beneckart/resonance-lighting/firmware/fixture/README.md

# fixture -- production fleet firmware

One image for all four fixture classes (downlight / perimeter / trunk /
chandelier), extracted from the proven bench sketches. The current code/NVS enum
still calls the trunk role `uplight`; treat that as a compatibility name until the
manifest/schema rename is coordinated (ADR 0032). `net_bench` remains the desk
**bridge** build (master + serial bridge); this sketch is peer-only.

## Indefinite storage and service wake

The September 12 image adds explicitly confirmed, exact-target storage:
untimed BQ ship with good USB/solar or QON wake, and untimed deep sleep with
physical RESET wake. Ship retains the fuel gauge; RESET/BOOT alone cannot wake
its unpowered ESP. OTA alone never enters storage or clears PROTECT. T-Deck
Rest -> Store also provides the existing timed sleep through a Pacific date
picker. See the [storage and wake guide](../../docs/howto/FIXTURE_STORAGE_AND_WAKE.md)
for exact firmware identities, 106-fixture deployment evidence and physical
wake/current tests still outstanding.

## Fixture class identity

The initial Wire1 probe and runtime drivers both use 100 kHz. Class identity is
ordered: ID-verified TMF8820/TMF8821-family ToF -> downlight; otherwise VL53L5CX
-> perimeter; otherwise MSA311 at `0x62` -> uplight. For the installed 2026 fleet,
no class sensors also defaults to uplight. A remembered downlight or perimeter is
retained with a mismatch if its ToF disappears.

Future chandelier PowerFeathers must be selected by exact MAC, recorded as
chandelier in the registry, and persist `O4` / `class_ovr=4` before installation.
Use `O0` to return a repurposed board to automatic identity. A sensorless explicit
chandelier is valid; an old automatically learned sensorless chandelier migrates
to uplight. See ADR 0067.

## Cambium direct control

`NB_DIRECT_FRAME` (type 25) carries up to 18 addressed RGBW entries per ESP-NOW
packet. A fixture renders only the entry matching its three-byte short MAC. Frames
grant an expiring micro-lease; after one second of silence the last color fades to
half, and after three seconds the fixture returns to its autonomous program with the
existing crossfade. `NB_FORCE_LIFECYCLE` (type 26) provides RAM-only day/night/auto
bench control and never survives reboot. The local power tier and night gate still
outrank requested colors.

The nominal 130-light fleet requires eight broadcast packets per complete color
wave. At Cambium's intended 8 Hz rate that is 64 packets/s, below the previously
exercised ESP-NOW rate range. The Nevada City acceptance bench uses perimeter
fixtures `F3FD88`, `F2BE80`, and `F2BFEC`.

## UTC schedule and build-week override

`NB_TIME_QUALITY` now carries the ADR 0031/0049 sparse UTC anchor. The T-Deck
GPS publishes active, checksum-valid RMC time; DS3231 fixtures add read-only
holdover when OSF is clear. Fixtures select bounded monotonic time and calculate
Black Rock City civil twilight (`-6 deg`) locally. If accepted time is absent
for 30 minutes, the existing panel-current dusk/dawn heuristic regains control.

RTC commissioning remains an explicit maintenance operation, never an automatic
show-time write. `ops/bench/rtc_commission.py` requires one exact fixture ID,
its identity-matched maintenance IP, the exact expected firmware revision, safe
power, DS3231 presence, and a fresh valid T-Deck GPS observation. The guarded
`POST /rtc` route repeats the fixture ID check, requires `SET_RTC_UTC`, writes
UTC once, clears OSF, and verifies readback. Maintenance telemetry exposes
`rtc_valid` and `rtc_utc_s` for the same proof.

In field profile, scheduled day is electrically dark and scheduled night runs
the autonomous program. Direct/program leases can override the baseline during
day; a dark lease can suppress night. `NB_FORCE_LIFECYCLE` provides RAM-only
Wake Fleet (the dark day baseline) / Night Show / Auto and clears on reboot.
Commission profile remains always awake with the ADR 0039 listener beacon. Only
accepted operator commands hold field fixtures awake for ten minutes; peer
heartbeats and time packets do not defeat the configured cadence. ADR 0064
additionally holds every timer wake through a trustworthy post-charge-enable
IBAT sample (normally about 12 s, bounded to 15 s on gauge failure), even if an
older recipe requested less.

## Transport sleep and rig RSSI capture

`NB_TRANSPORT_SLEEP` provides a 32-bit multi-day timer sleep. The bridge's
`Q<hours>` command (1-168) cuts fixture loads/rails and wakes automatically. The
timer wake restores radio/telemetry but retains an RTC-backed electrically-dark
output latch until a valid program command; bare bridge `b` is the intended
post-unload release. This is not physical ship mode and requires no lid access.

`NB_LOCATE_CONTROL` makes RSSI capture explicitly temporary. During bridge
`L[seconds]` only, a fixture retains up to 160 heard peers and sends its fresh
heard roster in 16-entry report fragments about every 20 seconds. Outside the
bounded window it emits no report traffic. See `ops/locate/rssi_capture.py` and
ADR 0045.

## Architecture stance

**Cooperative main loop + ISR-enqueue rx queue + esp_timer one-shots. No
application FreeRTOS tasks.** This deviates from ADR 0005 deliberately: it is
the only architecture with field hours behind it (net_bench soaks), and the
conservative reading of ADR 0028 rule 3 (no power-management-bus I2C from
core-0-pinned tasks under WiFi) plus the 2026-07-29 blocking-driver lesson
(cooperative TMF8820 one-shot machine; presence_bench's core-0 task quarantine
is forbidden on this bus). All Wire1 traffic runs at 100 kHz from loop context.
Revisit tasks only if render jitter is measured, and never for power-bus I2C.

> 2026-07-30 amendment (ADR 0028 addendum): rule 3 is downgraded -- the sealed
> A/B + 46 h soak both ran power-bus I2C from a core-0 task at 100 kHz, so the
> clock, not core placement, is the load-bearing rule. A single-owner sensor
> task (presence_bench shape, ALL Wire1 in one task) is now permitted pending
> a pre-playa field soak. Motivation is measured art quality: sensor-to-LED
> latency drives how alive the demo feels, and loop bursts visibly stutter
> max-speed orbit/spiral. Peer-to-peer CA impact TBD. The cooperative loop
> stays the shipping architecture until a task build earns its field hours.

## Layout

```
fixture.ino          setup()/loop() ordering only
src/core/            platform-independent, natively unit-tested (tests/)
  packet.h           wire protocol v1 + type registry (THE fleet contract)
  power_policy       ADR 0023/0046 tier ladder + compound PROTECT release
  boot_guard         POR/reboot-loop stage ladder (Phase-4 matrix)
  class_probe        sensors -> class decision table
  lifecycle          day/night machine, bounded night, energy-gated wake
  choreo/            program runtime: IDLE, GH_CA, BRIDGE_SHOW + lease
  neighbor_table     RSSI + pinned adjacency modes
  hex_geometry, filters, power_integrator, tmf_recovery
src/esp32/           glue/drivers (board_power owns the solar guard include)
  sensors/           cooperative machines + the single vendored VL53L5CX ULD
tests/run_tests.sh   wrapper contract + native g++ suite -- before every flash
```

## Build / flash

```
./build.sh                          # compile only
./build.sh --port /dev/ttyACM0      # USB flash
./build.sh --ota <ip>               # OTA via POST /update
./build.sh --artifact-variant b --wifi-profile-label party-in-the-woods-v1 \
  --channel 11 --profile field --basic-listener  # immutable canary artifact
./build.sh --channel 11 --profile commission
./build.sh --channel 11 --profile commission --basic-listener
./build.sh --precharge-ma 300            # low-VBAT recovery current
./build.sh --wifi-source <gitignored-header>  # solenoid capability is universal
./build.sh --wifi-source <gitignored-header> --solenoid-test  # targeted bench image
./build.sh --profile field --day-sleep-s 120 --wake-listen-ms 12000 # ADR 0064 canary
./build.sh --msa-trace-target ABCDEF --fw-rev fx-YYMMDD-xxxxxxx-t
./build.sh --sentinel-trace-target ABCDEF --fw-rev fx-YYMMDD-xxxxxxx-t
```

For ordinary edit/compile iteration, use the persistent development cache:

```bash
./build.sh --dev-cache --profile commission --channel 11
```

This path is serialized by an atomic lock and invalidated when the FQBN, flags,
toolchain, SDK, or firmware libraries change. Its mutable binary always reports
`dev-local`; it is suitable only for local iteration and, after host checks, one
explicit USB target. It is rejected with `--ota` or `--artifact-variant`.
Manual `--artifact-dir`/`--fw-rev` is disabled; the
artifact path and revision are derived from the exact canonical recipe before
compilation. Do not pass a development-cache binary to fleet tools.

If a cached build is killed, times out, or loses its wrapper, first confirm that
no `arduino-cli`, Xtensa compiler/linker, or `esptool` process remains, then run:

```bash
./build.sh --recover-dev-cache  # quarantine; next build is cold
```

Use `./build.sh --clean-dev-cache` only for a healthy, unlocked cache. Fresh
compile behavior remains the default when `--dev-cache` is omitted. Evidence and
raw gates are in
`../../docs/tests/FIRMWARE_BUILD_ACCELERATION_SMOKE_2026-08-22.md`.
Run `./build.sh --help` for the short local-versus-fleet command contract.
`tests/run_tests.sh` includes a fast, compile-free regression check for that
boundary before it starts the native C++ suite.

Maintenance WiFi credentials live only in gitignored `wifi_secrets.h`; copy
`wifi_secrets.h.example` and replace its placeholders locally. The historical
`RES_WIFI_SSID` / `RES_WIFI_PASSWORD` pair remains required. An optional
`RES_WIFI_SSID_2` / `RES_WIFI_PASSWORD_2` pair adds a second maintenance/OTA
network. On entry to maintenance, the fixture scans once, ranks visible known
SSIDs by RSSI, and tries both within a shared 30-second join budget. A failed
scan preserves primary-then-secondary order. Ordinary COMMS mode never joins
either network and remains pinned to the ESP-NOW channel.

Source defaults remain a 300-second DAY_CHARGE timer sleep and a 15,000 ms
post-wake listen grace. The installed 120 s / 3 s fleet artifact is superseded
by ADR 0064 because it could sleep before the 6-second charge guard and a fresh
MAX17260 conversion. New named 120-second canaries use at least 12,000 ms.
Firmware independently withholds ordinary day sleep until valid IBAT or a
15-second gauge-fault fail-open, so a shorter compiled grace cannot recreate
the charge-path defect. Record both build values with the artifact and do not
infer equal energy from listen duty alone because every wake also pays fixed
boot, sensor, and radio startup cost. USB telemetry exposes the compiled
`day_sleep_s` and `wake_listen_ms` values.

For any shared/fleet artifact, the manual `fixture-YYYY-MM-DD.N` counter is
retired. Follow `../../docs/howto/FIRMWARE_ARTIFACT_HANDOFF.md`: clean committed
source, generated `fx-YYMMDD-<recipe7>-<variant>`, immutable manifest, exact
binary SHA-256, and explicit target MACs. `build.sh --artifact-variant ...`
owns the canonical recipe bytes, revision/path, embedded identity, manifest,
and post-build cross-checks. Its golden test pins the final-LF byte contract.

Always `-DPOWERFEATHER_BOARD_V2=1` (build.sh injects it). Chemistry is
build-time (`--chem lfp` default); everything else is runtime NVS.
Solenoid capability is enabled by default on every PowerFeather image. The
one-time NVS policy migration enables devices that retained the historical
disarmed value; a later explicit runtime disarm remains persistent. D7/GPIO37
stays INPUT/high-Z while armed and idle, so rev-1 receiver/manual sources remain
usable and a Feather without a capboard has no connected load. A strike still
requires an addressed command, a deduplicated fleet strike event, autonomous
program output, or local input. Deliberate operator radio commands and events
are best-effort mechanism attempts under ADR 0065: they bypass lifecycle,
solar, and power-tier qualification but retain arm, pulse-width, rest-time,
maintenance, durable load-marker, and failsafe gates. Autonomous program
knocks retain the lifecycle/renewable/power-tier policy.

`NB_EVENT_SOLENOID_STRIKE` adds immediate and short-future fleet strikes without
changing the packet layout. One logical event is repeated for RF reliability;
fixtures deduplicate its 32-bit event ID, arm at most one pending event, clamp
the pulse to 5-300 ms, and refuse a scheduled strike more than 250 ms late.
`fire_in_ms` is capped at five seconds. The bridge decrements it on later RF
copies so every received copy refers to the same deadline, while the fixture
uses callback receipt time rather than later queue-drain time. At fire time an
operator event reaches the hard solenoid arm/rest/load-marker/timer/failsafe
boundary without lifecycle or power qualification. Older fixture firmware
ignores this new event kind.

`--canopy-solenoid` remains accepted as a deprecated no-op so older build recipes
do not fail; it is no longer required and must not be used to infer artifact
capability.

`--solenoid-test` is deliberately not a fleet option: it forces the arm bit and
relaxes the autonomous-program solar-surplus gate while retaining that path's
night and FULL-tier battery vetoes. Deliberate operator radio knocks no longer
need this override. Use a named artifact and a specific peer.

Rev-2 solarnoid SW1 shares D7 with the MCU through a hardware one-shot. An armed
fixture releases D7 to INPUT/high-Z between strikes. After observing a released
LOW, firmware accepts one external rising edge and extends it to the same bounded
40 ms pulse as the PowerFeather USER button; another strike requires release and
a new edge. Boot-high/stuck-high inputs do not fire or retrigger, normal MCU
requests refuse an already-high external line, and the timer plus loop failsafe
remain authoritative. External edges are ignored during OTA maintenance.

The default battery-side charge-current ceiling is 2,000 mA (ADR 0033). The
BQ25628E may deliver less because of input-current/voltage regulation, source
capability, system load, CV taper, or thermal regulation. `G<ma>` remains an
explicit lower override for a smaller or otherwise limited cell.

The BQ25628E precharge limit defaults to 300 mA (`--precharge-ma 300`). This
replaces the charger's 30 mA POR value, which left deeply discharged production
LFPs near 2.8 V treading water despite valid solar input. Firmware performs a
two-byte, little-endian, reserved-bit-preserving REG0x10 read/modify/write and
verifies the readback;
pending OTA images roll back if it does not match. Trickle charge below 2.25 V,
input DPM, thermal protection, and the hardware transition to fast charge near
3.0 V remain unchanged. Maintenance telemetry exposes `precharge_target_ma`,
`precharge_configured`, `bq_precharge_ma`, and raw `bq_reg10`.

Bringup: `fleet_usb_bringup.py commission --sketch-dir fixture --build-path
firmware/fixture/build/<r> --expect-fw <version> ...` -- the serial/HTTP
contract (`t` JSON keys, `u` + "maintenance WiFi up, ip=" banner, /telemetry,
/resume, /update) is preserved byte-for-byte from net_bench; the guarded `/rtc`
route is fixture-only.

## Sensor-domain recovery

Every non-parked boot gives the separate VSQT/STEMMA rail a verified 100 ms
off -> on cycle before class probing. This matters on OTA and warm resets because
PowerFeather otherwise preserves the RTC-held rail state, allowing a stale TMF
firmware/ranging state to survive the MCU reset. `Board.enableVSQT()` is retried
and GPIO14 is read back for both transitions; Wire1 remains fixed at 100 kHz.

The normal TMF timeout path still performs the cheap cooperative stop/start.
Three consecutive failed measurement cycles escalate once per boot to a full
VSQT cycle and reconstruction of the SparkFun driver, which forces TMF init,
open, firmware upload, application-mode switch, configuration, and ranging
start. MSA311 and BMP581 are reinitialized because they share the rail. Further
failures stay degraded rather than flapping the domain. Telemetry exposes
`tmf_domain_resets` in addition to reads/errors/recoveries.

Commissioning likewise treats `tmf8820_present=true` plus zero reads as a
recoverable state: it performs one explicitly targeted
`!S<short-mac>:1` timed-sleep/VSQT reset and retests before
failing. `tmf8820_present=false` does not get that retry and remains the signal
to inspect the module, first cable, and power contacts.

## Serial commands (peer)

`t` telemetry JSON | `u` local ENTER_MAINT | `c` resume | `C<mah>` capacity
(reboots) | `G<ma>` charge cap | `K<id>:<ms>` solenoid (gated) |
`!S<id>:<s>` newline-framed targeted deep sleep | `O<0-4>` class override |
`F<0|1>` profile dev/prod | `N<0|1|2>`
force day/night/auto | `L0` force LED rail off until `L1` or reset | `L1` clear
the override and run the bench smoke render | `X` guarded bare-board
PROTECT clear | `r` status line

`X` works only with verified good USB/VDC, no plausible battery, charging off,
and no charger fault. It does not clear PROTECT automatically or over ESP-NOW;
`fleet_usb_bringup.py` uses it only in the default battery-absent workflow.

### Installed-battery PROTECT rescue

Do not start with `RESET-BOOT-RESET`, erase NVS, or use `X`. Leave the fixture's
LFP installed, connect the enclosure rescue USB port to a proven supply, and
observe telemetry over normal USB CDC. A valid battery, good external supply,
valid/enabled charger with no fault, at least +20 mA charge current, and at
least 3.25 V must all hold continuously for 60 seconds before the durable
PROTECT latch releases. ADR 0068 adds a second proof for a full/tapered battery
that cannot accept +20 mA: a corroborated real cell, at least 3.45 V, and BQ
`CHG_STAT` of CV, top-off, or not-charging/done must hold with the same good
input and charger gates for 60 seconds. CC with low current, a proof change, or
one missing sample restarts the timer. Both paths release to LEDS_OFF and make
the same clean reboot; neither authorizes release from rebound voltage alone.

On `fx-260816-otafix1-b`, do not rely on the physical RESET button. A RESET
asserts a power-on-class reset; if the durable stage is still LEDS_OFF or DIM,
the cause-independent boot guard can correctly return to PROTECT. The observed
`F2BF5C` recovery held good USB and +340 mA charge long enough to climb
PROTECT -> LEDS_OFF -> DIM -> FULL, but the parked boot still left its LED rail
and sensors off. A deliberate software reboot at FULL then booted unparked,
initialized all three sensors, rejoined ESP-NOW, and returned to steady red.

The preferred rescue is to USB-install `fx-260816-prtrel1-b`; it replaces that
operator-timed software reboot with an automatic clean reboot immediately after
persisting the qualified release. The reboot is required because a parked boot
deliberately skipped rail cycling, class probe, sensor initialization, and LED
profiling. Use BOOT/download mode only if normal CDC never enumerates or the
ordinary USB flash tool cannot connect. Never erase NVS as a routine recovery;
it also destroys per-fixture configuration and bypasses the intended safety
qualification.

## NVS (namespace `resfx`)

`cap_mah` `chg_ma` `chg_policy` `class_ovr` `class_last` `fc_stage` `boots` `profile`
`batt_tier` `dim_mv/off_mv/slp_mv` `sol_en` `maint_v10` `channel`
`channel_policy` `night_max` `slp_cmd` `slp_prot`.
The USB command `H<1..13>` persists a new ESP-NOW channel and reboots so the
radio is cleanly re-pinned; bare `H` reports the current channel.
First boot migrates `netbench:{cap_mah,chg_ma}` and carries a parked
`fc_led_stage` (production must not un-park a protected unit). Charge-policy v1
then replaces legacy 500/1,000/1,500 mA NVS values with the 2,000 mA default
once. A nonstandard pre-existing value is preserved as a possible deliberate
cell limit; later `G<ma>` overrides remain persistent.

`slp_cmd` is the last validated operator sleep receipt; it records cause,
duration, source short ID/sequence/uptime, local uptime, VBAT, profile,
lifecycle, and power tier before the rails go down. `slp_prot` records the same
local context once on entry into PROTECT. ADR 0068 reuses its otherwise-empty
source fields to retain origin, predecessor stage, reset reason, prior
`load_arm`, and unexpected-reset streak without changing the 32-byte record.
Older records are annotated once as `legacy-unknown` without losing their entry
voltage/profile/uptime. Recurring day-charge and PROTECT timer sleeps do not
write NVS: their immediate cause uses RTC slow memory instead. An
operator-caused sleep is refused if `slp_cmd` cannot be persisted.

Channel 11 is the production default. Channel-policy v1 migrates an absent key
or the historical channel-6 fallback to the compiled channel (11 for production)
once, while preserving any other explicit lab channel. Later `H<1..13>` choices
are marked current and remain persistent.

## Commission vs field profile

`PROFILE_DEV=0` retains its wire/NVS value for compatibility but is now the
operator-facing **commission** profile. It is the pre-build/build-week posture:
the ESP-NOW control plane stays awake, heartbeats run at 1 Hz, solar current does
not trigger a lifecycle transition, and bridge command leases override the
selected no-command fallback. `commission_default` is `listener` (the normal
class-aware ready beacon), `ca` (autonomous light-only GH wildfire), or `dark`
(strict LED-rail-off diagnostics). Missing/invalid NVS stays `listener`. The
Bridge OS Default app changes one exact target or walks every fresh short ID;
its setting can be RAM-only until reboot or explicitly persisted with
`NB_COMMISSION_DEFAULT` type 30. A genuinely critical battery still parks all
loads; its commission-mode retry is 60 s, and a verified external source keeps
the parked control plane awake for service.

`PROFILE_PROD=1` is the operator-facing **field** profile: 300 s/15 s daytime
duty cycle (energy-gated), 0.2 Hz hb-short, scheduled/autonomous behavior, and the
normal 900 s PROTECT sleep. Local power and solenoid safety vetoes are identical
in both profiles; commission changes reachability and fallback behavior, not load
safety. Flip via `NB_PROFILE` (type 21) or per-unit serial `F` (`F0` commission,
`F1` field). New build flags accept `--profile commission|field`; `dev|prod` remain
compatibility aliases. The commission-default setting is ignored in field
profile, so it cannot replace the scheduled night CA or daytime sleep policy.

A timer wake with FULL power tier and measured good input at or above 150 mA
holds a RAM-only solar probe awake beyond the ordinary 15-second window. Sixty
continuous seconds earns `DAY_ACTIVE`; a transient clears immediately and
returns to the normal cadence. Once active, 100 mA is the energy-state
hysteresis threshold with a 300-second dropout confirmation; ADR 0071 no longer
treats that state as an all-day radio lease. DAY_ACTIVE returns to the normal
sleep/listen cadence after its grace and may carry readiness across one timer
sleep only when the fresh strike gate re-arms it. Autonomous strikes still
require at least 150 mA and the normal energy gate; deliberate operator knocks
are best-effort attempts under ADR 0065. Battery voltage alone is not surplus
evidence. See ADR 0060/0071.

Energy-ready downlights with trustworthy UTC shorten only their final daytime
sleep to wake 20 seconds before each hour. ADR 0071's fixed ritual attempts one
high-time-quality unison, one deterministic organic roll, and a sparse after-
ring, then returns to sleep by T+47 seconds. Invalid/weak time, scheduled night,
weak energy, a bridge lease, or any hard solenoid gate causes abstention. The
installed mallets strike finger cymbals, not bare bamboo.

The supervised `--basic-listener` posture is deliberately minimal and class
aware. With no active bridge lease, canopy/downlights hold their dedicated warm
white channel at linear 128, 37-pixel perimeter HEX modules hold red at linear
16, and single-pixel trunk/uplights hold red at linear 128. A bridge command or
dashboard tag overrides it, and stale-command fallback returns directly to the
selected commission default within three seconds. LED channel values are
linear: 0 is off and 255 is the 8-bit bright endpoint. The old
`--quiet-autonomy` option remains only as a build-script alias.

An `NB_PROGRAM_SET` GH-CA lease uses params byte 6 as an opt-in local ToF seed.
The sensor path is sampled once through the same ADR 0044 gate used by the
listener color wipe: 90-report per-zone learning, a confident 300 mm closer
delta for three reports, and four clear reports to re-arm. A rising edge is
held until the next CA step and excites only that downlight; ordinary CA state
gossip carries the result onward. Non-sensor fixtures remain graph participants.
Byte 6 defaults off, and params byte 1 now honors zero as zero spontaneous
sparks, so an operator can run a presence/neighbor-only CA lease. The separate
presence color-wipe gossip remains suppressed during every program lease.

The 1 Hz commission heartbeat remains the compact 29-byte `hb-short`. A length-
gated full heartbeat follows every 5 s in commission and every 60 s in field. Its
append-only output tails report fixture class, raw sensor-signature bits, class
mismatch, LED-rail state, the post-cap RGBW average actually written to lit
pixels, lit-pixel count, and low-VBAT recovery state/BQ presence-test voltage.
Tail 16 adds immediate sleep cause plus compact durable operator-sleep and
PROTECT-entry evidence. Tail 17 certifies power-sample validity; tail 18 adds
the durable PROTECT origin/predecessor/reset/marker/streak context. The full
heartbeat is now 199 bytes; automatic day/protection repetitions remain
flash-wear-free.
The fleet dashboard uses measured render state rather than inferring color from
the requested program. Older bridges remain compatible because every tail is
length-gated against the one canonical `src/core/packet.h` layout.

An installed LFP in the 2.2-2.5 V window is no longer confused with a missing
battery solely by voltage. On a qualified external source the fixture runs the
BQ25628E's documented 30 mA BAT-discharge presence test with charging disabled.
Only a surviving battery ADC reading at or above 2.2 V permits a 100 mA recovery
ceiling; LED and sensor rails remain parked. A fault stops recovery, and one
continuous minute at or above 2.55 V restores the persisted normal charge cap.
See ADR 0042. Cells below 2.2 V remain a bench-recovery case.

Maintenance exit clears the ESP-NOW receive queue before reinitialization, so a
queued maintenance command cannot replay after `/resume`. If radio initialization
fails during the WiFi-to-ESP-NOW transition, the fixture remains in COMMS posture
and retries once per second until `espnow_up=true`. Telemetry exposes
`espnow_up`, `comms_init_attempts`, `comms_init_failures`, `led_rail_on`, and
`smoke_render` so an operator can distinguish radio recovery, command receipt,
power veto, and physical LED output.

## OTA rollback

`verifyRollbackLater()`/`verifyOta()` are `extern "C"` -- the weak hooks live
in a C file; a mangled C++ override silently never runs. Deferred self-test at
t+20 s (power chip, gauge sanity, mode-appropriate network path, NVS, watchdog)
marks the image valid or reboots into rollback. COMMS requires ESP-NOW plus a
completed send; MAINT requires associated WiFi plus the active OTA HTTP server
because ESP-NOW is deliberately down there. Drill: flash a
`--ota-fail-selftest` build over OTA
and watch it revert unattended. Rollback support requires one full USB flash
to install the current bootloader config (the M1 fleet reflash provides it).
Telemetry exposes `ota_partition`, `ota_address`, `ota_state`, and the legacy
`ota_pending_verify` boolean so same-family A/B transitions remain observable.

## Hardware-gate checklist (owed before fleet flash; see plan)

- [ ] `fleet_usb_bringup.py --sketch-dir fixture` full commission incl. --wifi-check
- [ ] appears on an UNMODIFIED net_bench serial-bridge master + dashboard
- [ ] per-class render smoke from one binary (probe log + `O` override + RGBW order)
- [ ] bench-supply power matrix (ADR 0046): 3.15 dim / 3.10 off+OTA window / 3.05 sleep;
      PROTECT survives POR/WDT/SW reset; compound release only; retry once
- [ ] OTA good-image valid + fail-selftest auto-revert on battery
- [ ] GH wave on the 2x10 rig via pinned adjacency (RSSI-mode A/B for the record)
- [ ] commission bridge lease grant plus command-loss hard dark/rail-off <= 5 s
- [ ] commission time-to-maintenance <= 10 s; field worst case one sleep period
- [ ] 24 h outdoor prod soak: dusk, bounded night (set night_max low to prove
      it fires), dawn, maintenance reachable in every state, autonomous night
      strike refused, deliberate operator night strike bounded by mechanism gates
