beneckart/resonance-lighting/firmware/led_studio/README.md

# LED Studio (merged)

Interactive aesthetic bench tool that drives one of three LED options on the **same
data pin** (default GPIO10 / A0), with a UI **mode toggle** to hot-swap between them
-- no reflash:

- **HEX grid** -- SK6812 37px RGB hex.
- **RGBW point** -- single 4 W SK6812 RGBW (has a dedicated white die).
- **RGB point** -- single high-power RGB pixel (same as the RGBW minus the white die).

Supersedes the separate `hex_studio/` + `rgbw_studio/` sketches (kept for reference;
this one is the merged front-end).

## How the hot-swap works

Both modules are SK6812 (same WS2812 protocol + voltage), so a single
`Adafruit_NeoPixel` object is reconfigured at runtime via `updateType()` /
`updateLength()` -- **37px NEO_GRB** for HEX, **1px NEO_RGBW** for the RGBW. The strip
is blanked on every mode switch.

**Mismatched mode is harmless** (both SK6812): worst case is wrong colors or one LED
lighting until refreshed; current stays well under the 3V3 rail's ~1 A. Recommended
swap sequence: **All off -> physically swap the module on the JST -> flip the mode
toggle** to match.

## Wiring / flash

- LED data -> `DATA_PIN` (default **GPIO10 / A0**); power 3V3 (the RGBW runs fine undervolted
  at 3.3 V -- 5 V gives more Vf headroom / peak brightness but is *not* required); GND. The
  sketch enables the V2 switchable 3V3 rail (GPIO4).

> Note: the earlier "abnormally low" RGBW current at 3.3 V was a **measurement bug**, not a
> wiring problem -- `ina_monitor` divided by a 0.1 ohm shunt when the SEN0291 is 0.01 ohm, so it
> under-read 10x (fixed 2026-06-09; corrected full-RGBW draw ~ 290 mA). There is modest *real*
> rail sag under load (LED bus -> ~2.84 V at full RGBW), but **no evidence that lead / in-line
> resistance was ever the culprit** -- flaky DuPont jumpers can misbehave, but these tests don't
> demonstrate it.

```
./build.sh --port /dev/ttyACM1            # USB flash
./build.sh --pin 16 --port /dev/ttyACM1   # if data is on D6/GPIO16
./build.sh --sensor-triad --cap 6000 --charge-ma 2000 --maintain 4.6
./build.sh --l5cx --cap 6000 --charge-ma 2000 --maintain 4.6   # perimeter HEX demo
```

On shared WiFi the board registers a **per-device** mDNS name
`http://ledstudio-<last-3-MAC-bytes>.local/` (e.g. `ledstudio-9e5ae8.local`;
two boards both claiming plain `ledstudio.local` sent browser control to the
wrong unit, 2026-07-30). Serial monitor (115200) also prints the IP; SoftAP
fallback `ResonanceLED` (pw `resonance`) at `http://192.168.4.1`.

Since `led-studio-2026-08-01.3`: `wifi_secrets.h` may define `RES_WIFI_SSID2`
(bench AP) -- setupWifi scans at boot and prefers it over the primary SSID when
visible (phone hotspots can isolate clients; a laptop-hosted bench AP cannot).
Boards pick their network at boot only -- bring the bench AP up, then
power-cycle. `/set` + `/state` send `Access-Control-Allow-Origin: *` and
`/state` carries `"host"` (the mdns name), so laptop-side dashboards can drive
several boards at once: see `ops/bench/perimeter_trio.html` (3-light perimeter
bench UI with discovery scan, zone grids, and mood presets).

## Controls

- **Module toggle**: HEX grid * RGBW point * RGB point. Mode-specific controls
  show/hide accordingly (the W slider + white/warmth presets appear only for RGBW).
- **Shared**: color picker + R/G/B sliders, brightness, speed, gamma toggle, All off.
- **HEX mode**: W slider hidden; shape rings (center/+inner/+two/all); animations
  Spiral / Orbit / Breathe / Twinkle; Trail; Orbit ring; Freeze + Step.
  - **Split RGB** is a separate 3-state modifier (Off / Triad / Rotate) that applies
    on top of Static / Spiral / Orbit / Breathe -- it splits the moving "head" into
    pure R/G/B across three pixels:
    - **Triad** -- a local color-fringe cluster offset from the point (tune with
      Fringe **spread** + **rotate**).
    - **Rotate** -- R at the point, G/B the same point rotated 120 deg /240 deg about the
      grid center (3-fold rotational symmetry; collapses to white at the exact center).
- **RGBW mode**: W (white-die) slider; white/warmth presets + crossfade; animations
  Hue / Breathe / Candle / Fade (with Color B).
- **RGB mode**: same single-pixel color animations as RGBW (Hue / Breathe / Candle /
  Fade + Color B), but no W channel or white/warmth controls.
- **L5CX presence HEX mode** (`--l5cx`, perimeter demo enclosure): vendored
  VL53L5CX 4x4 @ 10 Hz on Wire1/100 kHz (fixture's trimmed ULD, loop-idiom like
  sway_demo -- begin() only in setup(), quick re-apply self-heal in loop).
  Boots into HEX anim 5 "Presence" at bri=255/gamma-off. Idle = all 37 px
  pure RED; a visitor's depth drives the hue continuously --
  t = (max - depth)/(max - min), red at 2.5 m walking R->O->Y->G->B->I->V as
  they close on the gobo threshold -- and inside the threshold (default
  500 mm, slider 40-600: visitors step up without knowing where the sensor
  is, so arm's-length pops the surprise) the gobo takes over: a single
  full-white center pixel until release. Visitor depth = closest target
  anomalous vs a learned per-zone scene baseline (unset zones count as FAR,
  so someone entering an empty sightline registers from max range; static
  clutter stays scene and cannot pin the gobo on). The wheel HOLDS during
  the gobo confirm (sudden appearance snaps to white instead of zipping the
  rainbow). Gobo triggers: **near** (visitor <= thresh) OR **occlusion** (>=60% of
  baseline-valid zones lose their target -- a palm covering the whole FoV
  returns non-valid statuses, so "closest target" alone would read it as
  clear). Baselines adapt asymmetrically (revealed-farther fast, closer on a
  ~1 min tau so a lingering visitor fades back to scene; frozen during gobo;
  "Re-zero scene" button reseeds). 2-frame enter / 3-frame release; gobo
  transitions and visible color motion re-render at sensor rate instead of
  the speed-paced frame timer. The UI shows a live 4x4 zone grid (mm +
  anomaly coloring), visitor depth, and wheel position.
- **Sensor-triad RGBW mode** (`--sensor-triad`): adds live MSA311, TMF8820, and
  BMP581 readback plus three reactive modes. ToF depth brightens the selected
  RGBW color as a target approaches (the known enclosed 20 mm window/fixture
  return is ignored); Tilt brightens with angle from a re-zeroed rest pose; and
  Elevation maps -1.5 to +1.5 m around a re-zeroed BMP581 pressure baseline from
  dim to bright. TMF8820 one-shots use a cooperative start/process/stop state
  machine instead of the driver's blocking convenience wrapper; all sensor and
  PowerFeather accesses remain single-threaded at Wire1's mandatory 100 kHz. The
  UI reports WiFi RSSI, request latency, TMF result age, and automatic recoveries.
- **Settings readback** for recording good-looking combos.

See `../POWERFEATHER_NOTES.md` for the 3V3-rail / native-USB-reset gotchas.
