beneckart/resonance-lighting/LOG.md

# LOG

Append-only session journal for the Resonance Lighting workstream. Most recent first.

Format per entry:

```
## YYYY-MM-DD -- author -- short subject

Body. What changed, what was decided, what's next.
```

## 2026-10-06 -- Ben + Codex -- Consolidate storage firmware and post-event work

Ben requested committing all pending work and pushing to origin. Integrated
both storage branches with the pending Atom/Magic Wand conductors, preserving
the exact deployed fixture/T-Deck artifacts and their original identities.
Added `docs/howto/FIXTURE_STORAGE_AND_WAKE.md` with wake contracts, operation,
rollout evidence and the still-open electrical/UI qualification. Fixed stale
canary counts and worktree-only artifact references. Added
`docs/postmortem/README.md`, linked from README, ROADMAP and TODO, to connect the
container/Oakland/PROTECT records with both 2027 brainstorming drafts. Those
ideas remain exploratory; controlled PROTECT recovery is still deferred.

Preserved the small supplementary storage snapshots/process logs/dry run with
a separate exact-byte manifest and explicit historical status. The three large
raw captures stay local with hashes retained; private NVS backups and Wi-Fi
secrets remain excluded. Original evidence and artifact bytes are unchanged.

Review caught a Magic Wand high-hold shock that could leave a gesture armed.
The source now cancels it immediately and has a regression at the rejection
threshold; previous embedded builds predate the fix and need a new artifact
before deployment. T-Deck registry generation also depended on CSV checkout
line endings; canonical LF hashing and LF/CRLF/content-change tests fix that
portability issue without altering the fleet entries or historical artifacts.

Retained the exact September 3 25 ms Atom application and supporting flash
files with a historical manifest. Its original build used uncommitted source;
the new record explicitly leaves the build source commit unknown rather than
assigning today's integration commit to that binary.

Validation: all 33 fixture and 20 T-Deck native executables, five conductor
native executables, 26 Python host/storage tests, two registry-generator
regressions, build-wrapper contracts, local documentation links and staged
whitespace checks passed. All 57 curated and 26 supplementary evidence records
retain their exact hashes in Git, as do the retained firmware binaries/options.
No fresh embedded image was built; the preserved binaries are the historical
ones, and the updated Wand source still requires a new artifact and canary.

No device commands, reflashes or changes to live fleet state were made during
this repository consolidation.

## 2026-09-14 -- Ben + Codex -- Instant maintenance wake as an OTA speed objective

Ben identified a second benefit for an independent wake interface: shorter OTA
turnaround. Added the requirement to the RFID feasibility note. It removes
sleep-cadence gathering and repeat straggler capture, especially the roughly
15-minute PROTECT rendezvous; it does not shorten compile/upload or verified
reboot. The runbook's ordinary-fleet phase timings are planning targets, not
an observed storage-run speed claim.

Specify retained bounded maintenance intent, loads parked, duplicate wake that
does not reset an active upload, group/roster coverage and the existing power
and pending-verify gates. A bare hardware reset may promptly sleep again and
never clears PROTECT. No implementation or device command.

## 2026-09-14 -- Ben + Codex -- RFID identification plus independent reset/wake explored

Ben connected the earlier battery-free fixture-ID idea to a ground-accessible
hardware reset/wake and asked whether an RTC coin cell could support it.
Recovered the earlier request from the Postmortem Findings task; no prior
selected RFID component was found. Added a feasibility note at
`docs/projects/2027-power-platform/RFID_SERVICE_ACCESS.md`.

Primary documentation establishes RF-controlled GPIO without ESP firmware on
EM4325-class UHF RFID, with an official coin-cell reference design. Proposed
independent bounded reset/ship-wake circuitry, a retained service request,
and harmless inventory separate from deliberate targeted action. Shared coin
power is plausible for control only; quantify complete standby/RF-event draw,
isolation and clock-retention effects. Passive ID, assisted ID and actuation
range need separate installed tests; passive fallback can be much shorter.

Reset does not clear durable PROTECT or supply energy to an empty main cell.
QON wakes BQ ship but not shutdown, and external-input reset behavior needs
explicit design. No chip/reader selected, device action, or firmware change.

## 2026-09-14 -- Ben + Codex -- Chime sensing demoted; command reception prioritized

Ben corrected the exploratory priority: both capboard revisions already have
optional voltage-divider sensing, and the populated bench proof produced
excellent data. Weak/null underfilled-cap strikes are acceptable; he reports
fast refill in weak sun and consistent several-Hz independent 433 MHz rings.
Chimes were more reliable than light control or presence sensing; sleeping
ESPs and suspect PROTECT recovery were the main remote-control impediment.

Revised the design exploration to preserve the working solar-fed bounded
strike path, keep cap telemetry optional for diagnostics, and compare radio
reachability/latency per unit energy. At an illustrative 3.3 V and 130 mA,
12 seconds of LEDs-off awake operation costs 5.15 J versus 4.75 J total stored
in a nominal 66 mF/12 V bank. This is not isolated RF power or per-strike energy.
Historical fast capacitor refill was measured on a bench supply; Ben's latest
weak-sun report is retained as field observation, not substituted for that trace.

ESP-NOW reception windows and an independent trigger/wake path are research
comparisons only. No deployment, new strike veto, or hardware change. The exact
count of erroneous PROTECT latches remains unresolved; no new guard command.

## 2026-09-14 -- Ben + Codex -- 2027 power-platform exploration; recovery UI deferred

Ben explicitly tabled implementation of a T-Deck un-PROTECT/recovery command
and asked for broader firmware/tooling assessment with a year until the next
event. Recorded an exploratory brief in
`docs/projects/2027-power-platform/EXPLORATION.md`, not an accepted ADR/BOM.

Reviewed local bus/SOC/current/solar/chime evidence and primary datasheets.
Proposed priorities: autonomous LFP-correct charging/recovery, private power
bus, whole-cycle energy accounting, source identity, chime-cap voltage,
independent load/cell cutoff and explicit calendar/service wake contracts.
Keep the gauge for characterization rather than blaming its silicon for an
unqualified SOC model. INA228 accumulation costs 640 uA typical while running;
its production measurement power source and gaps need design. Hardware fault
capture and retained evidence are more useful than additional opaque flags.

Queued a feature inventory and small comparative qualification program before
any board selection or retirement. No firmware, device commands, purchases,
or current fleet architecture changed.

## 2026-09-14 -- Ben + Codex -- Explicit PROTECT clear capability checked

Confirmed there is no T-Deck/ESP-NOW un-PROTECT command. Durable NVS PROTECT
survives RESET, power cycling and ordinary OTA. The fixture serial X command
is restricted to verified externally powered, battery-absent, charging-off,
no-fault bare boards; it is not an installed-battery override. Added the exact
capability boundary to the recovery investigation. A remote controlled retry
would require new fixture and handheld support. No device or firmware changes.

## 2026-09-14 -- Ben + Codex -- Wake does not override PROTECT radio sleep

Traced Wake/Performance Hold from NB_FORCE_LIFECYCLE through ordinary receive
hold and inspection control. PROTECT's separate power_glue deadline is set only
at boot and remains authoritative; Wake does not extend it, clear the latch or
guarantee full-time radio. Verified the independent 8-second grace/sleep gate
in Kiki's 91663fd source, Groot's 2805988, final-burn 316470a and inspection
7c1f71d. Expected PROTECT listening is about 8-9 s / 900 s asleep unless a
separate recovery/OTA/service condition holds it awake.

The six-minute Wake campaign also cannot guarantee capturing a 15-minute
PROTECT cadence. Corrected overly broad 'full-fleet' / 'each captured radio'
operator documentation; Performance Hold spans more wake cycles but still does
not override PROTECT. Added the distinction to the recovery investigation and
queued explicit Wake eligibility diagnostics. No firmware or device changes.

## 2026-09-14 -- Ben + Codex -- High-VBAT PROTECT cohort and recovery limitation

Ben linked unexpected quiet during the last Burning Man days to possible stuck
PROTECT. Reconciled the retained September 12 census: 74 PROTECT, 40 at >=3.25 V,
seven at >=3.30 V. The 40 entry histories are 35 low-VBAT, four load-armed reset,
one legacy; all report supply-good false in the dark-storage snapshot. This is
a substantial triage cohort, not proof of 40 healthy batteries or sunny failures.

Manifest/source ancestry confirms all three September 12 fleet images already
contained the full-battery and PROTECT sleep-ownership fixes. Kiki's older
658b7d2 contains neither; Groot's b0ff5db contains both. Offline injected-sample
checks against unchanged current power_policy reproduce a remaining limitation:
net-positive charge across sleep/wake can coexist with negative awake current,
so no recovery proof starts below the full-battery floor. Stable current and
full/CV positive controls release correctly. This is not hardware validation.

Also separated a known chime contributor: September 1 inspection firmware on
70 fixtures deliberately disabled autonomous chimes; the earlier final-burn and
visibility images allow them in FULL/DIM. Bench plan, exact cohort and synthetic
reproduction are in `docs/tests/PROTECT_RECOVERY_INVESTIGATION_2026-09-14.md`.
No production code or device state changed; preserve Oakland specimens for
controlled diagnosis before deciding a repair.

## 2026-09-14 -- Ben + Codex -- Timed sleep does not set PROTECT

Traced T-Deck Rest 12-hour radio sleep through NB_SLEEP_FOR into the fixture's
timed deep sleep. It records the operator request without setting PROTECT;
an expected timer wake preserves the previous power stage. Wooper retains a
12-hour command yet currently reports NORMAL. Kairi instead records a low-VBAT
entry at 2.993 V (no load armed), now 3.303 V/PROTECT; Kiki has a 2.978 V older
entry, now 3.277 V/PROTECT. These are historical trigger records, not independent
cell measurements. A voltage rebound alone never qualifies the charge-based
release. Groot's low-VBAT entry is 2.976 V with load armed, now 2.880 V.

Ben clarified the early morning timing and doubts significant solar recovery;
no measured charge history supports that explanation, so it is not adopted.
The available listen samples show negative battery current/good-input false
for the high-voltage production fixtures. Updated the Oakland post-mortem
record with exact command/protection distinctions; no device changes.

## 2026-09-14 -- Ben + Codex -- Oakland units stay out; preserve post-mortem baseline

Ben plans to leave the Oakland lanterns out, with no deliberate sleep/ship
commands, and may bring some inside for post-mortem analysis. Existing
automatic power policy remains in place; no forced-awake hold was requested.
The high-voltage PROTECT units plausibly survived dark storage through sparse
radio duty: roughly 216 mAh/week at 130 mA for 9 seconds awake / 900 asleep,
excluding leakage/other loads. This is a model, not measured storage draw or
remaining capacity; LFP voltage plateau and unknown recent solar history limit
the 3.3 V inference. Wooper's current shorter cadence models about 1.99 Ah/week.

Prioritize Groot versus a higher-voltage PROTECT fixture (Kairi/Kiki), retain
state before firmware/guard changes, then compare actual cell/load/current and
charge behavior. Keep old prototype 9F26F8 separate from production conclusions.
Updated `docs/tests/OAKLAND_LANTERN_INVENTORY_2026-09-14.md` and TODO; no device
changes were issued and the earlier passive capture remains immutable.

## 2026-09-14 -- Ben + Codex -- Oakland bin accounts for Kairi and Wooper

Ben brought a separate bin from Nevada City to Oakland: five canopy lanterns
and one batteryless uplight with its panel connected. Two old backyard
prototypes are also present; the perimeter may be disconnected/batteryless.
TSwift's five reported identities are Groot 9F2724, Kairi 9F26B4, Kiki F2BF5C,
Wooper 9F0E30 and prototype 9F26F8. None was in the September 12 stored 106.
Kairi/Wooper account for two of that census's eight missing IDs; six remain
unlocated. Groot/Kiki/prototype were outside the 114-ID baseline. Other bin
units are not yet mapped and may still overlap the stored group.

A 22-second read-only serial snapshot verified connected TSwift 979604 on
COM157, channel 11, tdeck-dev-local; storage4 was flashed on other T-Deck
8EB508. Last-listen battery reports were Groot 2.880 V, prototype 2.992 V,
and the other three 3.277-3.321 V, with ages 18 seconds to 13.6 minutes.
These are retained reports, not simultaneous cell measurements or a complete
900-second census. No commands, firmware/power changes or background process
were issued/left running. Exact evidence and service items are in
`docs/tests/OAKLAND_LANTERN_INVENTORY_2026-09-14.md`.

## 2026-09-12 -- Ben + Codex -- 106 fixtures stored; pack-up complete

All 106 observed fixtures acknowledged untimed USB-wake storage on the exact
retained f951ae9 image. The final five replied by 18:39:20 PDT; the final
17-target job stopped at 18:39:37 with no failed or unresolved target. All
106 source/sequence receipts match durable cause-8, zero-duration audits.
The final 19:17:57 read-only reconciliation passed after 38m37s of radio quiet
since the last receipt, with continuous logger/master evidence and no bridge
restart. A fresh storage-status confirmed the controller inactive. No further
sleep command was needed when Ben requested pack-up at 19:17.

Stopped only this run's logger/dashboard and released the temporary Windows
awake hold at 19:18. Laptop, T-Deck and Starlink can be packed. The eight
never-heard installed fixtures were not commanded and remain physical-service
exceptions. USB/solar or QON wakes the selected mode; RESET/BOOT alone does
not. Assembled current and physical wake still require service-time testing.

Final proof, exact ledgers/rosters, controller flash identity and capture
hashes are retained with the report at
`docs/tests/CONTAINER_STORAGE_CENSUS_2026-09-12.md`. Compact evidence and source
are on `codex/container-storage-host-20260912`; large raw logs/private NVS
backups stay local. T-Deck Rest -> Store includes indefinite storage and a
fresh-GPS Pacific wake picker from 30 minutes to seven days. Native and
embedded checks passed; physical LCD/wake/current qualification remains open.

## 2026-09-12 -- Ben + Codex -- All 106 OTA verified; direct USB storage underway

Ben's later instruction authorizes direct laptop operation, without a physical
T-Deck confirmation tap. His dinner return window is approximately
18:30-19:00 PDT. ADR 0081 records the narrow host-command exception.

All 106 observed fixtures passed fresh exact-revision and pending-window OTA
verification on the retained `fx-260912-f951ae9-b` image by 17:56:15 PDT;
no target failed or remained in commission. The eight census exceptions were
not heard and were not commanded. Exact per-job evidence is in the container
run directory, including `all-106-ota-verified.txt`.

Flashed exact T-Deck 8EB508 / 44:1b:f6:8e:b5:08 on COM152 with retained
`tdeck-0.3.0-storage4`, 1,578,224 bytes, SHA-256
`11b98b33ca46babf21ad27cb1f2edd7cccdf6319a5e130df3e5442fd6260c1b1`.
Every written flash-region hash verified, then fresh boot identity, channel 11,
radio census and an idle host storage controller were confirmed. Firmware
source is 556c2f6 in `../resonance-tree-storage-host-20260912`; artifact commit
a53181a retains binaries and manifest. Full native and embedded checks passed.
The native registry comparison now tolerates Windows CRLF; firmware did not
change after the retained build. A private NVS/apps recovery backup remains
local and must not be committed.

Hellboy's first storage command was accepted at 17:57:18 PDT. At 17:59:12 it
reported PREPARED for source 8EB508 / sequence 21, then stayed quiet past its
former 120-second cadence. Its durable command audit reports USB storage,
zero duration, the same source and sequence. Two subsequent groups brought
the total to 31 PREPARED by 18:04, all with matching durable audits and no
rejoin or failure. Storage requests are now actually being sent under Ben's
explicit permission; earlier no-command notes describe earlier checkpoints.

The 75 PROTECT-cycle fixtures are being handled in complete timing cohorts,
with Ponyta's group armed first. Remaining exact-roster plan and per-command
ledgers are retained. The final full-cadence quiet observation is still due;
PREPARED plus radio silence is not measured electrical current or a physical
USB-wake test. Expected pack-up readiness is about 18:40-18:50 PDT if these
cohorts behave as observed. Temporary laptop awake hold remains active.

## 2026-09-12 -- Ben + Codex -- Fleet USB storage authorized

Ben returned at approximately 17:08 PDT and explicitly authorized putting the
fleet into USB-wake storage. Earlier sleep/ship confirmation is now satisfied.
Continuing exact-target OTA batches from the tested immutable f951ae9 image,
then storage through the T-Deck with explicit request/receipt evidence. First
additional wave: 12 targets, job 6FA40ADD. The T-Deck storage3 build continues;
physical storage wake/current remains unmeasured. Full rollout results will
be appended when known.

## 2026-09-12 -- Ben + Codex -- Container census and one storage-capability OTA canary

Onboarded in Nevada City after roughly a week of dark container storage.
Ben wants fixtures off until physical service; USB wake preferred, RESET
acceptable, and QON effort only if the battery benefit warrants it. Ben
authorized OTA at discretion while AFK, retaining his earlier requirement
for separate confirmation before deliberate deep-sleep/ship commands.

Completed an uninterrupted 1,020-second census after a recorded host-process
capture gap: 106 of the September 1 installed roster of 114 heard, all FIELD,
all latest retained LED reports off and supply-good false. No 0-0.6 V report
appeared in either capture segment. Ponyta `F2B7DC` was lowest at 2.582 V;
Chunli `9F2714` was 2.618 V. These are readings, not a ruined-cell diagnosis.
Eight missing fixtures remain unknown. Seventy-four latest tiers were PROTECT.
Details, field ages, limitations and battery calculations are recorded in
`docs/tests/CONTAINER_STORAGE_CENSUS_2026-09-12.md`; raw data and exact rosters
are in `ops/bench/data/ca/20260912-155847-container/`.

Prepared storage firmware in the isolated adjacent worktree
`resonance-tree-storage-20260912`, branch `codex/container-storage-20260912`,
preserving unfinished conductor changes here. The canonical protocol adds
exact-target USB-wake ship mode and RESET-wake indefinite deep sleep; OTA
does not select either. The T-Deck adds reviewed storage and a GPS-backed
Pacific date/time picker with a seven-day limit and 16-minute catch-up window.
ADR 0080 in that worktree records the contract and physical qualification still
needed. The first T-Deck build was abandoned to fix confirmation-dialog fit;
its replacement uses a fresh path, never the interrupted directory.

Fixture and T-Deck native suites passed. Fixture embedded artifact
`fx-260912-f951ae9-b` (1,218,752 bytes), SHA-256
`ec03b074c6feae7ffc3f6bb2e178ec213ea5d241b56b3e24c95bfbb24d315001`,
was built from clean `fcc5ef0` with the same runtime flags as the installed
inspection image. Sole operator Ben + Codex OTA-updated only Hellboy `9F26C4`.
Job `84DEEB42` verified a fresh exact-revision heartbeat at 25,953 ms uptime,
FIELD profile and recovery state zero at 16:40:08 PDT. No deliberate sleep,
ship, lifecycle or LED command was sent.

Added a read-only census summarizer and storage request/receipt logging;
all 16 relevant Python tests pass. Periodic radio wakes dominate storage
draw. The vendor-board 24-to-1 uA deep-sleep/ship comparison saves just
0.440 Ah/week across 114 fixtures; USB wake is ship's stronger practical
advantage. Our ship implementation retains the gauge and needs external
current measurement; do not claim the vendor's gauge-disabled 1 uA result.

## 2026-09-12 -- Ben + Codex -- Explicit unattended USB-storage operation

Ben authorized putting the fleet in USB-wake storage and asked for direct
laptop operation while a campmate later packs the equipment. ADR 0081 adds a
bounded, exact-roster USB CLI with explicit confirmation text, fresh capability
checks, job-owned stop/status, and no automatic campaign resume. The existing
physical UI flow remains intact. Work is isolated from the still-running
storage3 compile; storage4 uses a separate source checkout/build directory.

## 2026-09-12 -- Ben + Codex -- Storage confirmation proposal frozen

Final UI review found keyboard focus could reach background controls while a
confirmation was open. Storage now refuses background Review/Back/mode/Stop
actions until that modal closes, preserving its exact target, wake method and
date. Confirmation also refuses entry after the Storage screen has gone away.
The completed storage2 image passed its embedded build but was not flashed;
storage3 uses a fresh retained build directory. Ordinary Hellboy RTC audit
retention is now confirmed after clearing the receiver cache; physical storage
entry and wake remain untested and require Ben's separate confirmation.

## 2026-09-12 -- Ben + Codex -- Storage census and one OTA canary verified

Completed a 17-minute uninterrupted census after recovering an earlier host
capture gap: 106 of 114 installed fixtures heard, all FIELD, no reported
0-0.6 V batteries; Ponyta 2.582 V and Chunli 2.618 V are lowest. Eight missing
fixtures remain unknown. The main saving is removing periodic radio wakes;
ship's extra gain over uninterrupted deep sleep is small, with USB wake its
main servicing advantage. Full evidence is in
`docs/tests/CONTAINER_STORAGE_CENSUS_2026-09-12.md` and the main checkout's
`ops/bench/data/ca/20260912-155847-container/`.

Built immutable canary `fx-260912-f951ae9-b` from `fcc5ef0`, exact SHA-256
`ec03b074c6feae7ffc3f6bb2e178ec213ea5d241b56b3e24c95bfbb24d315001`, and
used Ben's OTA authorization for only Hellboy `9F26C4`. Job `84DEEB42` proved
fresh exact revision beyond 25 seconds, FIELD profile, recovery state zero.
No storage command was sent; the original separate confirmation requirement
remains. Fixture/T-Deck native suites and the fixture embedded build passed.

Added storage receipt/request logging with separate PREPARED, refusal, and
entry-failure meanings. All 16 relevant Python tests pass. Screen review found
that content-sized confirmation dialogs could obscure the footer; bounded
the dialog with a scrollable content region. The first incomplete T-Deck
compile was intentionally stopped, its compiler descendants checked gone,
and its directory abandoned. The corrected storage2 image uses a new build
directory. This does not alter the already verified fixture artifact.

## 2026-09-12 -- Ben + Codex -- Explicit container-storage capability prepared

Added exact-target indefinite RESET-wake and USB-wake ship commands, durable
sleep audit causes, pre-entry receipts, and an appended capability heartbeat
tail. OTA never selects storage automatically. The T-Deck Power screen now
offers a reviewed storage action and a GPS-backed Pacific date/time picker
using existing transport sleep, with an explicit roster and a 16-minute
catch-up window for PROTECT sleepers. ADR 0080 records the wake contracts,
confirmation boundary, and remaining physical current/wake qualification.

Fixed pre-existing T-Deck registry-generation drift: new unnamed fixtures use
their exact ID, retired fixtures can retain historical callsigns, and the
generated roster is refreshed without changing the source registry/callsigns.
All fixture native tests passed. Embedded builds and the T-Deck test completion
are recorded in the follow-up validation entry. No sleep/ship command or flash
was issued while preparing this source.
## 2026-09-03 -- Ben + Codex -- Fourth and final 25 ms Atom Conductor flashed

Identified the last COM42 Atom as full MAC `14:08:08:54:B8:C8` (short ID
`54B8C8`) and found no prior role or identity record in the repo. SHA-checked
and reused exact 938,416-byte `atom-conductor-2026-09-03.1` application
`fdabd85037a7dec96353ad1e08c4b914f80f839dea26963469767ec06ef6cfc2`
without rebuilding. Every written flash-region hash verified. A controlled
reboot reported node `54B8C8`, channel 11, `pulse=25`, `color=64`, and
`radio=ready`; no fleet action was sent. Ben's completed full-conductor roster
is `1B636C`, `54AD9C`, `54B0C8`, and `54B8C8`.

## 2026-09-03 -- Ben + Codex -- Third 25 ms Atom Conductor flashed

Identified the next COM42 Atom as full MAC `14:08:08:54:B0:C8` (short ID
`54B0C8`) and found no prior role or identity record in the repo. SHA-checked
and reused exact 938,416-byte `atom-conductor-2026-09-03.1` application
`fdabd85037a7dec96353ad1e08c4b914f80f839dea26963469767ec06ef6cfc2`
without rebuilding. Every written flash-region hash verified. A controlled
reboot reported node `54B0C8`, channel 11, `pulse=25`, `color=64`, and
`radio=ready`; no fleet action was sent. The full-conductor roster is now
`1B636C`, `54AD9C`, and `54B0C8`.

## 2026-09-03 -- Ben + Codex -- Second 25 ms Atom Conductor flashed

Identified the next COM42 Atom before writing it as full MAC
`14:08:08:54:AD:9C` (short ID `54AD9C`). This was the previously recorded
reduced-access clicker for target `9E5B8C`; Ben explicitly approved replacing
that role with the full conductor.

SHA-checked and reused the exact 938,416-byte
`atom-conductor-2026-09-03.1` application
`fdabd85037a7dec96353ad1e08c4b914f80f839dea26963469767ec06ef6cfc2`
without rebuilding. Every written flash-region hash verified. A controlled
reboot reported node `54AD9C`, channel 11, `pulse=25`, `color=64`, and
`radio=ready`. No fleet action was sent. The current full-conductor roster is
`1B636C` and `54AD9C`; the latter no longer has the one-target clicker image.

## 2026-09-03 -- Ben + Codex -- Atom Conductor changed to 25 ms and reflashed

Ben corrected the conductor strike recipe after field observation that a 25 ms
solenoid pulse produced longer cymbal ringing than 40 ms. Changed the Atom
Conductor source/build defaults and documented validation recipe to 25 ms, and
gave it distinct revision `atom-conductor-2026-09-03.1` so it cannot be confused
with the superseded 40 ms image.

Built once in fresh path `field-25ms-20260903-r2` for channel 11, 25 ms pulse,
and RGBW value 64. The build uses 938,165 bytes (47 percent flash) and 54,936
bytes (16 percent RAM); its 938,416-byte application has SHA-256
`fdabd85037a7dec96353ad1e08c4b914f80f839dea26963469767ec06ef6cfc2`.
USB-reflashed exact Atom `1B636C` on COM42, verified every written-region hash,
and captured a controlled reboot reporting the new revision, node `1B636C`,
channel 11, `pulse=25`, `color=64`, and `radio=ready`. No fleet action was sent.
This exact binary supersedes both earlier 40 ms `r3` and the unversioned interim
25 ms `r1` for all planned spare full-conductor Atoms.

## 2026-09-03 -- Ben + Codex -- Atom Conductor canary flashed to 1B636C

Windows enumerated the connected original Atom Matrix as FTDI data port COM42;
a read-only chip probe identified ESP32-PICO-D4 MAC `F8:B3:B7:1B:63:6C`
(short ID `1B636C`). This is a third recorded Atom identity, distinct from the
older smoke-test `1B5108` and reduced-access clicker `54AD9C`.

USB-flashed the already validated `verify-20260902-r3` Atom Conductor binary,
without rebuilding it. The 938,416-byte application SHA-256 remains
`715a64c90056dc511b95015389520574b3123c0eb71ba232d102c03b560322f9`;
the upload verified every written flash-region hash. A controlled serial reboot
then reported `atom-conductor-2026-09-02.2`, node `1B636C`, channel 11, 40 ms
strike, RGBW value 64, and `radio=ready`. No fleet action was requested; the
cold-boot image is waiting for its first face press.

Ben intends to flash a few identical full-conductor spares so a depleted unit
does not end the interaction. Reuse this exact inspected binary for the spares,
record each full MAC/short ID and boot proof, and keep all of them in Ben's
custody: redundancy does not change the unauthenticated fleet-command risk.

## 2026-09-03 -- Ben + Codex -- Magic Wand gesture conductor built

Located Steve's `codex/NeoHex-Magic-Wand` work and confirmed that its merge tip
`codex/integrate-magic-wand` is already an ancestor of current `main`. Added
`firmware/magic_wand_conductor/` as a separate exact-device image while
preserving the working installed `net-bench-2026-08-19.1` fallback and its `.2`
source. The new binary checks the full `68:EE:8F:F4:03:44` MAC and refuses power
configuration, external LED frames, and fleet transmission on any other board.

Resolved the no-button control around a deliberate two-sensor gesture: hold
still 1.6 seconds, lift at least 0.45 m with MSA311 motion corroboration, then
hold at least 0.35 m high for 0.8 seconds. Shocks, motion without barometric
rise, pressure drift without motion, and stale/missing sensors fail closed.
Return to the original height, or hold still five seconds at a new height, to
re-arm. Thresholds remain provisional pending traces of Steve's real carries,
handoffs, and lifts.

The existing LED switch cannot be used as a software input without a hardware
sense wire. Its Pololu 5.1 V branch leaves the PCM in parallel with the
PowerFeather, so LED load bypasses the MAX17260 sense resistor; voltage-sag
inference on the 15 Ah LFP would be unreliable. The conductor does not invent a
switch or LED-rail state in telemetry. Because the switch is not a controller
wake source, Auto cleanup returns to an always-listening idle animation rather
than deep sleep.

The first accepted gesture starts ADR 0078's bounded six-minute Wake/neighbor
gather. Each of the twenty NeoHex boards visibly loads center-out in the shared
37-pixel spiral geometry with a moving frontier head. Once ready, later gestures
remain chimes through the one-hour pre-dusk lighting overlap and switch to color
at true civil dusk using canonical trusted UTC. Night selections display across
all 740 pixels and cycle red -> green -> blue -> dim RGB; the matching tree
frames use 64 on single channels or `21,21,21` RGB with no W die. Session
renewal, 15-minute inactivity, one-hour absolute maximum, repeated Auto, graph
planning, exact canopy targets, and no power-tier target filter match the Atom.

Native gesture and visual-policy tests pass, including knock, drift,
motion-only, sensor-loss, single-fire, and re-arm cases. The complete fixture
core suite reports `ALL TESTS PASSED`. The final channel-11 PowerFeather build
uses 962,625 bytes (28 percent flash) and 129,108 bytes (39 percent RAM); its
962,768-byte binary has SHA-256
`6d7f18db8a6fc8d7b2228f198784ead206bd21fe588d6dc12c48b2279cee3d73`.
No wand or fixture was flashed. ADR 0079 records the decision and hardware
validation gates.

## 2026-09-02 -- Ben + Codex -- Ben-only Atom Conductor built

Added `firmware/atom_conductor/` as a separate fleet controller while preserving
the reduced one-target `atom_clicker/`. One face-button wake now opens a bounded
six-minute Wake/neighbor-survey gather. The Atom reconstructs a 160-peer local
graph from each reporter's eight strongest observations and centrally replays
fresh, class-confirmed canopy waves: exact-target deliberate chimes or chunked
RGBW direct frames. Disconnected graph components fall back to six-dB
Atom-relative RSSI bands; power tier is intentionally not a target filter, so an
awake PROTECT/low-voltage canopy may attempt an operator strike while its own
power policy still owns sleep.

Clarified and implemented the two-clock contract from the design discussion.
Every strike/color/color-advance button action refreshes only the Atom's local
15-minute inactivity timer. A separate scheduler issues explicit Wake renewal
every five minutes while that local activity remains fresh. Effects never invoke
the Wake sender. Fifteen minutes idle or one hour absolute starts a ten-second
repeated Auto cleanup and GPIO39 deep sleep. Fixture-side expiry remains
authoritative if the Atom crashes or loses power. The conductor has no WiFi,
OTA, maintenance, NVS mutation, fleet-sleep, or serial command surface and
remains Ben-only while
fleet commands are unauthenticated (ADR 0078).

The automatic actuator family follows true civil dusk, not the inspection
light's one-hour pre-dusk start: short press remains chime throughout that
visible-light overlap, then becomes the next R/G/B/W wave at civil dusk. The
Atom consumes the existing `NB_TIME_QUALITY` path and the canonical UTC
consensus/BRC solar calculation. Missing or stale trusted time fails closed and
emits neither strike nor light; lifecycle heartbeat state is deliberately not a
fallback because Wake changes older images and inspection night starts early.

Atom native timing/graph/action-gate tests and the full fixture-core suite pass.
A real channel-11 Atom Matrix build with a 40 ms strike and RGBW value 64 passes
at 938,165 bytes (47 percent flash) and 54,936 bytes (16 percent RAM); binary
size is 938,416 bytes with SHA-256
`715a64c90056dc511b95015389520574b3123c0eb71ba232d102c03b560322f9`.
No Atom was flashed. Button wake/current, named-canopy commands, graph geometry,
trusted/missing-time and civil-dusk switching, installed-fleet traffic, PROTECT
behavior, and power-loss recovery remain hardware validation gates.
## 2026-09-02 -- Ben + Codex -- Final-burn branch promoted to main

At Ben's request, the complete `codex/burn-final-sunrise` history was prepared
for fast-forward promotion to `main`. This carries the emergency inspection
firmware source, retained immutable fixture artifacts, T-Deck performance-hold
work and flash records, and the partial 2026-09-01 fleet-rollout evidence into
the repository's primary branch. The burn branch remains available as a named
historical pointer.

## 2026-09-01 -- Ben + Codex -- Inspection image partial fleet rollout

Exact immutable artifact `fx-260831-f121868-b` was OTA-deployed at the tree in
router-sized waves. Seventy of 114 installed fixtures now have fresh
exact-revision proof beyond the 25-second pending-verify gate. Forty-four remain
on prior images; 39 reported PROTECT in the final snapshot. Five confirmed
physical canopy/downlights remain. No fixture below 2.872 V was encountered in
the successfully uploaded waves, and no upload required physical intervention.

The shared-WiFi client population plateaued around 14-16, so the rollout used
explicit small batches. Job waves verified 16 + 13 + 14 + 14 + 13 fixtures.
`F4042C` missed one job freshness deadline but supplied supplemental fresh proof
18 seconds later at 419,516 ms uptime. Two older `-p` images (`9F0E30` and
`9F26B4`) continued mesh heartbeats but did not expose maintenance endpoints.
Ordinary exception and 14-board PROTECT gathers found no endpoints and made no
uploads. At operator departure the bridge reported no active maintenance
campaign. Exact resume roster, job table, and artifact identity are recorded in
`docs/tests/ADR_0074_PARTIAL_FLEET_ROLLOUT_2026-09-01.md`.

## 2026-09-01 -- Ben + Codex -- Perimeter charging diagnosis: P126 setpoint mismatch plus no-input outliers

Onboarded through the repository orientation, live architecture, recent power-policy
ADRs, production fixture source, retained Black Rock City censuses, and the current
read-only dashboard state. The active full-fleet inspection-artifact OTA job was not
interrupted or mutated.

All 20 registry-known perimeters in the live dashboard reported field profile,
charging enabled, no BQ fault, and `bq_vindpm_mv=4600`. The same nighttime snapshot
had a 3.190 V median, 19/20 below the 3.250 V PROTECT-release floor, and 16/20 already
reporting PROTECT. Production firmware defaults and persists 4.6 V for every class,
but the production-cabling P126 sweep qualified 5.8 V. The exact July 10 same-wake
P126 comparison measured 4.6 V at a 16.2 percent BQ-input-power penalty and about a
19 percent battery-charge-current penalty versus 5.8 V. This is a real fleet-wide
harvest loss, but it does not by itself explain zero input.

The retained daylight censuses separate the mechanisms. Around 15:18 PDT on Aug 28,
five of six now-known perimeter IDs had good charger input, but only about 0.10-0.23 W
and none had positive battery current while awake. Around 18:18-18:25 PDT, 15 of 17
had good input at up to about 0.30 W, but only four ever crossed positive awake battery
current. Negative current during a 12-second radio wake is not proof of zero daily
charge: the BQ continues charging autonomously through the following 120-second sleep.
It does prove that the installed late-day panel power did not cover the awake load.
Skitty `F3FD28` and Gengar `F2BDD4` instead showed the true no-input signature --
roughly 0.01 V and 0 mA at the charger input -- and are now the two lowest known
perimeters at about 2.98 V and 2.95 V. Their panel orientation, shade/dust, pigtail,
polarity, and VDC connection remain physical inspection priorities.

Conclusion: MPP/VINDPM is a contributing configuration defect and likely erases the
small P126 energy margin, while actual disconnected/shaded panel paths and the prior
commission-profile drain explain additional failures. The emergency bright/long
inspection posture can keep the class energy-negative even after profiles are fixed.
Do not broadcast 5.8 V fleet-wide: P105 fixtures are qualified at 4.6 V, and a 5.8 V
persisted setting rejects 5 V USB. Safest next strong-sun test is artistic loads off,
named-perimeter telemetry before/after physical inspection, then a target-isolated
4.6 -> 5.8 -> 4.6 comparison. A production correction should be class-aware in field
operation and return to a USB-safe 4.6 V before maintenance. Existing TODO items
already cover the perimeter panel inspection and MPPT decision, so no duplicate was
added.

## 2026-08-31 -- Ben + Codex -- Performance Hold flashed on second T-Deck

USB identity on COM157 confirmed exact second T-Deck `979604`
(`44:1B:F6:97:96:04`) before writing. The same ADR 0077 Performance Hold
development image already verified on `8EB508` was uploaded without rebuilding:
1,568,560 bytes, SHA-256
`5b4a896504ec81d67edda16bd59b88bbec2e98ce524c2ea93bab228e132fa639`.
Esptool verified every written region. Post-reset telemetry confirms exact ID,
channel 11, stable memory, approximately 4.51 V USB-powered battery telemetry,
and `tdeck-dev-local`. The local fleet dashboard moved from disconnected COM152
to the currently attached COM157 bridge.

## 2026-08-31 -- Ben + Codex -- One-hour T-Deck Performance Hold

ADR 0077 adds a separate confirmed Performance Hold to the T-Deck Wake app.
It republishes the existing inspection-safe lifecycle mode-0 command every two
seconds for one hour, so sleeping fixtures gather and their fixture-owned
ten-minute direct-control arms keep refreshing. The final controller copy
leaves up to roughly ten minutes of bounded tail. Direct/audio frames still
cannot extend the deadline; Auto or Night Show replaces the campaign, and all
fixture battery/recovery authority remains unchanged. No fixture protocol,
source, or immutable artifact changed.

The Wake screen now retains the original 16-minute option, adds a distinct
`hold 1h` button, and displays the active campaign plus remaining time. The
warm-cache T-Deck build passed at 49 percent flash and 59 percent static RAM;
its 1,568,560-byte binary SHA-256 is
`5b4a896504ec81d67edda16bd59b88bbec2e98ce524c2ea93bab228e132fa639`.
USB upload and flash hash verification passed on exact T-Deck `8EB508`
(`44:1B:F6:8E:B5:08`). Post-reset channel-11, GPS UTC, mesh-send, and memory
telemetry are healthy. The full native wrapper stopped at the already-recorded
missing-callsign gate for `9F268C` and `F402A8`; the wrapper contract and all
native core binaries pass when run past that inventory-only gate. No new native
core module was introduced by this controller/UI-only change.

## 2026-08-31 -- Ben + Codex -- Wake Fleet timing clarification

Final audit clarified ADR 0075's bound without changing code or artifact. Wake
Fleet republishes for six minutes, and each campaign packet refreshes that
fixture's ten-minute inspection-control deadline. The final campaign copies
therefore leave roughly ten minutes of full-fleet control, for a maximum session
of about sixteen minutes from the button press. LED Studio and CoreS3 Audio
direct frames still cannot extend the deadline. ADR 0076 records the exact
semantics; retained artifact `fx-260831-f121868-b` already implements them.

## 2026-08-31 -- Ben + Codex -- Bounded inspection control and brighter audio

ADR 0075 restores deliberately limited operator control without restoring the
autonomous show. In the static inspection field image, T-Deck Wake Fleet now
runs its existing six-minute catch campaign but preserves lifecycle Auto and
opens one non-extendable ten-minute direct-frame window per captured fixture.
LED Studio and all seven CoreS3 Audio modes can drive the armed fleet; continuing
frames do not extend the deadline, ignored program/show streams do not create
awake holds, static inspection white returns after direct-frame staleness, and
night radio duty resumes at expiry. Auto or Night Show closes the window.
Perimeter direct output remains center-pixel-only, while point sources preserve
their explicit one-pixel RGBW command. DIM/OFF/PROTECT and all recovery gates
remain authoritative.

CoreS3 Audio now applies a RAM-only post-color output gain with 1X, 1.5X, 2X,
and 3X steps, defaulting to 2X. A fourth Audio footer button and USB `V` cycle
the setting; every channel saturates at 255 and fixture power policy still
applies downstream. T-Deck standalone OTA was explicitly deferred in favor of
bringing the Starlink/shared-WiFi path and this laptop out one last time.

The full fixture and CoreS3 native suites pass. Development hardware builds
pass for fixture (36 percent flash, 20 percent static RAM), CoreS3 (36/29), and
T-Deck (49/59). Clean source commit `7c1f71d` produced replacement immutable
field artifact `fx-260831-f121868-b` (1,217,856 bytes, SHA-256
`569fa5a584019e5b4d1dedcfbea832c2b72339246f12badb6042ee5adcd29c2e`).
Manifest commit/recipe/flags and independent byte/hash checks agree. No hardware
was flashed; fleet OTA remains the next action.

## 2026-08-31 -- Ben + Codex -- Emergency static inspection firmware implemented

Art Support judged the installed piece too dim and unsafe, so ADR 0074
temporarily supersedes the autonomous show. During the scheduled field interval,
every canopy/downlight, uplight, chandelier, and unknown fixture now renders
linear `R=G=B=255,W=0`; perimeters render only that same full-RGB physical
center pixel. Program/direct color, presence effects, autonomous propagation,
Identify/Smoke blinking, wake chimes, the hourly ritual, and 1 Hz choreography
traffic cannot alter this inspection frame. Existing startup sag limiting and
FULL/DIM/OFF/PROTECT authority remain unchanged.

The schedule now starts exactly one hour before evening civil dusk while still
ending at civil dawn. With trustworthy scheduled time and a safe active light,
ESP-NOW listens for 12 seconds and then turns only the radio off for 120 seconds;
the CPU and LED rail remain live, so there is no light blink. Missing time,
transport dark, pending OTA verification, incomplete wake power evidence, or a
failed radio restart restores continuous listening/recovery. A fresh full
heartbeat is sent at each listen-window start.

Measured full RGB is about 417.6 mA total and the awake controller/radio branch
has measured 116-168 mA, radio-RX dominated. The 9.1 percent radio duty can save
at most about 105-153 mA average; even a conservative half-of-116 mA avoidable
case saves about 53 mA, roughly 13 percent of the full-RGB load. The exact
radio-off/CPU-awake floor remains unmeasured and is not overstated. The complete
native suite passes, and the ESP32-S3 field/channel-11 development build passes
at 36 percent flash and 20 percent static RAM with the deployed 120/12 cadence.
Clean commit `4efad93` then produced immutable artifact
`fx-260831-32dcb76-b` (1,216,864 bytes, SHA-256
`e82376535270057297f28198c94f9d51d65b2886fde16d63d1de386f10dac981`).
Independent manifest/hash checks pass. The exact binary and canonical handoff
files are retained in git for the camp ThinkPad; nothing was flashed and fleet
rollout remains pending.

## 2026-08-31 -- Ben + Codex -- ADR 0073 partial fleet rollout stopped at 96/112

Built immutable field/channel-11 fixture artifact `fx-260831-dc82da7-b`
(1,220,192 bytes, SHA-256
`7230f81ff1737fa51ebdd357b9249748e5712657469de82a4b5b75799ac83299`)
from clean source commit `49e06b7` and deployed it through USB T-Deck bridge
`8EB508`. Fresh exact-revision heartbeats beyond the pending-verify interval
prove 96 of 112 fixtures: all 91 fixtures that were non-PROTECT at rollout
start plus five explicitly targeted PROTECT fixtures (Ponyta `F2B7DC`, Batman
`F2BDC4`, Gengar `F2BDD4`, Yoshi `F2BE08`, and Donkey `F2BE10`).

Ben ended the field session before the remaining PROTECT phases. Sixteen
fixtures still report rollback artifact `fx-260831-b3e2738-b`; 15 received no
upload, while Abra `F2BDB4` closed its HTTP connection and never produced a
new-revision heartbeat, so it is correctly counted as not updated. The final
six-target campaign `98A408F1` found no endpoints and was manually frozen
before the host process was stopped. The final dashboard record reports phase
2 and `active=false`, so no OTA campaign was left running. Exact updated and
resume rosters, battery snapshot caveats, and job-ledger identities are in
`docs/tests/ADR_0073_PARTIAL_FLEET_ROLLOUT_2026-08-31.md`.
Because this laptop is being retired before the resume pass, the handoff commit
also force-retains the artifact's canonical binary, manifest, recipe, build
options, and SHA file at its normal immutable build path. The next bench can
therefore upload the exact existing bytes rather than rebuilding them.

## 2026-08-31 -- Ben + Codex -- Minimum-viability role lighting implemented

Implemented ADR 0073 as one final-burn fixture/handheld bundle without changing
the battery or recovery authority. During the scheduled-night field show,
uplights now render one RGB-white point at 128 when the underlying mode is dark
and 255 when it is lit. Perimeters now render only their full-scale RGB-white
center pixel; all other HEX pixels stay zero, and their VL53L5CX remains sampled
and telemetried but no longer modifies art or originates presence traffic.
OFF/PROTECT still cut the rail, DIM still scales the rendered values, and
transport/boot/OTA service safety remains intact.

Canopy presence now blinks the program or direct-stream color at 1 Hz instead
of replacing it with dedicated warm white. The T-Deck LED screen adds an
explicit `R=G=B=255,W=0` RGB-white swatch while retaining the existing dedicated
W swatch. A brightness-path audit found no gamma transform: frames and driver
scaling are linear and NeoPixel global brightness is 255. Existing dimness is a
mix of optical/3V3 limitations and deliberate low-valued program states,
battery DIM, and dense-HEX current limiting; it is not an unseen gamma penalty.

The full fixture native suite passes. Fixture and T-Deck ESP32-S3 development
builds pass at 36 percent flash/21 percent static RAM and 49 percent flash/59
percent static RAM respectively. The focused T-Deck direct-frame native test
passes; its full wrapper remains blocked by the pre-existing missing callsigns
for `9F268C` and `F402A8`. No immutable artifact was created and nothing was
flashed or OTA'd in this implementation session.

## 2026-08-31 -- Ben + Codex -- Final-burn fleet deployed and PROTECT census

Deployed immutable field/channel-11 artifact `fx-260831-b3e2738-b` (1,220,288
bytes, SHA-256
`1c31b265a1dba8544a7b02670e42382314d20fc0820cb67ed312ad43b25c349d`)
from clean source commit `316470a` to the installed fleet through the USB T-Deck
bridge. Every upload used an explicit short-MAC roster and fresh identity/power
preflight. Success required a new exact-revision mesh heartbeat after the job
start and survival beyond the 25-second OTA pending-verify window; upload ACKs
alone were not accepted. Attempts that lost a maintenance endpoint or did not
discover a target made no upload to that target.

The staged fleet jobs and two final direct-target retries leave all 112 visible
PowerFeather fixtures on the exact artifact, with zero older revisions and zero
fixtures reporting commission profile. Low-voltage PROTECT peers were included
after Ben explicitly accepted the A/B rollback tradeoff. Eight of eight in the
first low/early PROTECT cohort and seven of seven in the phase-aligned final
cohort passed; the latter safely deferred sensorless perimeter `F402A8`, which
then passed the legacy direct-target path at 3.211 V. Canopy `F3FC90`, which had
ignored several roster campaigns, also passed the direct-target path at 3.251 V.
No OTA failure required physical access. Ben reports the new ordinary-wake
two-chime behavior is "incredibly delightful" and working very well in the art.

The post-deployment dashboard census found 19 fixtures explicitly reporting
PROTECT plus two abbreviated deep-sleep reports retaining a 900-second,
`last_sleep_tier=3` state (`F2BDB4` and `F3FD28`), for 21 active/probable
PROTECT fixtures. Known roles are ten perimeters (the nine registry-labeled
perimeters plus Skitty `F3FD28`, whose prior USB/VL53 history proves its physical
role), three uplights, and four downlights; four remain role-unresolved. Lowest
reported batteries were uplight Donkey `F2BE10` at 2.98 V, perimeters Gengar
`F2BDD4` and Skitty near 3.02 V, downlight Ponyta `F2B7DC` at 3.03 V, and
unresolved Chunli `9F2714` at 3.04 V. Registry locations for all three PROTECT
uplights remain `trunk light - position TBD`, so the telemetry cannot identify
which, if any, are on the north side. All 21 report the exact new revision and
field profile; Skitty's `commission_failed` registry status is historical sensor
commissioning metadata, not a current commission firmware profile. The fleet
registry now preserves physical perimeter roles for Rotom `F2BF7C` and Skitty;
Rotom is promoted to commissioned after its fresh class-2 heartbeat reported
healthy VL53L5CX and MSA311, while Skitty remains sensor-failed.

## 2026-08-31 -- Ben + Codex -- DG1022Z HEARTBEAT visible but under-scaled

Ben and the waveform owner ran the no-human DG1022Z path into the powered PUCA.
The HEARTBEAT response works, but Ben reports it remains very dim with the Rigol
at 4 Vpp and both carrier controls fully clockwise. The generator is explicitly
not connected to a person, so the body-connected isolation prohibition was not
in scope for this bench observation.

No amplitude increase beyond the documented 4 Vpp faceplate baseline was
recommended without capture evidence. Next discriminate the source waveform
from the PUCA gain map using a High-Z, 0 V offset, 4 Vpp 1 kHz sine, then capture
PUCA `peak`, `wave`, `gain`, `ceil`, and `clipblocks` over service USB. The
current faceplate path attenuates about 4:1 and HEARTBEAT maps the raw codec peak
linearly through at most 4x sensitivity, so firmware scaling remains a credible
cause if the sine also stays dim. No firmware or hardware was changed.

## 2026-08-31 -- Ben + Codex -- PUCA HEARTBEAT field controls reconciled

Onboarded from the canonical architecture, current PUCA hardware/firmware
records, ADRs 0035/0063, and the DG1022Z runbook for a read-only operator
walkthrough. Reconciled the installed `puca-bridge-0.5.5-dev` safe-boot behavior:
hold the capacitive paw continuously for 1.2 seconds during the five-second
steady-red boot opportunity to arm DJ + line, then release and use one short
touch to select HEARTBEAT; a long hold locks immediately or the setup window
locks 20 seconds after the last activity. Boot-held arming is hardware-proven;
the post-arm short-touch/long-hold sequence remains native-tested but not yet
recorded as a hardware acceptance pass.

The paired Rigol DG1022Z bench baseline remains one front-channel analog output,
High Z load display, 0 V offset, and 1 Vpp initial amplitude into PUCA J5/J6
AUDIO IN with generator output disabled during hookup. No device was opened,
powered, commanded, built, flashed, or otherwise changed. The existing warning
still applies: do not electrically join PUCA/Pod20/USB/Tree ground to a
body-connected ceremony circuit without a separately isolated monitor boundary
approved for the complete powered system.

## 2026-08-30 -- Ben + Codex -- Final-burn autonomous art bundle implemented

Implemented the deadline-driven single field bundle in ADR 0072. Canopy
downlights now attempt one battery-safe cymbal hit after a trustworthy daytime
wake sample and a second before sleep, with a durable stochastic attenuation
knob defaulting to 100 percent. The UTC-hour ritual now uses the same FULL/DIM
safety boundary instead of requiring solar surplus; OFF/PROTECT and every hard
mechanism gate remain vetoes.

Perimeter interaction now holds the crisp center pixel through transient
too-close invalid/zero distances only after a proven valid close approach.
Program/wave origins now default to a five-minute minimum plus 30 seconds
continuously clear before re-arm, without slowing local sensor rendering. A
rootless UTC schedule rotates every 10 minutes through existing CA, Color
Virus, Epidemic, and a K=2/no-spark visitor-started CA. Canopy and perimeter
ToF fixtures may originate these program events; other classes relay/render.

Added canonical append-only packet type 31 and one versioned NVS blob for the
four field knobs, plus a confirmed/audited T-Deck Field screen. The first full
fixture native run passed. A fresh T-Deck embedded build passed at 49 percent
flash and 59 percent static RAM. The T-Deck native wrapper remains blocked by
two newly preserved commissioned fixtures (`9F268C`, `F402A8`) lacking callsign
assignments; no physical identity was invented to bypass that data contract.

The fresh immutable fixture build completed from clean commit `316470a` using
the current fleet recipe (field profile, channel 11, basic listener, 300 mA
precharge, 120-second day sleep, 12-second wake listen, and WiFi profile label
`party-in-the-woods-v1`). Artifact `fx-260831-b3e2738-b` is 1,220,288 bytes
with SHA-256
`1c31b265a1dba8544a7b02670e42382314d20fc0820cb67ed312ad43b25c349d`;
the independent host hash matches its immutable manifest. Nothing was flashed
or OTA'd as part of the build.

A read-only rollout preflight found the laptop on the site `192.168.1.0/24`
LAN, but no serial bridge was connected and no fixture served a maintenance
`/telemetry` endpoint anywhere on that subnet. No maintenance command or OTA
upload was attempted: without a bridge or an already addressed maintenance
endpoint there was no identity-checked path to the fleet.

## 2026-08-30 -- Ben + Codex -- Laptop-retirement field evidence preserved

Fetched current `origin/main` before retiring the Nevada City/BRC laptop and
reconciled every linked worktree against the remote. Preserved the uncommitted
canonical fleet registry work from the 2026-08-30 perimeter recovery session:
one newly registered fixture and 13 updated perimeter fixtures, all with unique
IDs and parseable CSV records. Several records deliberately leave firmware
identity blank where the reported image had no matching immutable manifest or
binary SHA in this checkout.

Also retained six previously untracked Black Rock City JSONL records: the
arrival censuses, the successful Dixie and Froakie canary OTA jobs, Kairi's
freeze-unconfirmed recovery attempt, and Sakura's dry-run ledger. The short
arrival trace carries incorrect default battery metadata and is explicitly
excluded by the following authoritative trace; it remains as raw append-only
evidence rather than being silently discarded. The two Sakura canary/post-TMF
records found in the older release worktree were byte-identical to files already
on `origin/main` and were not duplicated.

## 2026-08-29 -- Ben + Codex -- Completed-work integration prepared for main

Collected every unique completed change from the active fixture, daytime
ritual, canopy canary, and PUCA worktrees onto current `origin/main` without
mutating or discarding their source histories. The integration retains the raw
Spyro, Gible, Astro, Donkey, and fleet-operation ledgers; combines the canopy
motion/presence diagnostics with automatic immutable artifact identity; keeps
PROTECT sleep ownership in power policy; and includes the hourly cymbal ritual,
fail-closed sentinel persistence, Spyro post-mortem, installed-height findings,
and capacitive-paw validation. Two retained Spyro JSONL records were normalized
from CRLF to LF with no JSON content change.

The complete fixture native suite passes, including the build-wrapper artifact
contract and all combined lifecycle, ritual, motion, and sentinel regressions.
The PUCA native suite passes 129 checks, and 41 focused Python motion, sentinel,
dashboard OTA, and dashboard tests pass. Final integration is ready for the
explicit `origin/main` update requested by Ben.

## 2026-08-29 -- Ben + Codex -- Eevee recovered from low-voltage PROTECT

Exact outer-ring downlight Eevee `9F0E54` / `D8:85:AC:9F:0E:54` appeared on
COM70 after Ben tapped physical RESET. Read-only telemetry on dual-site image
`fx-260828-658b7d2-p` showed a genuine retained 3.030 V PROTECT entry, 3.304 V
battery with about +1.05 A charging, good USB input, no BQ fault, and stale
6 Ah NVS capacity despite the registry's physical 15 Ah assignment. The old
image's longer physical-reset service window stayed awake long enough to
complete its healthy-battery proof, persist OFF, and reboot. MSA311, TMF8820,
and required outer-ring BMP581 then all sampled normally.

Reused already-built immutable canary `fx-260829-b0ff5db-b`, SHA-256
`276d6558116a40da15f32eccf6bc7a940ef6d827ba965ddb81a8a8f5b0e27ae0`; no
compile ran. Exact USB commissioning restored 15,000 mAh capacity and passed
the shared-WiFi endpoint at `192.168.1.119`. After explicitly returning from
maintenance WiFi to COMMS, settled telemetry showed 3.314 V / +1.108 A,
good 4.637 V input, 2 A charge configuration, no BQ fault, tier 2 / stage 3,
field profile, channel 11, ESP-NOW up, exact revision, `pending_verify=false`,
and healthy MSA/TMF/BMP samples with zero TMF errors. Evidence is in
`ops/bench/data/usb/2026-08-29-9F0E54-protect-canary.jsonl`.

Eevee is ready to unplug, but this variant-`b` service image has only the
Party In The Woods maintenance profile. Add it to the future dual-site
production tail before fleet closure.

## 2026-08-29 -- Ben + Codex -- Logan proves the fixed timer-wake PROTECT release

Exact downlight Logan `9E5A88` / `D8:85:AC:9E:5A:88` appeared on COM158 during
a short deep-sleep wake. Read-only telemetry on dual-site production image
`fx-260828-658b7d2-p` showed 3.595 V / 100 percent, good 6.245 V input,
charging enabled, no BQ fault, and durable power tier 3 / guard stage 4
PROTECT. Its retained sleep receipt named the immediately preceding failure:
120-second `day-charge` sleep at tier 3. That is the exact lifecycle race
previously diagnosed on Toad. The port disappeared at the old 12-second wake
boundary as expected.

Caught the next exact wake and uploaded already-built immutable bench canary
`fx-260829-b0ff5db-b`, binary SHA-256
`276d6558116a40da15f32eccf6bc7a940ef6d827ba965ddb81a8a8f5b0e27ae0`;
no compile ran. Ben confirmed this physical downlight has a 15 Ah cell, so its
stale 6 Ah NVS capacity was corrected to 15,000 mAh. The retained PROTECT latch
survived both upload and the configuration reboot.

Issued one exact-target, one-second serial sleep while the canary still held
PROTECT. On the resulting genuine deep-sleep wake, Logan remained awake at
21.636 seconds with tier 3 / stage 4, good input, no fault, and the exact image
-- directly beyond the old 12-second day-sleep cutoff. It then completed the
sustained full-battery release, persisted stage 3 / LEDS_OFF, software-rebooted,
and advanced to stage 2 / DIM. Settled telemetry showed field profile, channel
11, exact image, no interruption, healthy MSA311 and TMF8820 samples with zero
TMF errors, ESP-NOW, and `pending_verify=false`. The first WiFi HTTP read had an
empty body after successful association; one explicit COMMS resume and bounded
transport-only retry passed the exact endpoint at `192.168.1.186` without a
second upload. This is the missing real-hardware acceptance of the fixed
timer-wake branch. Evidence is in
`ops/bench/data/usb/2026-08-29-9E5A88-protect-timer-release-canary.jsonl` and
`ops/bench/data/usb/2026-08-29-9E5A88-protect-timer-release-proof.jsonl`.

Like Toad and Groot, Logan currently carries the one-profile variant-`b`
service image and must receive the future dual-site production artifact before
fleet closure.

## 2026-08-29 -- Ben + Codex -- Shuckle isolated to a bad sensor-chain cable

Exact downlight Shuckle `F4031C` / `68:EE:8F:F4:03:1C` appeared on COM33 on old
commission image `fx-260817-ec7f28d-b`. It initially reported the last reset as
panic, `pf_ready=false`, no battery, no sensors, and no rail. A non-writing ROM
flash-ID check proved healthy ESP32-S3 revision 0.2, 8 MB flash, 2 MB physical
PSRAM, and exact MAC. The following captured boot reproduced four failed
`Board.init` attempts, failed VSQT off/on control, a class mismatch, and repeated
LED-rail pad verification failures. No image was built, flashed, or erased.

Ben fully depowered the fixture and disconnected the external STEMMA chain.
USB-only boot immediately restored the PowerFeather, charger/gauge telemetry,
300 mA precharge readback, no-fault BQ, and rail control. TMF8820-only then
passed presence and ranging with zero errors; MSA311-only passed presence and a
healthy sample. Reattaching both sensors reproduced the hard bus failure with
the original and replacement chain attempts. The suspect inter-sensor cable
finally failed even when connected directly from the PowerFeather to the
known-good MSA311, isolating a defective or miswired cable rather than a dead
PowerFeather or sensor.

Before a separately proven replacement cable was available, Ben accidentally
connected solar without the battery. Shuckle then stopped enumerating over USB;
the planned USB-only bootloader recovery was deferred when Ben moved to the next
fixture. Registry status is now quarantined with explicit do-not-install notes.
Next service must remain USB-only, preserve flash/NVS, replace and independently
prove the cable, restore the full chain and confirmed 15 Ah battery, then pass
exact USB/WiFi commissioning before quarantine is removed.

## 2026-08-29 -- Ben + Codex -- Groot recovered and received the PROTECT-sleep fix

The next USB-connected problem fixture did not enumerate during a no-reset
watch lasting longer than its ordinary 120-second day cycle. One deliberate
physical RESET exposed exact downlight Groot `9F2724` /
`D8:85:AC:9F:27:24` on COM76. Read-only telemetry on accepted production image
`fx-260827-1254f04-p` showed a real installed 15 Ah LFP, durable guard stage 4 /
power tier 3 PROTECT, good 4.597 V USB input, +547.5 mA battery charging, and no
BQ fault. The retained entry was at 2.974 V, so unlike Rikku this was consistent
with a genuine earlier low-voltage latch.

The physical reset provided the ten-minute cold-boot listen window. Groot
therefore completed the existing 60-second charge-current release, persisted
stage 2 / DIM, and clean-software-rebooted before any flash. Both required
downlight sensors then returned healthy. This distinguishes the initial USB
silence from a bad cable or dead board: the fixture had been in its 900-second
PROTECT sleep cadence, and USB insertion alone is not a wake source. The old
image remained vulnerable on ordinary 12-second timer wakes to the independent
day-charge sleep bug already proven on Toad.

Uploaded the already-built immutable bench canary `fx-260829-b0ff5db-b`; no
second compile occurred. Exact USB identity, ESP32-S3 revision 0.2, 8 MB flash,
2 MB physical PSRAM, binary SHA-256, field/channel-11 configuration, 15 Ah /
2 A settings, 300 mA precharge, no-fault charging, downlight class, MSA311 and
TMF8820 samples, ESP-NOW, and shared-WiFi maintenance endpoint all passed. A
settled post-check reported the exact revision, stage 2 / DIM, no interruption,
3.274 V at +543.1 mA, and `pending_verify=false`. This remains a one-profile
variant-`b` service image, not the future dual-profile fleet artifact. Evidence
is in
`ops/bench/data/usb/2026-08-29-9F2724-protect-day-sleep-canary.jsonl`.

## 2026-08-29 -- Ben + Codex -- Toad fixed; artifact identity made automatic

Fixed the lifecycle ownership bug diagnosed below. `lifeTick` now suppresses
ordinary field `DAY_CHARGE` sleep whenever the power tier is PROTECT, leaving
the PROTECT cadence and qualified 60-second release entirely under power
policy. Native regression coverage keeps ordinary FULL/DIM/OFF day sleep
unchanged and pins PROTECT `wantSleep=false`. Integrated the accepted ADR 0069
and ADR 0070 source before validation; the complete native suite passed, as did
a guarded ESP32-S3 field/basic-listener build.

Built immutable canary `fx-260829-b0ff5db-b` from clean commit
`280598802a306c7d3c2b901b480f2dac864f4ca5`. Its canonical recipe SHA-256 is
`b0ff5db9edd5f65d1e53fbcbba85de6a291ee2e83527dd802e0e451183020071`;
the 1,212,640-byte binary SHA-256 is
`276d6558116a40da15f32eccf6bc7a940ef6d827ba965ddb81a8a8f5b0e27ae0`.
It is deliberately variant `b` and labelled `party-in-the-woods-v1`, because
this checkout has one local maintenance profile rather than the accepted
dual-profile fleet credential set.

The exact USB serial identity on COM56 matched Toad `F2BEE4` before upload.
Flash-ID, upload, embedded revision, field/channel-11 configuration, 15 Ah / 2 A
settings, no-fault BQ, downlight class, class match, MSA311, TMF8820, BMP581,
ESP-NOW, and pending-verify=false checks passed. A later deep-sleep wake still
reported the exact image; by 9.712 s it was charging at +536.7 mA from 4.637 V /
504 mA good input with all three sensors healthy. The retained boot stage was
already DIM after flash, so this hardware run did not recreate a live PROTECT
release; the native lifecycle test is the direct proof of that branch. Toad is
no longer parked and its ordinary 120-second field cycle is operating. Evidence
is in `ops/bench/data/usb/2026-08-29-F2BEE4-protect-day-sleep-canary.jsonl`.

The first artifact candidate exposed the recurring manual identity hazard: its
hash was calculated without the canonical recipe's final LF. The mismatch was
caught before upload and `fx-260829-e9350b7-b` was marked rejected/never
flashed. To remove that class of wasted cold build, `build.sh` now owns the
immutable transaction via `--artifact-variant`: clean-source check, exact
compact-JSON-plus-LF recipe bytes, derived revision and path, embedded identity,
fresh build, manifest/binary hashes, and post-build cross-check. Manual
`--artifact-dir`/`--fw-rev` is refused, direct flash/OTA is refused in artifact
mode, and profile/channel/non-secret WiFi label must be explicit. A compile-free
golden test reproduces accepted recipe hash `d374034...`, so newline, encoding,
key order, or normalization drift fails before compilation. The full native
suite passes with this contract. Also quoted three pre-existing registry notes
whose commas had malformed CSV rows, then recorded Toad's exact canary identity.

## 2026-08-29 -- Ben + Codex -- Toad PROTECT recovery defeated by day sleep

Onboarded from the repository and watched Windows USB long enough to catch the
short field wake of exact outer-ring downlight Toad `F2BEE4` /
`68:EE:8F:F2:BE:E4` on COM56. No firmware, profile, NVS, reboot, rail, or other
device mutation was requested. The host added the repository-documented
`pyserial` dependency only so the existing no-reset telemetry path could run.

Read-only telemetry identifies accepted artifact `fx-260827-1254f04-p`, field
profile, channel 11, correct 15,000 mAh capacity, downlight class, valid OTA
state, and durable guard stage 4 / power tier 3 PROTECT with the LED rail off.
The retained PROTECT entry was at 3.039 V in field profile after about 1,637 s
of fixture uptime, consistent with the known low-VBAT history. A separate
durable receipt records a prior six-hour radio-all sleep from exact T-Deck
`8EB508`, sequence 10, but the current recurring sleep is local rather than a
still-active operator command.

USB power and the charge path are healthy. On the next 120-second wake, the
early stale gauge sample corrected by 5.9 s; at 11.151 s telemetry reported
3.283 V, +506 mA corrected battery current, 4.637 V / 486 mA good input,
charging enabled, no BQ fault, and verified 300 mA precharge. The port then
disappeared at the approximately 12-second wake boundary. The following boot
record named the preceding sleep `day-charge` for 120 seconds, not PROTECT for
900 seconds.

This proves a control-plane race, not a failed cell, charger, cable, or USB
port. `power_policy` correctly suppresses its own PROTECT sleep while the
60-second charge-current release proof is accumulating, but `behavior_glue`
independently takes ordinary field `DAY_CHARGE` sleep once the ADR 0064 power
sample window completes. That path does not exclude `LedTier::PROTECT` or
otherwise honor the in-progress release hold. Deep sleep clears the RAM-only
release timer, so each 12-second wake restarts a proof that requires 60
continuous seconds and Toad can never release. The current Aug-28 source and
accepted artifact change PROTECT proof quality/provenance but leave this
day-sleep gate unchanged, so updating alone is not yet an adequate repair.

Leave Toad connected: it is safely dark and gains charge during each wake and
subsequent sleep, but the durable latch will remain until the sleep ownership
bug is fixed or an explicitly controlled service posture keeps it awake long
enough for the automatic release. Next is a native regression and source fix
making the power-policy path the sole owner of PROTECT sleep, followed by a
clean immutable artifact and exact-Toad canary under ADR 0040.

## 2026-08-29 -- Ben + Codex -- Primary T-Deck updated to current Bridge OS

USB-flashed the other known T-Deck Plus, exact identity `8EB508`
(`44:1B:F6:8E:B5:08`), observed on `COM152`. The guarded development-cache
wrapper rebuilt from pushed commit `30c4124` before upload. The resulting
`tdeck-dev-local` binary is 1,565,584 bytes with SHA-256
`345f150d53ceec57de6925531953a38e49cff2de87523ab359cd6fa36992721d`.
Esptool verified every written region and reset the board successfully.
Post-reset serial reported the exact `8EB508` identity on mesh channel 11,
healthy 8 MB PSRAM, keyboard, touch, ES7210, and GPS probes, active mesh receive,
and zero send failures. The camp-labelled TSwift `979604` was not connected or
changed during this flash.
## 2026-08-29 -- Ben + Codex -- Spyro sentinel post-mortem; fail-closed recovery and VL53 watchdog fix

The first flash-persistence hardware follow-up used exact Spyro `F2BCF0` and
target-only artifact `fx-260829-96862d8-t`. OTA job `34CB76FC` verified the
test image through pending verify, but the run did not produce an accepted
retrievable trace. Exact restore job `E1428FE2` later returned Spyro to retained
fleet artifact `fx-260827-1254f04-p` and verified the restore through pending
verify. Retain both operation ledgers, but do not count this as the required
hardware persistence acceptance.

Ben reported at least 18-21 close approaches during the controlled run. After
the expected retrieval transition, Spyro rebooted with `task_watchdog`, failed
to accept the checkpoint without reporting why, and silently started another
30-minute campaign. It rebooted again one 30-second settle plus one 10-minute
baseline later, exactly at `startTof()`. The synchronous VL53 firmware upload
over the required 100 kHz bus serviced the watchdog only before and after the
whole transfer; the timing and source isolate that unserviced transfer as the
rerun watchdog. Fresh boot telemetry reported `sensor_bits=10`, proving MSA311
at corrected address `0x62` plus VL53 on that boot. Earlier bit-2-only boots are
therefore intermittent probe/rail-chain evidence, not proof of absence.

Source hardening now treats an interrupted or corrupted campaign as a recovery
condition instead of silently starting the physical experiment again. A
separate CRC-protected run marker is written before acquisition. On boot, a
matching marker without a valid artifact-bound checkpoint enters rail-off,
recovery-only maintenance. Completed checkpoints are read back and fully
validated before persistence is advertised. Validation reasons are explicit in
telemetry and the HTTP trace header, and the host capture tool refuses a
recovery-only fixture. The pure core module pins the packed marker/header
layouts, artifact tag, CRCs, sequence/count constraints, and named failure
reasons. Long VL53 transfers service the task watchdog through the shared
watchdog seam. A new `--sentinel-trace-smoke` option compresses the automatic
sequence to 40 seconds. Smoke telemetry is tagged and the power downloader
rejects it, so checkpoint/readback, same-artifact reset survival, and retrieval
can be proven without operator interaction before another full campaign.

The complete native fixture suite passes, including the expanded 23-check
sentinel regression; 25 focused Python tests pass; and an ESP32-S3 development
compile passes at 36% flash / 20% globals. The process failure is explicit: an
unproven persistence path was tested with another full campaign, and phase was
later inferred from silence, causing unnecessary repeated requests to Ben. No
further human-assisted campaign is permitted until smoke checkpoint, deliberate
same-artifact reset, exact trace recovery without rerun, and exact-prior restore
all pass.

## 2026-08-29 -- Ben + Codex -- Shaded Spyro rerun reproduced retrieval reset; trace persistence added

Re-ran the exact-target perimeter sentinel A/B/A on Spyro `F2BCF0` with the
panel physically covered and orientation fixed. Immutable artifact
`fx-260829-9f140c3-t` from source `61f2b0c`, 1,225,728 bytes, SHA-256
`03a100407b7a51e61f61cb9b81c855e39d7405dadc9ddd893c97ba51906c7512`,
uploaded only to Spyro. Fresh input stayed below `supply_good` at zero input
current, and Ben made about 14-15 close approaches during the VL53 phase.

The image reported exact revision at 2,625 ms and again from the same boot at
29,575 ms, proving the 25-second pending gate. The host verifier falsely timed
out because its five-second live-age limit was narrower than the bridge's
cached-peer report cadence. It now latches a fresh exact-revision boot and can
accept a later same-boot monotonic uptime/sequence report without allowing
cached identity to cross a reboot.

The completed controlled trace was again erased by a `task_watchdog` reset
before HTTP retrieval. This independently reproduces the retrieval fault and
shows that watchdog-safe async scan alone cannot make volatile PSRAM evidence
acceptable. Exact-target sentinel builds now checkpoint the completed trace to
the otherwise-unused SPIFFS data partition before WiFi starts. Sector-bounded
erase/write operations feed the watchdog; the header is written last; and boot
requires matching artifact tag, schema, sample size, header/sample CRCs, count,
no overwrite, and exact sequence before resuming retrieval. A later WiFi reset
therefore retries with the flash copy instead of re-running the experiment.
The full native suite, 20 OTA/capture Python tests, and an ESP32-S3 development
compile pass. Hardware persistence proof is still required. Exact-prior restore
job `612D848D` subsequently found only Spyro at `192.168.1.99`, uploaded the
retained `fx-260827-1254f04-p` bytes, and formally verified a fresh same-boot
heartbeat at 27,720 ms. Final state was exact prior revision, field profile,
perimeter class, `sensor_bits=2`, recovery zero, no BQ fault, and charging input
after the panel was uncovered. No lid access was required.

## 2026-08-29 -- Ben + Codex -- Spyro sentinel run restored safely; retrieval watchdog fixed

Ran the first exact-target ADR 0071 sentinel campaign on physically identified
perimeter fixture Spyro `F2BCF0`. Clean immutable artifact
`fx-260829-f13e090-t` from source `bb86098`, 1,225,488 bytes, SHA-256
`249c500e3a9bf12ab4902ec1db1c18680605d3a1a35bf7933e2c162dc1061cb1`,
passed single-target OTA, fresh exact-revision rejoin, and pending verify. Ben
performed about 15-16 close hand holds during the 10-minute radio-off VL53
phase. The corrected canary probe still reported `sensor_bits=2`, so Spyro's
MSA311 was not freshly proven despite the historical wrong-address bug.

The run is not an accepted power result. Rapid sunrise made the A/B/A solar
input nonlinear, and maintenance retrieval later hit an 8-second task watchdog
while no HTTP endpoint was available, erasing the completed PSRAM trace. The
unbounded gap was the synchronous all-channel WiFi scan; join loops already
serviced the watchdog. Maintenance now runs that scan asynchronously, polls
while resetting the watchdog, and falls back to configured credential order
after 15 seconds. Native tests, 17 Python OTA/capture tests, and an ESP32-S3
development compile pass.

Spyro was recovered without opening its lid. Exact restore job `DCE67738` found
it at `192.168.1.99`, uploaded retained prior artifact
`fx-260827-1254f04-p` / SHA-256
`2f9a93344e172b023ee8df473b7c747b26f38dc0ec5353f6efd00d50ec45f4af`,
and proved fresh software-reset rejoin beyond pending verify with field profile,
perimeter class, FULL tier, no BQ fault, and valid input. The full evidence and
required stable-shade/full-sun reruns are in
`docs/tests/PERIMETER_SENTINEL_CANARY_2026-08-29.md`.

## 2026-08-29 -- Ben + Codex -- Hourly cymbal ritual and sentinel power gate staged

Recorded the installed noisemaker truth: all 72 canopy/downlight mallets strike
small finger cymbals mounted on the bamboo, not bare bamboo. ADR 0071 accepts a
rootless hourly daytime ritual for energy-ready field downlights. Its fixed
T-20 through T+47-second window attempts a high-time-quality fleet unison at
T+5, one deterministic 500 ms hash-slot roll from T+12 through T+35.5, and a
one-quarter-fleet after-ring from T+42 through T+45.5. The unison abstains above
500 ms reported UTC uncertainty; the organic acts tolerate at most 3,000 ms.
Invalid time, scheduled night, weak energy, a bridge/program lease, wrong
class, or any existing solenoid hard gate remains an abstention.

DAY_ACTIVE now means energy permission rather than an all-day radio lease. A
field fixture returns to the ordinary bounded sleep/listen cadence from either
day state. A confirmed energy-ready state may cross one timer sleep, is
consumed at boot, and re-arms only if the fresh wake still satisfies the real
strike gate. With valid UTC, an eligible downlight shortens only the final
ordinary sleep needed to wake 20 seconds before the hour. The per-event ledger
is RTC-retained and marked before actuation so a mechanism refusal or reset
cannot retry the same event into a brownout loop.

Persistent perimeter sensing remains deliberately unimplemented. Instead, a
new exact-target `--sentinel-trace-target` test image runs an automatic 10-
minute radio-off/sensor-off baseline, 30-second VL53 warm-up, 10-minute radio-
off MSA311/VL53L5CX phase, and second 10-minute radio-off/sensor-off baseline.
One-second PSRAM records retain corrected/raw battery current, battery/supply
telemetry, charger state, explicit radio/rail truth, VL53 progress/range/zones,
and palm-cover edges. Maintenance WiFi starts only after the campaign. The
downloader verifies exact identity/revision/target/perimeter/completion, proves
radio and rail phase truth plus advancing VL53 frames, and exclusive-creates
the JSONL. The runbook requires physical target confirmation, one writer, an
immutable `-t` artifact, and restoration of the exact prior fleet binary.

The complete native fixture suite passes, including 18 daytime-ritual checks,
15 sentinel-ring checks, and the expanded build-wrapper contract. Six Python
capture tests and syntax compilation pass. A guarded, throwaway field/channel-
11 sentinel test compile with dummy target `A1B2C3` passes at 1,207,669 bytes
program / 68,804 bytes globals and emits a 1,207,984-byte binary. The temporary
binary was automatically discarded; no artifact was published or flashed.
Next is one named cymbal/downlight hourly-boundary canary and one physically
confirmed perimeter power campaign before any sentinel implementation.

## 2026-08-29 -- Ben + Codex -- Windy-night canopy presence passes

Ben physically located Sakura `F2BE0C` with Fleet Identify and corrected the
census inference: Sakura was in a bin, not installed high. Its all-zero TMF
scene therefore meant an open/clear view from the bin, not evidence of canopy
height. Ben pointed Sakura at himself and the ADR 0070 canary correctly changed
from its low-white baseline to full dedicated white. This closes the new
artifact's sensor -> presence latch -> visible output path. Separately, people
walking beneath the installed tree reliably caused canopy lights to turn white,
which is the intended artistic response. The precise named installed-height
artifact canary remains useful for quantitative margin, but the installation's
observable interaction is working.

The test occurred on a windy night and invalidated the mental model of a rigid
sensor observing a moving target. Each lantern swings chaotically as a pendulum
over roughly two degrees of freedom, so its TMF cone scans the space. A person
standing still can be discovered sequentially by several nearby fixtures as
their cones swing across them. This feels alive and should be treated as an
artistic affordance, not automatically motion-compensated away.

No firmware threshold changed from this observation. The next tuning step is a
correlated empty-wind/person trace of TMF depth, per-zone confidence, MSA311 sway
envelope, and visible presence state. Use it to distinguish desirable swinging-
scanner encounters from background/branch/ground false positives and to choose
minimum white hold, release hysteresis, and retrigger cooldown. Preserve the
current proven behavior until that evidence exists; do not use MSA as a blanket
veto because it would suppress the exact wind-assisted discovery Ben observed.

## 2026-08-29 -- Ben + Codex -- Exact-target canopy flight recorder staged

Implemented the evidence path requested by the windy-night observation without
changing the production interaction. An exact-target `-t` image now records a
bounded motion flight trace during ordinary mesh/show operation, so capture
does not require the hanging light to stop behaving. Each 25 Hz MSA sample
retains raw XYZ, low-pass gravity, tilt/sway, all nine current TMF zones and
confidences, the production presence edge/latch, lifecycle/program/power tier,
and the rendered LED snapshot. PSRAM holds 8,192 samples (about 5.5 minutes); a
reported 1,024-sample fallback is used if PSRAM allocation fails.

The recorder is compile-bound to one six-digit fixture ID and disables itself
on a physical-ID mismatch. After the scene, maintenance WiFi exposes a bounded
NDJSON batch endpoint. `ops/bench/capture_motion_trace.py` verifies exact
fixture identity, exact `-t` revision, compiled target match, downlight class,
MSA health, maintenance state, and buffer availability before exclusive-
creating a JSONL trace. The field runbook requires a visually confirmed hanging
target, one OTA writer, a named pre-trace artifact/SHA, exact single-target OTA,
and restoration of that prior artifact through fresh heartbeat and pending-
verify proof.

All native fixture tests pass, including the new ring overwrite/cursor test;
the downloader unit tests pass. A full ESP32-S3 commission/channel-11 test
compile also passes at 1,204,237 bytes program / 68,780 bytes globals and emits
a 1,204,528-byte binary. No target artifact was built or flashed because the
physical hanging fixture ID still needs visual confirmation.

## 2026-08-29 -- Ben + Codex -- Sakura 15 ft canopy canary staged

Built immutable production candidate `fx-260829-8790f6d-p` from clean pushed
source `ab71b8989b12e860ad1d82a5e1cf4767773a86f7` with the current field recipe:
channel 11, 300 mA precharge, 120-second day sleep, 12-second wake listen,
listener commission default, and dual-site maintenance credentials. The binary
is 1,212,640 bytes with SHA-256
`5bd65970990a34e511b44cb9a9ef1a7dc4e93a7b3cd3746df08abafb3e0ab6bf`.
Recipe hash, embedded revision, clean commit, build options, manifest, exact
binary bytes, and SHA file all agree.

Declared one OTA writer and targeted only healthy zero-return installed-height
candidate Sakura `F2BE0C`. Exact job `C804CF1F` passed dashboard and fresh
maintenance power preflights at 3.31-3.32 V, identity-matched
`192.168.1.109`, uploaded the exact retained artifact, produced a fresh exact-
revision software-reboot heartbeat, and remained on that revision past the
pending-verify gate at 31,044 ms uptime. It retained field profile, downlight
class, and recovery state 0. The complete job and uploader ledgers are retained
in the Black Rock City data folder.

A post-update exact TMF census then recorded six consecutive raw zero-depth
reports while TMF remained read-OK with 405-456 completed reads, zero errors,
zero recoveries, and zero sensor-domain resets. This proves that accepting the
full 5 m range does not turn the high empty scene into a permanent ground
target. A 10-minute exact CA lease produced the expected visible low-white
baseline (`rail=1`, one pixel, `W=25`). An eight-minute telemetry watch saw no
spontaneous `W=255` event. An exact 20-second identify blink was sent to help
locate the fixture, but no person-under-Sakura attempt was confirmed during the
watch, so human detection is unexercised rather than failed. Eight exact release
acknowledgements ended the lease and a fresh mesh heartbeat completed cleanup.

Next: have a person walk/stand directly under Sakura while an exact visible
lease is active. If no `W=255` transition or raw 2.7-3.5 m return appears, treat
15 ft height/aim/sunlight as a P0 gating concern and test one lower or better-
aimed canopy fixture before any fleet promotion.
## 2026-08-29 -- Ben + Codex -- Astro control puts useful raw range below 1.6 m

Repeated Gible's raw 1-5 m height/aim experiment on lower-hung downlight Astro
`9E5B44`, reported near 12 ft. Built exact-target-only artifact
`fx-260829-066846f-t` from the same pushed source `d9cb775`; its 1,221,136-byte
binary SHA-256 is
`b9dba40884967fd182093d1e9ab370a7d40fd89b74f5ccc3ec6588d967636877`
and immutable recipe SHA-256 is
`066846f139e79f02aaa1ef6709e8618563d544e28bebada4e7db3ecf2cfeba09`.
The only diagnostic recipe change from Gible was the target lock. Job
`861C9C57` updated only Astro and verified it through pending verify.

Dawn suppressed the field show, so Astro alone received a temporary,
nonpersistent commission profile. A pre-existing RAM-only fleet dark lease was
released; scheduled field fixtures remained dark while Astro rendered the raw
red/white sentinel. Ben observed only a split-second flicker while walking
beneath Astro, but a substantially denser response when he raised his hand.
Astro is about 12 ft high and Ben is 6 ft 3 in, leaving about 1.75 m from sensor
to head before the raised gesture.

The exact rolling drain retained 913 samples over 304.3 seconds with no sequence
gap. It captured 35 white samples in 18 short runs. Every qualifying zone return
was physically plausible at 1,003-1,561 mm, confidence 20-41, across zones 1,
2, 3, and 5. There were no sampled 1.562-5 m returns. Empty intervals spanning
49.676 seconds before and 212.752 seconds after the interaction contained no
sampled 1-5 m false positives. This directly contrasts with Gible's nearby
raised target being misreported at 3.24-5.00 m.

Lowering therefore helps, but roughly 12 ft remains marginal for passive
walk-under interaction: Ben's head gap was just outside Astro's demonstrated
reliable band and a raised hand moved into it. Test roughly 10 ft or equivalent
re-aim before choosing an installed height; do not threshold-tune around
Gible's far artifacts. Exact job `AFF7F2E7` restored Astro's original
`fx-260828-658b7d2-p` image and verified field profile, downlight class, recovery
state 0, and pending-verify survival at 32,039 ms uptime.

## 2026-08-29 -- Ben + Codex -- Raw Gible test rejects 5 m as usable physical range

Ben challenged the earlier interpretation correctly: Gible is less than 5 m
high, yet a normal person did not trigger it and a bamboo split had to be held
roughly 2 m from the sensor. The retained 4.8-5.0 m values proved that firmware
no longer discards far reports, but they did not prove accurate or useful
physical ranging at those distances.

Built exact-target-only artifact `fx-260829-4192016-t` from pushed commit
`d9cb775`, 1,221,136 bytes, SHA-256
`27b9d412d4fe51c44fc37d4adc75a7c2b0481ab2750c13b08f020482773b7fc2`.
Its immutable recipe SHA-256 is
`419201645ff0321b58030837faac989ebb8648e108e5429131e0ad696907f113`.
The diagnostic excludes Gible's known 166-363 mm self-splay, then treats any
confident zone from 1,000 mm inclusive through 5,000 mm exclusive as immediate
presence: no learned background, hit debounce, or hold hysteresis. Red means no
such zone and full RGB white means one is present. Compile-time isolation
prevents the aggressive predicate from originating or relaying a mesh presence
wave. All native checks passed, including 565 presence checks, and the fresh
ESP32-S3 build ended at 1,220,833 bytes program / 68,788 bytes globals. Job
`AB8F3FA6` updated only Gible and verified the exact image through pending
verify at 32,289 ms uptime.

The 860-sample trace retained 300.500 seconds with no overwrite or sequence
gap. It was red for 123.895 seconds before and 142.250 seconds after the sole
34.355-second interaction window. No sampled 1-5 m return and no white output
occurred in either empty interval. During Ben's raised-bamboo interval, 45
samples were white across 23 raw rising edges. The detector contract matched
exactly: every sampled 1-5 m return was white and no sample without one was
white.

The ranges inside that interval are the decisive anomaly. Despite Ben placing
the bamboo split roughly 2 m from the sensor, the TMF produced no 1-3 m zone
return. It produced eight 3-4 m returns and 65 4-<5 m returns across zones 0-4,
plus one raw exactly-5,000 mm report. Confidences were 20-79. Maximum frame
summary was 4,988 mm and maximum zone was 5,000 mm. These are not isolated
empty-scene false positives; they appear only when the nearby raised target
changes the optical scene. They are therefore evidence of aim, partial
occlusion, edge/background ranging, or multipath, not calibrated 5 m person
range.

The software parser and visible path work, but Gible's installed sensor geometry
fails the physical usability gate even with every background/debounce
discriminator removed. Do not tune production thresholds around these far
numbers. Lower or re-aim Gible, clear the TMF aperture/field of view, then repeat
a normal-person test. Exact final job `105DD74F` restored normal canary
`fx-260829-7906e6f-p` and verified it past pending verify at 26,599 ms with
field profile, downlight class, and recovery state 0.

## 2026-08-29 -- Ben + Codex -- Gible sentinel proves the path but not useful interaction

The earlier rolling captures left Ben unconvinced that the installed-height
experiment was timed and signaled clearly enough. Built exact-target-only trace
artifact `fx-260829-e98247b-t` from pushed test commit `ce785c5`, 1,222,416
bytes, SHA-256
`f19c8e2f597e0baa3145c0c2c450becf07b83a398685da4a21140a6e118d2bdc`.
Its immutable recipe SHA-256 is
`e98247b9ddff406e8e16769073792e839b14a9751200aa55853cfa166c15bbb5`.
The build is locked to Gible `9E5B34`, marked target-test-only and never
fleetable, and retains just over five minutes at one 300 ms sample per record.
It leaves the production TMF gate/debounce unchanged but replaces visible
output on that exact target with an unmistakable sentinel: solid red without a
presence latch and full RGB white while the latch is active. Exact Identify
still has higher precedence and supplied green start/end markers.

Job `C2DFDDB2` updated only Gible, received fresh 3.297 V maintenance evidence,
and verified the exact trace image through pending verify at 23,972 ms uptime.
Ben physically confirmed the red baseline. The final 1,024-sample capture
contained two approximately 10-second green markers at sequences 1031-1060 and
1501-1530. Between them, the first 111.855 seconds after the first marker were
red with no false latch. Ben then had to hold a split high to trigger Gible.
The recorder captured five separate presence rises at 2,504-4,497 mm and 49
active samples across 27.356 seconds. Every active sample rendered exact
`R=255,G=255,B=255,W=0`; no inactive sample rendered white. The sequence then
returned to red for 8.030 seconds before the second green marker. This rules out
capture timing and proves the sensor -> full-range parser -> production
debounce/latch -> render arbitration path on installed hardware. Exact capture
campaign `29CC104A` selected only Gible, froze before drain, and made no NVS or
profile mutation.

The trace also answers the range-cap question directly. Its maximum retained
post-parser zone was 4,982 mm at confidence 32; the maximum frame summary was
4,781 mm. The parser therefore demonstrably accepts the TMF through its 5,000 mm
limit. Presence intentionally has a separate 4,500 mm empty-background ceiling,
so the 4,982 and 4,781 mm frames did not initiate a latch. Rising-edge depths
were 4,497, 2,508, 2,860, 3,829, and 2,504 mm. Ben's impression that the useful
trigger was mostly near 2.5-3 m is consistent with the trace and is not evidence
that the retired 2.5 m parser cap remains.

It does not pass ADR 0070's usability gate: ordinary standing and walking had
not triggered, and the successful gesture required holding the reported split
high. Treat the remaining issue as installed aim/range/sensitivity, not a dead
sensor or broken output path. No production threshold or fleet artifact changed.
Exact restore job `F02313D7` put normal canary `fx-260829-7906e6f-p` back on
Gible and verified it past pending verify at 27,560 ms with downlight class,
field profile, and recovery state 0.

## 2026-08-29 -- Ben + Codex -- Gible installed-height canopy canary failed

Built immutable normal canary `fx-260829-7906e6f-p` (1,212,736 bytes, SHA-256
`95df1a6b18f21c0f0643949e70474a4d2af019e85efbb86f21877af350dadb7d`)
from clean test commit `fe6619f`. Exact one-target job `A04CDF37` updated only
hanging downlight Gible `9E5B34`, then proved fresh exact-revision rejoin past
pending verify with field profile, downlight class, healthy TMF/MSA, no class
mismatch, and recovery state 0.

The initial scalar censuses and timed/condensed person choreography were kept
as diagnostic evidence but rejected as acceptance runs. An exact-target trace
variant `fx-260829-1170f20-t` continuously recorded sensor, presence, motion,
and rendered LED state into a rolling buffer. Physical PSRAM was not exposed to
this image, so its explicit 1,024-sample internal-RAM fallback was used. Two
human-triggered drains retained about 70 seconds each without asking Ben to
race a timer: one while standing beneath Gible and one after a natural walk.

The standing window contained 48 valid depth frames at only 168-363 mm; the
walking window contained 23 at only 166-362 mm. Both were confined to the same
two near-field zones. Neither contained a person-range return, presence edge,
held presence, or full dedicated-white `W=255` response. Ben's observation of
repeated warm-white changes is also present in the trace: seven separate
pre-trigger `W=25` intervals match GH CA's ordinary quiescent point-source
state and provide a useful timing control. They are not the ADR 0070 response,
which requires the presence latch to force `W=255`.

The installed-height interaction gate therefore failed cleanly without a
threshold change or fleet promotion. Exact final job `32F8BF78` restored the
normal canary and verified it past pending verify at 28,353 ms; a later fresh
heartbeat showed ordinary mesh mode, field NIGHT_SHOW/FULL/GH CA, downlight
class, sensor bits `9`, no mismatch, and recovery 0. Next is mechanical
TMF-window/aim diagnosis using raw range evidence, not a wider parser limit or
weaker debounce.

## 2026-08-28 -- Ben + Codex -- Art-site TMF height census and 15 ft canopy fix

Ran a read-only exact-target TMF census while canopy installation was underway.
Campaign `207B660F` selected 61 live TMF-bearing downlights and discovered 46
shared-WiFi maintenance endpoints across one complete wake window. No firmware,
NVS, profile, or persistence write occurred. Six raw telemetry samples per node
separated 42 close returns at 145-575 mm, consistent with fixtures in bins, from
four healthy all-zero nodes: Panther `9E5A84`, Gible `9E5B34`, Sakura `F2BE0C`,
and Leia `F40384`. The latter are the strongest installed-height candidates,
though physical location is not proven. Fifteen nodes did not present an HTTP
endpoint and remain unsampled, not failed. Every sampled fixture subsequently
returned to mesh with a fresh heartbeat. Evidence is retained in the Black Rock
City data folder and summarized in the build-week TMF test note.

The census and Ben's report of roughly 15 ft sensor-to-ground mounting exposed
an artificial 2,500 mm firmware cap. TMF8820 hardware supports 5,000 mm, while a
standing head under this geometry is commonly about 2,700-3,200 mm away. ADR
0070 therefore accepts confident scene returns through 5,000 mm, extends the
empty-background presence window to 4,500 mm, clears a stale per-zone baseline
after 12 empty reports, and slowly follows a farther non-presence background.
This lets a powered fixture re-baseline after moving from a close shipping bin
to the tree without a reboot.

ADR 0069's downlight absolute distance/color/380 mm gobo rule is superseded.
Downlights now use the existing debounced per-zone presence latch and hold full
dedicated white while a person is present. Perimeter keeps its 150-1,800 mm
continuous hue and 37 -> 19 -> 7 -> 1 ring peel. Blackout, program suppression,
battery tiers, rail policy, and the physical HEX budget keep authority.

The full native fixture suite passed, including 558 presence checks. An
ESP32-S3 commission/listener development compile passed at 1,201,065 bytes
program and 68,716 bytes globals; its 1,201,360-byte `dev-local` binary SHA-256
is `c19b95df3e65aaade0a43625716defe0bf16911c6d1c307a1e9aaf32762775a2`.
No binary was flashed. Next is one immutable update on a named healthy installed
zero-return candidate and a person-under-fixture daylight/night canary.

## 2026-08-28 -- Ben + Codex -- Build-week palette, HEX power, and ToF sprint

Started the final build-week interaction sprint in an isolated clean worktree
from current `origin/main`; the active checkout's unrelated dirty T-Deck work
was not moved or modified. Upstream already recorded Ben's physical fleet truth:
20 manufactured uplights, with four former planning allocations returned to
unassigned, so no duplicate roster edit was needed.

ADR 0069 adds three bounded fixture-side improvements. First, the physical
37-pixel RGB HEX driver now budgets the rendered frame to 765 linear RGB channel
units after composing the existing battery-tier brightness cap. A sparse gobo
at or below one full RGB pixel/three full saturated channels remains unscaled;
dense washes are uniformly scaled with fail-safe downward rounding. Point RGBW
and uplight RGB output behavior is unchanged.

Second, autonomous GH CA uses the existing trusted UTC estimate for a
synchronized palette step every 20 minutes, with a six-step/two-hour loop.
Invalid time preserves the configured hue, and a bridge-owned program keeps its
requested palette. This is the first synchronized artistic cadence, not yet
program-ID rotation.

Third, a post-program local interaction layer restores continuous ToF behavior
without changing `packet.h`. From 150 through 1,800 mm, distance drives color;
the perimeter HEX peels 37 -> 19 -> 7 -> 1 pixels as someone approaches, and a
downlight switches to its full dedicated-W point source at <=380 mm for the
crisp gobo pop. It applies to any visible program, including direct bridge
frames, but an all-zero/suppressed frame remains dark and the physical current
budget plus all existing power vetoes remain downstream. MSA311 motion input is
plumbed into the same pure layer with a canary switch, but normal builds leave
it disabled until installed wind-versus-human traces set threshold/hysteresis/
hold behavior. BMP581 and multi-fixture aggregate gestures remain open.

The complete native fixture suite passed. A guarded commission/listener
PowerFeather development compile also passed at 1,201,937 bytes program and
68,708 bytes globals; its 1,202,240-byte binary has SHA-256
`9f9cd933e3c1a51929824d625e49d916be1fab298cf1aa9aea554d2d8e4a060f`.
This dirty `dev-local` binary is compile evidence only: nothing was flashed or
published. Named battery-installed perimeter and downlight canaries are next.
## 2026-08-29 -- Ben + Codex -- Sakura synchronized palette accepted

Reconnected exact T-Deck `8EB508` on `COM7` with fresh master timestamps and
advancing RX/TX counters, then took a strictly read-only Sakura sample. Exact
Sakura `F2BE0C` reported `fx-260829-8790f6d-p`, GH CA state 1, and RGB
`51,0,70`. That ratio exactly matches the firmware's expected UTC-derived
purple phase, while ordinary baseline downlights retained their static blue
hue. Ben simultaneously identified Sakura physically and described it as a
nice purple. Combined with the earlier red observation, later non-blue drift,
normal CA animation, exact canary provenance, and correct Fleet Blink/LED
Studio lease behavior, Ben accepted the synchronized palette feature without
requiring the remainder of a formal two-hour watch. The finite read-only
heartbeat monitor was deleted before any later run. No fixture command, OTA,
reboot, NVS, profile, or persistence write occurred. Palette cadence is no
longer a fleet-release gate; the electrical, installed-height, and ADR 0068
negative-safety gates remain open.

## 2026-08-29 -- Ben + Codex -- Canary inventory scopes unified fixture release

Audited the exact 110-fixture night census by artifact and source provenance.
The fleet is split across 76 general dual-site fixtures on
`fx-260828-658b7d2-p`, 16 freshly heard members of the completed 20-uplight
cohort on `fx-260828-d8f62c3-p`, 13 older baseline/holdback fixtures, and five
special canary instances: Akuma `9E668C` on mutable `dev-local`, Rikku `9F26B0`
on the ADR 0068 intermediate `fx-260828-abd893c-p`, Dixie `F40314` plus Froakie
`9E5B18` on ADR 0069 artifact `fx-260829-97aed8e-p`, and Sakura `F2BE0C` on the
ADR 0069/0070 superset `fx-260829-8790f6d-p`.

The source does have a coherent convergence path. Current `main` already
contains the dual-site maintenance, short-wake telemetry, full-battery PROTECT
recovery, MSA/uplight classification, and RGB uplight framing changes. Remote
branch `origin/codex/build-week-interaction-sprint` is exactly six commits ahead
from `main` with no divergent main commits. Fixture source through clean commit
`ab71b8989b12e860ad1d82a5e1cf4767773a86f7` adds ADR 0069's count-aware HEX
budget, synchronized palette, and local interaction plus ADR 0070's full-range
canopy presence. Its exact Sakura artifact passed identity, OTA/rejoin, pending
verify, basic sensor-to-output, and no-empty-trigger checks. The later
`fa2c9d9` motion flight recorder is exact-target diagnostic instrumentation and
is not part of the ordinary fleet-release cutoff.

Do not reuse or combine the existing canary binaries. After the remaining
hardware gates, merge the accepted source, build one new clean immutable ADR
0040 artifact, repeat a small mixed-role canary, and widen with explicit safe
target lists. Remaining gates are the ADR 0068 negative release/fault matrix,
one named installed-height canopy raw-range margin check, and a measured
perimeter HEX current/rail check. Ben subsequently accepted the synchronized
palette cadence from physical and exact telemetry evidence without requiring a
formal two-hour watch. Akuma's mutable development identity, low-voltage/PROTECT
fixtures, recovery exceptions, and target-bound diagnostics remain exclusions
until separately cleared. No build, OTA, fixture command, or persistent state
change occurred during this inventory.

## 2026-08-29 -- Ben + Codex -- Night census identifies Sakura palette canary

Onboarded through the canonical repository documents, then opened the existing
read-only host dashboard on the sole connected ESP32-S3 serial device. Exact
T-Deck `8EB508` was positively identified on `COM7`, channel 11, with zero
reported send failures. Its already-running census had seen 111 identities;
110 field-profile fixtures were heard within 15 minutes, 98 within 60 seconds,
and the five-second live count varied around 80-95 with the weak field links.
The 15-minute fixture cohort reported 108 NIGHT_SHOW, 105 CA, 96 FULL, 3 DIM,
and 11 PROTECT. Firmware was mixed across 76 `fx-260828-658b7d2-p`, 16
`fx-260828-d8f62c3-p`, 11 `fx-260827-1254f04-p`, two
`fx-260826-51d1fe1-p`, two `fx-260829-97aed8e-p`, and one each of
`dev-local`, `fx-260828-abd893c-p`, and `fx-260829-8790f6d-p`.

The same session exposed a bridge-side control failure. LED Studio and the
T-Deck Fleet/Blink action produced no visible response while fixtures continued
CA. Bridge receive frames kept climbing, but `sendok` remained exactly 9,058
through multiple attempted actions and `sendfail` remained zero. Source review
showed why the zero is misleading: transmit accounting observes only ESP-NOW
completion callbacks, while all ordinary `esp_now_send()` call sites discard a
synchronous enqueue error. LED Studio also reports the number of planned fresh
targets, not confirmed radio submissions. The failure is therefore isolated to
the T-Deck transmit path before fixture command acceptance, not CA arbitration;
the exact ESP-NOW error and initiating mechanism remain unknown.

Releasing COM7 for a read-only `show` query unexpectedly reset the USB-native
T-Deck. It returned mesh-only, channel 11, SSID unset, and ESP-NOW marked up.
After reboot, an exact-target diagnostic immediately advanced successful send
callbacks, and a new all-fleet green LED Studio stream advanced TX continuously
with zero callback failures. Ben confirmed every visible fixture green. Treat
reboot as recovery evidence, not root cause or an adequate permanent fix: add
synchronous-submit telemetry, a truthful UI fault state, and bounded recovery
for a flat TX counter while RX remains healthy.

The first telemetry interpretation did not identify the physical lantern. No
fresh class-bearing downlight heartbeat reported red output, while the fresh
red/orange renderers with authoritative LED telemetry reported perimeter class.
Ben eliminated Daxter `9D7884` because it is a known real perimeter light, then
showed that the anomalous lantern joined Fleet's filtered downlight green blink.
The lantern also followed the normal changing CA pattern and accepted arbitrary
LED Studio colors, ruling out a stuck LED channel, retired constant-red ready
behavior, and general direct-control failure.

Ben then filtered Fleet by firmware and identified the physical lantern on the
first try as Sakura `F2BE0C`, the sole observed `fx-260829-8790f6d-p` fixture.
Artifact provenance resolves the color anomaly: that exact canary was built
from clean pushed source `ab71b8989b12e860ad1d82a5e1cf4767773a86f7`, which
inherits `f5b86070931a6b32272735930fa8abf869ce02d2` and ADR 0069's synchronized
autonomous palette experiment. With trusted UTC and no bridge lease, GH CA
advances its base hue by 43 every 1,200 seconds in a six-step, two-hour loop.
A bridge lease deliberately preserves the requested hue. Sakura therefore can
appear red, later drift to a different non-blue hue, continue the same CA
animation, and still obey green Fleet Blink or any LED Studio color. This is
intentional canary behavior, not a class mismatch, missed OTA, stale hue lease,
or LED fault. Sakura was deployed as the installed-height canopy-presence
canary, but its artifact also inherited the palette-cadence experiment. That
feature remains on `origin/codex/build-week-interaction-sprint`; current main
does not contain it. Decide whether to promote the cadence or return Sakura to
the static fleet palette after the canary evaluation.

The post-blink host investigation also found that the dashboard's last master
and peer snapshot was frozen at 01:55 even though localhost continued serving
normally. COM7 no longer enumerated, but the page exposed neither serial loss nor
master age, so later apparent telemetry was cached rather than live. No firmware,
profile, NVS, OTA, or persistent fixture setting changed; the earlier diagnostic
COM reopen reset only T-Deck `8EB508`.

## 2026-08-29 -- Ben + Codex -- PUCA capacitive paw root-caused and boot arming proven

Retested exact PUCA `A4EB10` with both faceplate audio plugs removed. A confirmed
12-second stationary paw hold produced 11/11 `pawpin=0` samples, disproving the
idea that the earlier J8/J9 output-jack mistake was the continuing cause. Ohmic's
published trigger test uses `digitalRead(GPIO15)`, but its carrier schematic
routes the paw separately from the TL074 audio-output stages and the exact unit's
digital input never tracked touch.

Added an inactive-only raw ESP32 touch-channel probe in `0.5.4-dev`. The released
paw was exceptionally stable at 867-870 counts; a held paw fell cleanly to 216.
This proves the electrode, front-panel/header path, GPIO15, and ESP32 touch
peripheral. The first blocking probe exposed and then fixed two diagnostic-only
artifacts: one transient digital HIGH on peripheral restoration and receive-queue
drops while the loop was blocked.

Production paw handling now uses the actual ESP32 T3/GPIO15 capacitance channel,
not the vendor example's digital input. `0.5.5-dev` applies exact-unit hysteresis
(press <=650, release >=750) and rejects near-zero/shorted readings below 50 so
the arming gate fails safe. The 1.2-second continuous boot hold, five-second
opportunity, setup window, and SAFE-IDLE policy are unchanged. All 129 native
checks pass. Fresh artifact
`firmware/puca_bridge/build/puca-bridge-20260829-paw-cap-touch-v055-r1/puca_bridge.ino.bin`
is 1,038,176 bytes, SHA-256
`b7d4db31f339a14d079a273170544f6b4218a367075799736f1229a6c1c2f2c1`,
with `esp32:esp32:pico32:PartitionScheme=default`. Exact-target shared-WiFi OTA
uploaded once to identity-matching `A4EB10` and verified a fresh
`puca-bridge-0.5.5-dev` software-reset rejoin.

Ben then held the paw before a real Pod20 power cycle. The PUCA rejoined with
fresh `reset=poweron`; preserved USB telemetry proved `bootarmed=1`, `active=1`,
DJ + line input, released `pawcap=865-868`, 3,000+ direct frames, and zero send,
capture, queue, I2C, or clipping errors. USB `A` stopped publication and froze
the direct-frame count. A final released `P` probe remained 866-868 while
servicing mesh traffic, with `paw=0`, zero queue drops, and no synthetic edge.
The physical paw and boot arming are accepted; real RODE gain and the timed
post-arm setup gestures remain open.

## 2026-08-28 -- Ben + Codex -- PUCA mic modes proven; line and paw faults isolated

After the separate fleet OTA ended, declared this laptop the sole PUCA operator
and used T-Deck bridge `8EB508` on channel 11 plus exact PUCA `A4EB10`. A
service-started onboard-MEMS run exercised DJ, HEARTBEAT, EMBER, and HUE on the
live fleet, and Ben visibly confirmed audio-reactive fixture behavior. Serial
evidence covered about 75-92 fresh fixtures, RMS roughly
1,300-5,500, peaks through 14,685, useful rendered levels through 0.56, and zero
send, I2S-read, I2C, or receive-queue errors. Ben directly observed the audio-
reactive fixture behavior. Each run ended with `A`, a final blackout, frozen
direct-frame count, and return to inactive DJ/line state.

The laptop headphone proof did not reach the PUCA faceplate line input. Windows
recognized `Realtek HD Audio 2nd output`; a directed 96 kHz WASAPI stream played
successfully at about -8 dBFS. The endpoint was unmuted, and tests at its original
10 percent level and a temporary 25 percent level left PUCA at the same RMS 7-10
noise floor. The level was restored to 10 percent. This isolates the remaining
fault to the analog adapter/faceplate route or the WM8978 line-routing setup; it
does not implicate the shared codec/I2S/DSP/render/mesh path, which the onboard
mics proved. Verify adapter continuity and both J5/J6 inputs before changing
codec registers.

Ben later identified the exact passive chain: JSAUX `B07D8M5DML` 3.5 mm TRS
stereo male to dual RCA male, then two Bolvek `B09K3DHL82` RCA-female-to-3.5 mm
TS-mono adapters. This is electrically the correct one-channel-per-J5/J6
topology and does not inherently short or combine channels. Remaining physical
checks are continuity, full plug seating, and confirming J5/J6 AUDIO IN rather
than J8/J9 AUDIO OUT before investigating WM8978 line-register routing.

Correction and positive retest: the two TS plugs had in fact been in faceplate
J8/J9 AUDIO OUT. Ben moved them to J5/J6 AUDIO IN and the identical directed
96 kHz laptop waveform at the restored 10 percent Windows level immediately
raised line RMS from 6-12 at quiet to 37-41, with rendered level about 0.13-0.15,
zero clipping, and zero transport/capture errors across about 83-91 fresh
fixtures. `A` then stopped the publisher and returned level to zero. This proves
the exact cable chain, faceplate J5/J6 path, WM8978 line routing, I2S capture,
envelope, renderer, and fleet transport. Only real RODE gain/clipping and visual
per-mode/fallback acceptance remain on this audio axis.

A follow-up 28.5-second laptop burst run temporarily used 25 percent headphone
level and advanced DJ -> HEARTBEAT -> EMBER -> HUE at seven-second intervals.
The final status proved HUE active after the complete serial sequence, direct
frames advanced from 1,871 to 4,591, send callbacks reached 5,225 with zero
send/read/I2C/queue/clipping errors, and line level returned to zero with the
bursts stopped. Cleanup sent `A`, returned mode to DJ, and restored the Windows
endpoint to 10 percent.

A dedicated HEARTBEAT repeat used a synthesized 16-second paired-pulse waveform
through the same laptop/J5/J6 line path. With the top sensitivity control first
confirmed at its 4.00x maximum and the headphone endpoint temporarily at 60
percent, telemetry captured rendered peaks through 0.222 across about 84-93
fresh fixtures. Capture peaks reached 2,063 without a single clip, send failure,
I2S read failure, I2C error, or receive-queue drop. Cleanup stopped publication,
returned mode to inactive DJ, and restored the headphone endpoint to its 10
percent baseline; final telemetry reconfirmed gain 4.00x and zero error counters.
Ben visibly confirmed that the paired deep-red HEARTBEAT response works. He was
turning the sensitivity knob during the run, which explains the logged 0.26x-
4.00x changes; the complete top-knob sweep is therefore also proven. Physical
orientation is counterclockwise for more sensitivity and clockwise for less,
opposite Ben's initial expectation.

Ben requested the conventional carrier-control direction after that proof.
`puca-bridge-0.5.3-dev` now explicitly normalizes both carrier pots: fully
clockwise raises the top audio-sensitivity control to 4.00x and the bottom
brightness ceiling to 1.00; in HUE, clockwise also advances the color wheel.
The pure mapping and all existing safety/render checks pass 121/121. Fresh
combined artifact
`firmware/puca_bridge/build/puca-bridge-20260828-knob-direction-v053-r2/puca_bridge.ino.bin`
is 1,024,656 bytes, SHA-256
`97e43bf5e2686057474e95d4404a839967b9681e05832919ea81e77079b4bcb5`,
with the explicit `esp32:esp32:pico32:PartitionScheme=default` recipe. The prior
top-only `r1` build was never deployed. Exact-target `UA4EB10` maintenance found
identity-matching `192.168.1.159`, uploaded `r2` once, and verified a fresh
`puca-bridge-0.5.3-dev` software-reset rejoin. Post-update USB telemetry remained
SAFE-IDLE with zero direct frames and zero capture/transport errors.
After a later full power cycle, fully clockwise hardware telemetry read exactly
`gain=4.00`, `ceil=1.00`, and HUE endpoint 360, accepting both corrected control
directions. The original PUCA USB cable then enumerated only as a failed USB
device descriptor; moving the known-good T-Deck cable to PUCA immediately
restored its exact CP2102 identity on COM6. Treat the original cable as suspect;
the PUCA USB interface itself passed the swap test.

The first polarity guess produced and exact-target OTA-installed
`0.5.1-dev`, but official Ohmic Original Edition trigger source and later raw
telemetry disproved active-low operation. It was superseded in the same session.
Source and exact-target OTA now run `puca-bridge-0.5.2-dev`: active-high paw
handling, raw `pawpin`/`paw` telemetry, a five-second steady-red boot opportunity,
and elapsed-time audio calibration. Native tests pass 105/105. The immutable
candidate is
`firmware/puca_bridge/build/puca-bridge-20260828-paw-telemetry-v052-r1/puca_bridge.ino.bin`,
1,024,608 bytes, SHA-256
`3e3e8d9fa0ce3c8d60950abc027840eb345c95cf1f9438d1f0ff44cbac5a20e8`.
Exact-target shared-WiFi OTA found `A4EB10` at `192.168.1.159`, uploaded once,
and verified fresh `0.5.2-dev` software-reset rejoin. A subsequent full power
cycle also rejoined cleanly.

Hardware validated the calibration correction: `calibrated` was false at
1,500 ms and true at 2,505 ms before direct frames began. Paw release is
definitively GPIO15 low. Runtime sampling caught two intermittent high readings
about 4.2 seconds apart during one attempt, but a later confirmed ten-second
stationary hold produced no transition, and the five-second held-paw power-cycle
still returned `bootarmed=0`. Do not weaken the physical arming interlock around
an intermittent signal. Until the carrier touch path is electrically inspected
or traced at higher rate, USB service `A` is the repeatable bench start path;
SAFE-IDLE remains the no-touch boot result.

## 2026-08-28 -- Ben + Codex -- Daytime interaction and bounded fleet wake brainstorm

Onboarded from the current `main` architecture and reviewed the measured daytime
radio floor, field sleep cadence, UTC/civil-twilight scheduler, conditional solar
probe, perimeter palm gate, distributed CA/Contagion seams, and solarnoid policy.
No fixture, bridge, serial port, artifact, or shared bench was changed or
commanded. This is exploratory context, not a new ADR or implementation decision.

Continuous radio receive remains the wrong default: the measured dark-awake
floor is 126-144 mA before perimeter ToF load, or 1.51-1.73 Ah across 12 hours.
The promising architecture separates local renewable/strike eligibility from
radio availability. Strong solar may permit a strike or a richer rendezvous, but
should not by itself require all-day receive.

The leading artistic candidate combines scheduled and interactive behavior. A
bounded hourly daytime rendezvous wakes the fleet for a short roll call or
ring-wise composition and opens a fixed invitation window. Fresh perimeter palm
edges contribute engagement credits; distinct source IDs or sectors are more
valuable than a held/repeated gesture. Successive thresholds grow the response
from a few nearby downlights, to one ring, to a three-ring ripple, to a full
chorus. The session has an absolute hard end and cooldown that activity cannot
extend, while every downlight retains its autonomous solar/power/mechanism gates.

Between scheduled windows, a future low-duty perimeter-sentinel posture could
turn the radio on only after local ToF detection and let a small expiring event
spread as ordinary sleepers wake. Do not select that posture until the existing
named-perimeter A/B measures MCU plus VL53L5CX ranging with the radio off; the
small 2 W / 6 Ah perimeter class is the tightest daytime budget. The existing
generic choreography, event-fabric, sensor-power, wake-window, localization, and
solarnoid validation TODOs already cover the needed work, so no duplicate TODO
was added.

## 2026-08-28 -- Ben + Codex -- TMF8820 twenty-foot installation range reviewed

Onboarded through the canonical repository documents and compared the exact
ordered TMF8820-mini, current fixture implementation, open height-validation
TODO, and ams OSRAM datasheet performance. No firmware, fixture, bridge, serial
port, or shared bench was changed or commanded.

The TMF8820's specified maximum target distance is 5,000 mm (16.4 ft), while a
20 ft sensor-to-ground distance is 6,096 mm and cannot produce a ground return.
A roughly 6 ft person's head would be about 4,267 mm (14 ft) from the sensor,
inside only the best-case low-ambient raw range. The datasheet's 3x3 / 550 k
iteration table reaches 5 m on a full-FoV 18 percent grey center target under
350 lux LED lighting, but falls to 3.0 m center / 2.8 m edge / 2.0 m corner at
the equivalent of 1 klux sunlight; a person fills less than the test target.

The deployed source is more restrictive than the silicon: sensor parsing drops
returns beyond 2,500 mm and the no-background presence path admits only targets
within 2,200 mm. Therefore the current artifact will not detect a person from a
20 ft mounting height. A night-only foreground interaction may be recoverable
with a deliberately tested long-range configuration and gate change, but this
is not yet evidence: the exact-part downlight-height test remains open. If ToF
interaction matters, pause further high placement until one exact enclosed
fixture passes a 20 ft walk-under test; otherwise treat the high TMFs as class-ID
devices, not reliable presence sensors.

## 2026-08-28 -- Ben + Codex -- RODE-only PUCA mode proof scoped

Fast-forward pull confirmed local `main` already matched `origin/main`. Onboarded
through the canonical repository documents and reviewed the current PUCA hardware
record, ADRs 0035/0063, firmware, native tests, and audio operating guides while a
separate laptop retained ownership of the active fleet OTA. The in-progress
untracked fleet-OTA ledger was preserved and no serial port, bridge, fixture, or
PUCA was opened, commanded, reset, built, or flashed.

The RODE VideoMic NTG is sufficient to validate the PUCA line-input path and
visibly distinguish DJ, HEARTBEAT, EMBER, and HUE with speech, claps, or a played
click track. It cannot prove fidelity to the performer's exact arbitrary
waveform; that remains a later generator/photodiode gate. Current `0.5.0-dev`
has no dry-run or named-canary output: once armed it sends direct frames to the
complete fresh fixture census. SAFE-IDLE also returns from audio processing
before updating RMS, peak, clipping, envelope, or color evidence. Therefore do
not arm it in parallel with the fleet OTA. After the OTA operator releases the
radio, run the RODE test in a declared one-publisher window, capture serial
level/peak/clip evidence for all four modes, observe a controlled mixed RGB/RGBW
cohort, and finish by proving the roughly three-second autonomous fallback.

## 2026-08-28 -- Ben + Codex -- All 20 manufactured uplights updated

Declared one OTA writer and reused immutable artifact
`fx-260828-d8f62c3-p`, SHA-256
`57f40023e1e599d60cf2a309e6a7af2f94bf45716421309b2b3a15048b239097`.
The first two four-target campaigns (`70E694A4` and `385B7EF8`) completed their
full gather and freeze contracts but discovered no maintenance endpoints, so no
upload occurred. Windows exposed only the 5 GHz `Party In The Woods` BSSID,
which initially suggested a missing 2.4 GHz service. An exact no-upload Togepi
maintenance control then found `9E5AB0` at `192.168.1.207`, disproving that
hypothesis: Starlink's 2.4 GHz path was healthy and the Windows scan had omitted
it. The earlier selected fixtures simply had not woken into the campaign.

Job `45208DD7` targeted four freshly heard uplights (`F2BE1C`, `F3FC8C`,
`F2BEB4`, and `9F2694`). All four identity-matched, accepted the exact binary,
rejoined with the exact revision, survived pending verify, and retained field
profile. A direct post-update maintenance check on Psyduck `F3FC8C` reported
`fixture_class=uplight`, `class_ovr=0`, `sensor_bits=8`, and no mismatch; an
explicit second `/resume` returned it to mesh after the diagnostic HTTP client
timed out while the endpoint was dropping WiFi.

Job `444537E1` then targeted the other 15 uplights present in the dashboard.
All 15 maintenance endpoints were found, including previously unreachable
Donkey `F2BE10`; all 15 uploads acknowledged, all 15 produced fresh exact
revision heartbeats, all 15 survived pending verify, and none remained in
commission profile. Together with Togepi and the staged four, all 20 physically
manufactured uplights now report the exact artifact. Ben confirmed that only 20
uplights were made; the 24-row roster had incorrectly promoted four earlier
planning allocations into the physical cohort. Ken `F2B8DC`, Pikachu `F2BCE0`,
Kirby `F2BE64`, and Haunter `F40438` are not manufactured uplights, were never
rollout targets, and have been returned to role-unassigned registry state. The
uplight rollout is therefore complete at 20 of 20.

## 2026-08-28 -- Ben + Codex -- Combined safety/class artifact and Rikku canary

Built one immutable fleet artifact from clean pushed commit `5865282`, folding
the ADR 0068 full-battery PROTECT recovery together with the ADR 0067 MSA311
classification correction. The production recipe is field profile, channel 11,
300 mA precharge, 120-second day sleep, 12-second wake listen, and listener
commission default. Artifact `fx-260828-abd893c-p` is 1,211,504 bytes with
SHA-256
`6a0126f205be2cb6be034a71de5c5caa75f0af0acd00e1684ddc27377fb175f5`;
its clean commit, canonical recipe, embedded revision, toolchain, build options,
binary digest, and manifest all passed the ADR 0040 identity checks. The earlier
classification-only sibling artifact was never uploaded and is obsolete.

Exact Donkey `F2BE10` job `1004BAFA` acknowledged the single-target maintenance
campaign, but no endpoint appeared on either maintenance subnet across the full
360-second discovery window. Cleanup freeze was acknowledged. The host therefore
made no HTTP upload and Donkey remains unchanged on `fx-260828-658b7d2-p`.

Exact Rikku `9F26B0` job `A357B979` found a fresh endpoint at 3.597 V with good
6.138 V input and no power fault, uploaded the combined artifact, received a
fresh exact-revision heartbeat, and survived the 20-second pending-verify gate.
The retained false PROTECT state then satisfied the new sustained full-battery
proof, persisted LEDS_OFF, and made the intentional clean software reboot. It
subsequently advanced OFF -> DIM -> FULL while keeping the daytime LED rail off.
Fresh post-recovery telemetry through more than eight minutes shows field
profile, exact revision, FULL tier, downlight class, sensor bits 9 (TMF8820 plus
MSA311), no class mismatch, healthy BQ state, and no pending verify. This passes
the positive ADR 0068 hardware canary without erasing NVS or bypassing the guard.
The negative-gate fault matrix and fleet audit for other high-VBAT PROTECT
entries remain open.

Ben then brought in an installed uplight whose solar panel had been found
disconnected and connected it to USB. Read-only identity established exact
Togepi `9E5AB0`, a registry-rostered 6 Ah trunk/uplight. On the prior
`fx-260828-658b7d2-p` image it reproduced ADR 0067 exactly: automatic class was
chandelier, sensor bits were zero, and MSA311 was absent. Battery/input preflight
was safe at 3.430 V and about +418 mA charge with good USB, no BQ fault, FULL
tier, field profile, and rail off. An exact COM12 upload of the same combined
artifact verified every written region against hardware MAC
`D8:85:AC:9E:5A:B0`. Post-reset telemetry changed the same hardware to uplight,
sensor bits 8, MSA311 present with a good live read, no mismatch, exact revision,
and no pending verify. The first identity-gated `L1` smoke attempt asserted
`smoke_render=true` and the 3V3-enable pad high, but Ben saw no light. That was a
real second defect, not a bad rail: uplights are the lensed 3 W RGB module, while
`ledProfileForClass()` had incorrectly grouped them with downlight RGBW modules
and emitted four-byte `NEO_RGBW` frames. The W-only point-source smoke frame was
therefore invisible, and ordinary RGB frames also had the wrong byte stride.

Source commit `0f08904` fixes the physical class contract: perimeter and uplight
use three-byte `NEO_GRB`, downlight retains slot-proven `NEO_RGBW`, and the smoke
renderer uses equal RGB on an RGB point source versus dedicated W on RGBW. A new
platform-independent profile helper and 10 native checks pin those mappings;
the complete fixture native suite passed. The guarded ESP32 development compile
passed at 1,210,377 bytes program / 68,740 bytes globals. Clean immutable
artifact `fx-260828-d8f62c3-p` was then built from pushed commit `0f08904` with
the same production recipe: 1,210,720 bytes, SHA-256
`57f40023e1e599d60cf2a309e6a7af2f94bf45716421309b2b3a15048b239097`.
Recipe hash/prefix, clean source, manifest, build flags, binary digest, and
embedded revision all match. The prior `fx-260828-abd893c-p` remains valid for
Rikku's ADR 0068 canary but is superseded for every uplight.

An exact second COM12 upload verified every region on Togepi's hardware MAC.
Fresh telemetry retained uplight class, sensor bits 8, a good MSA sample, field
profile, channel 11, FULL tier, no fault/mismatch/pending verify, and ESP-NOW.
Corrected `L1` visibly produced the requested white breathing pattern; the
battery charge current fell from about +398 mA to +279 mA under the real LED
load. Ben confirmed the physical output was "beautifully breathing." `L0`
returned the rail off and charge current to about +420 mA; a 150 ms RTS reset
then restored ordinary field behavior with the rail off. ADR 0067 classification,
physical RGB framing, and optical smoke acceptance now pass on exact Togepi.

## 2026-08-28 -- Ben + Codex -- ADR 0068 full-battery PROTECT recovery developed

Implemented the fail-closed fix for Rikku's high-VBAT PROTECT deadlock without
weakening the loaded-collapse boot guard. OTA already parks all loads and clears
`load_arm` before writing, but correctly preserves an existing PROTECT stage;
high open-circuit VBAT also cannot disprove a real under-load collapse. The
entry ladder therefore remains fail-safe. The release plane now has two separate
60-second proofs, and changing proof or losing one battery sample restarts the
clock. The existing >=+20 mA / >=3.25 V proof now explicitly requires a valid,
enabled, no-fault BQ. The new full-battery proof requires a corroborated real
cell, >=3.45 V, good external input, valid enabled/no-fault BQ, and `CHG_STAT`
CV, top-off, or not-charging/done. CC with low current is rejected. Either proof
persists LEDS_OFF and makes the existing clean reboot; neither releases on
rebound voltage alone. A high plausible but uncorroborated cell requests the
rate-limited BQ presence test so a tapered cell can establish independent proof.
The same audit closed a pre-existing NVS failure hole: a failed PROTECT-stage
write now stays parked awake and retries instead of timer-sleeping back into the
older brighter stage; a failed release-stage write still returns to PROTECT and
cannot clean-reboot.

Added durable entry provenance without changing the 32-byte version-1 sleep
audit layout: local PROTECT reuses otherwise-empty remote-source fields for
origin, predecessor stage, reset reason, prior `load_arm`, and unexpected-reset
streak. Old records are annotated once as `legacy-unknown` without losing their
original voltage/profile/uptime. Append-only heartbeat tail 18 exposes the
context through T-Deck census/`nb-peer`, the logger, and fleet dashboard.
ADR 0068 records the decision and exact Rikku/fault-injection canary gates.

The complete fixture native suite passed, including 195 power-policy, 26
sleep-audit, and 70 packet-layout checks. The Donkey registry change was carried
into the generated T-Deck health roster; its freshness check and all directly
compiled T-Deck native test binaries passed. All 18 fleet-dashboard parser tests
passed. A guarded
field-profile PowerFeather development build passed at 1,210,353 bytes program /
68,740 bytes globals and produced a 1,210,656-byte `dev-local` binary with
SHA-256
`ca910470953cd3ebff9c952d04becf15b6e220931d74ddc19ebb9043c01648ee`.
That dirty-worktree binary is compile evidence only. Nothing was flashed or
mutated on Rikku; next is a clean commit, immutable ADR 0040 artifact, exact
Rikku automatic-recovery canary, and supervised negative-gate matrix.

## 2026-08-28 -- Ben + Codex -- Rikku false high-VBAT PROTECT deadlock

Ben connected a second canopy/downlight that was dark the prior night despite
a roughly 3.6 V battery. A timestamped read-only USB catch identified exact
Rikku `9F26B0` / `D8:85:AC:9F:26:B0` on COM11, running accepted artifact
`fx-260827-1254f04-p` with the correct field profile and 15,000 mAh capacity.
No flash, erase, maintenance, profile, rail, or NVS command was sent.

Telemetry proved durable guard stage 4 / power tier 3 PROTECT with the LED rail
off. The retained entry audit records PROTECT at 3.596 V in field profile only
2.809 seconds into that boot. This is far above the 3.15/3.10/3.05 V power
ladder and cannot be a voltage-floor transition. The leading mechanism is an
unexpected reset while the durable load marker was armed, possibly after the
one bounded FULL-to-DIM retry; the current audit does not retain the predecessor
stage or reset reason, so the initiating reset class is not proven.

Fleet history shows the latch predates the latest artifact: Rikku was already
handled on the 900-second PROTECT cadence, then accepted the exact
`fx-260827-1254f04-p` OTA at 3.582 V and survived pending verify. OTA correctly
preserved NVS, including the bad latch. A later gather still found it at
3.536 V on the same protected cadence.

The current USB observation exposed a release deadlock. Input was good, the BQ
had no fault, VBAT stabilized near 3.56-3.58 V / 99 percent, and the configured
15 Ah capacity was correct, but the nearly full cell accepted only about
0-2 mA. The compound release requires battery current >=20 mA continuously for
60 seconds, so a healthy full battery can never clear false PROTECT merely by
remaining on USB. Fix both axes before fleet use: make high-VBAT false
escalation diagnosable/less trigger-happy without weakening real collapse
safety, and add a sustained charger-termination/full-battery release proof that
cannot release a rebounded depleted cell. Rikku remains protected pending an
explicit recovery decision.

## 2026-08-28 -- Ben + Codex -- All canopy batteries confirmed 15 Ah

Ben confirmed that every canopy/downlight without exception has a 15 Ah
battery. Ponyta `F2B7DC` therefore has a live persisted-capacity configuration
error: telemetry reports 6,000 mAh while its physical class and existing
registry record correctly require 15,000 mAh. No device command or NVS write
was sent in this clarification; correct Ponyta through the declared exact-target
configuration path before relying on gauge SOC or capacity telemetry.

## 2026-08-28 -- Ben + Codex -- Sensorless uplight fallback and MSA311 probe fix

Ben reported that roughly eight installed trunk/uplights appear to share Donkey
`F2BE10`'s MSA311 detection failure. Opening that cohort to replace PowerFeathers
is not practical before deployment, while no chandelier fixtures are installed.
Ben therefore chose an installation-stage compatibility policy: automatic
sensorless fixtures are uplights, and future chandelier PowerFeathers will be
selected by exact MAC and persist an explicit class override before installation.

Source inspection found the fleet-wide cause behind the apparent hardware pattern.
The fixture's initial class probe polled `0x26`, the older MSA301 address, although
the installed Adafruit library and production MSA311 hardware use `0x62`; the later
runtime MSA311 driver already used the correct default. That split explains why a
ToF-bearing fixture could classify first and initialize its MSA311 later, while an
MSA-only uplight always appeared sensorless during class selection. The prior LOG
inference that the boot class probe used `0x62` was therefore incorrect.

ADR 0067 now supersedes ADR 0041's no-sensor-to-chandelier clause. Source probes
MSA311 at `0x62` and pins PART_ID `0x13`; automatic order is TMF -> downlight,
VL53L5CX -> perimeter, MSA311 -> uplight, then sensorless -> uplight. Existing
downlight/perimeter ToF-loss guards remain. Old sensorless `class_last=chandelier`
records migrate to uplight. A future sensorless chandelier is valid only with its
exact-MAC-rostered persistent `O4` / `class_ovr=4`; `O0` clears that assignment.
BMP581 remains non-classifying.

The complete native fixture suite passed, including 50 class-probe checks. A
guarded field-profile ESP32-S3 PowerFeather build passed with Arduino-ESP32 3.3.7,
using 1,207,517 bytes of program storage and producing a 1,207,808-byte `dev-local`
binary with SHA-256
`7e30b9e8a2688e38f3f680cc3acc91d0c949c78735b8900e3840bb479595d74f`.
That binary is compile evidence only. No revised firmware was flashed: the dirty
worktree must first become a clean commit and immutable ADR 0040 artifact. Next is
an exact Donkey canary, then exact-MAC promotion to the affected uplight cohort;
future chandelier installation is blocked on its MAC/override roster audit.

## 2026-08-28 -- Ben + Codex -- Ponyta dark-night cause and PROTECT release

Onboarded from the repository and diagnosed the PowerFeather that Ben found
dark overnight after a 3.22 V voltmeter reading. A timestamped Windows USB
watcher caught its short wake as exact outer-ring downlight Ponyta `F2B7DC` /
`68:EE:8F:F2:B7:DC` on COM10. The first 11.6-second enumeration was the
fixture's protected field wake, not a failed cable or ROM-downloader problem.
No image was built, selected, flashed, or erased.

Read-only telemetry on `fx-260827-1254f04-p` proved the immediate cause of
darkness: durable guard stage 4 / power tier 3 PROTECT with the LED rail off.
The retained entry audit records PROTECT at 3.236 V while `profile=0`
(commission); Ponyta has since been corrected to field, but a profile change
does not clear the safety latch. This supports the known commission-energy /
low-voltage chain, although the trace does not preserve the minimum loaded
voltage or distinguish a direct voltage transition from a load-armed reset.
The current live configuration also reports 6,000 mAh even though the registry
records this large-enclosure downlight as 15,000 mAh. Ben subsequently confirmed
that every canopy/downlight without exception has a 15 Ah cell, making this a
proven persisted-capacity configuration error.

With USB held continuously, charging enabled after the normal guard and stayed
near +192 to +260 mA at 3.25-3.27 V from a good 4.65-4.78 V input. The BQ
reported no fault and the configured 300 mA precharge read back correctly.
After 60 seconds of qualified charging, firmware released PROTECT to
LEDS_OFF, persisted guard stage 3, and performed its intentional clean software
reboot. MSA311, TMF8820, and BMP581 then initialized and sampled cleanly. The
fixture remains intentionally dark in the intermediate LEDS_OFF tier and needs
continued charging before a nighttime readiness test. Only read-only `t`
queries were sent; the recovery state transition and clean reboot were the
firmware's automatic guarded behavior.

## 2026-08-28 -- Ben + Codex -- Donkey exact current USB flash; MSA still absent

Ben requested the newest accepted production fixture firmware on the red
trunk/uplight. Codex declared this laptop/session the sole firmware and
configuration writer, and exact target Donkey `F2BE10` /
`68:EE:8F:F2:BE:10` on COM8. The dirty worktree was not built. Preflight selected
retained immutable artifact `fx-260828-658b7d2-p` from its manifest and accepted
promotion record, not by mtime: 1,208,640 bytes, source commit `91663fd`, SHA-256
`95de59286831bcbb9d8f610f84b09e3ac761be558f106b10b9aee8dfb01bd8cc`.
Manifest, recipe, embedded revision, local binary digest, FQBN, and Arduino CLI
1.5.1 matched.

Fresh target preflight proved the old `fx-260816-prtrel1-b` application, exact
MAC, 3.341 V battery, +221 mA charging from good USB, no BQ fault, FULL power
tier, and guard stage 1. Direct `arduino-cli upload` reused the retained build
directory and wrote only COM8; esptool identified exact `F2BE10`, verified every
bootloader/partition/application region hash, and reset normally. No build,
OTA, profile/class command, manual NVS mutation, or second target was involved.

Continuous read-only post-flash telemetry at 24.9 through 54.8 seconds proved
exact `fx-260828-658b7d2-p`, field profile, channel 11, app0, no pending verify,
3.343-3.346 V battery, about +254 to +284 mA charging, no BQ fault, configured
300 mA precharge, FULL tier, guard stage 1, and live ESP-NOW. The current image
still reports `sensor_bits=0`, `msa311_present=false`, and chandelier class.
This rules out the old firmware as the MSA detection cause. The flash passed,
but the uplight commissioning gate did not; no completion salute was sent and
the fixture is not installation-ready until the external STEMMA data path or
module is repaired.

## 2026-08-27 -- Ben + Codex -- Donkey replacement MSA and cable still do not ACK

Ben replaced Donkey `F2BE10`'s already-new MSA311 STEMMA cable and reconnected
the fixture. Fresh normal application telemetry on COM8 showed a fully healthy
power posture (guard stage 1, tier FULL, shared 3V3 rail on, good USB, no BQ
fault), but the boot's verified VSQT off/on cycle again reported
`tmf8820=0 vl53l5cx=0 bmp581=0 msa311=0` and classified chandelier. The charger
and gauge continue to communicate on internal Wire1, so the MCU/bus is not
generally dead. With a replacement sensor and cable still receiving power but
no ACK at `0x62`, next isolate the external PowerFeather STEMMA connector/data
contacts against one complete known-good MSA-plus-cable assembly; a new part is
not yet a proven-good A/B reference. No device mutation was sent.

## 2026-08-27 -- Ben + Codex -- Donkey MSA powered but absent on Wire1

Ben observed the MSA311 breakout's power LED lit on recovered Donkey `F2BE10`.
A fresh read at 181.9 seconds uptime simultaneously proved the fixture fully
recovered to power tier 0 / guard stage 1 with the shared 3V3 LED rail on, while
`msa311_present=false` remained. The firmware's probe addresses the MSA311 at
its default `0x62` on Wire1 at the required 100 kHz; the earlier verified VSQT
off/on cycle also received no acknowledgement. Powered-but-absent therefore
narrows the fault to the STEMMA cable/connectors' SDA/SCL path, an unusual
module/address mismatch, or the MSA board itself. No I2C scan command exists in
this older image, and no device mutation was sent.

## 2026-08-27 -- Ben + Codex -- Donkey new-battery PROTECT release; MSA still absent

Ben installed a new battery in Donkey `F2BE10`, left USB connected, and pressed
normal RESET. The application enumerated on COM8 immediately, so ROM bootloader
mode was unnecessary. One continuous DTR/RTS-low, read-only telemetry session
observed the old `fx-260816-prtrel1-b` recovery path without using bare-board
`X`, forcing the LED rail, entering maintenance, or changing configuration.

The new cell was recognized at 3.30-3.32 V / reported 51 percent. After the
normal six-second guard, charging enabled and held about +254 to +265 mA from
roughly 286-296 mA good USB input with no BQ fault. The qualified recovery then
released PROTECT automatically, persisted guard stage 3 / LEDS_OFF, and made a
clean software reboot. Post-reboot charging remained healthy; the LED rail
correctly stayed off in the intermediate power tier. LED smoke acceptance and
current-artifact promotion remain open.

The same reboot performed a verified VSQT off/on recovery cycle and then probed
`tmf8820=0 vl53l5cx=0 bmp581=0 msa311=0`. Repository history contains only the
original sensorless August 16 bare-board commissioning for this MAC, also
classified as chandelier; no retained evidence ever shows an MSA311. The
`uplight` label is a later registry allocation, not a previously proven runtime
class. Inspect/install the MSA311 and its STEMMA cable before treating this as an
accepted trunk light.

## 2026-08-27 -- Ben + Codex -- Archived one-off USB perimeter gobo controller

Retained a dependency-free Windows Forms stopgap for field-testing one perimeter
gobo without Starlink or the T-Deck under
`ops/bench/archive/perimeter_gobo_usb/`. The local launcher automatically
selects the sole COM port, opens native USB CDC with DTR/RTS low, and requires
fresh read-only `t` telemetry proving an exact healthy perimeter fixture before
enabling Start.

Start sends the existing RAM-only `L1` command, whose production renderer walks
one white pixel through the HEX spiral. Stop sends `L0` and explicitly explains
that the boot remains forced dark. Return to Normal sends `L0`, waits for the
rail-off path, and applies the documented 150 ms USB RTS reset pulse so normal
field behavior resumes. The app refuses non-perimeter, deep-recovery,
uninitialized, PROTECT, and LED-OFF targets; fixture-side power/boot/ramp gates
remain authoritative. No firmware, WiFi, OTA, profile, lifecycle, or NVS change
is performed. The code and its self-test are preserved for posterity, but the
installed USB-extension/reset path was never hardware-validated, so this is not
advertised as a supported production workflow.

## 2026-08-27 -- Ben + Codex -- Donkey uplight dark in pre-ADR-0051 PROTECT

Onboarded from the repository and diagnosed the USB-connected trunk/uplight as
Donkey `F2BE10` / `68:EE:8F:F2:BE:10` on COM8. The port was opened with DTR/RTS
low and only the read-only `t` telemetry query was sent; native USB CDC produced
one boot, but no firmware, profile, class, lifecycle, maintenance, rail, NVS, or
other device mutation was requested.

The immediate reason for darkness is authoritative: old artifact
`fx-260816-prtrel1-b` booted with persisted guard stage 4 (`stored=4`, `park=1`),
power tier 3, and the physical LED rail off. USB itself was healthy at 4.760 V /
70 mA with `supply_good=true` and no BQ fault. The BAT node read 2.345 V at about
+2.2 mA, but firmware judged the battery absent/implausible and kept charging
off. Because this artifact predates ADR 0051, its history matches the known
floating-BAT failure mode that could durably latch PROTECT on an empty board;
an actually installed but disconnected or severely depleted cell cannot be
excluded without physical inspection.

Registry history confirms `F2BE10` was OTA-bootstrapped bare and later allocated
to the 6 Ah trunk-light pool. Live auto-probe saw no MSA311 or other STEMMA
sensor, so it classified as `chandelier`, not `uplight`. Check the battery and
MSA311 connections before choosing the battery-absent guarded-clear path versus
the installed-battery recovery lane. The LED module/data wiring remains untested
because firmware never energized the rail.

## 2026-08-27 -- Ben + Codex -- Dual-site WiFi artifact and split-fleet rollout

Ben confirmed that camp and art-site Starlinks must retain distinct network
credentials. ADR 0066 replaces the queued one-virtual-SSID requirement for
fixture maintenance: the image may carry two gitignored credential profiles,
scan once, prefer visible known APs by RSSI, fall back in declaration order,
and share one bounded 30-second join budget. Ordinary COMMS remains ESP-NOW
only. Serial output, recipes, manifests, and git use profile labels rather than
credential values. Added the pure planner plus ten native checks, optional
second-pair compile guards, example placeholders, and firmware documentation.
The full fixture native suite and production ESP32-S3 build passed.

Clean source commit `91663fd0688f6fa903d1086fb023337a372ff179`
produced immutable artifact `fx-260828-658b7d2-p`, 1,208,640 bytes, SHA-256
`95de59286831bcbb9d8f610f84b09e3ac761be558f106b10b9aee8dfb01bd8cc`.
Its recipe label is non-secret. Swablu `F2BE70` passed the exact-target canary:
upload ACK, software-reset mesh rejoin on the exact revision, survival past the
25-second pending-verify gate, and FIELD profile. The first configured network
then carried the wider rollout. The second site profile is compiled into the
same image but still needs one explicit art-site hardware association check.

The final read-only census before releasing T-Deck `8EB508` reported 98 of the
110 intended fixtures on the exact new artifact and 12 on the prior known-good
`fx-260827-1254f04-p`. Every one of the 98 has fresh exact-revision and
pending-window proof; every verified profile was FIELD. No lingering commission
mode was found among the promoted cohort. The 12 intended holdouts are Rikku
`9F26B0`, Groot `9F2724`, Ponyta `F2B7DC`, Cammy `F2B900`, Spyro `F2BCF0`,
Gambit `F2BCF4`, Batman `F2BDC4`, Gengar `F2BDD4`, Toad `F2BEE4`, Daisy
`F40308`, Dratini `F4035C`, and Sneasel `F403DC`. No accepted or ambiguous
upload was automatically retried.

The field crew departed mid-rollout with all 24 physical perimeter fixtures.
The working historical/live perimeter reconstruction shows 13 already
contract-verified on the new image. The art-site USB queue is Cammy `F2B900`,
Spyro `F2BCF0`, Gambit `F2BCF4`, Batman `F2BDC4`, Gengar `F2BDD4`, uncalled
`F2BE80`, Clank `F2BF60`, uncalled `F2BFEC`, Thor `F40344`, Dratini `F4035C`,
and Sneasel `F403DC`. The physical slot-to-MAC map remains incomplete, so read
the identity over USB before writing rather than trusting box position alone.
Clank remains the known unsafe/commission exception and needs supervised power
recovery, not a casual OTA.

The six-way uploader again delivered the predicted transfer speed: the final
20- and 21-target ordinary camp waves each found every target and completed all
41 full upload-plus-verification contracts in 176 and 225 seconds. The overall
campaign did not approach ADR 0062's roughly ten-minute target. A 101-target
roster received only 93 bridge add acknowledgements and failed closed before
discovery; splitting fixed that control-plane loss. A later 53-target wave
found all peers but eight maintenance endpoints vanished before the fresh-power
preflight, so it also failed closed without uploads. The 48-target recovery
wave passed, and an exact nine-target recovery passed eight; Cammy's HTTP peer
closed without an ACK and its mesh revision remained old, so it was held.

Movement of the perimeter load then made three discovered endpoints disappear
before preflight and correctly produced no upload. A separate five-target
PROTECT job found only Rikku during the complete sparse cadence. Its automatic
freeze hit one transient dashboard HTTP 500; the finalizer also missed the
acknowledgement, and a manual exact-job freeze then cleared the bridge before
any upload. One final no-write Rikku attempt expired in bridge phase 3 without
discovery. Follow-up tooling should retry a transient freeze transport error,
accept a fresh stopped/expired phase as safe cleanup evidence, demote vanished
partial-discovery endpoints instead of failing the whole selected wave, and
make large roster add acknowledgement robust. All maintenance campaigns were
inactive, all OTA/dashboard processes were stopped, and COM7 was opened and
released successfully before Ben unplugged the T-Deck.
## 2026-08-27 -- Ben + Codex -- TSwift shell color and copy polish

Ben's physical review accepted the permanent shell and found three small
legibility issues: the `P` in Stop was clipped, app identity blended into the
scrolling ribbon, and the idle text alternated between ambiguous phrases such
as `join ch11 mesh` and the redundant `mesh ch11 mesh`. Widened Stop from 62 to
66 pixels and reduced its internal padding. App identity now uses a blue accent,
the ribbon retains its primary text color, and the independent clock uses cyan.
The idle ticker now spells out `WiFi`, `WiFi joining`, `mesh-only`, or `GUARD`,
followed by separated `ch11`, `live N/M`, and `bat N%` fields. Here `live N/M`
means fresh fixtures now / distinct fixtures seen since this T-Deck booted.

The complete native suite and build-wrapper contract passed. The locked build
produced a 1,565,280-byte binary with SHA-256
`3267a1b237a2a4708e5c999cf1730f497ecbc30bd80e299a8b76374764931d4c`;
the linker reports 49 percent flash and 59 percent global RAM. Esptool flashed
and verified only TSwift `979604` / `44:1B:F6:97:96:04` on COM157. Read-only
post-reset evidence reported `tdeck-dev-local`, channel 11, 19/19 mesh sends
with zero failures, valid local GPS time, and healthy PSRAM, keyboard, touch,
ES7210, GPS, heap, and PSRAM probes. No fixture command or mutation was sent.

## 2026-08-27 -- Ben + Codex -- TSwift promoted to permanent Bridge OS shell bar

Ben accepted the compact activity ribbon as a useful control signal but asked
to replace the overlay with real shell chrome. Bridge OS now permanently owns
the top 26 pixels on every LVGL screen. The left cell carries app identity, the
center carries idle app/network status or a scrolling activity ribbon, and a
fixed right-side clock and Stop button appear while this T-Deck owns a stream
or tracked program lease. Keeping the changing clock out of the text prevents
it from restarting the scroll each second. Permanent streams say
`LOCAL ... until STOP` and count up; expiring program leases count down. Fresh
non-self T-Deck, PUCA, CoreS3, or
unknown publishers remain passive warnings, and local-plus-foreign overlap is
red.

Removed duplicated per-screen title/status objects and migrated the launcher
plus all 13 implemented apps to the y>=26 content contract. LED Studio's class
picker and swatches and Wildfire CA's dense controls were explicitly reflowed;
Fleet and Health moved their former top-right controls to bottom action rows.
The bar never appears or disappears, so starting or stopping activity cannot
shift app content or cover a title, picker, or action button. Fleet detail
charger labels and Fleet View charger-phase filters remain included; Health's
existing VBAT/CHG toggle remains unchanged in behavior.

The complete native Bridge OS suite and build-wrapper contract passed. The
locked development build produced a 1,565,056-byte binary with SHA-256
`fcb0c499e749474e5c49128dcdc6245b613298a89e7b189cde7f0d80f2fc9810`;
the linker reports 49 percent flash and 59 percent global RAM. Esptool flashed
and verified only camp-labelled TSwift `979604` / `44:1B:F6:97:96:04` on
COM157. Read-only post-reset checks passed PSRAM, keyboard, touch, ES7210, and
GPS probes and reported `tdeck-dev-local`, channel 11, 15 live / 19 seen peers,
and active mesh/time publication. No fixture command, OTA, profile/lifecycle
change, reboot request, or NVS mutation was sent. Cross-app touch and conflict
behavior remains for Ben's physical visual acceptance.

## 2026-08-27 -- Ben + Codex -- TSwift banner moved off app action rows

Physical acceptance immediately rejected the first persistent-banner layout:
after LED Studio Green, its full-width bottom strip covered the app's
Solid/Stop/Back controls. Auditing every Bridge OS screen confirmed the bottom
row is universally operational and the top-right also contains controls in
several apps. The common safe region is the top-left title/status area before
the nearest interactive control at x=130.

Replaced the bottom strip with a 122x26 top-left control pill. For local
activity the entire pill is Stop, with stream mode plus explicit `n=` target
count or program countdown in a scrolling label. Foreign-only status is still
informational/non-clickable, and local-plus-foreign conflict remains red. The
pill occupies x=2..124 and y=0..26, leaving LED Studio's x=130 class selector
and y=200 Solid/Stop/Back row untouched.

The full native suite passed. The locked warm build produced a 1,586,544-byte
binary with SHA-256
`aaf2b9ae2a0d111ca69def7a04bee52af0d03cab999f12308338c4cef6335b64`;
the linker reports 50 percent flash and 59 percent global RAM. Esptool flashed
only exact TSwift `979604` / `44:1B:F6:97:96:04` on COM157 and verified every
region. Post-reset serial reported `tdeck-dev-local`, channel 11, live fleet
receive, 14/14 sends with zero failures, and healthy heap/PSRAM. No serial
command or fixture mutation was sent. COM157 was closed for the operator's
immediate LED Studio recheck.

## 2026-08-27 -- Ben + Codex -- Banner build flashed to camp-labelled TSwift

Recorded the camp label `TSwift` for the second LCD T-Deck Plus, exact MAC
`44:1B:F6:97:96:04`, short ID `979604`. USB enumeration independently exposed
that full MAC on COM157; the only remaining dashboard process owned primary
T-Deck COM152, so the exact upload target was unambiguous and free.

Rebuilt through the healthy locked development cache and USB-flashed only
TSwift with the banner and Fleet charge-filter image. The application is
1,586,688 bytes with SHA-256
`f97af709e6ea6bf234d323c53366384880c5fa734ee4a8203ac12bbe32ae45f3`;
esptool identified the same full MAC and verified every written region.

Post-reset serial reported `fw=tdeck-dev-local`, ID `979604`, channel 11, live
mesh receive, 19/19 successful sends with zero failures, roughly 7.7 MB free
PSRAM, and a valid local GPS time source. The local `probe` check passed 8 MB
PSRAM, keyboard, GT911 touch, GPS at 38400 baud, and ES7210 at 0x40. Only local
read-only `help` and `probe` commands were entered; no fixture command, OTA,
profile/lifecycle change, reboot request, or NVS mutation was sent. The monitor
was closed cleanly. Banner touch/expiry/conflict behavior and Fleet charge
filter canaries remain queued for physical acceptance.

## 2026-08-27 -- Ben + Codex -- Global control banner and charge filters built only

Added a shell-level T-Deck control activity banner that stays on LVGL's top
layer across apps. Local direct streams remain labelled `until STOP`; local
program leases show a countdown, and one touch stops the stream and releases
the tracked program without returning to its originating app. The passive side
uses the existing packet header and lease fields to identify fresh non-self
T-Deck, PUCA, CoreS3, or unknown controller activity by exact short ID. It adds
no wire format, discovery packet, or polling traffic.

Kept the already-present Health VBAT/CHG toggle unchanged. Existing Fleet detail
charger decoding now uses the operator labels `CHARGING_CC`, `CHARGING_CV`,
`TOP-OFF`, `DONE/OFF`, and `FAULT`; Fleet View adds filters for those phases plus
unknown and off air. The generated Health roster was reconciled with the
pre-existing local Bidoof registry update (6 Ah, downlight) so its source digest
contract remains exact.

The complete native Bridge OS suite passes, including new publisher freshness,
self-suppression, program lease/release/expiry, and charger-filter tests. A
locked no-upload development build completed at 1,586,688 bytes with SHA-256
`f97af709e6ea6bf234d323c53366384880c5fa734ee4a8203ac12bbe32ae45f3`;
the linker reports 50 percent flash and 59 percent global RAM. Because the build
laptop was issuing a fleet OTA, this session deliberately opened no serial port,
flashed no T-Deck, and sent no mesh, OTA, profile, lifecycle, reboot, or NVS
command. Hardware acceptance remains queued until the OTA writer is finished.

## 2026-08-27 -- Ben + Codex -- Second T-Deck Plus updated from origin

Fast-forwarded the working branch from `ec5e6c6` to current `origin/main`
`027f725a44d57c86a170d4ffba4d9817d1724aec`, preserving the existing local
LOG, TODO, registry, USB-rescue, and camera work. The two append-heavy journal
conflicts were reconciled by retaining the newer upstream record together with
the later local camera and Bidoof updates.

Positively identified the connected old handheld as LCD T-Deck Plus
`44:1B:F6:97:96:04` / short ID `979604` on COM157. It was running
`tdeck-0.1.0`; preflight showed healthy 8 MB PSRAM, keyboard, GT911 touch,
ES7210 at 0x40, GPS at 38400 baud, channel-11 mesh traffic, and retained local
credentials. No fixture or PUCA serial device was present on the selected
port.

The complete native Bridge OS suite and build-wrapper contract passed. Built
current source through the healthy locked warm cache and USB-flashed only
`979604`. The 1,583,456-byte `tdeck-dev-local` binary has SHA-256
`12d43afdf80d483e3340ddf66b554d8878d13a71586917b40c4ad3fe0405d80c`;
esptool verified every written region. Post-reset serial confirmed the same
identity, retained SSID/API/model/channel/day-mode settings, healthy onboard
peripherals, live mesh receive, 19/19 sends with zero failures, and firmware
`tdeck-dev-local`. No fixture command, OTA, profile/channel persistence, or
fixture NVS mutation was sent.

## 2026-08-27 -- Ben + Codex -- Current-source fleet OTA promotion and timing

Codex was the sole writer through exact T-Deck `8EB508` on COM7. Source commit
`d6c923427b6dc0b27ed3d054b457856c084dc0c1` was clean. The T-Deck native suite
passed and its warm-cache `tdeck-dev-local` image was flashed and boot-checked;
the 1,583,456-byte binary has SHA-256
`d22712f7f383968645cb4c381b7ad6abb17257a4c34d16bf9519a1578b8e2b06`.
This folds in the Fleet VBAT/signed-current row, human-readable detail states,
firmware/program filters, DAY/NITE UI, Health VBAT/charge swatch toggle and
clipped legend, charge-state detail, and ADR 0065 best-effort operator knocks.

Built one fresh immutable production fixture artifact from that same commit:
`fx-260827-1254f04-p`, 1,207,376 bytes, SHA-256
`2f9a93344e172b023ee8df473b7c747b26f38dc0ec5353f6efd00d50ec45f4af`.
The full native fixture suite, release build, embedded revision, canonical
recipe, manifest, build options, credential semantics, and clean-source checks
passed. Hawkeye `9F2664` then passed exact-target canary job `F774B62C`: upload
ACK, fresh software-reset mesh rejoin, exact revision beyond the 25-second
pending-verify gate, and FIELD profile, in 53.844 seconds.

The promoted rollout named 103 ordinary-cadence fixtures and a separate six-ID
PROTECT cohort. All 109 post-canary targets accepted the exact binary without an
automatic retry; together with Hawkeye, the final dashboard roster reports all
110 intended fixtures on `fx-260827-1254f04-p` and all 110 in FIELD profile.
The only observed commission fixture is Clank `F2BF60`, which was deliberately
excluded at 0.94 V. Also excluded were protected development canary Akuma
`9E668C`, targeted-maintenance exception Bidoof `9F26D8`, unsafe Tidus `F40424`,
uncommissioned `F402A8`, and off-air protected Magic Wand `F40344`.

The strict ADR 0040 completion ledger accepted 107/110 targets. Gambit
`F2BCF4`, Kabuto `F2BEE4`, and Zubat `F2B7DC` now report the exact new revision,
but their upload jobs did not observe a sufficiently fresh post-upload heartbeat
through the pending-verify contract. No accepted upload was retried. F2BEE4
entered at 3.063 V and returned to PROTECT; F2B7DC entered at 3.227 V with weak
input and later exposed exact-revision 32.096-second uptime, but the cached row
was already outside the verifier's freshness window. Treat these three as
installed-but-unproven until a later fresh exact-revision wake is recorded.

Measured from the first 103-target ordinary job at 22:16:47Z through PROTECT
cleanup at 23:01:56Z, the field rollout took 45 minutes 9 seconds rather than
the predicted roughly 10 minutes. The first ordinary job itself took 9 minutes
49.5 seconds, but sparse maintenance association found only 54/103 endpoints
and verified 53. Across the six post-canary upload waves, all 109 HTTP uploads
ACKed; their upload windows totaled 5 minutes 11 seconds, with per-fixture ACKs
10.43-29.22 seconds (median 14.41 seconds). The new six-way uploader was thus
faster than the runbook's predicted 7-9-minute upload component. Repeated
150-second discovery windows, one fail-closed cohort where a found endpoint
vanished before fresh maintenance preflight, and full verifier timeouts on
sleeping holdouts consumed the speedup.

The state machine's safety behavior held: explicit rosters, complete 1.3-second
maintenance cycles, acknowledged FREEZE before uploads, safe deferral of missing
targets, no duplicate write after upload ACK, exact-revision/pending-window
checks, automatic endpoint resume, and exclusive job ledgers. Follow up by
making partial discovery survive a later endpoint loss, aligning the 5-second
verification freshness threshold with the T-Deck's 10-second full-census serial
cadence (or forwarding proof immediately), and carrying verification across a
full PROTECT wake without weakening ADR 0040.

## 2026-08-27 -- Ben + Codex -- Operator knocks bypass energy qualification

Ben clarified the sparse Knocker result: the control plane should request a
knock from every receiver that hears it. An empty capacitor yielding weak or no
motion is acceptable; DAY_ACTIVE, >=150 mA solar input, and FULL tier must not
pre-filter a deliberate operator request. ADR 0065 supersedes the operator-
strike portions of ADR 0030/0038/0041/0060 while retaining their energy policy for
autonomous program-generated knocks.

Added a pure strike-origin policy and routed exact-target and deduplicated fleet
radio events through the operator path. Received operator traffic now reaches
`solenoidStrike()` regardless of lifecycle, solar, supply-good, or tier. The
persisted arm, rest interval, pulse clamp, D7 collision check, durable load-
armed marker, timer/failsafe, maintenance exclusion, event dedupe, one-pending
bound, and late-drop remain. Native CA/choreography still calls the autonomous
path and retains the renewable/power gate. T-Deck and agent wording now says
attempt/mechanism gate rather than promising a physical impact.

Also fixed the Health page key reported below the physical display: caption and
legend are explicit 310 x 17 pixel clipped rows inside the 320 x 240 viewport,
and both VBAT/CHG legends are shortened to one line.

The complete fixture and T-Deck native suites pass, including the new four-case
strike-origin regression. A production-conditional field fixture development
build passed at 1,207,049 bytes (36 percent) flash and 68,692 bytes (20 percent)
RAM; its 1,207,344-byte `dev-local` binary has SHA-256
`d81285ed81931f5ca3feed4ba36a5038d1e6a1b240abf4d0dcd874886f384f1a`.
The T-Deck development build passed at 1,583,307 bytes (50 percent) flash and
194,856 bytes (59 percent) RAM; its 1,583,456-byte binary has SHA-256
`d22712f7f383968645cb4c381b7ad6abb17257a4c34d16bf9519a1578b8e2b06`.
Neither development image was flashed or OTA-deployed.

## 2026-08-27 -- Ben + Codex -- Sparse Knocker roll is not the live count

Ben observed 92 live fixtures but only sparse audible results from a Knocker
targeted roll. A subsequent read-only 22-second T-Deck serial census captured
106 unique peers, 83 of them under the app's 5-second freshness threshold. Of
the fresh rows whose full lifecycle fields were available, 18 reported
DAY_CHARGE, four reported DAY_ACTIVE, and one reported COMMISSION. Only four
had affirmative FIELD + DAY_ACTIVE + FULL + good input >=150 mA evidence:
`9E5B44`, `9F2664`, `9F266C`, and `F401CC`. Sixty fresh serial rows lacked the
full lifecycle/firmware tail, so they could not be counted as strike-ready.
No fixture command was sent during this diagnosis.

Knocker currently equates `fresh` with rollout membership. It snapshots every
real ID heard within five seconds, regardless of class, full-state evidence,
DAY_ACTIVE, tier, solar input, or physical mallet presence. A 92-target roll at
80 ms per target takes about 7.36 seconds, so an ordinary short-wake peer may
already be asleep when its sorted turn arrives even though it was `live` when
the modal opened. Every receiver then independently refuses a field strike
unless it is DAY_ACTIVE with >=150 mA input and FULL tier; a fixture without
physical mallet hardware is silent regardless. The displayed live count is
therefore send fanout, not expected audible knocks. Add explicit fresh,
mallet-class, state-known, and strike-ready counts/filtering; retain the
multicast modes for the updated fleet when simultaneous awake-peer delivery is
desired.

## 2026-08-27 -- Ben + Codex -- Hawkeye passed ADR 0064 OTA canary

Declared exact T-Deck `8EB508` as the sole writer and exact fixture `9F2664`
(Hawkeye) as the only target. Fresh preflight showed the battery-backed field
fixture on `fx-260826-51d1fe1-p`, 3.571 V battery, +317 mA battery current,
6.137 V / 244 mA input, FIELD profile, DAY_ACTIVE lifecycle, FULL tier, DARK
program, and no protect latch. OTA job `192D6A8B` used retained artifact
`fx-260827-db0cb73-p`, source `8c0e577ed05b32453aeeefa239819920551e7a6d`,
and binary SHA-256
`e30c42802f34966ca5c959539d20bf9c737786c935dc81c3934a3ff638386b5c`.
No other fixture was targeted.

The shared-WiFi maintenance endpoint was found at `192.168.1.254`, fresh
maintenance power preflight passed at 3.570 V battery and 6.026 V / 264 mA
input, and the 1,207,408-byte upload returned its reboot ACK. The host then saw
the exact new revision at 8.649 s uptime and did not accept the canary until a
fresh software-reset heartbeat at 28.521 s uptime had survived the 25-second
pending-verify gate. Profile audit confirmed FIELD; no commission correction or
NVS write was needed. The job completed with one verified, zero deferred, and
zero failed targets. The generated job and upload ledgers are retained under
`ops/bench/data/Nevada City/`.

Post-verify read-only telemetry reported 3.567-3.573 V, +312 to +323 mA IBAT,
6.157-6.232 V / 240-242 mA input, charge status 2 (`CHARGING_CV`), FULL tier,
and LEDs off. At 79.741 s uptime Hawkeye completed the sustained-solar probe
and returned to DAY_ACTIVE. OTA reboot cleared the prior volatile DARK lease,
so its program returned to IDLE. This proves artifact identity, power
ride-through, corrected positive-sun telemetry, solar-active transition, and
the profile audit. It does not yet prove the no-surplus 120-second sleep/wake
path because Hawkeye's input remained above the 150 mA DAY_ACTIVE threshold.
Hold fleet promotion until a low-input wake proves the validity transition and
ordinary sleep behavior.

## 2026-08-27 -- Ben + Codex -- ADR 0064 immutable fixture candidate retained

Committed the complete short-wake power-truth change as clean source
`8c0e577ed05b32453aeeefa239819920551e7a6d`, then generated the canonical
production recipe with field profile, channel 11, LFP, 300 mA precharge,
120-second day sleep, 12,000 ms listen grace, ADR 0039 basic-listener
capability, and the local `party-in-the-woods-v1` credential set. Recipe
SHA-256 is
`db0cb732abe988e6c0e8e691d5c11ccabc92cf127d99691db95fe10542838463`.

The fresh retained build completed normally with the actual production
conditional paths. Candidate `fx-260827-db0cb73-p` uses 1,207,113 bytes (36
percent) of flash and 68,692 bytes (20 percent) of RAM. Its 1,207,408-byte
`fixture.ino.bin` has SHA-256
`e30c42802f34966ca5c959539d20bf9c737786c935dc81c3934a3ff638386b5c`.
`build.options.json`, embedded identity, binary digest, immutable manifest, and
the locally installed PowerFeather SDK source-tree digest all agree. The
manifest marks this `p` artifact `candidate_canary_pending`.

No fixture was commanded, rebooted, profile-mutated, or OTA-flashed. ADR 0064
requires one explicit battery-backed field canary before widening, and ADR 0040
still requires Ben to name the exact short-MAC target roster and sole writer.
A subsequent 18-second read-only T-Deck snapshot captured 230 peer lines / 115
unique peers: 113 field, one persisted commission (`F2BF60` Clank), and one
profile-unknown (`F40424` Tidus). No correction was sent. These are the two
already-known unsafe battery exceptions (about 0.86 V and near-zero/missing,
respectively), so they remain outside ordinary OTA/profile mutation until their
battery paths are repaired or separately proven stable.

## 2026-08-27 -- Ben + Codex -- Short-wake charge truth and Health charge view built

Investigated why most idle daytime fixtures reported battery current around
zero while fixtures held awake by a dark command showed strong charge. The
initial full heartbeat is a boot announcement before lifecycle initialization;
fixture power initialization disables charging until the 6-second battery
guard. The installed 120-second sleep / 3-second listen recipe could therefore
return to deep sleep before charging was re-enabled. Independently, the
MAX17260 Current register can remain a hibernate-era sample for 5.625 seconds,
so a successful early I2C read did not prove a fresh zero. This reopens the
3-second cadence as unsafe for solar-health visibility and charge continuity.

ADR 0064 appends `power_sample_flags` as heartbeat tail 17. Old firmware current
is now explicitly unverified. New firmware trusts IBAT only after 12 seconds,
immediately sends a corrected full heartbeat on that transition, and blocks
ordinary day sleep until the sample is valid or a bounded 15-second gauge-fault
fail-open expires. A live program lease also blocks day sleep for its duration,
so a long Blackout lease cannot be lost through a timer reboot. The full wire
packet is now 193 bytes; the fixture RX buffer was raised to the ESP-NOW
250-byte limit and canonical layout tests pin the append-only offset.

Bridge OS now latches BQ state across short heartbeats, displays signed IBAT
only with the new validity proof, derives human charge phases
`CHARGING_CC`/`CHARGING_CV`/`TOP_OFF`/`NOT_CHARGING/DONE` plus disabled/fault/
unknown/off-air, and lets Health toggle its stable swatches between VBAT and
CHG. Fleet and Health detail use readable class/lifecycle/tier/program/charge
names. The launcher and apps now separate Wake Fleet, Blackout, and Deep sleep.
Wake Fleet is the former repeated dark day-baseline campaign; Blackout is the
releasable LED-off/radio-awake lease.

The OTA host now audits verified runtime profiles. With explicit
`--fix-commission-profile`, it sends persisted FIELD only to exact verified
commission targets and requires a fresh expected-revision field confirmation;
unknown evidence fails closed. Repeated RF profile copies are deduplicated in
fixture firmware so one command cannot multiply NVS writes.

Fixture native tests, the complete T-Deck native suite, and 12 OTA host tests
pass. The field-recipe fixture development build uses 1,197,161 bytes (35
percent flash) and 68,692 bytes (20 percent RAM); its 1,197,456-byte binary has
SHA-256
`129fe62ad4c831b6e7a42ec9aa30eae9a69e769bf1cf98e6a90ec6cd485d472c`.
It is `dev-local`, lacks maintenance WiFi credentials, and was not flashed to
any fixture.

The T-Deck build uses 1,583,199 bytes (50 percent flash) and 194,856 bytes (59
percent RAM). Its 1,583,344-byte binary has SHA-256
`3bc13ca8a8bfeb60aaa31d349721b3760522dc1600f3913dd145400fe1ef905c`.
Preflight read exact COM7 identity `44:1B:F6:8E:B5:08`; only T-Deck `8EB508` was
USB-flashed, esptool verified every written region, and post-reset serial showed
live `8EB508` channel-11 time traffic. No fixture command, OTA, profile write,
or reboot request was sent. Next is one clean immutable credentialed fixture
artifact and a named battery-backed short-wake canary before any exact-roster
fleet OTA.

## 2026-08-27 -- Ben + Codex -- Combined current Bridge OS flashed on 8EB508

Ben requested the new Fleet build on the primary T-Deck and asked whether it
also contained the other recent Bridge upgrades. The previously retained Fleet
binary was older than the current source tree, so it was not reused. Recorded
source digest
`f8b93cb792aee9edd7b7271f7748243f662aca4027038e2e1b2d1a00adc4adbd`
before the build and matched it afterward. The combined source includes the
persistent high-contrast DAY/NIGHT presentation and Fleet quick toggle, the
compact Fleet VBAT/signed-IBAT row, IDLE-versus-unknown state fix, readable
detail names, program/firmware rollout filters, the exact-target Default app,
and the current semantic-white planner.

The complete native T-Deck suite passed. Built and USB-flashed only exact
T-Deck `8EB508` (`44:1B:F6:8E:B5:08`) on COM7; COM6 remained the separately
identified PUCA CP2102N and was never opened. The application uses 1,581,023
bytes (50 percent) of flash and 164,888 bytes (50 percent) of global RAM. The
1,581,168-byte `tdeck-dev-local` binary has SHA-256
`c87b2805feb8bd95c0d6c9ae3022baaa40079483bca652de6c33f738c0e69e7e`.
Upload verified every written region. Three raw `read-flash` attempts stopped
after 4-44 KB with USB serial corruption at 921600, 460800, and 115200 baud;
the independent `verify-flash` operation then compared all 1,581,168
application bytes in place and passed with a matching digest.

After the verification reset, `8EB508` reported `tdeck-dev-local`, channel 11,
`display=day`, saved night backlight 59, mesh up with live receive, 14/14 sends
and zero failures, healthy 8 MB PSRAM/keyboard/touch/ES7210/GPS probes, about
68.7 KB free heap, and about 7.72 MB free PSRAM. Only local read-only
`show`/`probe`/`mem` and emitter on/off diagnostics were used; no fixture
command, profile change, reboot request, OTA request, or NVS mutation was sent.
Physical checks of the new Fleet layout/filter scrolling and Default/semantic-
white behavior remain in TODO.

## 2026-08-27 -- Ben + Codex -- PUCA safe bootstrap and exact-target OTA accepted

Onboarded from and fast-forwarded to `origin/main` at `ec5e6c6`, preserving the
existing uncommitted Bridge and PUCA work through a named safety stash. Reviewed
the incoming T-Deck cache-schema-2 optimization: Arduino owns only
`build/dev-cache`, wrapper recipe/interruption state now lives in sibling
`dev-cache.state`, and the compile-free build-wrapper contract passed locally.
No T-Deck rebuild or flash was required for this acceptance run.

Built the credentialed PUCA Original Edition `puca-bridge-0.5.0-dev` bootstrap
with the explicit 4 MB default dual-app partition layout. The retained
application is 1,024,128 bytes, SHA-256
`1e90f6f1731a622b11274fa91abbc6eeebb17c35abe90bd86337c915cb99e8da`.
The received CP2102N automatic-reset circuit repeatedly booted normally instead
of entering the ROM downloader. The visible onboard button proved to be GPIO36,
not BOOT. With stable Pod20/USB power, holding the accessible `RST` header pin to
`GND`, asserting DTR/download, releasing `RST`, and using esptool
`--before no_reset` entered ROM download; all four flash regions completed hash
verification. A normal jumper was used -- never an ammeter-mode meter or a
short to `VIN`/`VDD`.

Fourteen consecutive post-bootstrap samples reported DJ selected but
`active=0`, `bootarmed=0`, controls locked, healthy codec, and `frames=0`; only
the intended PUCA heartbeat counter advanced. Primary Bridge OS `8EB508` saw
fresh channel-11 `A4EB10` heartbeats with exact revision
`puca-bridge-0.5.0-dev`.

The host then sent only exact command `UA4EB10`. PUCA joined shared maintenance
WiFi, exposed identity-matching telemetry, accepted the exact retained
1,024,128-byte image, rebooted with software reset, rejoined the Bridge with
reset uptime/sequence, and survived the 25 s pending-verify gate. A later
ordinary USB-induced reset again reported SAFE-IDLE, locked controls, codec
ready, and zero direct frames. The OTA result is in
`ops/bench/data/ca/2026-08-27-ota-results.jsonl`. Routine enclosed OTA is now
accepted; paw-held DJ/setup controls, `/resume`/timeout, broadcast rejection,
softAP absence, forced rollback, and visible audio/light acceptance remain open.
## 2026-08-27 -- Ben + Codex -- Local Windows Arducam viewer added

Added `ops/camera/`, a dependency-free localhost USB UVC viewer launched as a
Microsoft Edge app window. It prefers an Arducam/USB Camera source, requests
320x240 through 1920x1080 modes, reports the accepted mode, saves PNG snapshots
and WebM recordings, supports mirror/fullscreen shortcuts, and exposes the
camera controls Windows publishes to Chromium. A guarded launcher reuses one
hidden localhost server; a companion script stops only its recorded matching
process. Video stays local.

The attached device enumerated as USB camera `0C45:6366` with video and audio
interfaces. LilyGO's T-Deck schematic confirms that its ESP32-S3 USB data pins
are present but the Type-C port has sink/device CC pull-downs, VBUS input, and
no host 5 V source. The future T-Deck path is therefore a channel-11 WiFi
320x240 JPEG/MJPEG viewer fed by a laptop or Pi, not a passive OTG cable.

The likely Arducam B0205/B0506 day/night family is designed to leave its IR LED
boards connected: a photoresistor automatically switches the 850 nm LEDs and
mechanical IR-cut filter. Disconnect them, with USB power removed first, only
for visible-only dim-room tests, reflection troubleshooting, or reduced power.
HTML JavaScript, PowerShell launcher/stop parsing, ASCII, diff checks, localhost
serving, and the complete no-permission UI passed. The Edge app is open; final
live-video acceptance awaits the one-time user camera-permission click.

## 2026-08-27 -- Ben + Codex -- Bidoof USB rescue and A/B verification completed

Declared the single state-changing target as Bidoof `9F26D8` on COM156 and
used immutable production artifact `fx-260826-51d1fe1-p` from clean commit
`64264b2c60cbff9a9423642cb6cfee93e4272636`. Its 1,206,784-byte binary freshly
matched manifest SHA-256
`57306019dbf93a1d0cf950f25b9f557d9a0a68663621a7ce4579aba01dea1261`.
No competing flash or OTA process was active.

The generic Arduino uploader failed closed before any write because this
archived artifact retains the application binary but not the companion
bootloader/partition binaries expected by the full-image upload recipe. Bidoof
remained on the old image with uninterrupted uptime and guard stage FULL. The
documented ESP32 application-only path then wrote only the existing app0 address
`0x10000`; esptool positively identified full MAC `D8:85:AC:9F:26:D8`, wrote
1,206,784 bytes, and verified the on-device data hash. The partition table and
NVS were preserved.

The production boot reported the exact revision, healthy field profile, channel
11, good input/charge, downlight class, and healthy MSA311/TMF8820. An explicit
serial `F1` persisted field profile. Local maintenance then joined
`Party In The Woods`, exposed exact identity at `192.168.1.75`, and accepted the
same immutable binary into app1. Fresh serial evidence showed `pending_verify`
at 12.9 and 17.0 seconds, followed by the 20-second network self-test PASS,
`ota_state=valid` at 21.0 seconds, and continued exact-revision stability through
93.9 seconds. Final telemetry was VBAT 3.451 V / +673 mA, qualified 4.637 V input,
no BQ fault, field/DAY_ACTIVE, channel-11 ESP-NOW 114/0 sends, guard FULL, and
healthy MSA311/TMF8820.

The original no-endpoint failure is closed: Bidoof now has working maintenance
WiFi and a validated production image. A T-Deck-targeted maintenance command
could not be rechecked because its COM152 bridge was physically absent; the
dashboard correctly reported disconnected. That one test remains useful only to
exclude a secondary ESP-NOW receive fault. Evidence is in
`ops/bench/data/usb/2026-08-27-bidoof-usb-rescue.jsonl`.

## 2026-08-27 -- Ben + Codex -- Bidoof USB diagnosis found WiFi-less same-version image

The newly attached Espressif native-USB device on COM156 positively identified
as Bidoof `9F26D8` / `D8:85:AC:9F:26:D8`. Read-only serial telemetry showed old
`fx-260816-otafix1-b` on app0 with pending verify false, persisted commission
profile, channel 11, guard stage FULL, and healthy PowerFeather, battery, charger,
radio uplink, LED rail, MSA311, and TMF8820. Settled samples measured about
3.43 V / +613 to +621 mA at the battery and 4.63 V / 610 to 632 mA good input,
with no BQ fault. ESP-NOW status reported 41 successful sends and zero failures.

A transient local USB `u` maintenance test supplied the missing discriminator.
The fixture entered the maintenance transition but printed
`no wifi_secrets.h -> cannot OTA`, immediately resumed ESP-NOW, and returned to
healthy COMMS. No flash, NVS/profile/channel write, manual reset, or persistent
mutation was performed. The accepted immutable `fx-260816-otafix1-b` artifact
had demonstrably working compiled-in maintenance WiFi on its F40364 canary, so
Bidoof is running different bytes under the same historical revision string.
This fully explains why supervised targeted-maintenance campaigns never found
an identity-matching endpoint; those observations do not prove a per-unit
ESP-NOW downlink fault. A secondary receive fault remains untested until the
current exact production artifact is USB-installed and targeted maintenance is
rechecked. Preserve NVS, then verify field profile and reboot ride-through as
already planned.

## 2026-08-27 -- Ben + Codex -- T-Deck warm-build cache boundary repaired and proven

Before changing the wrapper, fetched GitHub and confirmed the clean local HEAD
matched current `origin/main` at `d60d1ca`; the second laptop still needed its
own fetch, which Ben acknowledged before work continued.

Fixed the cache failure exposed by the day-mode upload. Cache schema 2 now
treats `firmware/tdeck_bridge/build/dev-cache` as exclusively Arduino-owned.
The wrapper's recipe hash/detail and interruption marker live in sibling
`dev-cache.state`, where Arduino's source-graph cleanup cannot delete them.
Clean removes both cache and state; recovery quarantines both plus any lock;
the existing atomic single-writer and fail-closed interruption behavior remain.
Schema 2 also recognizes a legacy schema-1 `.build-in-progress` marker and
requires quarantine instead of silently reseeding an interrupted old cache.

Added a compile-free wrapper regression with a fake Arduino CLI. Its first
compile deletes every entry, including dotfiles, from the Arduino build path;
the second invocation must retain the external recipe, report `DEV_CACHE_HIT`,
reuse the simulated LVGL object, and leave no lock or in-progress marker. The
clean path must then remove both directories. The complete native Bridge suite
passes with this regression.

Real-toolchain acceptance used one uninterrupted schema-2 seed followed by two
unchanged builds. The seed took 3,051 s (50m51s); the warm runs took 143 s and
145 s (2m23s and 2m25s), about 21x faster. No `.o` or `.a` timestamp changed
during the warm runs. All produced the same 1,579,040-byte application with SHA-256
`d4eb675e4c0423310325d9c35d8613c985d75edaea29833cfc71cb9c3b67f3db`,
50% flash use, and 44% global RAM use. The build was not flashed. Independent
cold-build byte nondeterminism remains a separate explicit TODO.

## 2026-08-27 -- Ben + Codex -- Rotated-power cohort updated; cadence holdbacks closed

After Ben rotated the USB power cables onto dark lanterns, a read-only 379 s
census found eight ordinary old-firmware candidates with safe power evidence.
The exact immutable target remained `fx-260826-51d1fe1-p` (1,206,784 bytes,
SHA-256 `57306019dbf93a1d0cf950f25b9f557d9a0a68663621a7ce4579aba01dea1261`).
Protected Akuma `9E668C`, protected magic-wand Thor `F40344`, and unsafe 0 V
Shuckle `F4031C` were excluded.

The first eight-target 360 s campaign failed closed before upload because
Bidoof `9F26D8`, Cynder `F4042C`, and Meowth `9F266C` did not expose maintenance
endpoints. A follow-up exact five-target batch uploaded Loki `9E5AD4`, Chunli
`9F2714`, Pacman `F40174`, Ponyta `F2B7DC`, and Rikku `9F26B0`; all five supplied
fresh exact-revision heartbeats and survived the 25 s pending-verify gate. The
apparent Cynder/Meowth failure was then correctly identified as cadence: both
had reported `LedTier::PROTECT`, so a separate 930 s PROTECT campaign caught,
uploaded, and pending-verify-proved both. This closes all six fixtures left in
the original 120 s / 3 s cadence rollout defer list.

An authoritative maintenance telemetry audit found Loki, Chunli, Pacman, and
Rikku persisted as `field`, while Ponyta remained `commission`; exact targeted
`FF2B7DC:1:1` changed and persisted Ponyta to field, and a subsequent full mesh
heartbeat reported `profile=1`. Cynder and Meowth reported field immediately
before OTA, and OTA preserves NVS profile. No named nonzero retained peer now
reports commission. A stale `000000/profile=0` record matches Shuckle's old
revision, panic reset, 0 V telemetry, and RSSI and is treated as a transient
identity record rather than a separately addressable fixture.

Bidoof remains the known `fx-260816-otafix1-b` targeted-maintenance downlink
exception: it is continuously fresh on channel 11 with about 3.40 V battery and
strong USB input, but two supervised campaigns never found an identity-matching
WiFi endpoint. Windows exposes only T-Deck COM152; the rotated fixture cables
provide power, not USB data. Bidoof therefore requires a real data-cable USB
rescue. No AP fallback was used.

The failed all-or-none campaign also exposed a cleanup edge case: when
`discover_batch()` raises for missing required targets, its locally found
endpoint map is not returned to `main()`, so the finalizer cannot request
`/resume` for already discovered peers. The bridge roster still freezes
correctly and no upload occurs, but the host should retain incremental discovery
state across the exception so endpoint cleanup is complete.

## 2026-08-27 -- Ben + Codex -- Bridge day mode flashed; dev-cache defect isolated

Ben found the dark Bridge OS presentation too dim in early-morning sun. The
T-Deck now has a persistent Bridge-wide display mode that defaults to day for
existing and new settings. Day mode uses the full 255 backlight and explicit
high-contrast light palettes in the launcher, Fleet, Health, and RF Diagnostics;
night mode restores the saved night-backlight level (59 on primary T-Deck
`8EB508`). Fleet has a quick `DAY`/`NITE` toggle, and Settings exposes the same
mode plus a night-backlight slider. SunTest returns to the active display mode.
The serial console reports the mode and accepts `set display day|night`; `set bl`
now changes the stored night level.

The complete native Bridge suite passed. The ESP32-S3 application is 1,579,040
bytes, using 50% flash and 44% global RAM. It was flashed through the guarded
wrapper to exact T-Deck `8EB508` (`44:1B:F6:8E:B5:08`, COM152); every write
region verified, and a complete application-region readback matched SHA-256
`473510ba76ec5ee9ce47e76575556ac0a7783c78445d913548473e0b3d4b819a`.
After reset it reported `display=day night_bl=59`, rejoined mesh channel 11,
received fresh traffic, reported `sendfail=0`, and passed peripheral and memory
probes. No fixture command or mutation was sent.

This build also exposed a defect in the T-Deck development cache. The first
compile entered as a cache hit, but Arduino rebuilt its dependency graph and
cleaned the build directory, deleting `.dev-cache-recipe.*` metadata that the
wrapper incorrectly stores inside that disposable directory. The immediate
upload invocation therefore failed closed with `DEV_CACHE_RESET reason=missing`
and performed a second full build. Two same-source, same-size full builds also
had different application hashes (`2cabfda9...` then the flashed/read-back
`473510ba...`), so dev builds are not currently byte-reproducible. Repair and
regression coverage are recorded in `TODO.md`; current cache safety behavior is
preserved until that work is done.

## 2026-08-27 -- Ben + Codex -- Fleet table contrast hotfix flashed on 8EB508

Ben's first physical Fleet check found black table text on the dark cell
backgrounds for most live fixtures. The custom Fleet draw hook was styling the
cell-fill task, then returning before LVGL's separate label task; the label
therefore inherited the default black table text. Fleet now sets label contrast
explicitly for every table cell: near-white for headers and live rows, and a
muted light grey for retained off-air rows.

The complete native Bridge suite passed. The corrected `tdeck-dev-local`
application is 1,576,768 bytes with SHA-256
`43cfda9c42e2c73126d232584c4a72717d4b118331dcbe96bf3ab108153f65e2`,
using 50% flash and 44% global RAM. It was flashed through the guarded wrapper
to the exact primary T-Deck `8EB508` (`44:1B:F6:8E:B5:08`, COM152); every write
region verified, and a complete application-region readback matched that hash
exactly. After the readback reset, the Bridge rejoined mesh channel 11, received
fresh fixture traffic, reported `sendfail=0`, and passed peripheral and memory
probes. No fixture command or mutation was sent. Physical contrast confirmation
and the remaining Fleet acceptance checks stay open in `TODO.md`.
## 2026-08-27 -- Ben + Codex -- Fleet truth labels, battery current, and rollout filters

Onboarded from the repo and traced the T-Deck Fleet report in which only a few
fixtures showed `dir` while most showed `idle`. The fixture runtime does not
persist DIRECT through a protection lockout: the lease expires after direct
frames stop, and a reboot/deep-sleep reconstructs runtime state. The actual UI
bug was that each sparse short heartbeat cleared `hasFixtureState`, after which
Fleet rendered the default numeric program value 0 as `idle`. Full-heartbeat
program/profile/lifecycle/tier state is now latched across short heartbeats with
its own evidence timestamp. A sender reboot or sequence restart clears cached
program and firmware evidence until that new boot emits a full heartbeat, so
old state cannot masquerade as current.

Reworked the compact Fleet row around the field-useful values: callsign/class,
`inf`/age, raw VBAT, signed IBAT (`+` charge, `-` discharge), and program. RSSI,
PDR, and advisory gauge SOC remain in detail. An explicit `idle` now means a
reported program 0; `?` means no program evidence. Detail uses human-readable
class, profile, lifecycle, tier, program, and network-mode names such as
`perimeter`, `FIELD`, `DAY_CHARGE`, `PROTECT`, `DIRECT`, and `COMMS`, and also
shows state age, battery/input current, and input-good state.

Extended the scrollable View screen with program filters plus firmware known,
unknown, exact-reference, and not-reference/unknown filters. The firmware
reference picker is populated from up to 16 exact revisions retained by the
census; a compact 32-bit equality fingerprint rides cached census rows so the
many 192-row consumers do not duplicate 24-byte strings. The non-match cohort
deliberately includes missing revision evidence for rollout triage; host-side
fresh-revision and pending-verify gates remain the authority for OTA success.

The complete native T-Deck suite passes, including regressions for IDLE versus
unknown, full-state retention across short heartbeats, reboot invalidation, and
firmware rollout filters. The unflashed `tdeck-dev-local` build uses 1,578,783
bytes (50 percent) of flash and 164,880 bytes (50 percent) of global RAM. Its
1,578,928-byte binary has SHA-256
`d7e544c435b9bc9bbfc26488f985ea06666224cc9cc354f6fa2a4aa2af25c599`.
No hardware was flashed; primary T-Deck `8EB508` still carries the prior
verified image documented below.

## 2026-08-27 -- Ben + Codex -- PUCA safe boot and exact-target shared-WiFi OTA source

Implemented ADR 0063 for the one-off Original Edition PUCA `A4EB10`. The
`0.5.0-dev` source now boots SAFE-IDLE after every reset and emits no
`NB_DIRECT_FRAME` unless the capacitive paw is held continuously for 1.2 seconds
during boot. A successful hold arms line input + DJ (the prior CLASSIC per-slot
look) and opens the existing 20-second setup window; the live cycle is now DJ,
HEARTBEAT, EMBER, HUE. Locked touches still report status only. An OTA/software
reboot deliberately returns dark and requires a later physical paw-held boot to
publish.

Added a PUCA tail-7 heartbeat carrying `puca-bridge-0.5.0-dev`, so Bridge OS can
census and target the publisher without any audio bridge mistaking it for a
fixture. PUCA accepts only an exact `NB_TARGET_ENTER_MAINT` for its own short ID;
the all-zero fleet target is test-covered and ignored. Maintenance stops
publishing without a blackout frame, leaves channel-11 ESP-NOW, joins the shared
maintenance WiFi, and exposes the fixture-compatible `/telemetry`, `/update`,
and `/resume` endpoints. It never creates a softAP. Resume, startup failure, and
the 10-minute timeout return to dark COMMS. The default 4 MB dual-app partition
layout and deferred 20-second codec/I2S/network/NVS self-test provide A/B
rollback; a forced-failure build flag supports the rollback drill.

Extended the build wrapper with explicit default OTA partitions, `--ota`,
`--wifi-source`, and `--ota-fail-selftest`. Updated PUCA hardware/firmware docs,
the Bridge OS field manual, TODO, and added the ADR. The documented end-to-end
path reuses `field_cycle_ota.py`: Bridge OS sends `UA4EB10`, host discovery
identity-matches the PUCA endpoint, waits out the 35-second command tail,
uploads the PUCA binary, then requires fresh exact-revision rejoin evidence and
25-second pending-verify survival.

All 103 native PUCA checks pass. A clean ESP32-PICO-D4 build on explicit
`PartitionScheme=default` uses 1,013,704 bytes (77 percent) of the 1,310,720-byte
app slot and 62,504 bytes of RAM; binary is 1,013,856 bytes, SHA-256
`1ff4f5aa9baf168fe8d6866d92f841b21406a0ad29cc8281901e8f595c674e58`.
This is deliberately only a compile-check: the checkout has no local
`wifi_secrets.h`, so that image would refuse OTA. No hardware was flashed.
Windows also exposed only COM3 / PowerFeather `F2BE20` (`VID_303A`), not the
PUCA CP2102N (`VID_10C4`, previously COM154), so the wrong ESP32 was explicitly
excluded. Next is to re-enumerate the PUCA, provide the shared-WiFi header via
`--wifi-source`, build/USB-flash that credentialed bootstrap, then execute ADR
0063's safe-boot, exact-target OTA, pending-verify, and rollback hardware gates.

## 2026-08-27 -- Ben + Codex -- One plugged canopy class probe verified; second identity still unknown

Onboarded from the repo and investigated Ben's report that two USB-powered
physical canopy lights appeared as uplights while a separate PUCA bench was
active. Preserved the in-progress PUCA source and did not touch PUCA hardware.
Windows exposed only one Espressif USB data device: COM3 / Sonic `F2BE20`
(`68:EE:8F:F2:BE:20`), a registered outer-ring downlight. The other powered
canopy was not data-enumerated on this host, so its exact identity remains
unknown from host evidence.

Opening COM3 with DTR and RTS disabled nevertheless caused the ESP32-S3 native
USB path to report `USB_UART_CHIP_RESET`; no other fixture port was opened after
that. Sonic rebooted cleanly on valid production artifact
`fx-260826-51d1fe1-p`, retained commission/listener, 15 Ah, 2 A, channel 11,
and reported no class mismatch. Its cold boot ID probe found TMF8820 + BMP581
(`sensor_bits=5`) and selected `downlight`; the later MSA driver probe reported
the MSA present, although the early telemetry sample preceded its first healthy
read. This proves the visible listener light is not itself a sensor-health gate
and rules out a missing-TMF/uplight classification for Sonic on this boot.

Ben clarified that the suspected misclassification came from T-Deck LED
Studio's white swatch rendering equal RGB rather than the dedicated W die. The
current planner does use dedicated W for a census class of downlight, but it
also deliberately maps class `unknown` to RGB white. LED Studio consumes the
raw census class and does not use the embedded registry-role fallback that the
new Fleet view uses. Therefore RGB white proves only that the T-Deck did not
have `downlight` latched for that target at planning time; it does not by itself
prove the fixture probed as uplight. Sonic's exact boot evidence is the stronger
current result. Fixtures send a full class-bearing heartbeat at boot and every
5 seconds in commission, but a missed initial full frame can leave a briefly
fresh/unknown target after its short heartbeat arrives.

Ben then ruled out both PUCA and LED Studio as sources for the three illuminated
bench fixtures at about 09:00. The lifecycle trace identifies two remaining
paths. Sonic is explicitly in persisted commission/listener, which never
day-sleeps and deliberately shows a ready beacon regardless of time. A field-
profile fixture without valid scheduled UTC instead falls back to the bare-peer
heuristic: 30 continuous minutes without a good >=20 mA input becomes dusk and
starts autonomous `NIGHT_SHOW`; five minutes of useful input ends that show.
Distributed UTC is RAM-only, expires 30 minutes after the last accepted source,
and is lost immediately on reboot, so a battery-only fixture stranded from the
fleet in bench shade can enter a false night. The autonomous Greenberg-Hastings
CA can look like random light activity. USB normally supplies affirmative day
evidence (Sonic reported about 70 mA), so the USB-powered fixtures remaining lit
for more than five minutes point to commission/listener rather than false dusk;
the unpowered-by-USB fixture could be either. Fleet detail exposes the decisive
state directly: lifecycle 3 is `NIGHT_SHOW`, while 4 is `COMMISSION`.

The initial diagnosis performed no flash, OTA, profile/channel persistence, NVS
mutation, fixture command, or PUCA operation. A follow-up host recheck after more
than five minutes still exposed only COM3/Sonic; no T-Deck and neither other
fixture enumerated as a data device. Elapsed time in shade does not satisfy the
five-minute dawn gate: it specifically requires continuous good input at >=20
mA.

Ben then explicitly authorized the exact `F2BE20` profile repair and the known
USB-open reset risk. With this laptop declared the sole configuration writer,
the guarded transaction identity-checked COM3's USB serial as
`68:EE:8F:F2:BE:20`, sent local `F1`, received `profile -> field`, and verified
with a bare `F` query returning `profile=field`. The live lifecycle immediately
started its daytime solar probe on 358 mA input. No image, channel, or other
fixture was changed.

The same short serial window captured six successive 40 ms `capboard SW1`
strikes, numbered 27 through 32; the host sent no strike command. Ben then
confirmed that the 433 MHz handheld transmitter had been used intermittently
that morning. The receiver and physical SW1 intentionally share the external
D7 path and therefore the same log label, so this is expected transmitter
activity rather than a profile-write side effect or capboard fault. Field
profile deliberately does not suppress that physical/receiver authority path.
The serial port was closed after verification.

Ben next connected the other prior RGB-white canary. USB enumeration identified
Bidoof `9F26D8` on COM4 and, six seconds later, registered outer-ring downlight
Leia `F40384` on COM5. With Ben authorizing the possible USB-open reset, a
read-only COM5 telemetry query proved Leia is running `fx-260826-51d1fe1-p`,
classifies `downlight` with `class_ovr=0` and no mismatch, and has healthy
MSA311, TMF8820, and BMP581. The TMF reported 85,330 successful reads with zero
errors or recoveries. This rules out a current STEMMA/class-probe failure as the
cause of Leia's prior LED Studio RGB-white result and supports the already
traced T-Deck raw-census `unknown` -> RGB semantic-white gap.

The same telemetry exposed two independent current-state facts. Leia remained
in persisted commission/listener (`life_state=4`), so it showed its daytime
ready beacon after commands stopped. It was also actively receiving direct
frames: over the observation interval `direct_seen` rose from 110 to 1,702 and
`direct_matched` from 110 to 716 while program remained 3 (`DIRECT`). Ben then
clarified that PUCA was connected and believed to be publishing. Fixture
telemetry does not retain the direct sender ID, so this observation is attributed
to the declared PUCA bench context and is not evidence of a lingering T-Deck
LED Studio stream. The existing Bridge OS Back-versus-Stop semantics remain
documented separately.

Ben explicitly authorized Leia's exact profile repair. With this laptop the
sole fixture configuration writer, COM5 identity was rechecked as `F40384`,
local `F1` received `profile -> field`, a bare `F` query returned
`profile=field`, and complete telemetry independently confirmed field profile,
`life_state=1` (`DAY_CHARGE`), 328 mA good input, and LED rail off. The live
class remained downlight with healthy TMF. PUCA and Bidoof/COM4 were untouched;
no fixture image or other NVS field changed.

## 2026-08-27 -- Ben + Codex -- Filterable Fleet Bridge OS flashed and read back on 8EB508

Declared the primary T-Deck `8EB508` (`44:1B:F6:8E:B5:08`, COM152) the sole
writer and flashed the already verified `tdeck-dev-local` Fleet image through
the Bridge build wrapper. The 1,576,688-byte application has SHA-256
`703b71a038530029dbd12b0cd072bc589b2d06dc83b12d9c3d4e6ca7073ea622`.
Esptool verified every written region, and a subsequent 1,576,688-byte readback
of the application region matched that SHA-256 exactly. The temporary readback
was removed after verification.

After both the flash and readback reset, the Bridge rejoined mesh channel 11 as
`8EB508` on `tdeck-dev-local`, received fresh fixture traffic, and reported
`sendok=19`, `sendfail=0`. PSRAM, keyboard, touch, codec, and GPS probes passed;
the final memory sample showed 85,744 bytes minimum free heap and 7,718,884
bytes minimum free PSRAM. Only read-only `show`, `probe`, and `mem` console
queries were used for acceptance. No fixture command, OTA, reboot, profile,
lifecycle, or fixture-NVS mutation was sent. Physical screen layout, dropdown,
stable-scroll, detail/back, 192-row memory, and named filtered-identify canary
acceptance remain open in `TODO.md`.

## 2026-08-27 -- Ben + Codex -- Stable filterable T-Deck Fleet view implemented

Onboarded from the repo and traced the Fleet app's scroll jumps to its two-
second live-first re-sort by heartbeat age and RSSI. Replaced that implicit
dynamic order with a native-tested Fleet view model. The default is now the
complete 144-entry production registry plus fresh unexpected peers, sorted
stably by callsign. Registry fixtures retain grey off-air rows, the old 64-row
UI cap is gone, and fixture identity plus scroll context survive refreshes and
detail round trips. The table now exposes raw VBAT instead of advisory SOC;
detail retains both.

Added a View screen with independent roster/seen/live scope, downlight/
perimeter/uplight/chandelier/unknown class filters, good/near-low/low/off-air/
invalid-VBAT filters, and callsign, short-ID, voltage-low/high, recent, or RSSI
sorting. Stable callsign is the default; age and signal are explicitly dynamic
operator choices. Live class telemetry stays authoritative, with registry-role
fallback only for absent or not-yet-full-heartbeat rows.

Added confirmed identify of the current filtered cohort. The button snapshots
only fresh visible IDs, reports the exact count with cancel focused, then walks
those exact targets at 80 ms cadence with 30-second green blinks. It does not
broadcast to hidden/off-air rows and changes no packet, OTA, reboot, profile,
lifecycle, or fixture-NVS contract. Sleep/Dark and Release remain together
behind the Fleet Power entry point.

The complete native Bridge suite passes, including the new stable-roster,
scope, class, battery-band, voltage-sort, and role-fallback tests. A first
embedded pass caught and fixed Arduino's `LOW` GPIO macro colliding with the
battery enum. The clean `tdeck-dev-local` build then passed at 1,576,688 bytes,
SHA-256
`703b71a038530029dbd12b0cd072bc589b2d06dc83b12d9c3d4e6ca7073ea622`,
using 50% flash and 44% global RAM. Documentation is updated. Nothing was
flashed; physical layout/input, stable-scroll, memory-watermark, and named-
canary filtered-identify acceptance remain in `TODO.md`.

## 2026-08-27 -- Ben + Codex -- USB-powered recovery updated 20 fixtures; low-VBAT lane passed

Declared T-Deck `8EB508` / channel 11 the sole writer and recovered the connected
old-firmware cohort with immutable fixture artifact `fx-260826-51d1fe1-p`
(1,206,784 bytes, SHA-256
`57306019dbf93a1d0cf950f25b9f557d9a0a68663621a7ce4579aba01dea1261`).
The expected 24 USB fixtures appeared gradually as 23, 24, and finally 25 exact
USB-powered peers. Twenty were uploaded in staged canary/ordinary/low-VBAT
batches; every one produced a fresh exact-revision heartbeat and survived the
25-second pending-verify gate. Three already-current fixtures were not
reflashed, Thor `F40344` retained its protected net-bench image, and Clank
`F2BF60` was deliberately refused at 0.86 V. Final accounting was 23/25 on the
production artifact, one protected magic wand, and one unsafe low-cell defer.

The 2.2-2.5 V recovery lane passed on real hardware. Daxter `9D7884` was the
one-device canary at 2.324 V, followed by Daisy `F40308` and Dratini `F4035C`.
All three survived OTA, proved an attached battery, enabled guarded charging,
reported field profile and no BQ fault, and showed the expected USB input-current
step. Daxter and Daisy rose to about 2.61 V and graduated to recovery state 4;
Dratini rose from 2.342 V to about 2.46 V and remained actively recovering at
the final sample. The MAX17260 current channel remained asleep at these low
voltages, but BQ state, input current, presence evidence, and rapid VBAT rise
proved charge flow. Tidus `F40424` already had current firmware but still
reported about 0.01 V/recovery refused and needs a battery-path inspection.

The first canary attempts failed closed before upload and exposed two
control-plane bugs. A 100+ peer full snapshot every second permanently exceeded
115200-baud capacity, while the host requested status four times per second and
amplified the backlog. T-Deck snapshots now emit every 10 seconds, host status
requests are bounded to once per 10 seconds with a 30-second acknowledgement
window, and the newly immediate acknowledgement exposed/fixed one ledger
`phase` name collision. Added exact-target-only serial profile command
`F<ID>:<0|1>:<0|1>` (profile/persist), refused for all-zero targets; hardware-
smoked a nonpersistent field command on Gambit. Post-OTA audits found every
sampled fixture already in field profile, so no persistent mutation was needed.

Final exact T-Deck dev-local image on `8EB508` is 1,573,072 bytes, SHA-256
`f42b4a1d40b151e07de1f569fd9cf50a095bf270f3d68547b450953d54ef4d51`.
The full embedded build, all 15 native test binaries, and 29 host OTA/dashboard
tests passed. Live bridge evidence ended on channel 11 at 7,888 successful sends,
zero failures, with the last campaign frozen. Full target/result/ledger detail is
in `docs/tests/USB_POWERED_FIXTURE_RECOVERY_2026-08-27.md`.

## 2026-08-26 -- Ben + Codex -- CoreS3 Milestone A cadence passed on hardware

Flashed only exact CoreS3 `4D5DB0` / `80:45:6B:4D:5D:B0` with the fresh
Module Audio/channel-11 `r6` build. The 1,189,072-byte binary SHA-256 is
`4AB7DB1D7F09526CD82A6E6FE7B22C5455F5DAA951C3956AED8ABB10A6F2E6C2`;
all upload region hashes verified. The full Audio screen transfer initially
limited cadence to about 15 Hz, so active Audio now transfers only its 304 x 96
spectrogram at 25 Hz, updates small meters at 5 Hz, and limits the full USB peer
table to once per 5 seconds while retaining 1 Hz compact timing telemetry.

On the awake fleet, a 65-second Ambient run achieved 24.802 Hz analysis,
24.799 Hz display, and 9.999 Hz direct-frame publishing with zero audio read
failures, radio send failures, or RX queue drops. A preceding 70-second Module
TRS run achieved
24.020/24.006/10.000 Hz; its one radio send failure leaves the 30-minute
zero-failure soak open. Both source handoffs performed an explicit black frame,
and Audio was paused/black at the end. No fixture firmware, OTA, flash, NVS,
profile, or lifecycle state changed. Physical Aux photodiode and Ambient video
sound-to-photon measurements remain open.

## 2026-08-26 -- Ben + Codex -- Live CA color and perimeter-silence diagnosis

Onboarded from the repo and inspected the already-running read-only dashboard
on T-Deck `8EB508` / `COM152`; no fixture command, OTA, profile change, reboot,
or NVS write was sent. At 20:37 PDT the bridge was healthy on channel 11 but
had restarted or been power-cycled about five minutes earlier and reported zero
outgoing frames, sends, or failures. Thus no LED Studio stream was active; a
direct stream disappears from fixtures after about three seconds of silence,
while their autonomous GH-CA continues independently.

The red/orange apparent CA island is primarily the intended class tint, not
proof of a disconnected component. Autonomous GH-CA uses hue 30 for perimeter
HEX fixtures and hue 160 for the rest of the fleet; neighbor excitation crosses
classes without copying hue. Awake perimeter peers Magmar `F2BDFC` and Swablu
`F2BE70` both reported class 2, LED rail on, one warm pixel at roughly
`25,17,0`, and usable bidirectional mesh evidence. Their battery readings were
3.170 V / 8 percent advisory SOC and 3.228 V / 34 percent respectively. The
RSSI-selected strongest-eight, three-second-fresh neighbor view can still make a
local cluster look islanded, especially before a pinned spatial map exists.

The perimeter cohort nevertheless has a real power/recovery problem. Current or
recent known-perimeter evidence included `F403DC` at 2.848 V with its LED rail
off, stale `F2BF74` / `F3FD88` near 2.25 V, `F401DC` near 3.10 V with tier 3 and
rail off, and `F40314` near 3.22 V but still tier 3/rail off. Some protected
wakes report class unknown and are therefore excluded by LED Studio's perimeter
filter even while briefly reachable; local power vetoes would still refuse
light output. Ben corrected the repository's pre-QC inventory state: all 24
perimeter fixtures were QC'd, dead cells were replaced, and none should now be
batteryless. The slot-to-MAC map and registry role coverage remain incomplete;
silence now needs to be separated into low charge, solar/charge-path failure,
identity/firmware trouble, or another hardware fault using fresh voltage and
current evidence. More precisely, QC rejected every installed cell below
3.10 V and replaced it with a factory-fresh cell individually verified above
3.20 V; the replacement cohort was not merely populated with marginal old
cells.

After LED Studio was reactivated, T-Deck `8EB508` transmitted continuously at
about 27 packets/s with successful send callbacks and zero failures. This rules
against a bridge publishing failure as the explanation for only 2 of 24
perimeters lighting. Under that load, `F2BDFC` sagged toward 3.10 V and `F2BE70`
toward 3.20 V. The former is at the LEDs-off/protect boundary and the latter has
little reserve. The current LED Studio run adds load and should be stopped when
not needed, but ten minutes near 180 mA is only about 30 mAh -- far too little
to take a healthy 6 Ah cell from charged to PROTECT.

The depletion also predates the current LED Studio run and the late-day tests.
Thirteen fixtures were already undiscoverable/deferred during the production
rollout, most with prior PROTECT evidence. The new fixture sleep audit shows the
updated cohort using automatic 120-second DAY_CHARGE sleeps, while the current
T-Deck action audit contains no retained Sleep, Dark, or Force action. Today's
207-second PUCA soak and short audio/CA tests are also too small to explain the
class-wide loss. The strongest working hypothesis is therefore accumulated
negative energy balance in the 6 Ah / 2 W perimeter class, caused by inadequate
recent harvest or a shared panel/orientation/cabling/charge-path problem. There
is no historical daytime logger for this interval, so the exact harvest failure
is not yet proven. In the next strong-sun window, leave artistic LED streams
off and capture supply voltage/current plus battery current on several named
perimeters before and after inspecting their P126 panels and connections.

Follow-up review identified the perimeter VL53L5CX as a plausible contributor
but not yet a proven root cause. Every awake perimeter starts the sensor and
ranges continuously from the fixture's perspective at 4x4 / 5 Hz, regardless
of whether the current artistic program uses ToF. Deep-sleep entry explicitly
cuts the complete VSQT sensor rail, so it should add essentially nothing during
the 120-second sleep interval. The ULD documents autonomous mode as its default,
but fixture firmware does not explicitly set or read back the ranging mode or
integration time. ST specifies about 19 mW (roughly 6 mA at 3.3 V) for autonomous
4x4 / 5 Hz / 5 ms, versus 313 mW (roughly 95 mA) in continuous mode. The intended
case is too small to explain 22 of 24 by itself; an unexpected continuous-mode
case would materially worsen the small-battery nightly budget. A named-perimeter
current A/B with identical radio/LED state, plus mode/integration readback, is
required before ruling this axis in or out.

Ben then connected USB to two physically dark perimeter positions. The two USB
identities were `F40344` (Thor) and `F4035C` (Dratini). Thor reported healthy
4.68 V input and about +495 mA battery charge, although the registry currently
describes it as the portable Magic Wand rather than a perimeter; reconcile that
physical assignment. Native USB identified Dratini on COM155. An exact-target
telemetry query restarted that unit once through the USB CDC connection but
made no firmware or configuration change. It booted old
`fx-260816-prtrel1-b`, self-classified as perimeter, and reported durable
PROTECT stage 4, a real but deeply depleted 2.324 V / 6 Ah LFP, good 4.883 V
USB input at 72 mA, no BQ fault, but `battery_present=false`,
`charging_enabled=false`, and 0 mA battery current. Thus Dratini is not being
rescued merely by leaving USB attached. This is the known pre-ADR-0042 firmware
gap: below the old 2.5 V plausible-cell threshold the image refuses charging;
later fleet images add the guarded 2.20-2.50 V recovery lane and verified
300 mA precharge. Dratini needs the explicit supervised USB recovery/flash path
with post-flash positive-current and voltage-rise evidence, not an OTA retry.

The clarified QC threshold makes a firmware-mediated post-QC collapse credible.
Perimeter Sneasel `F403DC` is especially useful evidence: it was 2.296 V before
QC and therefore had to receive one of the >3.20 V replacement cells, but the
dashboard now retains a 2.755 V heartbeat from `fx-260818-05ed4b3-b` with
`profile=0` (commission), about -166 mA, no input, and PROTECT. Dratini's exact
USB telemetry likewise reports commission profile. Commission intentionally
keeps ESP-NOW RX awake; the measured LEDs-dark battery-only floor is about
126-144 mA, or 3.0-3.5 Ah/day before the listener pixel and ToF. At roughly
160-200 mA total, a fixture spends 3.8-4.8 Ah/day. A >3.20 V open-circuit LFP
check proves a real, non-dead cell but does not prove a full 6 Ah charge because
of the flat LFP plateau. A field-default OTA image also does not overwrite an
already persisted commission profile. The likely chain is therefore: a
partially charged factory cell was installed, an old persisted commission
posture spent most or all of its reserve faster than the small P126 could
replace it, and old pre-recovery firmware could then either charge at the old
30 mA precharge rate or, below 2.5 V, refuse charging altogether. This chain is
directly demonstrated on one perimeter and consistent with another, but is not
yet proven for all silent perimeter slots.

Ben then connected two physically dark canopy fixtures by USB. Windows
enumerated only Loki `9E5AD4` / `D8:85:AC:9E:5A:D4` on COM105; no second
Espressif serial, JTAG, bootloader, or failed USB device appeared. Opening
Loki's USB CDC for read-only telemetry restarted it once but made no firmware,
profile, NVS, or other configuration write. Exact telemetry identified
`fx-260818-f80f315-b`, 6 Ah LFP, downlight class, persisted commission profile,
PROTECT stage 4, rail off, and the verified 300 mA precharge setting. With USB
attached it held clean supply and no BQ fault, charged at about +293 mA, and
rose from 2.851 V to 2.868 V over 93 seconds. Loki is therefore deeply depleted
but is successfully recovering on its existing image; keep it attached. The
second canopy remains electrically unidentified and should be connected alone
through Loki's proven data cable/host port to distinguish a cable/port problem
from failure to boot/enumerate on USB.

## 2026-08-26 -- Ben + Codex -- Predictable job-scoped fleet OTA implemented

Implemented ADR 0062's conservative path from the 120/3 rollout post-mortem.
The T-Deck now owns a bounded 160-target exact-maintenance roster instead of one
overwritten target. It schedules at 10 ms per target (1.3 s for 130 fixtures),
uses explicit job-scoped begin/add/freeze/status commands, preserves legacy
`U<ID>`, and emits structured `nb-maint` evidence through the dashboard. Native
campaign tests pass 452 checks including capacity, idempotence, wraparound,
expiry, wrong-job refusal, round-robin timing, and immediate freeze.

Refactored `fleet_dashboard_ota.py` into PLAN -> PREFLIGHT -> GATHER -> DISCOVER
-> FREEZE -> UPLOAD -> VERIFY -> CLEANUP. The host derives a 150 s ordinary or
930 s PROTECT gather, refuses insufficient deadlines, requires a fresh matching
freeze ACK before upload, removes the fixed 38 s tail, separates HTTP results
from promotion, reconciles responsive endpoints before any retry, requests
`/resume` during cleanup, uses independent firmware evidence age, and exclusive-
creates one append-only per-target job ledger. Dashboard and host tests pass.

Recorded deferred multicast/mesh-distribution and pre-stage/activate designs in
`docs/design/FLEET_OTA_FUTURE_SPEED_OPTIONS.md`; shared-WiFi unicast remains the
production transport. Added the 10-minute runbook.

Later in the same session, exact T-Deck `8EB508` on COM152 was flashed with the
complete `dev-local` image (1,572,560 bytes, SHA-256
`96f5bad803c7af646d64c2a9d3e75c42ca1a2eaa50aaac99d79c7830985f3281`).
The restarted dashboard positively reported that bridge on channel 11. A
collision-checked synthetic 130-ID roster reported a 1,300 ms cycle, dispatched
348 packets with 348 successful callbacks and zero failures, retained the same
86-peer census, and stayed exactly at dispatch 348 for one second after FREEZE.
Legacy `UF00001` still parsed as one-target `U<F00001>`, not the new lowercase
freeze command; its fake campaign was explicitly frozen afterward. The source
and live bridge scheduler are validated. A clean immutable bridge promotion,
small real-fixture interruption batch, and timed full fleet pass remain open.

## 2026-08-26 -- Ben + Codex -- PUCA standalone heartbeat baseline flashed and fleet-soaked

Installed the official Silicon Labs CP2102N Windows driver and positively
identified the received PUCA on `COM154` as ESP32-PICO-D4 revision 1.0 with
4 MB embedded flash, MAC `4C:75:25:A4:EB:10`, and USB identity
`USB\\VID_10C4&PID_EA60\\0EC45B486617EC1183509E9D47486EB0`. The S3 bench
device on `COM152` was explicitly excluded. Before the first Resonance flash,
captured an exact 4,194,304-byte full-flash recovery image with SHA-256
`c4f67d01dc1c001e1e6342f7b3b604f77b5f6f701ee4962b3bb94dd5e3d0bfcf`.

Changed the no-laptop runtime to boot in HEARTBEAT + line input with controls
LOCKED. A normal capacitive-paw touch now displays status only, so a DJ or
performer cannot accidentally stop or change the show. A continuous 1.2 s paw
hold at boot opens a 20 s setup window; short touches cycle HEARTBEAT, CLASSIC,
EMBER, and HUE, while a long hold confirms and locks. OFF is deliberately absent
from the paw cycle. The bottom LED encodes input with long pulses and mode with
short pulses. Native coverage for gestures, setup timing, LED timing, waveform
following, full-census chunking, and peer identity reached 85 passing checks.

The first flashed candidate exposed a stale `fixture-*`-only filter: transmit
counters stopped once current ADR 0040 `fx-*` heartbeats had identified every
peer. Aligned PUCA with the already-tested CoreS3 eligibility rule (`fx-*`,
legacy `fixture-*`, and `dev-local`) and added an eligible-fixture count to
status. Built and flashed the corrected `0.4.1-dev` candidate from the unique
`puca-bridge-20260826-standalone-heartbeat-v041-c2` directory. Its binary is
964,752 bytes, SHA-256
`e8ec74680564f96f10c2f6e87b37eb807b9d9ba3b355ccf41c72f8301c4984b6`;
all flash write/read-back hashes verified.

The powered Pod20 booted with steady rails, codec and stereo I2S ready, line
input, HEARTBEAT, channel 11, and LOCKED controls. Ben's normal paw test printed
status only and did not change mode. During a 207 s full-census soak the bridge
grew to 70+ eligible fixtures and 8,318 successful send callbacks with zero send
failures, audio read failures, receive drops, codec I2C errors, or clipped
blocks. This proves the local publisher and more-than-18-fixture packet path;
the performer's exact DG1022Z waveform, visible receiver response/stale fallback,
full knob sweeps, boot-hold setup feel, intended-placement RF/PDR, mixed-output
fidelity, and multi-hour soak remain open.

Left the powered bridge in a deliberate non-publishing service state so silent
HEARTBEAT frames do not own the fleet while no generator is connected. USB key
`A` sent one final eight-chunk black census, status changed to `active=0`, and
the transmit counters remained fixed. This state is intentionally not persisted;
the next power cycle restores active HEARTBEAT + line input + LOCKED controls.

## 2026-08-26 -- Ben + Codex -- 120/3 production rollout reached 85/98; OTA post-mortem recorded

Rolled immutable fixture artifact `fx-260826-51d1fe1-p` (1,206,784 bytes,
SHA-256 `57306019dbf93a1d0cf950f25b9f557d9a0a68663621a7ce4579aba01dea1261`)
from source commit `64264b2c60cbff9a9423642cb6cfee93e4272636` to 85 of the
98 fixtures on the prior production revision. Every promoted fixture produced
a fresh exact-revision mesh heartbeat and survived the 25 s host pending-image
gate. Stage-1 fixtures `9F2638`, `9F26BC`, and `F4019C` also proved the new
cadence end to end: after their 10-minute software-boot grace they slept near
600 s uptime and returned from an approximately 120 s timer sleep with
`reset_reason=deepsleep` and the exact new revision.

Thirteen production fixtures remained undiscovered and were not flashed:
`9F266C, 9F26B0, 9F2714, F2B7DC, F2BCF4, F2BDD4, F2BF7C, F3FD28, F40174,
F401DC, F402A8, F40314, F4042C`. Their last VBAT range was 3.101-3.539 V;
most full heartbeats reported PROTECT. The field PROTECT cadence is 900 s sleep
with only an 8 s wake grace, so the late-day five-minute pass could not span one
cadence. They are deferred for a strong-sun recovery/gather window. Temporary
fleet-dark gathering was explicitly released; special, dev-local, recovery,
prototype, and Magic Wand revisions were not selected.

The rollout exposed a bridge/tool contract bug: T-Deck stores only one sustained
exact-target maintenance campaign, while the host batch tool sends many targets
as if each campaign persists. Rapid lists therefore overwrite earlier targets.
It also exposed the difference between recently heard and positively held
awake, dashboard full-field revision lag, HTTP timeout despite successful OTA,
and a gather/verification race that re-caught three new-image fixtures in
maintenance; exact endpoint telemetry plus `/resume` recovered them without a
second flash. The full evidence ledger, root-cause analysis, deterministic
pacing math, and proposed PLAN -> PREFLIGHT -> GATHER -> DISCOVER -> FREEZE ->
UPLOAD -> VERIFY -> CLEANUP redesign are in
`docs/tests/FLEET_OTA_120X3_ROLLOUT_POSTMORTEM_2026-08-26.md`.

## 2026-08-26 -- Ben + Codex -- 120/3 fleet artifact built; rollout waiting on T-Deck USB

Promoted the validated Akuma cadence recipe into clean source commit
`64264b2c60cbff9a9423642cb6cfee93e4272636`, containing only fixture firmware,
tests, and ADRs 0059/0060. The complete fixture native suite passed, including
172 behavior checks, 63 packet-layout checks, 37 fail-closed serial-mutation
checks, and 13 sleep-audit checks. A first embedded build was interrupted by a
concurrent field-laptop compile; its exact lingering compiler PIDs were stopped
and its partial directory was never reused. The fresh exclusive build completed
normally with the required flash/RAM summary.

The immutable production artifact is `fx-260826-51d1fe1-p`: 1,206,784 bytes,
binary SHA-256
`57306019dbf93a1d0cf950f25b9f557d9a0a68663621a7ce4579aba01dea1261`,
recipe SHA-256
`51d1fe14bcde00e05bca6174bf9c9317d14c1dcaa3568bdcd62c0a1e368e8812`.
Its manifest is clean-source variant `p`, field profile, channel 11, standard
listener capability, 120 s DAY_CHARGE sleep, and 3000 ms timer-wake listen.
The copied canonical artifact and recipe hashes were independently rechecked.

Declared stage 1 as healthy exact targets `9F2638` (Lucas), `9F26BC` (Pinsir),
and `F4019C` (Treecko). Their dry-run preflight passed at 3.335-3.515 V with
live input. The first live maintenance POST returned HTTP 500 because the
T-Deck had disappeared from COM152 and the dashboard was disconnected. Its
recorded last command remained the earlier Akuma test, proving no stage-1
maintenance command was accepted; discovery and upload never started. Resume
only after physical T-Deck USB reconnection and a fresh `8EB508` bridge
heartbeat, then require exact revision through the 25 s pending-verify gate
before widening. Full callout:
`ops/bench/data/ca/20260826-120x3-cadence-rollout-callout.txt`.

## 2026-08-26 -- Ben + Codex -- CoreS3 Milestone A latency scheduler implemented

Implemented the CoreS3-only first slice of the sound-to-photon plan without
changing the fixture wire contract or fixture source. Audio analysis, legacy
direct-frame publishing, the spectrogram display, and bridge status now have
independent phase-locked deadlines. Late work advances from the prior deadline,
skips stale periods without catch-up bursts, and records achieved rate, minimum
and maximum interval, skipped periods, maximum lateness, and maximum capture,
FFT, packetization, display, and total-loop blocking time. This removes the
spectral path's permanent 40 ms / 100 ms quantization to 120 ms (8.3 Hz) while
keeping the installed-fleet publisher target at 10 Hz.

Calibration now measures two seconds across contiguous successful microphone
captures rather than assuming a fixed number of loop iterations. A capture gap
over 200 ms restarts that clock. Decoupling the publisher exposed a stale-data
safety edge: an I2S failure could otherwise replay the last bright feature. A
stale input now blocks publishing and emits one explicit black frame before the
fixture's ordinary fallback. The Audio screen reports achieved FFT/TX rates,
and the one-second USB `audio-timing` line carries the full scheduler evidence.

Added the durable physical-measurement record at
`docs/tests/AUDIO_REACTIVITY_LATENCY_BASELINE_2026-08.md`: Aux uses a common-clock
electrical input edge and fixture photodiode, Ambient uses a 240 fps visible-clap
cross-check, and both require median/p95/max, settle/release, and cohort skew.
The native CoreS3 suite passes 167 checks, including phase regression,
overrun/skip, millis wrap, cadence math, successful-time calibration, stale
capture freshness, FFT/envelope, and app-model coverage.

No device was flashed and no mesh artistic frame or fixture command was sent
during implementation. Several CoreS3 build attempts were abandoned when
unrelated PowerFeather compiles took the shared Arduino path. The final fresh,
exclusive Module Audio/channel-11 `r4` build passed at 1,187,435 sketch bytes
(37 percent) and 100,320 bytes dynamic memory (30 percent). Its 1,187,584-byte
binary SHA-256 is
`8FE579C3B83B8481776D0028635C133031D94EDD5B3A3C9E1077F8FBA65724FF`;
the build options confirm the CoreS3 board, channel 11, and Module Audio flag.
Exact CoreS3 `4D5DB0` / `80:45:6B:4D:5D:B0` then reappeared on `COM43`; its
pre-flash boot reported `cores3-os-0.1.2-dev`, channel 11, and Module Audio
ready. Physical cadence and sound-to-photon evidence remain open.

## 2026-08-26 -- Ben + Codex -- DG1022Z PUCA heartbeat source built

Added a dedicated HEARTBEAT look to the partially proven PUCA performance bridge
without changing the fleet packet contract or any fixture source. USB key `H`
now selects the WM8978 line input and HEARTBEAT in one step. Unlike the ambient
audio path, this mode follows raw stereo block peak with no quiet-room
calibration, so a continuously repeating generator waveform is not learned away
as noise. A fast peak follower preserves narrow pulses within the existing
100 ms capture / approximately 10 Hz direct-frame ceiling, and KNOB2 caps a
shared deep-red RGB pulse. Status output adds `wave` beside raw peak/clipping
evidence. Native coverage grew to 39 passing checks for peak attack/release,
sensitivity, and heartbeat color.

A clean `esp32:esp32:pico32` build completed at 963,248 bytes with SHA-256
`365bd7d61e67897c8080c9089f5c2176e41f099664c2090b7e42a9bef66a68d9`.
This is a development compile-check, not an ADR 0040 promoted artifact; nothing
was flashed or transmitted.

The Rigol DG1000Z manual establishes that DG1022Z has only two independent
arbitrary outputs. Its two rear Sync connectors can provide TTL repetition
timing, but an arbitrary waveform produces a 50 percent duty square rather than
a copy of its internal shape; the current AC-coupled peak input may detect both
square-wave edges. Exact waveform following therefore needs an
analog monitor copy; a passive BNC T is an acceptable high-impedance no-human
bench tap but is not acceptable evidence for a body-connected ceremony. Added
`docs/howto/DG1022Z_PUCA_HEARTBEAT.md` with the initial gain staging, clipping
checks, and a hard requirement for a qualified, separately isolated monitor
boundary before PUCA, Eurorack, USB, inverter, or Tree grounds approach the
human-connected circuit. Hardware line-in, waveform/light fidelity, RF, and
isolation acceptance remain open.

## 2026-08-26 -- Ben + Codex -- 120/3 energy decision moved to theory gate

Ben confirmed there is no INA instrumentation at the Burning Man camp, so the
Akuma cadence decision cannot depend on an unavailable empirical current test.
Replaced that field blocker with an explicit break-even model. Let `b` be the
fixed boot/setup energy expressed as the equivalent number of seconds at the
ordinary awake/listening power. Comparing full cycle active fractions,
`(b+3)/(120+b+3)` for the canary and `(b+15)/(300+b+15)` for production, gives
an exact break-even at `b=5 s`. The 120/3 recipe uses less awake energy when
`b<5 s`, the same at 5 s, and more when `b>5 s`.

Akuma's passive T-Deck evidence placed a post-deep-sleep heartbeat at about
1.1 s uptime, after board/sensor/radio initialization. Even treating that boot
interval as 2-3x the steady awake power gives roughly 2.2-3.3 awake-equivalent
seconds, still below the 5-second boundary. At `b=1.1 s`, the idealized awake
fractions are about 3.3 percent for 120/3 versus 5.1 percent for 300/15, about
35 percent lower; at a conservative `b=3 s`, 120/3 is still about 16 percent
lower. Sleep current is already known to be sub-mA and does not reverse this
comparison. Therefore the field recommendation is to treat 120/3 as likely an
energy improvement, not merely a responsiveness improvement, while retaining
the honest uncertainty of a theory-based estimate. Promote by staged fleet
observation of census/reachability rather than an INA gate that cannot be run
onsite.

## 2026-08-26 -- Ben + Codex -- Akuma 120/3 maintenance catch passed 3/3

Removed only Akuma `9E668C` from USB and left the T-Deck on `COM152`. Turning
the panel face-down on reflective playa was not enough: live Akuma heartbeats
continued to report about 4.648 V / 538 mA, well above the ADR 0060 150 mA
surplus threshold. Adding opaque plastic reduced measured input first to 42 mA
and then 0 mA / supply-not-good. That immediate physical-to-telemetry transition,
together with the burned-in full MAC inventory, confirmed the handled fixture
was Akuma even though the requested visible identify did not light it.

The identify miss exposed a real operator-parity issue rather than an RF miss.
T-Deck Fleet UI identify explicitly requests a green blinking production-light
frame, but serial quick command `i9E668C:10` calls the legacy color-0 default,
which drives only the PowerFeather status LED hidden inside the enclosure. The
field manual currently describes the serial example as green; align or clearly
separate those commands before relying on laptop identify in the field.

After the low-input hysteresis and the existing software-boot grace expired,
Akuma entered the experimental 120-second day-charge sleep cadence. Sustained
exact-target `U9E668C` campaigns caught three clean timer wakes in 86.4, 100.9,
and 94.3 seconds (3/3; mean 93.9 s, maximum 100.9 s). HTTP telemetry became
available at fixture uptimes 3.746, 4.319, and 4.380 seconds. Each catch reported
`reset_reason=deepsleep`, `last_sleep_reason=day-charge`, `last_sleep_s=120`,
`day_sleep_s=120`, and `wake_listen_ms=3000`. Because WiFi association and HTTP
startup happen after the ESP-NOW command is accepted, the roughly 4-second HTTP
times are compatible with and prove command receipt inside the 3-second radio
window.

Two apparent early repeats were deliberately excluded: one caught the 10-minute
non-deep-sleep boot grace after a same-binary OTA, and one caught a still-active
35-second T-Deck maintenance tail. The clean trials waited out each RF tail,
called `/resume`, confirmed the maintenance endpoint remained closed, and then
started from a real timer sleep. After the third pass, `/resume` again succeeded
and the endpoint remained closed for 12 seconds, returning Akuma to natural
cadence. No other fixture ID was commanded or flashed; fleet cadence remains
300/15 and the fleet still runs its prior immutable image.

The 3-second window is therefore a promising command-reachability setting on
this canary, but it is not yet an energy result. A 120-second sleeper wakes 2.5x
as often as a 300-second sleeper, so fixed boot/sensor/radio cost can erase the
listen-time savings. Use the INA logger to compare complete cycle charge before
fleet promotion. The session also showed temporally contradictory T-Deck and
direct same-revision records while modes were changing; exact cause remains
unproven, so keep the verifier fail-closed and reproduce with synchronized raw
serial, USB, and HTTP evidence rather than labeling it a cache bug prematurely.

## 2026-08-26 -- Ben + Codex -- Sound-to-photon latency development plan

Made reactive latency and cross-fixture skew explicit artistic requirements and
added `docs/projects/LOW_LATENCY_AUDIO_REACTIVITY_DEV_PLAN.md`. The plan separates
an immediate CoreS3-only path from a gated future fixture path. The immediate
work measures true sound-to-photon median/p95/max, fixes the spectral source's
nominal 10 Hz publisher quantizing to 8.3 Hz, decouples capture/analysis/TX/UI,
adds an 8 ms transient lane beside the rolling 512-sample FFT, and measures how
far faster direct publishing can improve the existing 10 Hz fixture latch.

The future path is conditional on those measurements. It proposes one compact
fleet-size-independent audio-feature broadcast, local audio mapping, and an
event-driven/50 Hz fixture latch only while a fresh Audio lease is active. It
includes old/new mixed-fleet capability handling, fast missing-stream decay,
native wire/lease tests, physical HEX/RGBW USB canaries, 130/150-node RF gates,
LFP soak, and ADR 0040 staged promotion. No firmware was changed, built, flashed,
or transmitted as part of the planning session; no fixture OTA was authorized.
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
