beneckart/resonance-lighting/ROADMAP.md

# Roadmap

## Post-event entry point (2026-10-06)

The [2026 postmortem and 2027 future-work index](docs/postmortem/README.md)
collects field evidence, storage firmware, unresolved recovery behavior and
hardware/service-access brainstorming. Use it with [TODO](TODO.md) for the next
cycle; no custom power platform has been selected. The phase plan below is
retained as the 2026 delivery baseline, not a fresh claim about current status.

Phases of work for the Resonance Lighting workstream, working backwards from Burning Man
2026.

**Hard deadline:** all nominally 130 fixtures (four classes -- see the fleet table in
`docs/block-diagram/SYSTEM.md`) must be in hand and operational by about Aug 20 --
**the container loads in Nevada City on Aug 21**.

Project-wide anchor dates (gold standard: https://resonancenetwork.org/camp,
corroborated 2026-07-08): container lands Port of Oakland **Jul 12**; NC prebuild at
Bodhi Hive, Nevada City **Jul 31 - Aug 19**; all-hands container unload **Aug 1-2**;
**lights + camp systems team build Aug 8-9**; container load **Aug 21**; early crews
roll Aug 22-24; gates open Aug 30; burn night Sep 5. (Earlier repo docs said "Grass
Valley" for the staging area; the site pins it as Bodhi Hive, Nevada City.)
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
