beneckart/resonance-lighting/CORTEX.md

# Resonance Tree — Lighting Cortex (controller / show system)

**v1.0 “Emergence”** — the first complete release: the full digital twin + control
system, runnable by anyone from a fresh clone (below), sound included, offline-capable.
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
