beneckart/resonance-lighting/ops/bench/data/ca/2026-06-02-ca-liion-4400-soc_v.png

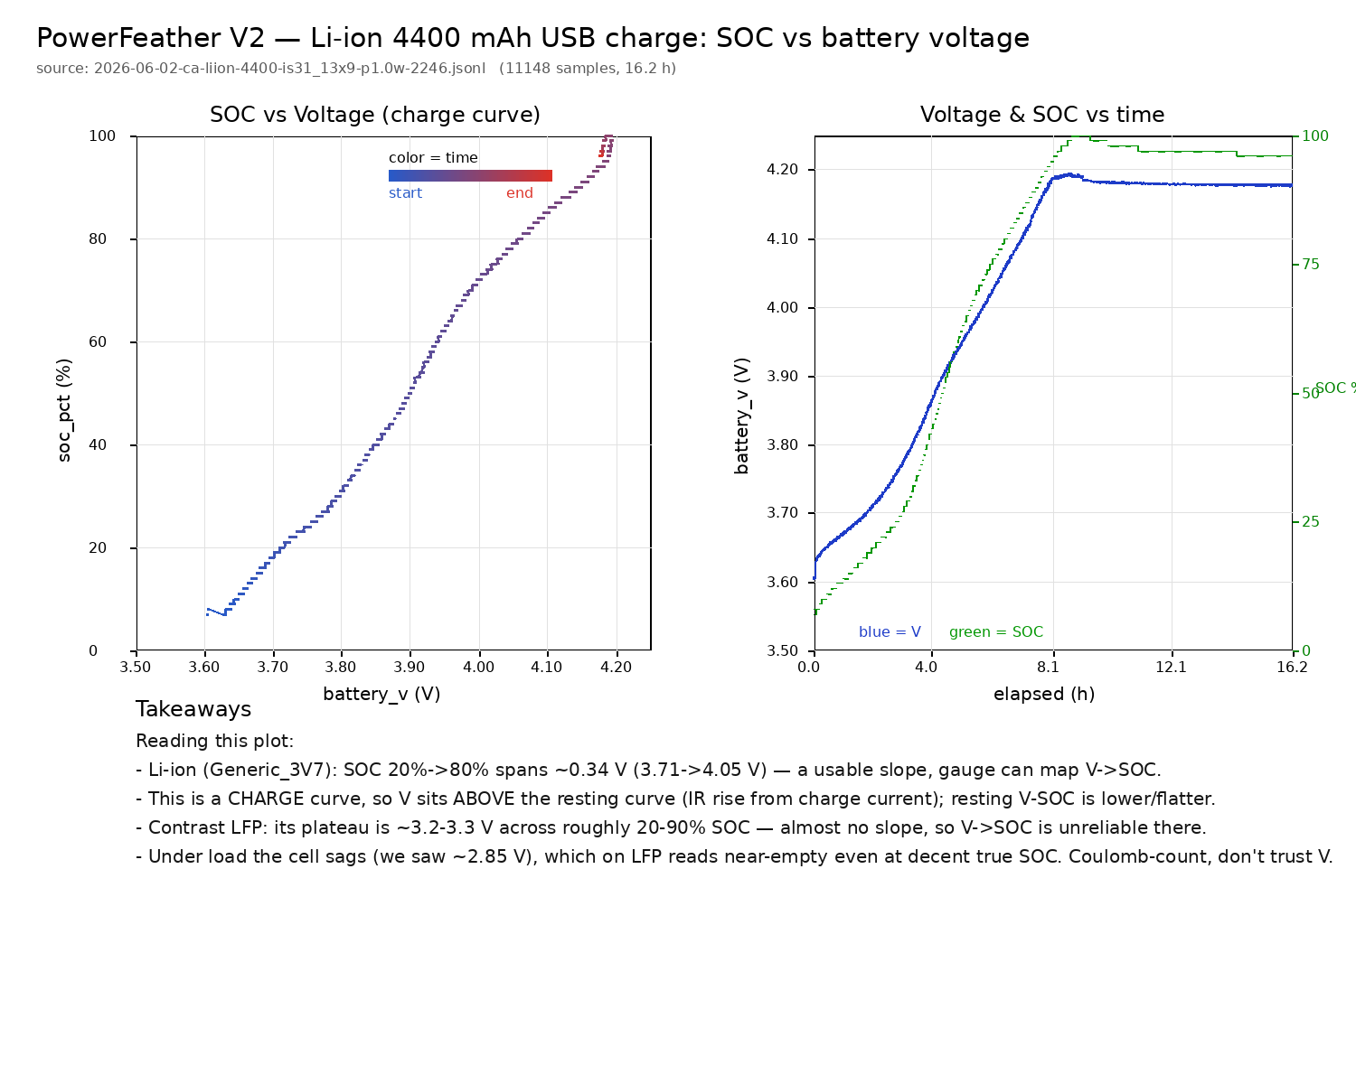
ops/bench/data/ca/2026-06-02-ca-liion-4400-soc_v.png
