beneckart/resonance-lighting/ops/bench/data/ca/2026-06-03-ca-lfp-overnight-soc_v.png

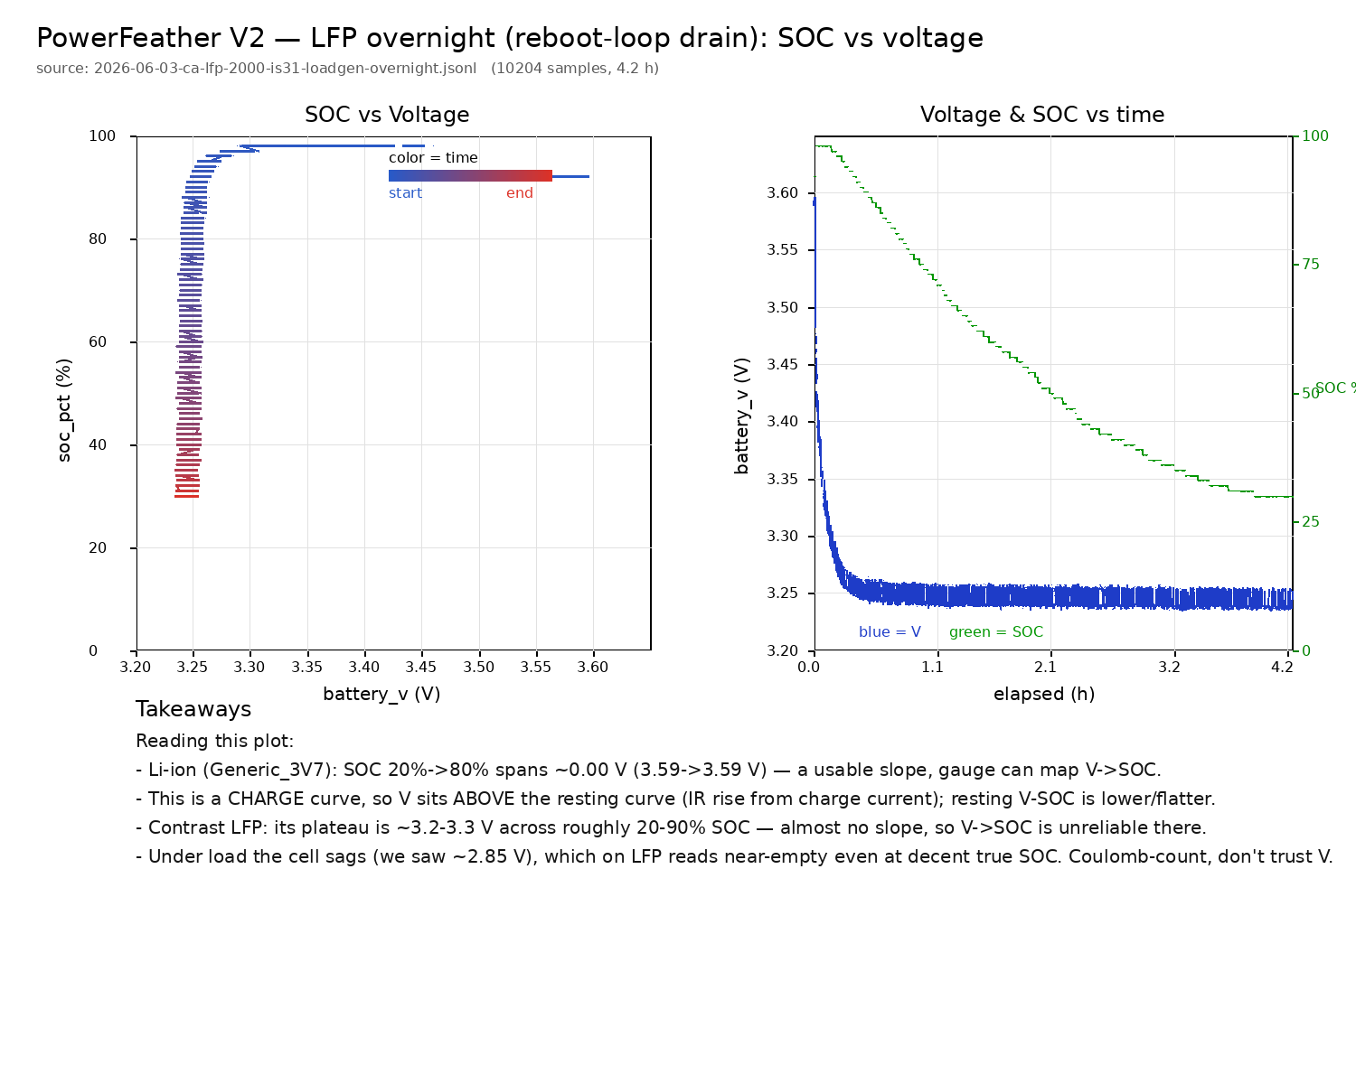
ops/bench/data/ca/2026-06-03-ca-lfp-overnight-soc_v.png
