beneckart/resonance-lighting/ops/bench/data/ca/2026-06-08-rangewalk.png

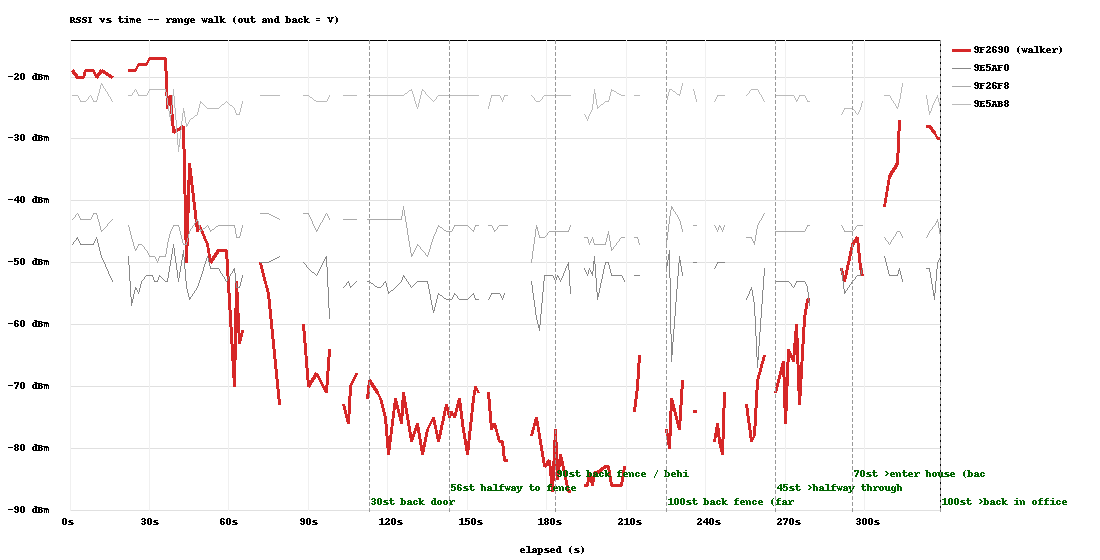
ops/bench/data/ca/2026-06-08-rangewalk.png
