beneckart/resonance-lighting/ops/bench/data/ca/2026-06-09-led-ina-sweep-2247-x10.png

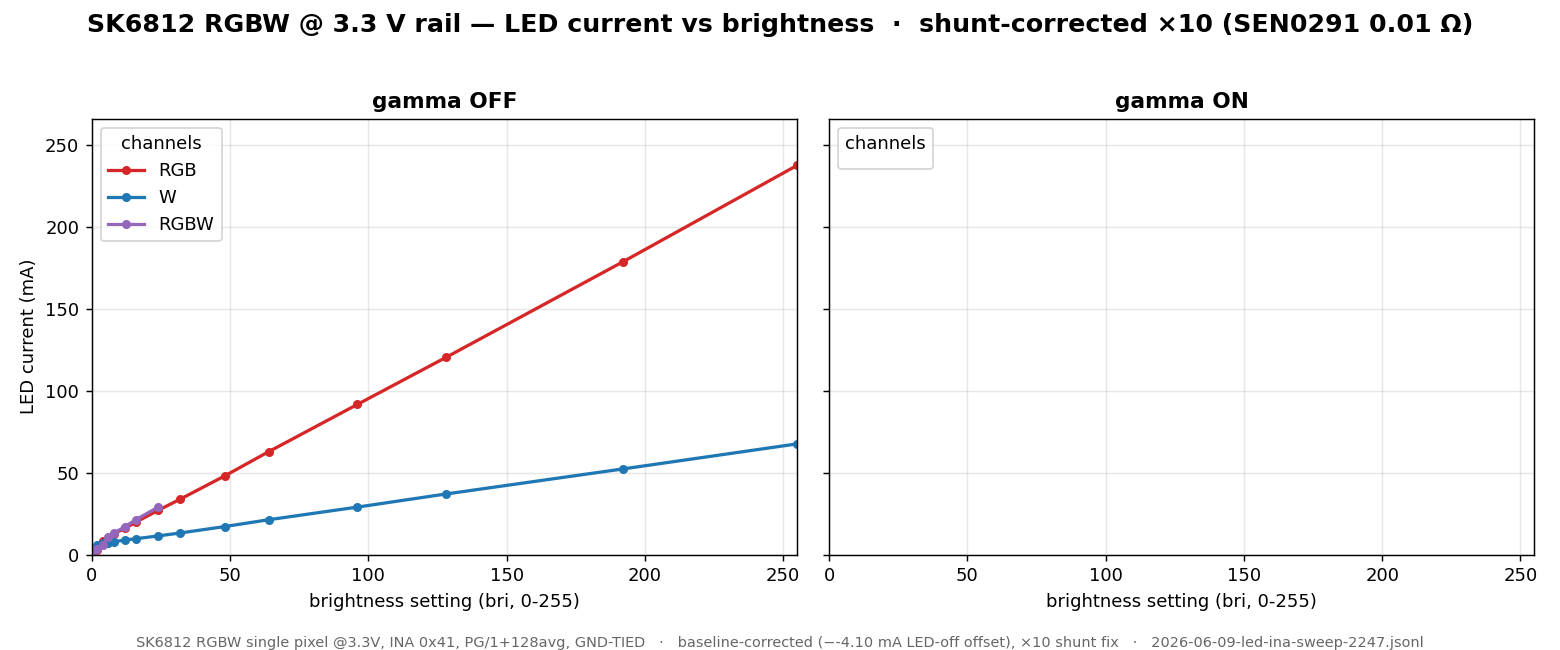
ops/bench/data/ca/2026-06-09-led-ina-sweep-2247-x10.png
