beneckart/resonance-lighting/ops/bench/data/ca/2026-06-10-afk-sweep-0031-power.png

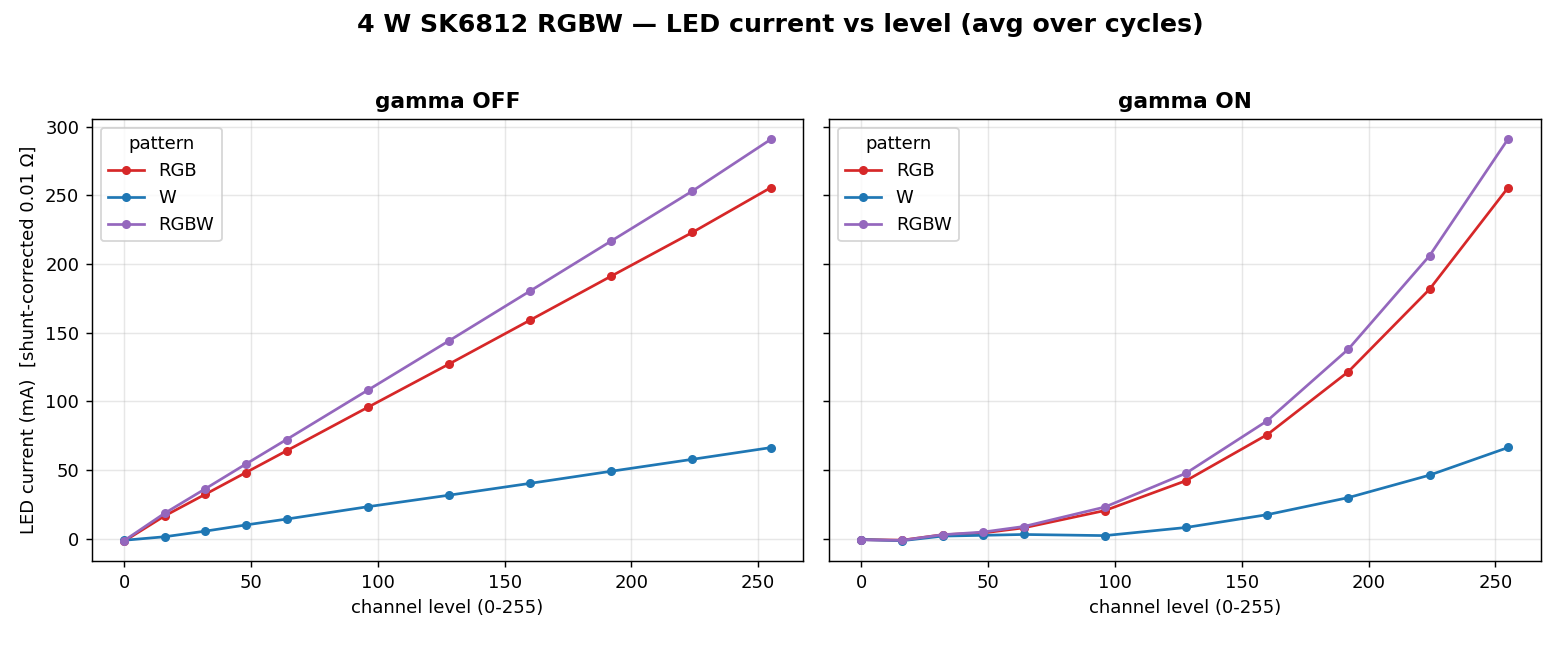
ops/bench/data/ca/2026-06-10-afk-sweep-0031-power.png
