beneckart/resonance-lighting/ops/bench/data/ca/2026-06-10-discharge-1357-bb-eff.png

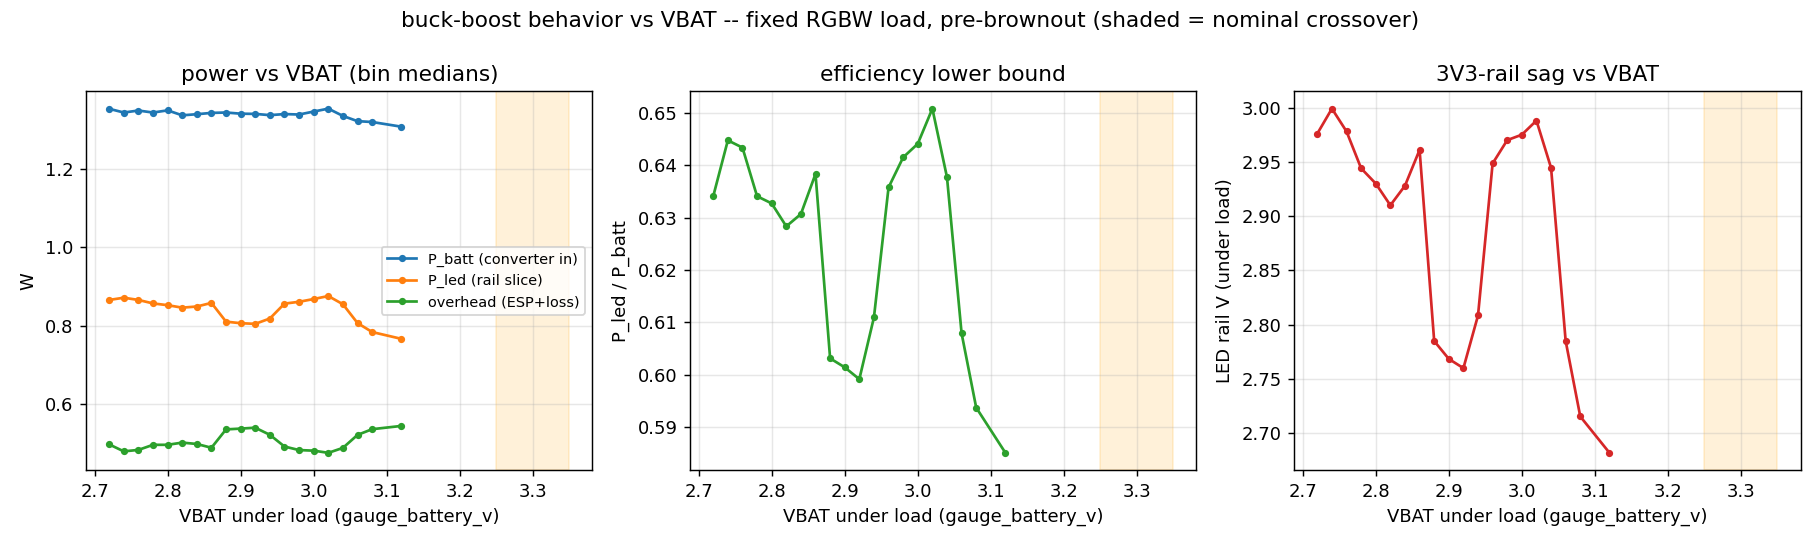
ops/bench/data/ca/2026-06-10-discharge-1357-bb-eff.png
