beneckart/resonance-lighting/ops/bench/data/ca/2026-06-11-afk-sweep-0028-gauge.png

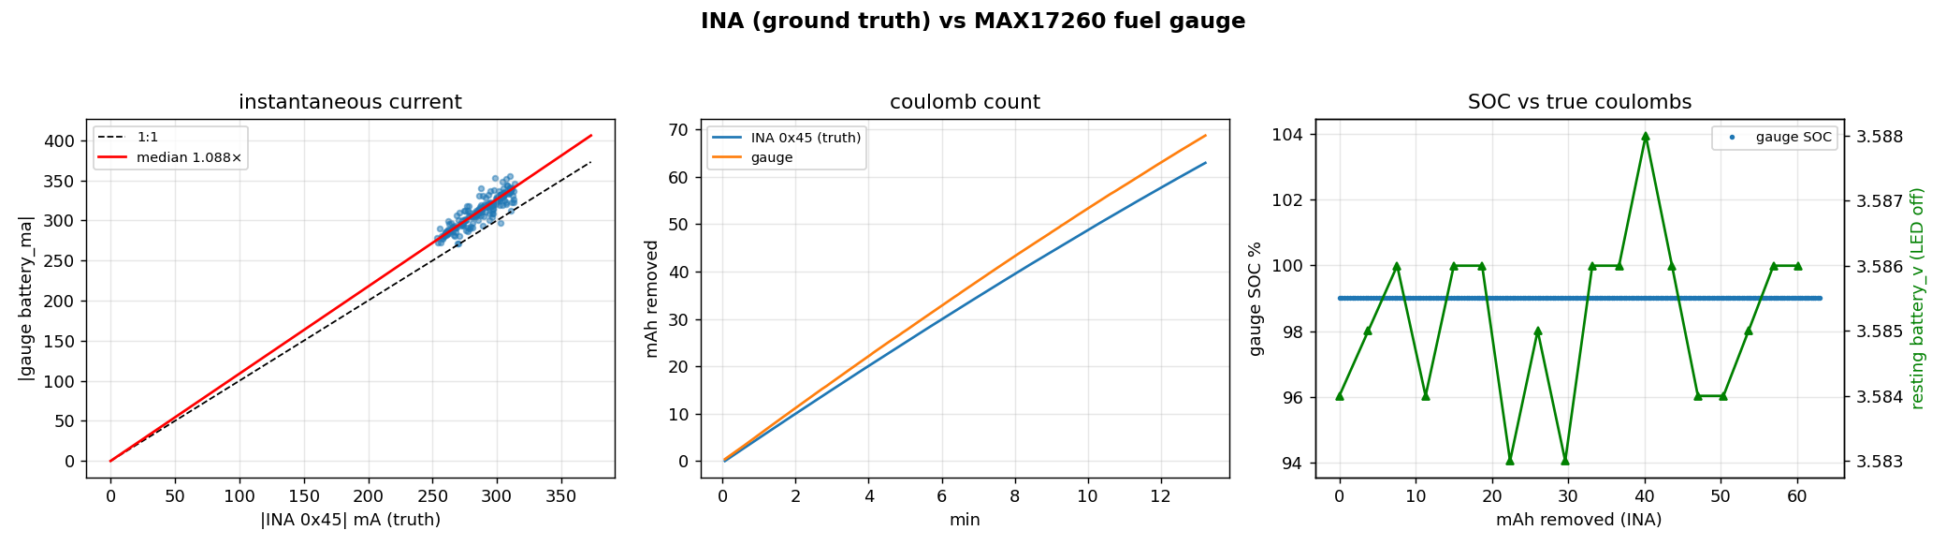
ops/bench/data/ca/2026-06-11-afk-sweep-0028-gauge.png
