beneckart/resonance-lighting/ops/bench/data/ca/2026-06-11-discharge-1717-gauge.png

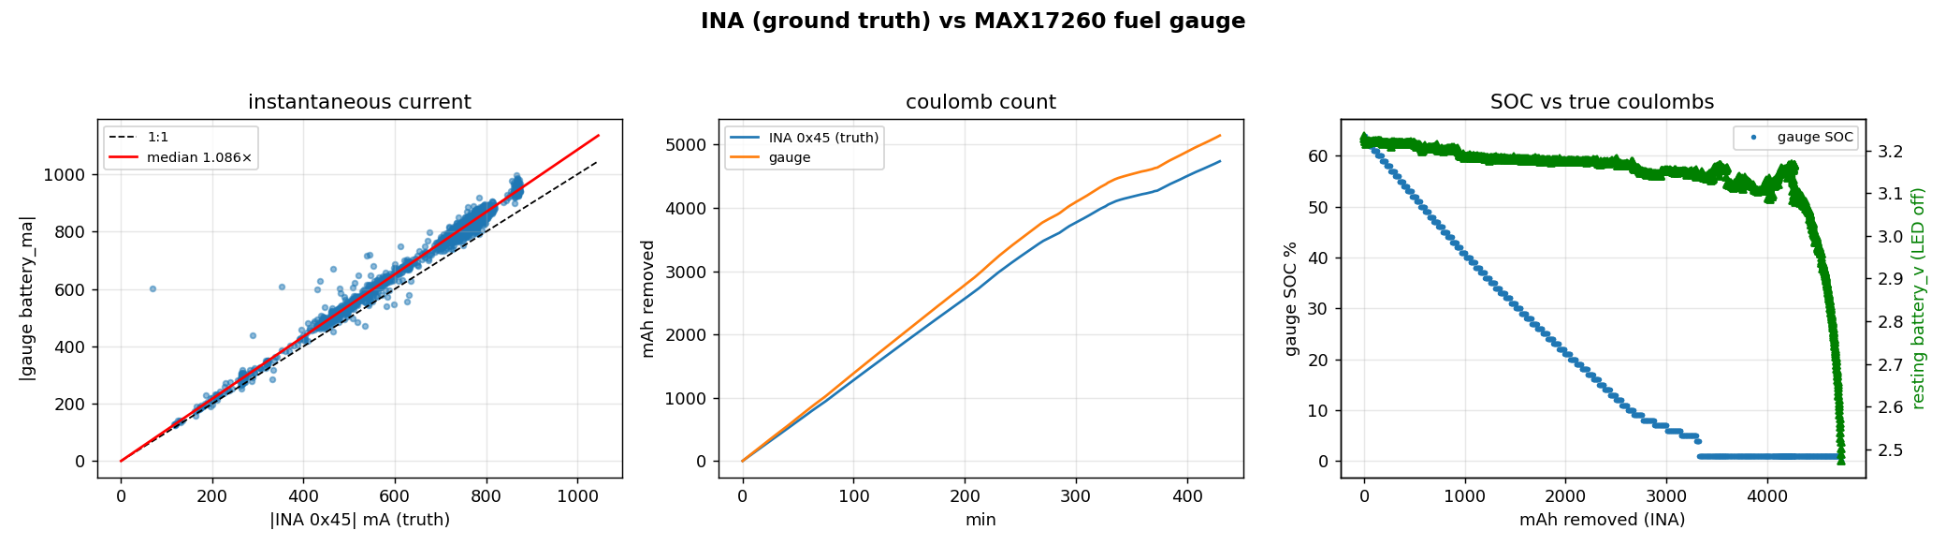
ops/bench/data/ca/2026-06-11-discharge-1717-gauge.png
