beneckart/resonance-lighting/ops/bench/data/ca/2026-06-11-mpp-sweep-hot-pm-knee-2245-curve.png

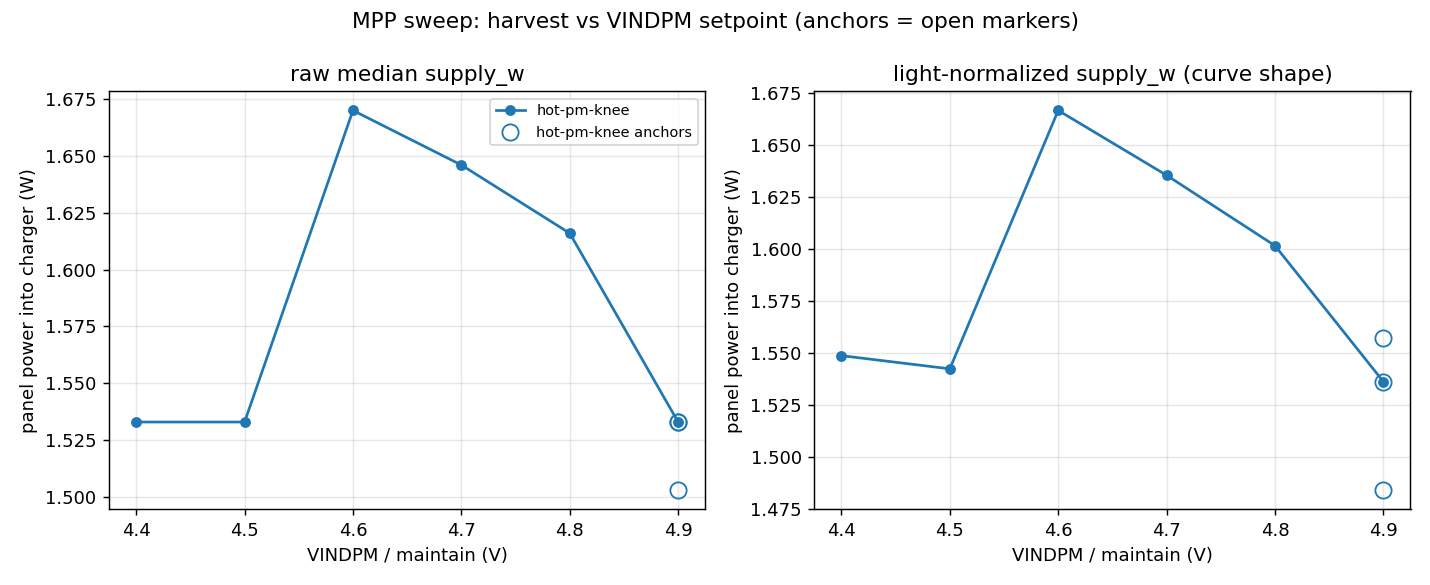
ops/bench/data/ca/2026-06-11-mpp-sweep-hot-pm-knee-2245-curve.png
