beneckart/resonance-lighting/ops/bench/data/ca/2026-07-06-discharge-F-cycle1-gauge.png

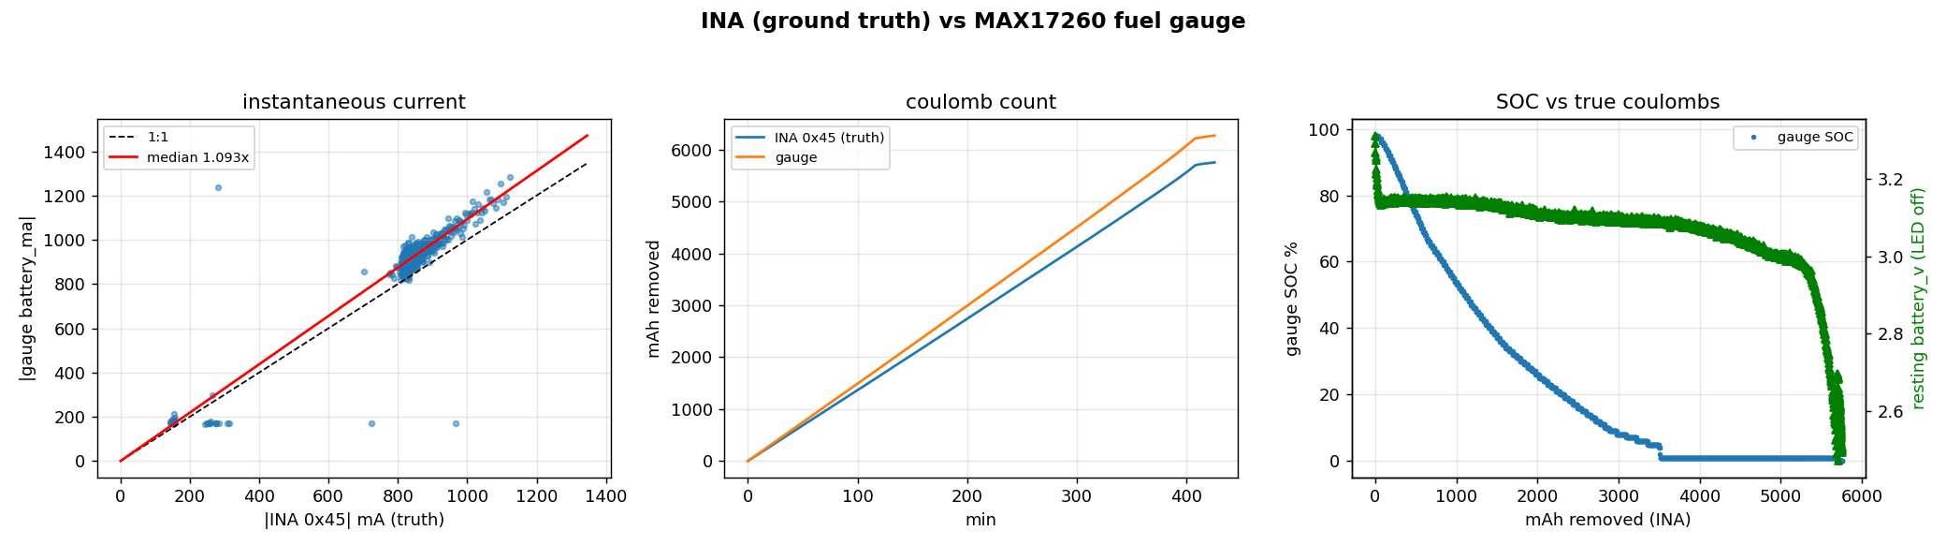
ops/bench/data/ca/2026-07-06-discharge-F-cycle1-gauge.png
