beneckart/resonance-lighting/ops/bench/data/ca/2026-07-11-discharge-20ah-cycle1-gauge.png

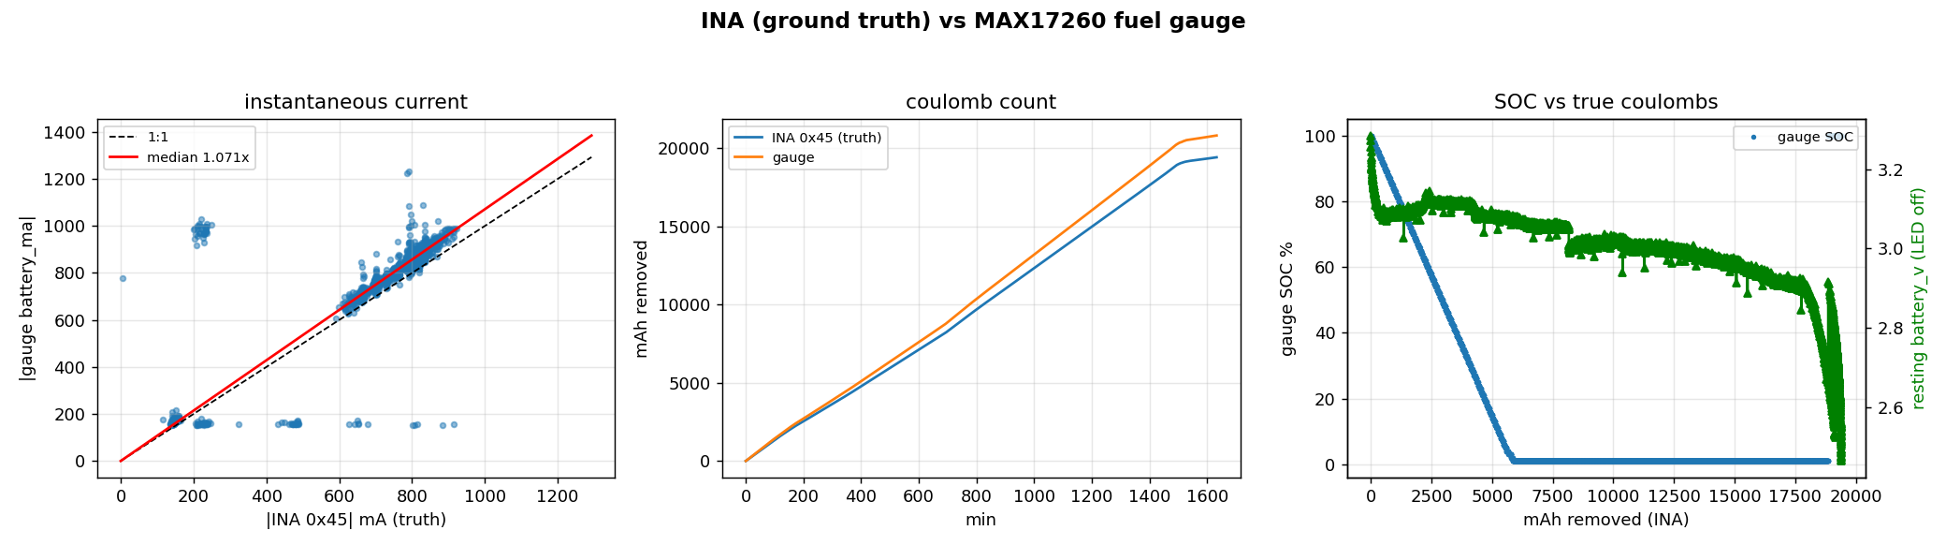
ops/bench/data/ca/2026-07-11-discharge-20ah-cycle1-gauge.png
