beneckart/resonance-lighting/ops/bench/data/ca/led-eff-3way.png

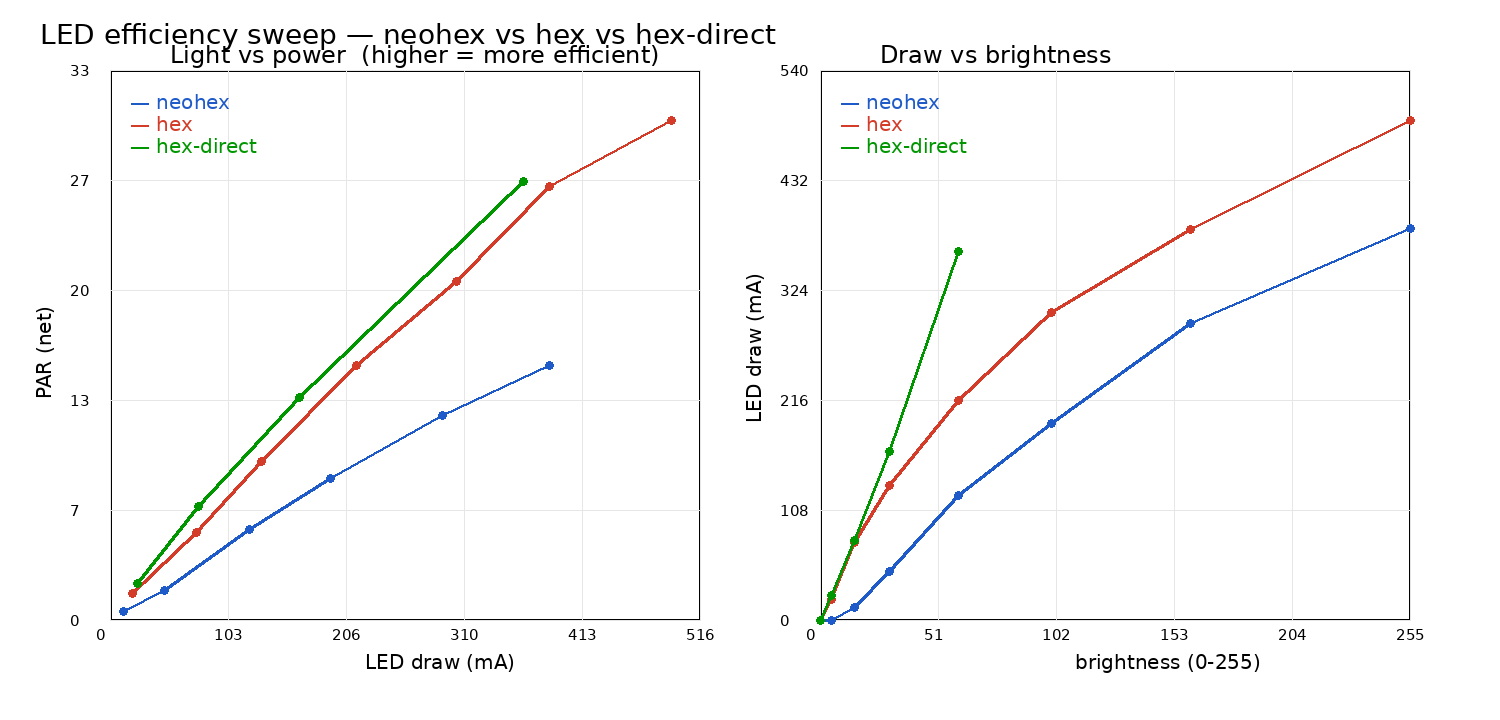
ops/bench/data/ca/led-eff-3way.png
