beneckart/resonance-lighting/ops/bench/data/ca/led-eff-compare.png

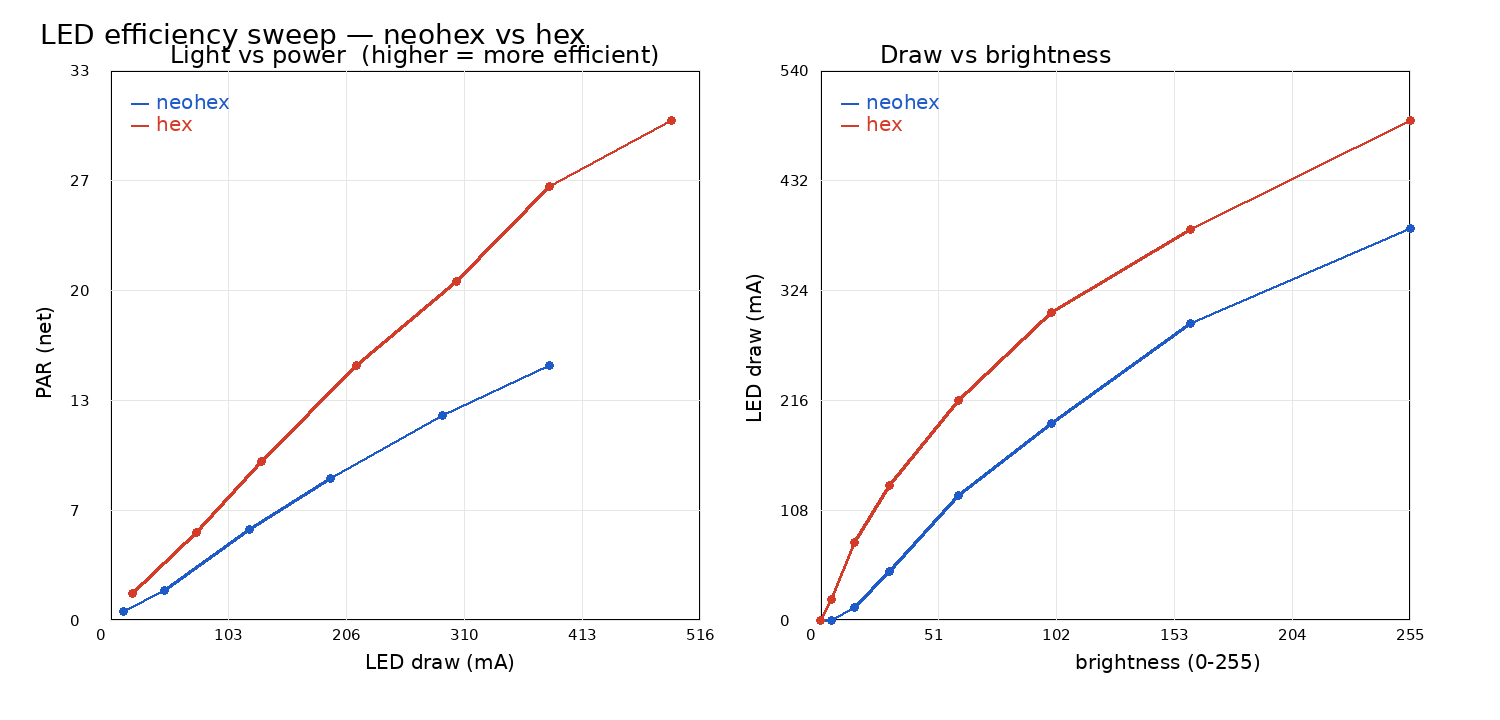
ops/bench/data/ca/led-eff-compare.png
