beneckart/resonance-lighting/ops/bench/data/ca/led-par-vs-draw.png

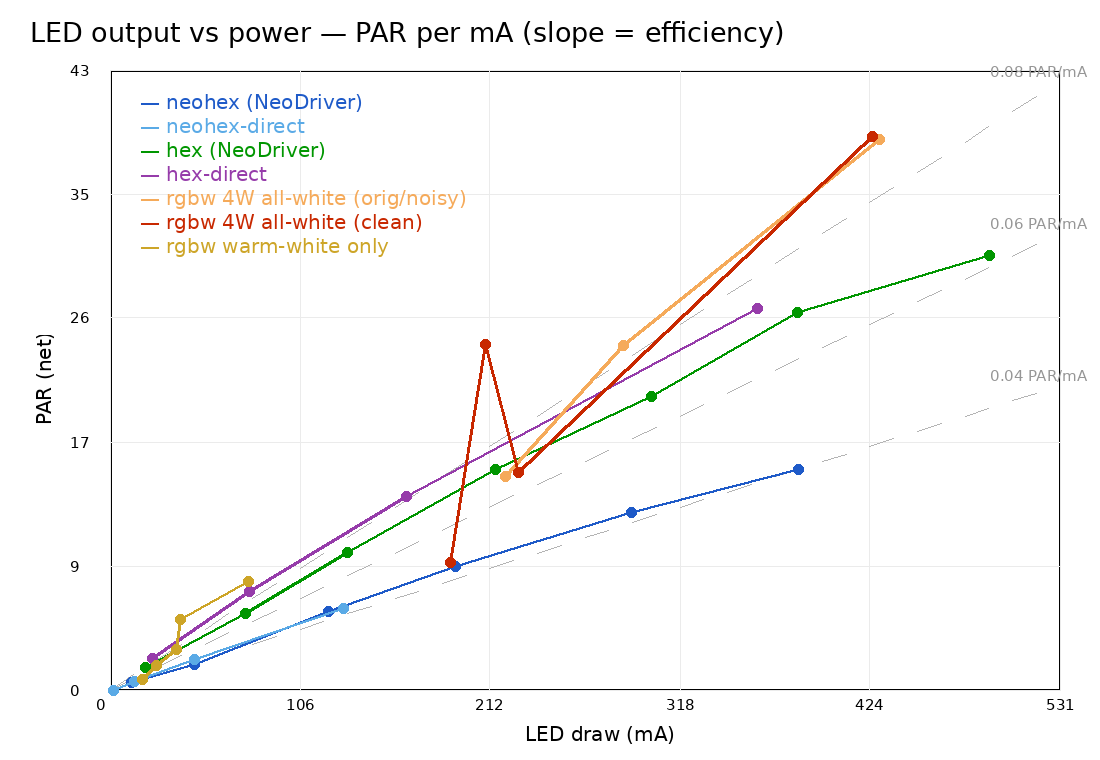
ops/bench/data/ca/led-par-vs-draw.png
