beneckart/resonance-lighting/ops/bench/data/ca/plots/2026-07-01-field-cycle-overview.png

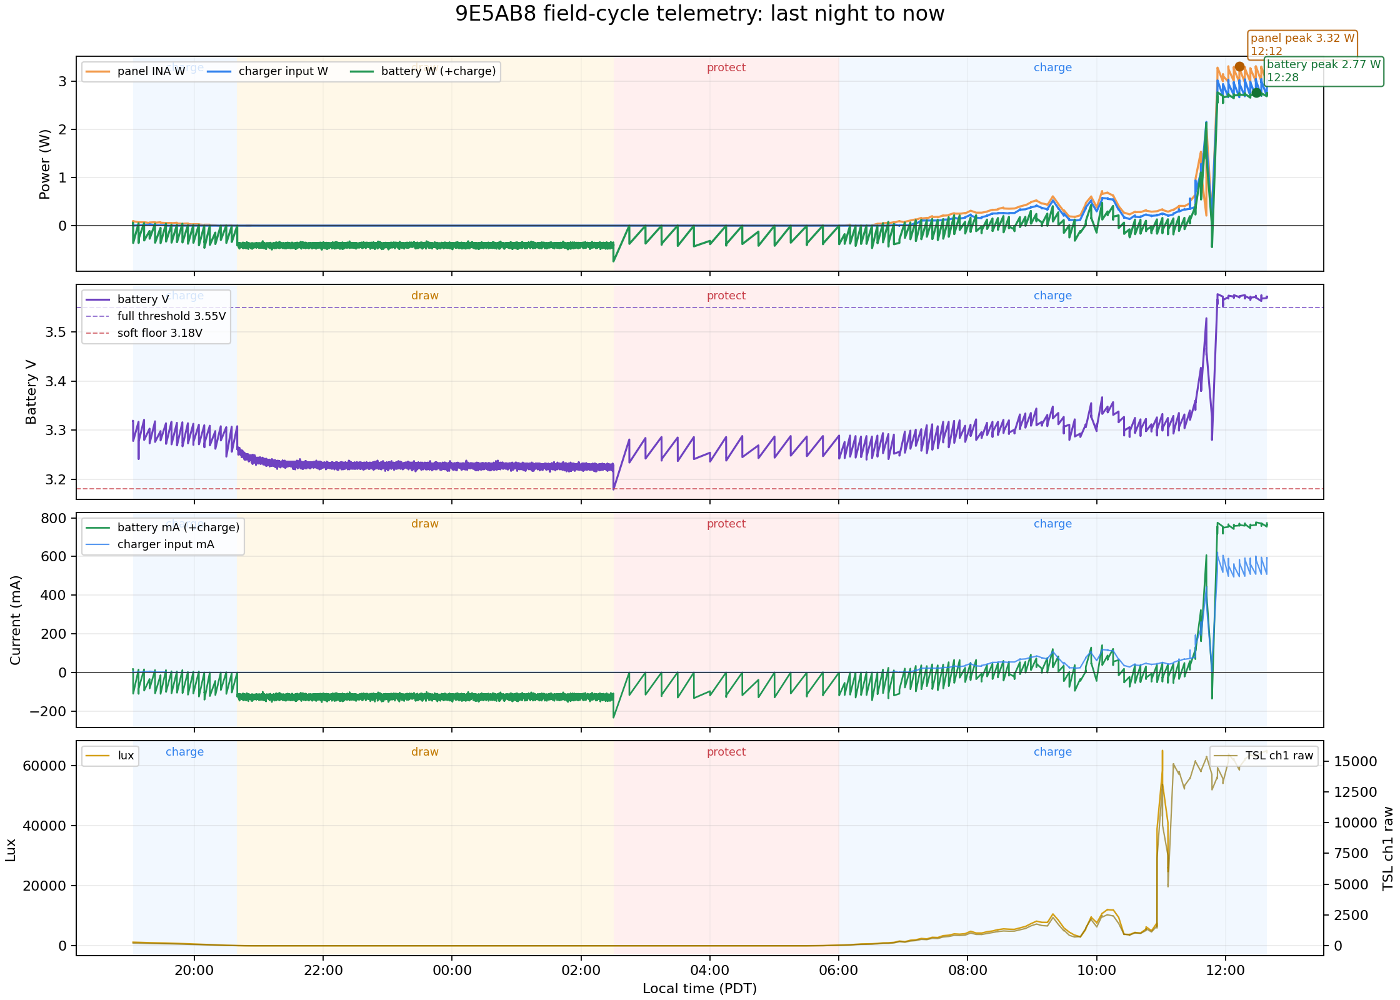
ops/bench/data/ca/plots/2026-07-01-field-cycle-overview.png
