beneckart/resonance-lighting/ops/bench/data/ca/plots/2026-07-08-09-field-cycle-daynight.png

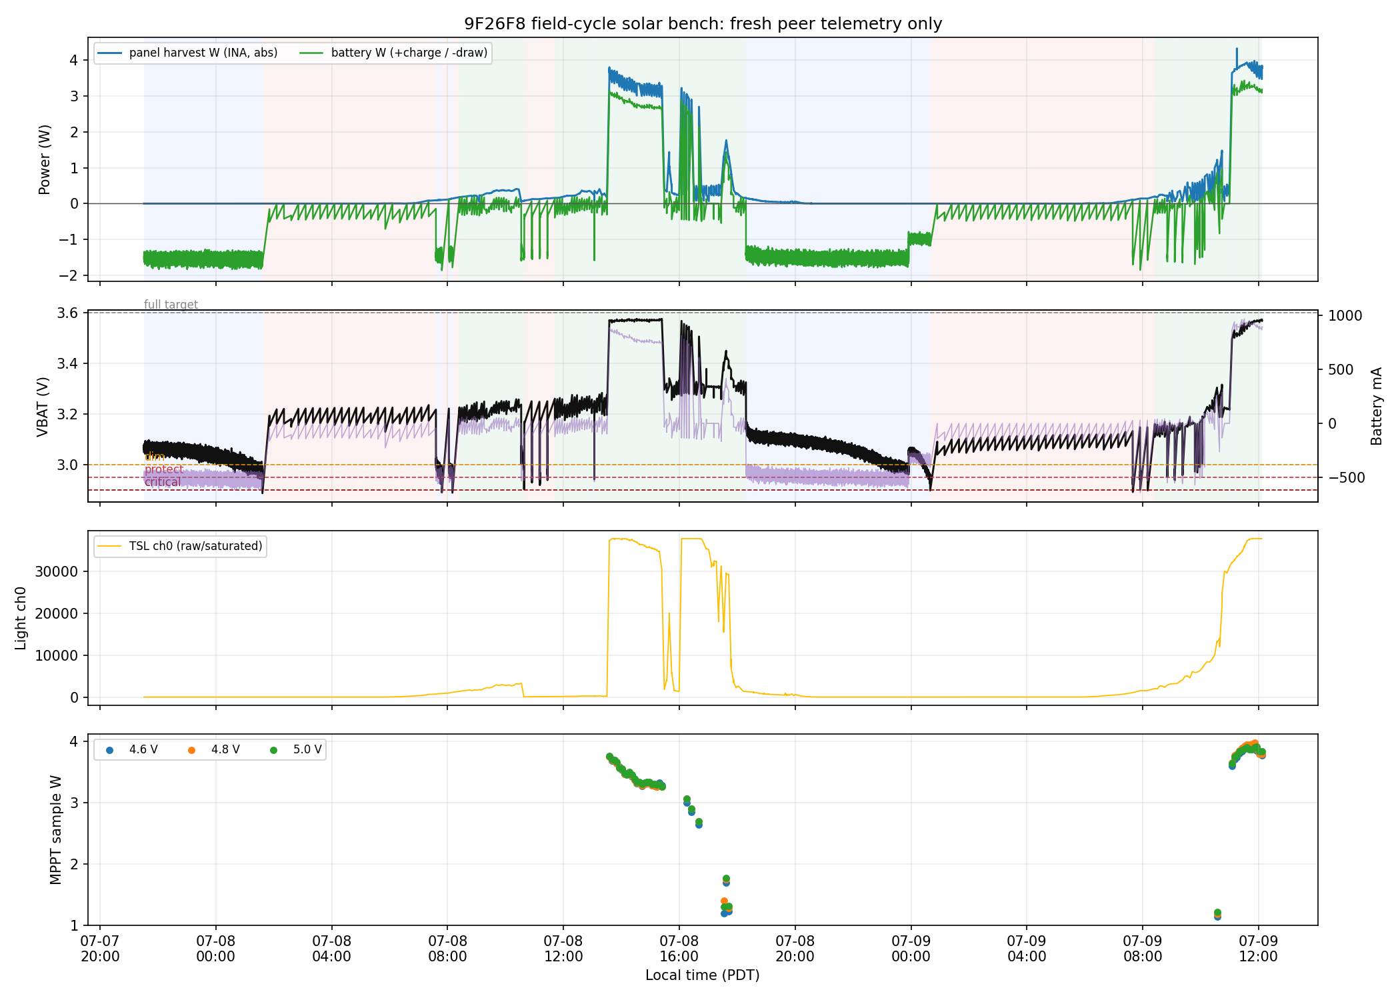
ops/bench/data/ca/plots/2026-07-08-09-field-cycle-daynight.png
