beneckart/resonance-lighting/ops/bench/data/ca/plots/2026-07-08-10-field-cycle-daynight-extended.png

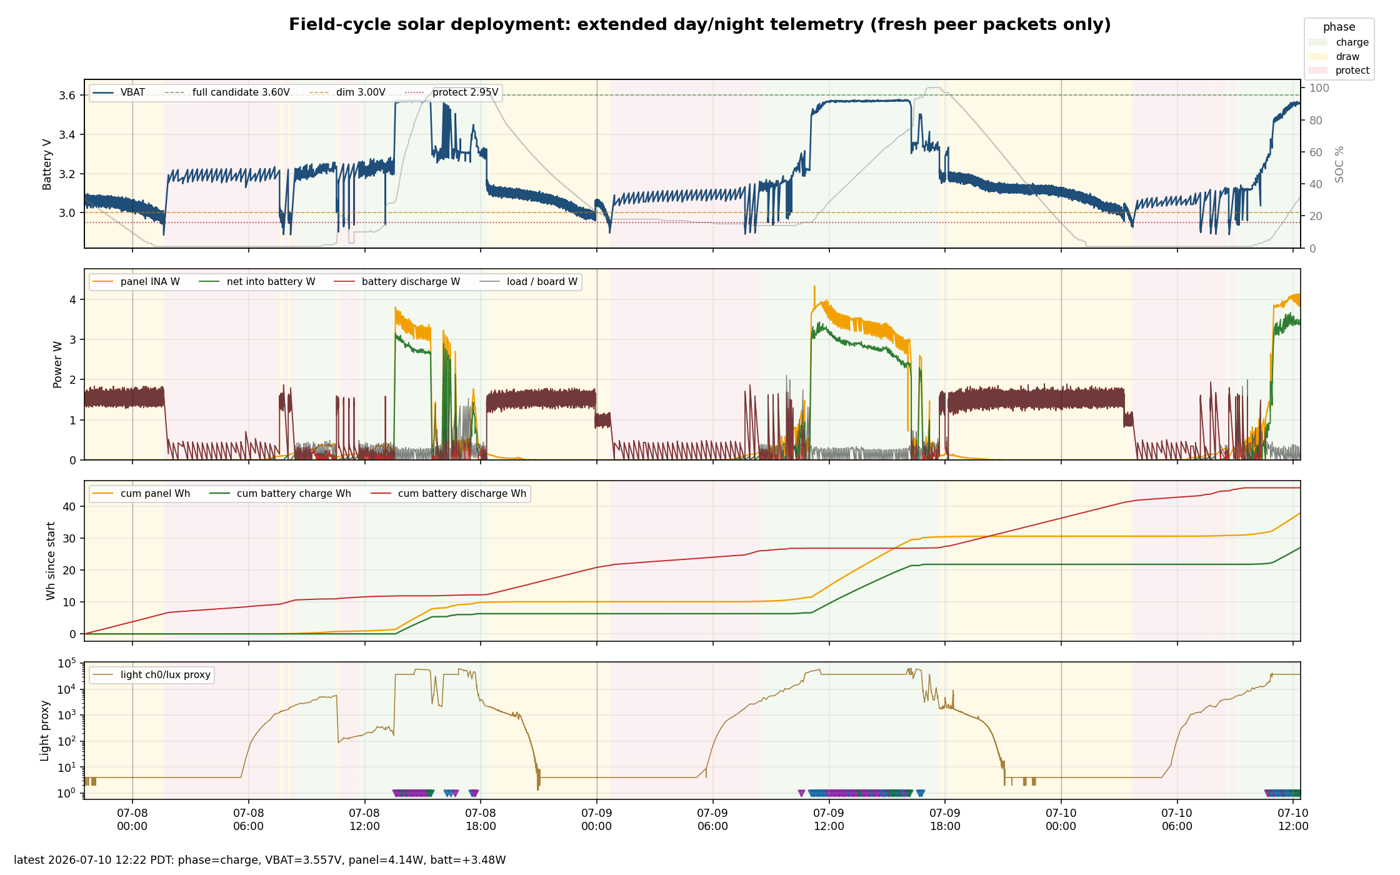
ops/bench/data/ca/plots/2026-07-08-10-field-cycle-daynight-extended.png
