beneckart/resonance-lighting/ops/bench/data/ca/rgbw-undervolt.png

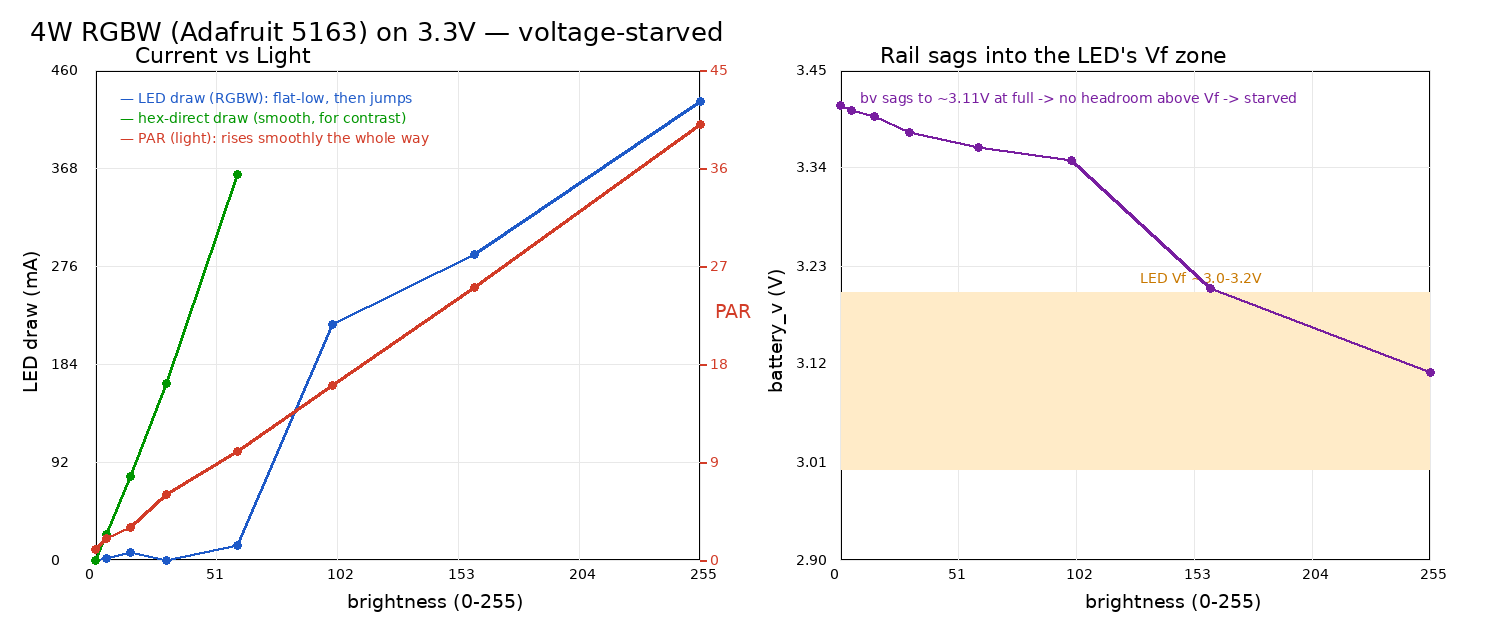
ops/bench/data/ca/rgbw-undervolt.png
