beneckart/resonance-lighting/ops/bench/data/solenoid-vdc-sweep-2026-07-11.png

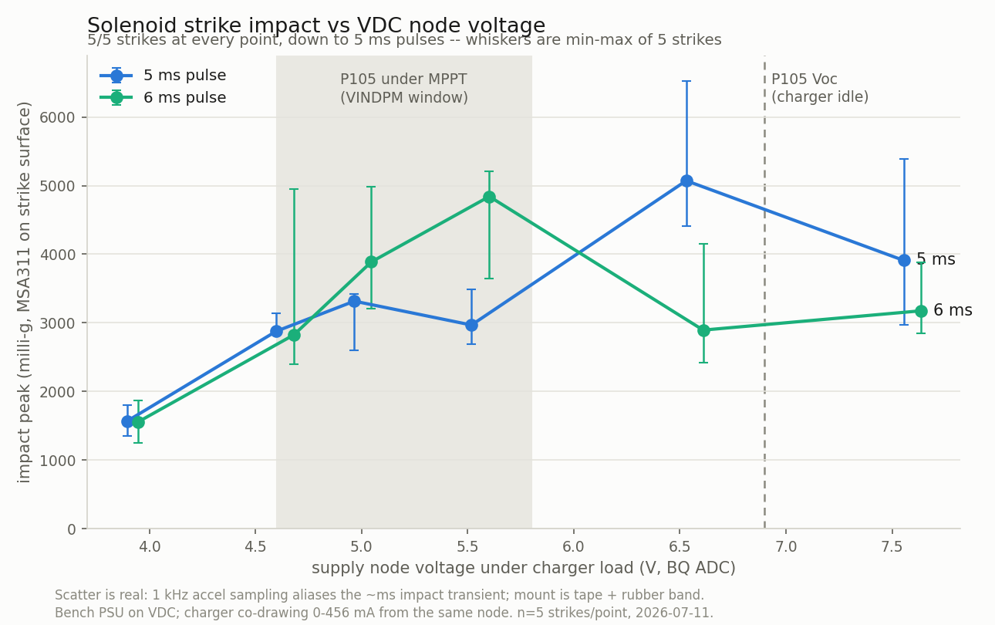
ops/bench/data/solenoid-vdc-sweep-2026-07-11.png
