beneckart/resonance-lighting/ops/bench/solenoid-comparison-2026-07-25/solenoid-comparison-preview.png

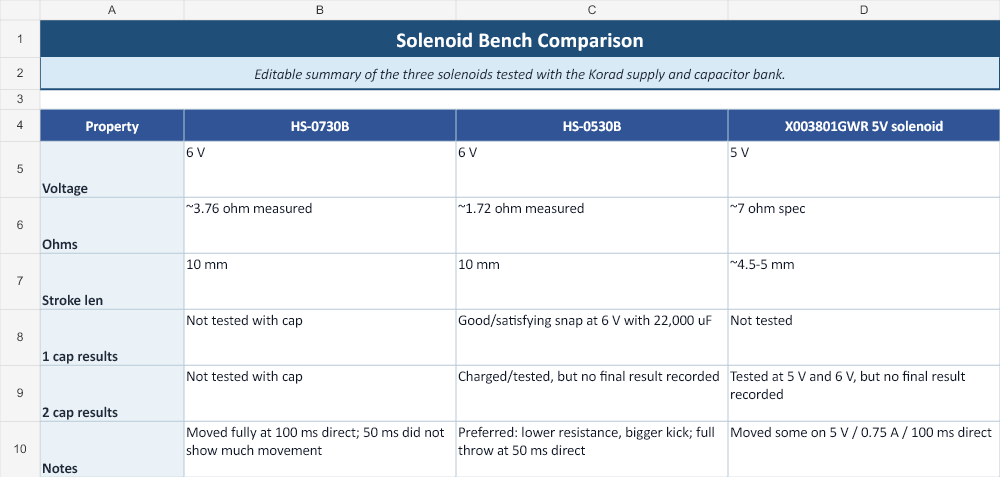
ops/bench/solenoid-comparison-2026-07-25/solenoid-comparison-preview.png
