beneckart/resonance-lighting/ops/locate/data/sim/2026-07-12-sim-sl4-s11-rssi.png

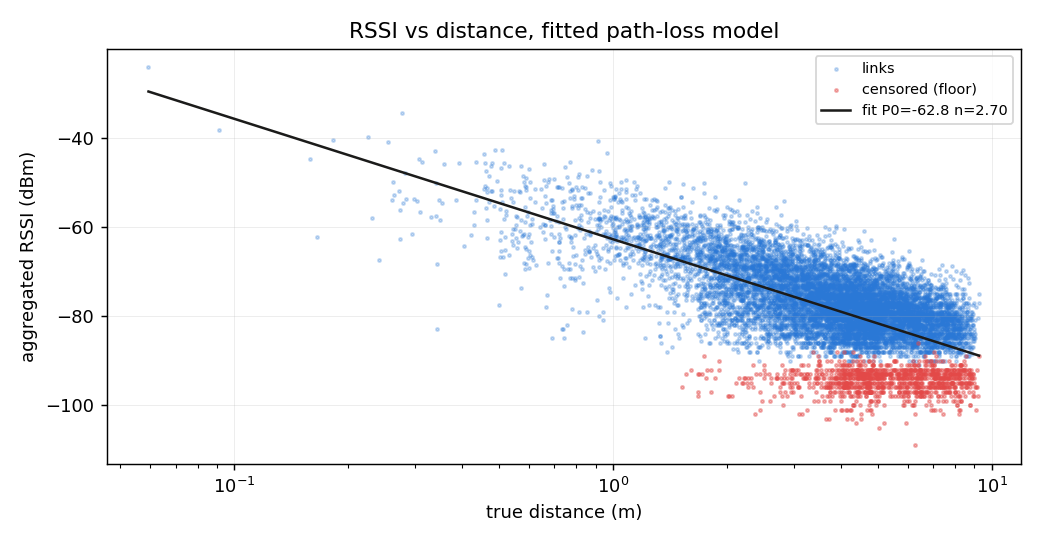
ops/locate/data/sim/2026-07-12-sim-sl4-s11-rssi.png
