beneckart/resonance-lighting/ops/locate/data/sim/2026-07-12-sweep-beacons.png

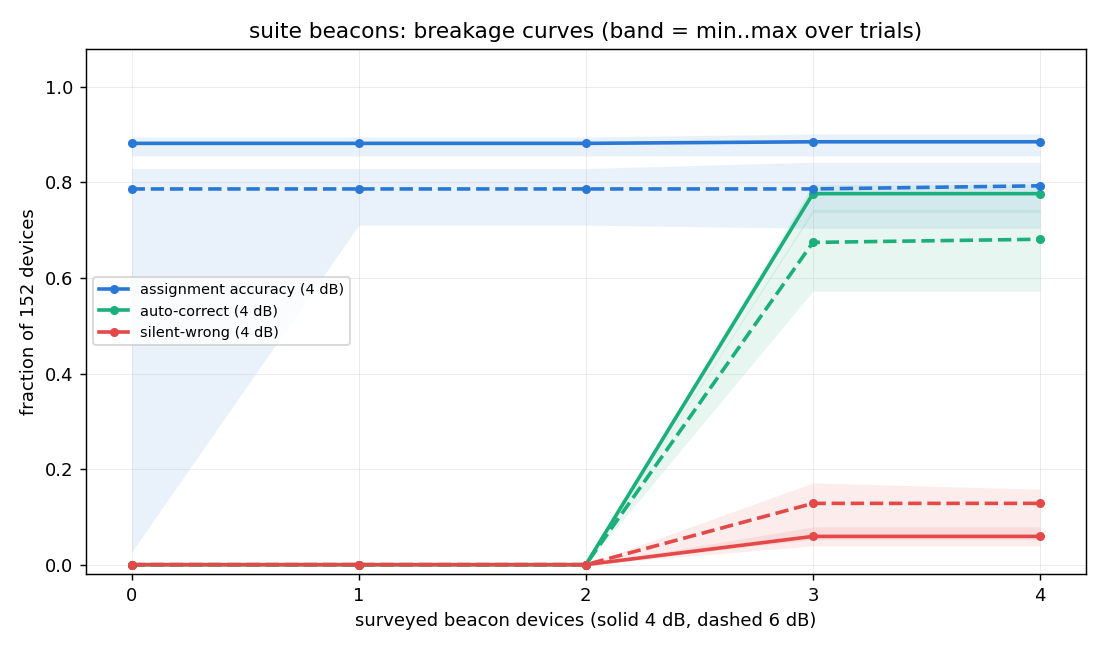
ops/locate/data/sim/2026-07-12-sweep-beacons.png
