beneckart/resonance-lighting/ops/locate/data/sim/2026-07-13-sim-sl4-s7-positions.png

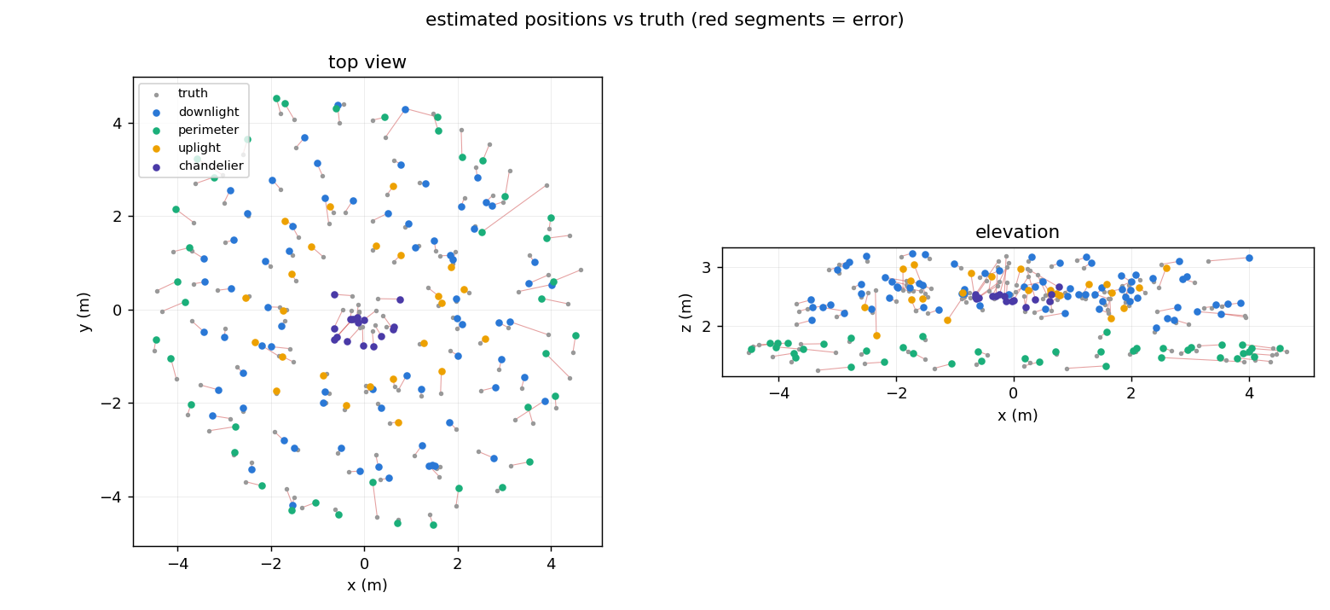
ops/locate/data/sim/2026-07-13-sim-sl4-s7-positions.png
