beneckart/resonance-lighting/ops/solarsim/data/figures/hinge_quadrants.png

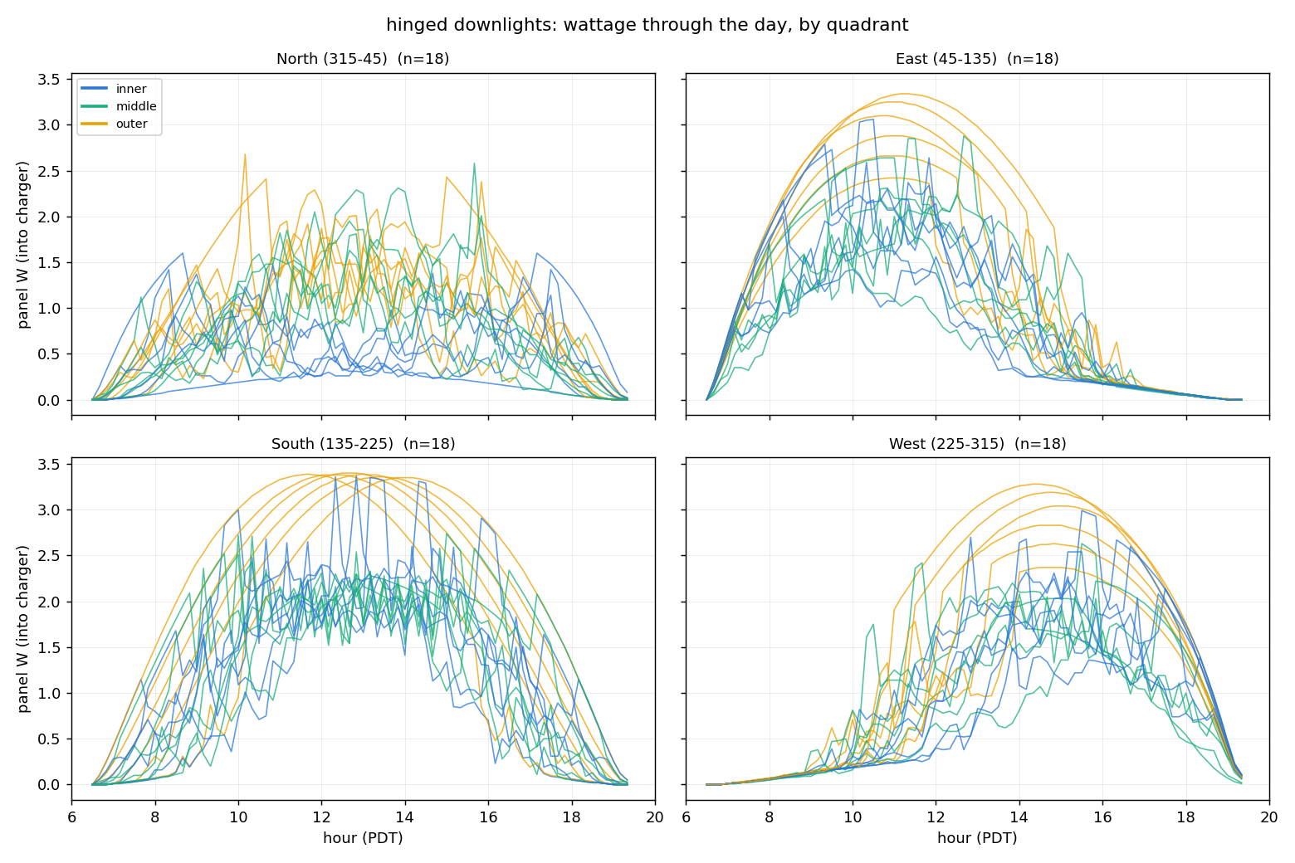
ops/solarsim/data/figures/hinge_quadrants.png
