beneckart/resonance-lighting/ops/solarsim/data/figures/hinge_sunplot.png

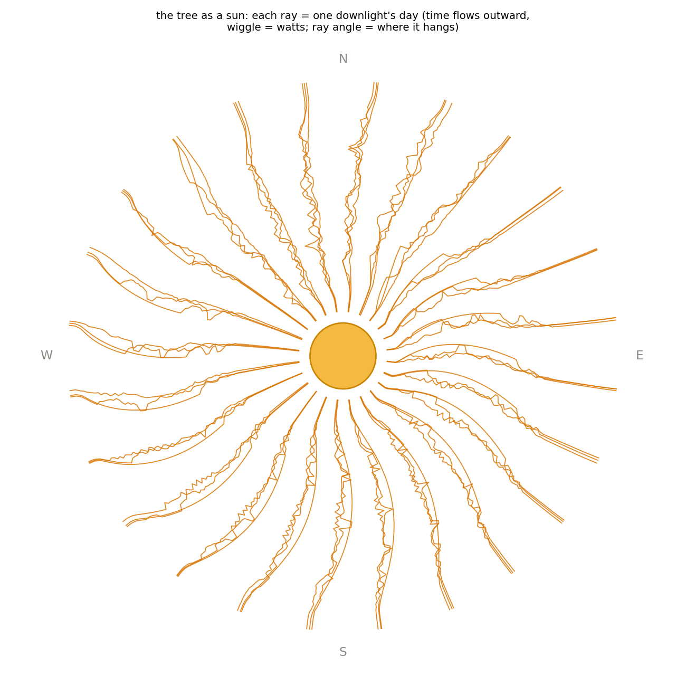
ops/solarsim/data/figures/hinge_sunplot.png
