beneckart/resonance-lighting/ops/solarsim/data/figures/hinge_sunplot_ember.png

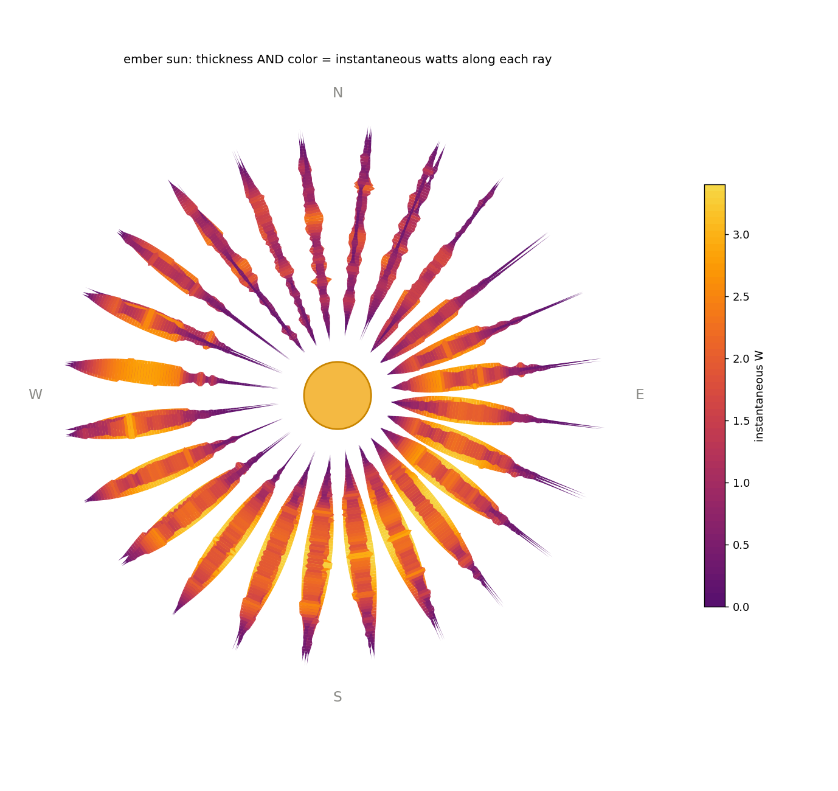
ops/solarsim/data/figures/hinge_sunplot_ember.png
