beneckart/resonance-lighting/ops/solarsim/data/figures/hinge_sunplot_ribbon.png

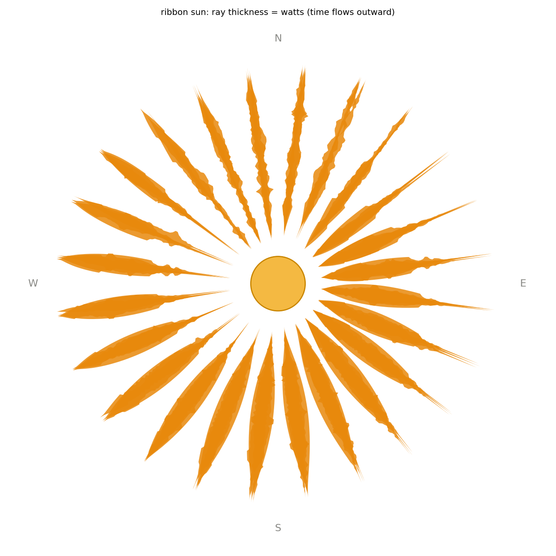
ops/solarsim/data/figures/hinge_sunplot_ribbon.png
