beneckart/resonance-lighting/ops/solarsim/data/figures/hinge_sunplot_rings.png

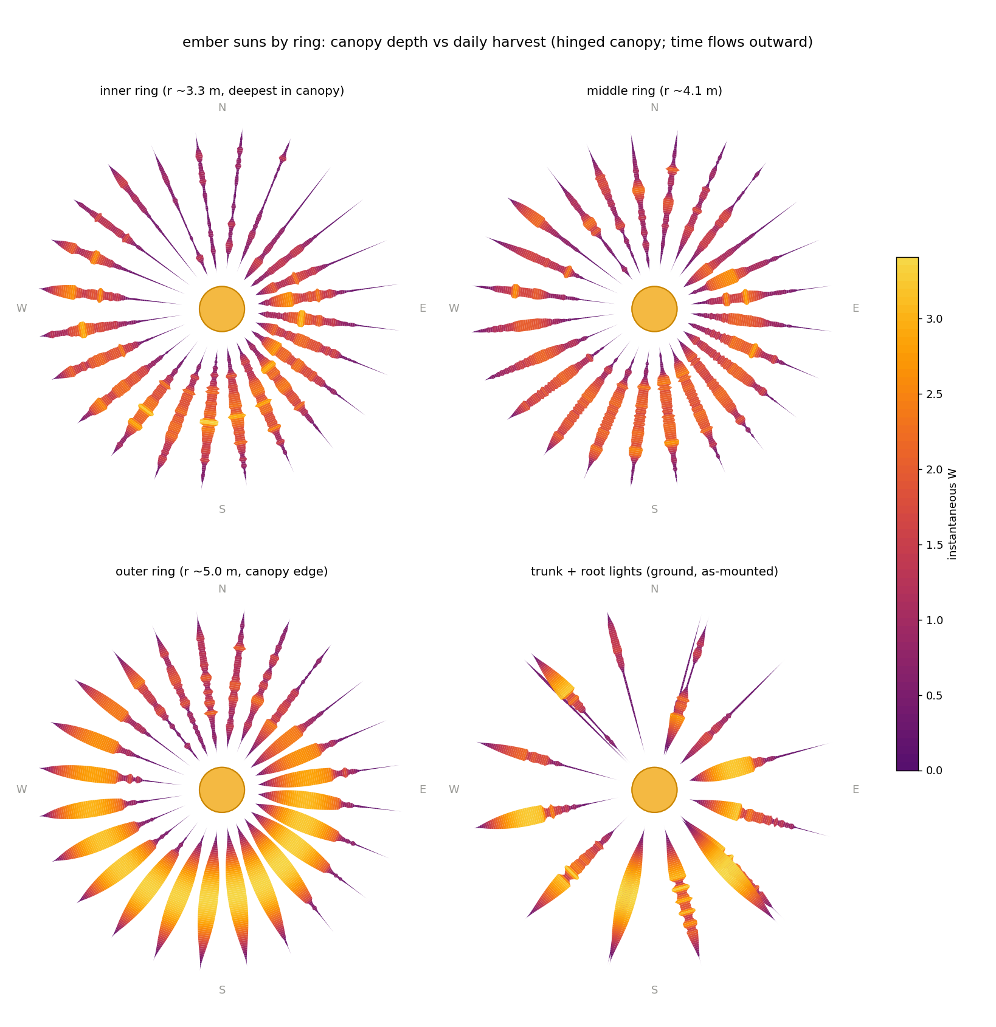
ops/solarsim/data/figures/hinge_sunplot_rings.png
