beneckart/resonance-lighting/ops/solarsim/data/figures/hinge_sunplot_rings_labeled.png

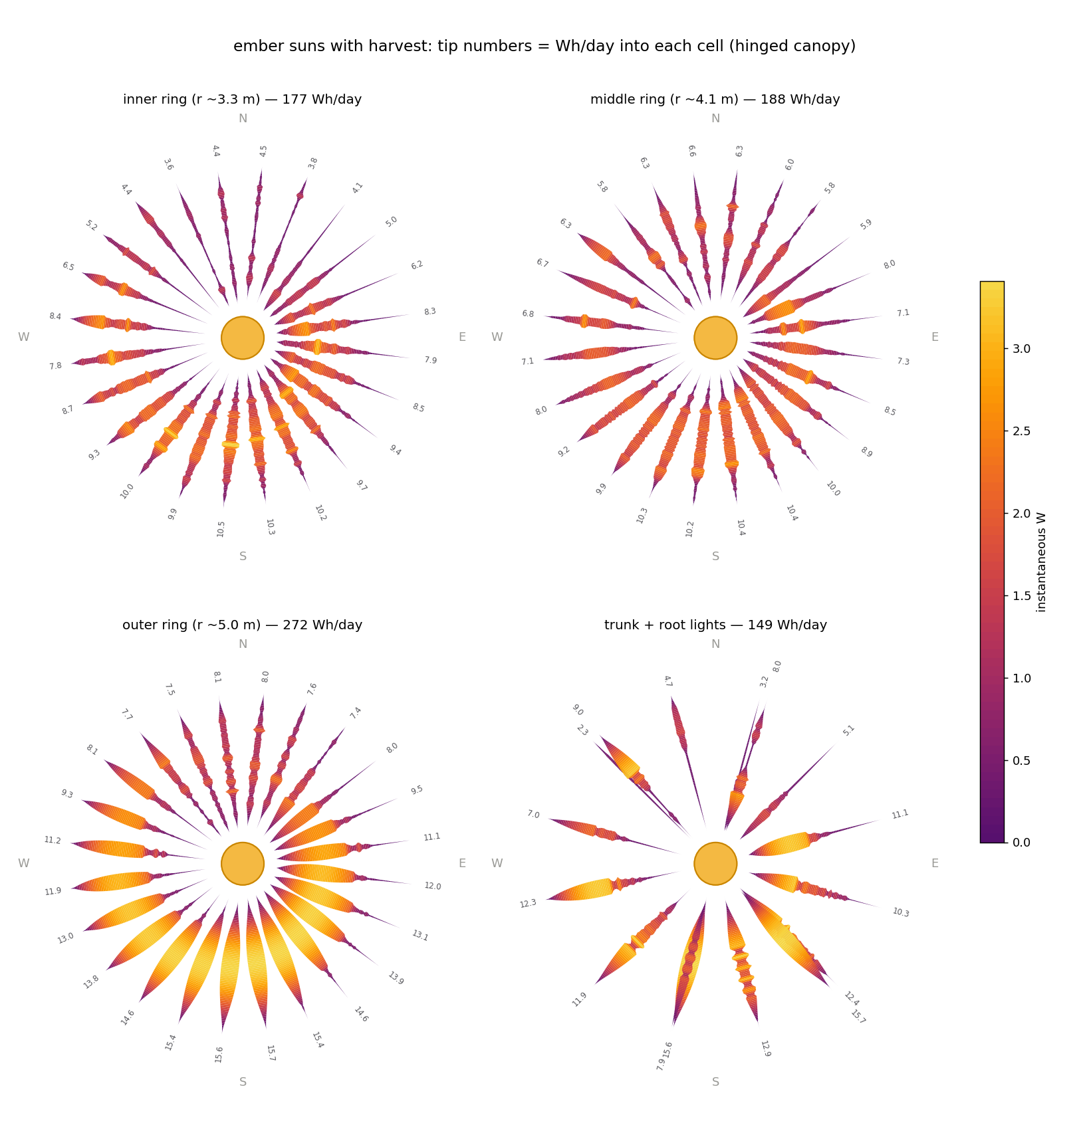
ops/solarsim/data/figures/hinge_sunplot_rings_labeled.png
