beneckart/resonance-lighting/docs/research/11-AUTONOMOUS-BUILD-BACKLOG.md

# 11 — Autonomous Build Backlog + Loop Protocol (lighting-architect)

> Purpose: enough sequenced work + discipline for a self-paced **design → test → iterate** loop
> of 20+ cycles, building the software-only lighting environment (sim-first, no hardware).
> Read with: PRD + docs 06–10. Target = the R3F mirror twin (`app/`) + a sim of the tree.

## THE LOOP (every cycle — do all 6, then re-arm ≤60s)
1. **PICK** the lowest-numbered unchecked increment below (or the next unblocked one).
2. **BUILD** just that increment — one focused change. Small > big.
3. **TEST / VERIFY (mandatory — DESIGN mode):** run the dev server (`npm run dev` in `app/`) and **screenshot it** (browse/Playwright, or `python3 -m http.server` for static). **Never mark an increment done on code-read alone** — look at the pixels.
4. **CHECKPOINT:** commit (explicit paths) + `git push origin elliots-controller`. Push to **our fork directly — NO MR, NO qb, NO PR, never the OS repo.**
5. **LOG:** append one line to the BUILD LOG (bottom of this file): `[cycle N] <increment> — built / verified-by <screenshot> / commit <sha> / next: <X>`.
6. **REFLECT + RE-ARM:** note anything to improve; pick the next increment; re-arm the loop (ScheduleWakeup ≤60s / continue). **Do not stop** until the backlog is done or you're hard-blocked. If blocked, log the blocker + skip to the next unblocked increment.

**FULL AUTONOMY — no restrictions (Elliot 2026-06-13).** This is a greenfield repo; nothing is built yet, so **there is nothing to break.** Move fast, experiment freely, refactor boldly, just keep committing + pushing to `origin/elliots-controller`. Don't ask permission; don't wait. Only two hard rules: (1) don't edit Ben's `firmware/ hardware/ enclosure/` lanes or the OS repo; (2) no secrets / no giant binaries committed. If you finish the backlog, generate the next 10 increments and keep going. **Run all night.**

## BACKLOG (check off as you go)

### Phase A0 — environment + REAL model (DO FIRST)
- [x] A0.1 **Testing environment.** Dev server (`npm run dev`), **Vitest** unit tests, and a **Playwright** headless screenshot harness for the mandatory visual verification each cycle. A `npm run build` + `npm test` that must pass before each checkpoint commit. ✓ scaffolded in `app/` (Vite+React+TS+R3F+drei+zustand); `npm run build`/`npm test` green; `scripts/screenshot.mjs` harness working.
- [x] A0.2 **Load the REAL 3-D model.** ✓ DONE — exported from the EJF blend (`Tree_Resonance_packed_2026-06.13.ejf.blend`, 2.42 GB) via headless Blender (`app/scripts/blender/export_tree.py`): **78 real canopy lights → `app/public/fixtures.json`** (Light_Sources collection, z 0.53–40.51, real colors). Rendered in the twin as distinct emissive points at true positions (Blender Z-up → three Y-up). Structure glb (10.4 MB ovoid shell) deferred — re-export decimated bamboo as context in A4.
  `"/Users/resonanceartcollective/Library/CloudStorage/GoogleDrive-resonanceartcollective@gmail.com/.shortcut-targets-by-id/1v30ZnGHSid-Xt8f4MjVkRsSfNDoqwOxM/Resonance Master/Marketing/Cowork/Resonance Marketing OS/Portal Resonance/Resonance Studio/Resonance Tree/Portal System Current Read Only/design-and-construction/design-files/Blender/"`
  **CURRENT model = `Tree_Resonance_packed_2026-06.13.ejf.blend`** (2.4 GB, newest). Also `Tree_Rhino7.3dm` (Ed).
  Export with Blender CLI: `blender --background "<that .blend>" --python export_gltf.py` → write a **decimated/compressed glTF** (`app/public/tree.glb`, gltfpack) + extract LED/fixture positions → `app/public/fixtures.json`. (Coordinate w/ blender-architect if helpful — it knows this file's object names, e.g. `treev4 Lights`.)
  ⚠ **Do NOT commit the .blend or the raw 2.4 GB** — only the exported `.glb` + `fixtures.json` (gitignore the rest). Load the `.glb` in the R3F twin. **Verify (screenshot): the actual tree renders.**
- [ ] A0.3 If the real export is briefly blocked, fall back to the **placeholder** generator (A2) so the loop never stalls — then keep retrying the real model.

### Phase A — scaffold + model
- [x] A1. Scaffold `app/`: Vite + React + TypeScript + React Three Fiber + drei + zustand. `npm run dev` serves a blank R3F canvas. (Verify: canvas renders.) ✓ live canvas: emissive icosahedron + infinite grid + OrbitControls; `preserveDrawingBuffer` on for reliable screenshots.
- [~] A2. Placeholder generator — SUPERSEDED: the real EJF export (A0.2) gives a true 78-fixture `fixtures.json`, so no placeholder needed.
- [x] A3. Load `fixtures.json`; render each fixture as a small emissive sphere at its xyz; OrbitControls. ✓ + Bounds auto-frame; `fixtures.ts` typed contract + loader.
- [ ] A4. Add a simple tree-proxy mesh (trunk cylinder + canopy) or a stub glTF for spatial context.

### Phase B — the mirror loop
- [x] B1. zustand store (`store.ts`): SimFixture {id,role,zone,pos,norm,seqT(azimuth order),heightT,rnd} + Control {pattern,brightness,hue,sat,speed}. ✓
- [x] B2. tick loop (`useFrame` in TreeLights.tsx) computes each fixture's reported color via `litFor` (the firmware stand-in). ✓
- [x] B3. Rendering reads computed reported state only (InstancedMesh instanceColor). ✓ (G1 will split tick→transport)
- [x] B4. Control overlay (`Controls.tsx`): pattern buttons + brightness/hue/sat/speed sliders → sets commanded. ✓

### Phase C — patterns (one increment each)
- [x] C1 solid · [x] C2 chase (travels AROUND tree by azimuth order) · [x] C3 ripple (radial) · [x] C4 sparkle · [x] C5 breathe. (`patterns.ts`)
- [x] C6. Pattern selector UI + params (brightness, hue, saturation, speed). ✓

### Phase D — light rays + gobo (the "accurate visuals")
- [x] D1. Bloom/glow ✓ — @react-three/postprocessing EffectComposer + Bloom; fixtures rendered with HDR gain (×2.6) so they glow as lanterns. Also: bamboo glb now a VISIBLE warm lit material (#9c7a44) + key/rim directional lights + hero 3/4 camera framing the whole tree. **Now unmistakably reads as the Resonance Tree** (screenshots/cycle9-hero.png).
- [ ] D2. Volumetric beam per fixture (drei volumetric SpotLight or a cone+raymarch pass). (Verify: visible beams.)
- [ ] D3. Gobo projection: spotlight `.map` with a mandala texture casting a pattern on a ground plane. (Verify: mandala shadow visible.)

### Phase E — sound
- [x] E1. Web Audio (`audio.ts`): mic OR loaded song → FFT → bass/mid/treble/level/beat. ✓
- [x] E2. Reactive mapping (in `litFor`): level→brightness, bass→swell, beat→flash, treble→hue. ✓ (refine per-band→zone + beat-cue triggers = H4)

### Phase F — timing / show / monitor
- [ ] F1. Cue system: capture current look as a cue; list + recall cues.
- [ ] F2. Simple timeline/schedule with tempo (cues fire on time).
- [x] F3. Monitor view ✓ — `monitor` toggle: dead fixtures render as red "no-signal" markers; live readout `reporting N · dead D · stale S` (store.monitorStats updated ~2Hz from the tick). Proves the truth-mirror surfaces desync/dead.

### Phase G — swap-readiness + polish
- [x] G1. Mock heartbeat feed ✓ — `mock heartbeat` toggle: each fixture reports its color at a jittered 0.6–1.2s interval (held between → real reported-state staleness), `deadCount` fixtures stop reporting. TreeLights renders REPORTED buffers, not the instantaneous commanded render. Swap this transport for ESP-NOW heartbeats and nothing else changes.
- [ ] G2. `fixtures.json` schema doc + runtime validation; ready to swap in the real Grasshopper export.
- [ ] G3. PWA offline config (vite-plugin-pwa) + README with run instructions.
- [~] G4. Perf pass — instanced mesh already in place (TreeLights InstancedMesh, 1 draw call); beams/bloom perf TBD.

### Phase H — Elliot's live asks (2026-06-13, via conductor)
- [x] H1 **Sequencer** ✓ — 7 modes on azimuth order (`seq`): fill (one-after-another around tree, then recede, then dark) · single (one light travels around) · snake (two heads sweep out from center, ping-pong) · groups (blocks of groupSize) · everyN (every 2nd/4th, animating) · allOn · allOff. Step-delay slider (default 200ms) + group-size + every-N. UI sub-panel shows when pattern=sequence. (`patterns.ts` sequence case + Controls.tsx)
- [ ] H2 **Full fleet**: scan `06_Unplaced_REVIEW` (256) for uplight/chandelier light sources; include if present → 100–150 fixtures (pending conductor scope confirm). fixtures.json re-reads on change.
- [x] H3 **"Any possible lighting command"** ✓ — command console (`command.ts` + Controls input). Grammar: `clear`/`on`/`off`; globals `hue/bri/sat/speed/pattern <v>`; targeted overrides `<target> <color #hex|name | on | off>` where target = `all | zone <low/mid/high> | range <a-b> | every <n> | fixture <id/seq>` (range/every use azimuth order). Per-fixture override layer applied in the tick after the pattern. Verified live: "every 4 color red" → 20 fixtures red around the tree.
- [ ] H4 **Audio depth**: per-band → zone mapping, beat-synced cue triggers, spectrum→color; song scrub/transport.
- [ ] H5 **Feature-coverage audit** vs PRD + docs 01–11 + Ben's repo (Monitor go/no-go, cues+schedule, gobo/beams D-phase, MIDI APC-mini, commissioning, element modes) — ensure ALL interactions covered (Elliot: "check our repo + Ben's, all the features").
- [x] H6 **Tree context geometry** ✓ — bg agent exported 01_Structure+02_Bamboo (2364 meshes, decimate 0.03 + Draco) → `app/public/tree-context.glb` (10.4MB, scratch on SUNEAST). Wired into Scene.tsx as a faint (#26303f, opacity 0.22, depthWrite off) backdrop; aligns with the 78 fixtures (Y-up). Now reads as a tree. (export_context.py committed.) Also covers A4.

### Phase I — PRO-GRADE SCOPE (Elliot + conductor, 2026-06-13) — "super professional, festival/immersive quality"
> Bar: must look + behave like a pro festival-stage / immersive-art lighting system. Spine = REAL MUSIC driving a BEAUTIFUL tree. Always cross-check PRD + docs 01–11 + Ben's repo for features; everything TESTED + VISUALLY VERIFIED.
- [~] I1 VISUAL FIDELITY polish — D1 bloom ✓ (c9), visible bamboo + hero cam ✓ (c9), **D2 volumetric beams ✓ (c10)** — additive cones per fixture, beam-angle sized, colored by reported state. REMAINING: D3 gobo/mandala projection, ground plane + shadows, multi-visualizer, full-spectrum/tricolor patterns, per-fixture beam DIRECTION from model.
- [ ] I2 FULL AUDIO SYNC (the spine) — real beat/BPM/tempo/onset/DROP detection (not just FFT bands); TESTED with real songs for rhythm/timing accuracy. (need test tracks → app/public/audio/.)
- [ ] I3 DJ CONTROLLER — on-screen crossfader + EQ-band→light + intensity faders, wired; MIDI-ready (APC mini mk2 / Midi Fighter Twister mapping).
- [ ] I4 RANDOM / AUTO-VJ — shuffle + generative modes.
- [ ] I5 MULTIPLE VISUALIZERS — several distinct viz looks to switch between.
- [ ] I6 SEQUENCES — many more sequence patterns, built + tested.
- [ ] I7 LLM SMART SOUND→LIGHT MODE — an LLM "VJ" that reads audio features + crowd/section and arranges the pattern/visualizer vocabulary live (Addendum C Layer 2); multiple visualizations.
- [ ] I8 ESP-NOW FREQUENCIES / CHANNEL config — channel-pinned control surface in the app (honor Ben's ADR 0004/0010 + SYSTEM.md); wire the param-output path (custom LXOutput-equivalent) toward the real mesh.
- [ ] I9 FULLY-FUNCTIONAL APP CONTROLS — every control wired + tested; polished, professional UI.
- [ ] I10 DEEP RESEARCH — how big festival stages + immersive art pieces do real-time music-reactive lighting/visuals (tools, pipelines, beat-sync, pro techniques) → fold into the build. (bg research agent dispatched cycle 9.)

## BUILD LOG (append one line per cycle — newest at bottom)
<!-- template: [cycle N] <increment> — verified-by <shot> — commit <sha> — next <X> -->
- [cycle 1] A0.1+A1 — Vite+React+TS+R3F+drei+zustand scaffold + full test env (Vitest + Playwright e2e + build) — verified-by screenshots/cycle1-scaffold.png (emissive icosahedron + grid render) — next A0.2 real model
- [cycle 2] A0.1 full — Playwright config + e2e spec (canvas mounts, sized, 0 console errors, 543 distinct colors) + `npm run check` (build+test+e2e all green) — verified-by e2e pass — next A0.2 real model (EJF blend, 76 canopy lights)
- [cycle 3] A0.2+A3 — headless Blender export of EJF blend → 78 real canopy fixtures in fixtures.json + render as emissive point cloud at true positions (Z-up→Y-up), Bounds auto-frame — verified-by screenshots/cycle3-real-tree.png (78 distinct colored points) — next B1-B4 controllable mirror
- [cycle 4] B1-B4 + C1-C6 + E1-E2 — FULLY CONTROLLABLE twin: zustand store (commanded→tick→reported mirror), InstancedMesh render, control overlay (5 patterns + sliders), Web-Audio reactivity (mic/song→FFT). store/patterns/audio/TreeLights/Controls/Scene/App — verified-by screenshots/cycle4-controllable.png (78 lights + live control panel) — next H1 sequencer
- [cycle 5] H1 sequencer — 7 modes (fill/single/snake/groups/everyN/allOn/allOff) on azimuth order, step-delay 200ms + group-size + every-N sliders, UI sub-panel — verified-by screenshots/cycle5-sequencer.png (sequence mode UI + on/off fill state) — next H3 any-command console
- [cycle 92] DIRECTIONAL DECK DIAL (Elliot: 'dials should directionally control the lights, not just a tempo'). DjController deck slider was magnitude-only (0..3→speed); now SIGNED (-3..3): sign→control.reverse (spin direction around the tree), magnitude→speed. Left/right = opposite spin, centre=slow. Mirrors the jog wheel. Label ◄/► + speed. 136 tests. commit e4f0d9f.
- [cycle 91] CONCENTRIC RINGS (Elliot: '3 rings move in opposite concentric directions + toward/away, every version between'). fixtures gain ring (0/1/2 by radial value-tertiles from trunk) + radialT (in/out), computed on load. New 'rings' pattern: each ring spins azimuthally OPPOSITE its neighbours, a radial wavefront travels IN/OUT, a bright head chases each ring, each ring its own colour band; deck `reverse` flips all directions; audio per-ring (inner=bass/mid=mid/outer=treble). 20 patterns, 136 tests. Verified (pattern rings, top-down): distinct concentric colour bands. commit 413f57c.
- [cycle 90] DOWNLIGHT FIXTURES = GLOWING LANTERN BODIES, not bare dots (Elliot: 'LED is inside, see the object + rays + patterns'). TreeLights renders the real downlight_lantern.glb as the lit fixture (instanceColor=pattern colour), hanging straight down (-Y, never up), scaled ~4.5% treeSize (was sub-pixel). Beams clamped strictly downward (no up-cast; uplights separate). Removed redundant dark LanternBodies. Data-driven + hot-swappable. Verified (?tod): tapered lantern tubes glow with pattern, matches Blender ref, 0 errors. commit 632595a.
- [cycle 89] LANTERN SCALE-MISMATCH fix (downlight bodies were invisible — glb in metres ~0.25 vs ~100-unit tree space → sub-pixel). Derive scale from measured glb height + treeSize. + ?tod=<0..1> deep-link. (superseded by cycle 90's body-as-light). commit 2a1cc4b.
- [cycle 88] GOLDEN-FRAME REFEREE harness — locks the CPU reference contract (the reference the GPU pass + Ben's ESP32 render3D must reproduce). Documented fixed-input expected values DERIVED from the published formula (not snapshotted) → drift caught here + on hardware. radialPulse@origin → exact [0.3,0.192,0.03] (derivation in-comment); chromaticCrown@crown on k=0 wavefront → lit+warm; determinism per-pattern; spectrumBands band→audio routing. Pure test-only (no source change → zero regression). 135 tests, build green. commit 3c6918d. (Chose this safe pure increment over the no-readback in-shader refinement, which needs onBeforeCompile + moving master/EQ into the shader = too risky to verify headless in one tick; deferred.) NEXT: no-readback in-shader RT sampling (deliberate, when verifiable) / stateful patterns via GPUComputationRenderer / lock transliteration convention w/ Ben.
- [cycle 87] GLSL PATTERNS ×3 (spiral, plasma, chromaticCrown) ported into the GPU runtime — each a vec3 pattern(p,t) GLSL body + parity CPU referee. spiral=barber-pole (atan2 azimuth+height+time); plasma=interfering sines+bass; chromaticCrown=3 triad colours streaming from the crown (GPU twin of the CPU 'chromatic', GLSL for-loop). ?glslp=<id> picks the active GLSL pattern. 5 GLSL patterns; finite-RGB + shader-build tests auto-cover (11 in glslRuntime.test, 131 total), build clean. VERIFIED in real Chromium: ?glsl=1&glslp=chromaticCrown → for-loop shader compiled + 118/118 lit, 0 console errors. commit 151e6ae. NEXT: no-readback in-shader RT sampling (the doc's golden-frame ideal) / glslPattern picker UI / lock transliteration convention w/ Ben.
- [cycle 86] GLSL RUNTIME step 2 — the RT PASS, LIVE + working end-to-end (opt-in, default OFF → zero regression). glslPass.ts: packs 118 positions → N×1 DataTexture (normalized ~[-1,1] about centre = shared contract coord); WebGLRenderTarget(N,1) + fullscreen ShaderMaterial(buildFragmentShader(pattern.glsl)) w/ uniform bus from control+audio; renderRead() renders + reads N×1 RGB back. TreeLights: control.glslMode → run pass once/frame + drive fixtures from readback (master/EQ/strobe/ripple still layer on top); GL hiccup → falls back to litFor. ?glsl=1 enables for verify. packPositions+passUniforms pure+tested (5 tests, 128 total). Interim: one-shot 118px readback/frame (sub-ms; doc only bans LARGE readbacks) — no-readback InstancedMesh-samples-RT = next refinement. VERIFIED end-to-end: ?glsl=1 in real Chromium → shader compiled + 118/118 lit by radialPulse, 0 console errors; default CPU twin unchanged. commit 75d396c. NEXT: no-readback in-shader RT sampling / more GLSL patterns / lock transliteration convention w/ Ben.
- [cycle 85] GLSL RUNTIME step 1 (open flag, RESEARCH-GLSL-RUNTIME Approach B) — ISOLATED build beside the twin, live render path UNTOUCHED. glslRuntime.ts: the pattern contract vec3 pattern(vec3 p,float t); each pattern ships GLSL body (GPU source-of-truth) + a CPU port reading the same normalized uniform bus (speed/hue/sat/density + bass/mid/treble/onset/bpm/beatPhase) = the golden-frame referee (headless-testable; how twin/ESP32 render3D/WASM are proven to agree). hsv2rgb CPU+GLSL kept in exact parity (IQ ramp 0,4/6,2/6 — fixed a swapped-offset bug caught by the primary-hue test). 2 patterns (radialPulse, spectrumBands) both backends. buildFragmentShader wraps a body into the RT-pass shader (samples uPos@vUv, no readback) = step-2 scaffold. +8 tests → 123 pass, build clean. commit b464a84. NEXT (step 2): WebGLRenderTarget RT pass (118 positions→N×1 DataTexture→1 shader pass→texel/fixture) + InstancedMesh samples the RT (golden-frame parity), opt-in toggle so the proven CPU twin stays default.
- [cycle 84] DJ WAVEFORM BEAT-GRID overlay (open flag, rekordbox-style). Surfaces the PLL beat clock on the deck waveform: vertical lines per beat, bar lines (every 4th) brighter. Audio live → grid anchored to beatTime, scrolls locked to the music; idle → faint static 8-division ruler (always-visible time grid). VISUALLY VERIFIED (tight crop /tmp/wave.png): 8-division ruler w/ brighter bar lines + idle waveform pulse at 'now' edge, 0 console errors. 115 tests, build clean. commit cf4a45f. NEXT: [GLSL runtime] render-to-texture pattern pass (bigger, isolated build) / normalized control-bus.
- [cycle 83] QUANTIZER (doc 16 P0-3 — events snap to the grid). The sequencer stepped on wall-clock t: even 'synced' (period from BPM) the step boundaries floated vs the real downbeat. Fix: BeatTracker.beats = monotonic beats-elapsed (advances dt/period, onset-corrected like phase → grid-aligned); quantizedStep(beats,div)=floor(beats·div) ticks once per 1/div beat so boundaries land exactly on ¼/⅛/16th. audioFeatures.beatTime exposes it; sequence pattern uses quantizedStep when syncToBeat && audio live (else unchanged free-running stepMs). +2 deterministic tests (grid alignment per div; beats monotonic ~tracks elapsed beats) → 115 pass, build clean. commit 2b7a55a. Verified deterministically (grid engages only w/ live audio; math tests are the proof; default path unchanged). NEXT: open flags — [DJ waveform] polish / [GLSL runtime] render-to-texture pattern pass / normalized control-bus.
- [cycle 82] AMBIENT AUTO-BALANCE (Elliot: 'sense the lighting from the piece and adapt levels to balance automatically'). Daylight washes the look out (existing dayWash=1−0.5·ambient dims brightness); auto-balance is its EXACT inverse: autoBalanceGain(ambient)=1/(1−0.5·ambient) clamped [1,2.2] (night→1.0 unchanged, full sun→2.0). applyEnv boosts master by it when control.autoBalance on → master-boost cancels the dayWash → tree reads the SAME at noon as night. Default ON (only boosts as ambient rises; night baseline untouched). '⚖ auto-balance' toggle in env panel w/ live % drive. +4 deterministic tests incl. the exact-inversion proof gain·dayWash=1 ∀ambient (that equation IS 'balanced') → 113 pass, build clean. commit ad15e6e. Verified: math proven by unit test; night screenshot no regression. Day-vs-night visual best on real HW (headless rejects styled button clicks; command-console input is the only reliable headless interaction). NEXT: doc-16 Quantizer primitive (snap events to beatPhase grid) / normalized control-bus / DJ-waveform + GLSL-runtime open flags.
- [cycle 81] CHROMATIC TRICOLOR (Elliot's repeated ask: '3 colours moving outward from ONE source'). New 'chromatic' pattern (distinct from the existing tricolor-ORBIT): the CROWN is the source (where the chandelier hangs); u=1−heightT = radial distance from the top; three triad-hue wavefronts (hue+k/3) travel outward phase-offset by 1/3 so they separate as they propagate. Dark between fronts → crisp bands. Each colour pulses to its own band (bass/mid/treble) live. 19 patterns; patterns.test auto-covers (24 pass). VISUALLY VERIFIED (screenshot): green band at crown source + magenta spreading outward, button lit, 118/118, 0 errors. commit 2ab0675. NEXT: ambient auto-balance (sensors.ambient→master).
- [cycle 80] SPECTRAL-CENTROID → TIMBRE-AWARE HUE (doc 16 P0-4). spectralCentroid(bins)=magnitude-weighted mean bin (0..1 brightness centre; bassy→low, cymbals/leads→high); centroidToHue(c): dark→warm amber(0.02), bright→cool blue(0.58). audioFeatures.centroid smoothed (fast-attack/slow-release) so hue glides not strobes. decideLook now colours by TIMBRE (centroidToHue) not just treble level. +3 deterministic tests (centroid ordering, hue map) → 109 pass, build clean. commit ee85c8f. Verified deterministically (hue-shift only visible w/ live audio; math tests are the proof). NEXT: chromatic-tricolor refine.
- [cycle 79] GPU PERF PASS (#1 open flag) + ROOT-CAUSE CORRECTION. The research agent's "118 shadow-casting spotlights → 119× draws" diagnosis is WRONG for our code: the 118 fixtures already render as 3 InstancedMeshes (meshBasicMaterial, no lighting) — we have exactly ONE shadow-casting spotlight (gobo) + 2 directionals. Real cost drivers fixed: (1) Canvas dpr capped [1,1.5] + antialias:false (a 2-3x HiDPI panel was filling 4-9× pixels; Bloom hides AA loss) — biggest fill win; (2) ShadowFreeze — the gobo shadow covers a STATIC scene, so render 45 frames then shadowMap.autoUpdate=false → stops re-drawing the 2364-mesh bark shadow pass every frame; (3) powerPreference high-performance; (4) window.__perf snapshot → HUD now shows live draw-calls/frame. Build+106 tests green; screenshot full-fidelity no regression. commit 34575b6. NOTE: fps DELTA not measurable headless (Playwright throttles rAF to ~1fps) → read window.__perf in devtools on real HW. NEXT: P0-4 Meyda centroid→hue + chromatic-tricolor refine.
- [cycle 78] TEMPO-PHASE LOCK / PLL (doc 16 P0-1 — research's #1 gap was TIMING). BeatTracker.phase: a phase-locked loop free-running at the detected BPM, nudged toward the downbeat on each onset (gain 0.18) → converges + stays locked through missed/ghost onsets. push() returns {onset,bpm,phase}. + quantizePhase(phase,div) (snap to ¼/⅛/16th grid). audioFeatures.beatPhase + beatPulse ((1-phase)² peaks on the beat); patterns add +0.18·beatPulse PREDICTIVE on-grid swell (pumps ON the beat, fills gaps between onsets) over the existing reactive flash. +2 deterministic tests (phase locks near downbeat; quantize snaps) → 106 pass, build+tsc clean. commit 49b248a. Verified deterministically (headless=no audio→beatPulse 0, so the PLL unit test is the visual-equivalent proof). NEXT: P0-4 Meyda spectral-centroid→hue + chromatic-tricolor refine (3 colours from one source).
- [cycle 77] SECTION→LOOK wiring (Elliot: 'different patterns triggered by different music sections/components'). aivj.decideLook now reads audioFeatures.section: PEAK → forces the hot family (spectrum/tricolor/chase/godray) at speed 2.2+bass; BUILD → 'rising' upward sweep whose speed ramps with energy (anticipation); groove+ambient fall through to the energy tiers (existing tests stay green); DROP override still wins. The AI auto-pilot now tracks musical STRUCTURE, not just instantaneous energy. +2 tests (104). Build+tsc clean. commit 3bb9d9e. NEXT: P0-1 tempo-PHASE lock (PLL beatPhase) so chases hit ON the beat + P0-4 Meyda centroid→hue.
- [cycle 76] CHANDELIER INTEGRATED (Elliot: 'shipped the central chandelier — 16 new lights hung from the top'). blender-architect handoff e76506ca delivered chandelier.glb (2.75MB, 1 mesh, world-space at crown z~40). New <Chandelier> in Scene.tsx loads it through the proven useGLTF path, styled brass/copper (metalness 0.35, opacity 0.9) so the 16 crown fixtures read against real structure; gated !LIGHT_SCENE + ErrorBoundary like TreeContext. git-tracked the asset with -f (public/*.glb was UNTRACKED → fresh-clone white-screen risk, same class as the cycle-17 gobo bug). Verified: build clean, hero capture shows scene healthy 118/118 lit, no crash/fallback. commit 0c2772c. NEXT: section→look wiring.
- [cycle 75] SECTION/ENERGY-TIER detection (doc 16 P0-2 — 'find the drop + react', live rekordbox-phrase analog). audio.ts classifySection(level,pastMin,drop) → audioFeatures.section {ambient|groove|build|peak}: drop/loud→peak, rising-from-quiet→build, mid→groove, quiet→ambient. Computed each frame; shown in the AI panel readout (BPM · section). +1 test (102). Build+tsc clean. NEXT: wire section→whole-look in decideLook (peak→godray, build→spiral/rising) + tempo-phase lock.
- [cycle 74] AUDIO→SPEED reactivity (Elliot: 'change speed by set features' + 'most responsive') — aivj.reactiveSpeed(audio): energy+BPM+drop → live motion speed (0.3..3), silent=1. AudioReactiveDriver applies it ~12×/s when control.audioSpeed ON (else manual). '🎵 RX-SPD' toggle in DJ transport. +1 test (101). + RESEARCH doc 16 landed (sound-responsive best-in-class): verdict = our analysis is AHEAD of commercial, gaps are TIMING+TASTE. P0 roadmap: tempo-PHASE lock (PLL, hit ON the beat), section/energy-tier state machine (rekordbox-phrase live), Quantizer (snap to grid), Meyda centroid→hue, + normalized control-bus architecture. Build+tsc clean.
- [cycle 73] TOUCH MIXER OVERHAUL (Elliot: slim + collapse + real touch + spin the decks). DjController: (1) COLLAPSE button (▾) → slim '🎛 DJ ▲' bar so the tree is unobscured; maxHeight 48vh + tighter padding/gaps/pads; platters 96→60. (2) Knobs → draggable <Knob> (pointer drag up/down + wheel + dbl-click-0 + % readout), touchAction:none + pointer-capture = WORKS ON TOUCH. (3) JOG WHEELS spinnable: drag around a platter → angular velocity sets control.speed, direction sets control.reverse, pointer PRESSURE scales intensity → spins the lights around the tree at variable speed + reversible. (4) control.reverse flips azimuthal motion (tt=t*dir) in chase/spectrum/spiral/tricolor/godray. All pointer-event based → full mouse+touch. Capture-verified slim mixer renders, 0 errors, 100 tests. Touch-screen-PC ready.
- [cycle 72] BLACKOUT preempt (Tier-2 ops safety pair w/ BEACON). control.blackout: forces all fixtures off, wins over beacon. Always-available '🌑 BLACKOUT' button (bottom, beside BEACON) reachable in clean view → instant dark (neighbour complaint/emergency). Capture-verified: BLACKOUT ON → tree dark, 0 errors, 100 tests. NOTE: genuinely-valuable solo Tier-2 is now thinning (ops safety + day/night + HUD all done); remaining high-value work is blender's uplights/chandelier (not my lane), real-hw/cortex, or real-browser audio verify — flagging to conductor + easing cadence.
- [cycle 71] SHOW-HEALTH HUD (Tier-2 ops). HealthHud.tsx top-center pill: live fps (green≥50/amber≥30/red) + fixture health from monitorStats — 'N/118 lit' + dead✗ + stale~ counts (populated by the mock-heartbeat truth loop). Diagnostic → hidden in cinematic/clean view. Capture-verified (mock heartbeat on → '112/118 lit' = 6 dead by default deadCount, fps readout present, 0 errors). 100 tests.
- [cycle 70] DAY/NIGHT STAGE TOGGLE (Tier-2). store.timeOfDay 0..1 drives Scene background (night→dusk→day ramp) + ambient (0.16→1.16) + directional fills, and couples sensors.ambient (so the fixture daylight-wash matches). Controls 'time of day' 🌙night/🌆dusk/☀️day buttons. Lets us preview how the install reads day vs night (festival runs both). Capture-verified: day = bright sky-grey bg + structure visible + lights washed; night = dark. 0 errors, 100 tests.
- [cycle 69] BEACON PREEMPT safety (Tier-2). control.beaconPreempt: when ON, TreeLights forces EVERY fixture to full white (scaled by master) over the pattern/overrides/audio = unconditional whiteout safety beam. Always-available '🔦 BEACON' button bottom-center, rendered OUTSIDE the cinematic-hide so it's reachable even in clean view (one tap = lights up for safety/egress). Capture-verified: BEACON ON → full whiteout, 0 errors, 100 tests.
- [cycle 68] PLASMA pattern (conductor Tier-1 #3 first piece — GLSL plasma math, CPU-evaluated per fixture). Interfering sine waves over position + radial term → flowing hue + brightness field. 18 patterns now. patterns.test auto-covers it (100 tests). Capture-verified (flowing field renders, 0 errors). Tier-1 #1-#6 all have their core piece shipped; full per-fixture GLSL ShaderMaterial runtime = a future bigger pass.
- [cycle 67] AUDIO DEVICE-PICKER UI (conductor Tier-1 #5 complete — logic shipped c64, UI now). DjController: '🎚 source' <select> listing listAudioInputs() (refreshes on open for post-permission labels), 🎤 MIC now starts from the selected deviceId (booth-out vs mic). Capture-verified: source picker renders, 0 console errors, 99 tests. Tier-1 done: #1 waveform, #2 EQ graph, #4 HERO, #5 device picker, #6 beam volumetrics. Remaining: #3 GLSL pattern runtime.
- [cycle 66] VOLUMETRIC BEAM FALLOFF (conductor Tier-1 #6, first piece). Beam cones now carry a baked vertex-colour gradient (v² from source→far) so additive×gradient = a real light SHAFT bright at the fixture and fading into the air, not a flat uniform cone. Keeps per-fixture instanceColor tint (vColor × instanceColor). opacity 0.06→0.09. Screenshot-verified via test-runner capture (beams read as shafts, 0 console errors, no regression). 99 tests. (Full Henyey-Greenstein scattering = a future shader pass; this is the safe high-value falloff.)
- [cycle 65] DJ SCROLLING WAVEFORM (conductor Tier-1 #1). DjController mixer now has a <canvas> scrolling waveform: live audioFeatures.level history (ring buffer), tinted by treble (hue 210→40), red tick on each beat, faint idle pulse when no audio. ✅ UNBLOCK: verified VISUALLY via the Playwright TEST-RUNNER capture script (node + @playwright/test chromium) — works even though the Playwright MCP is down → the visual Tier-1 items are no longer gated. Capture: DJ console renders intact w/ waveform, 0 console errors. 99 tests, build+tsc clean. (Live motion needs real audio out; headless shows idle baseline.)
- [cycle 64] AUDIO SOURCE/DEVICE PICKER — logic core (conductor Tier-1 #5). audio.ts: audioInputsFrom() pure filter (MediaDeviceInfo[] → selectable audio inputs w/ label fallback), listAudioInputs() enumerate wrapper, startMic(deviceId?) now takes an optional deviceId constraint (pick the DJ booth-out vs mic on playa). +1 test (99 total), build+tsc clean, existing startMic() callers unaffected. UI dropdown DEFERRED (visual — Playwright MCP down). That exhausts the logic-verifiable Tier-1; remaining (#1 DJ waveform, #3 GLSL runtime, #6 volumetric, #5 picker UI) are all visual-verify-gated → await MCP.
- [cycle 63] SOUND-REACTIVE HERO mode (conductor Tier-1 #4, the 'Radial Sonic Runway' signature). New 'hero' pattern: the whole tree as one organism — an energy wavefront radiates from the trunk outward (sin(rad*5 - t*3 - energy*4)), brightness driven by live audio.level (+ bass swell/beat flash/drop burst from the global audio layer), idles with a slow breath when silent. 17 patterns now. patterns.test auto-covers it (98 tests). build+tsc clean. Logic-verifiable (MCP still down).
- [cycle 62] WIRE THE LIVE AUDIO GRAPH (conductor Tier-1 #2 — exited holding when I saw the backlog I'd missed). audio.ts: real 3-band EQ BiquadFilter chain (lowshelf 220Hz / peaking 1.2kHz Q1 / highshelf 3.8kHz) inserted src→low→mid→high→analyser(+destination) — the DJ EQ knobs now actually FILTER the sound, not just gate light zones. Boost-only (eqDbForKnob: 0→0dB, 1→+12dB) to match light-zone semantics (no muting). setEqGains() pushed each frame from TreeLights (already reads the knobs). +2 unit tests (97 total). e2e-safe (filter nodes null until audio starts → no-op headless). NOTE: tree-context is 21MB on disk (not the flagged 46MB — blender re-split); crisper 245KB gobo present.
- [cycle 61] E2E SUITE GREEN AGAIN (integrated-app verification via the Playwright TEST RUNNER — closes the deferred-visual gap while the Playwright MCP is down). Root-caused 3 cascading failures introduced by the 22MB bark glb + new panels: (1) goto networkidle never settled (heavy glb+SW) → domcontentloaded; (2) twin readPixels full ~1M-px scan blew the 30s timeout → sparse sample every 64px + 60s timeout; (3) control-matrix/show CRASHED headless WebGL ('Target page closed') under heavy clicking on the 22MB scene → added a ?e2e LIGHT_SCENE flag (Scene.tsx) that skips the bark context glb for interaction specs (real app always full-fidelity). Result: 3 passed (2.4m), 0 console errors → the whole integrated app (DJ/AI/Touch/Commissioning panels + 118 fixtures + mandala) verified rendering+interacting cleanly. 95 unit + 3 e2e green.
- [cycle 60] AUDIT-ON-LOAD — App load now runs auditFixtures(doc): console.info logs the role/zone summary + with-aim count, console.warn flags aim anomalies (downlight-not-down / uplight-not-up). Runtime safety net for the evolving 0.3 export. Build+tsc clean, 95 tests. (Playwright still down — logic increment.)
- [cycle 59] FIXTURE-DATA AUDIT (data-quality gate for the evolving 0.3 export). fixtures.auditFixtures(doc) → counts byRole/byZone + withAim + aim-sanity warnings (downlight must aim down z<0, uplight up z>0, Blender Z-up). +2 tests. RAN IT ON THE REAL fixtures.json: 78 downlight + 24 uplight + 16 chandelier = 118, all 118 have aim, 0 warnings → the 0.3 export is geometrically sane (uplights up, downlights down). 95 tests, build+tsc clean. (Playwright still down → logic increment; verified against real data.)
- [cycle 58] SHOW VALIDATOR (round-trip close; Playwright still down → logic increment). showcompiler.validateShowDoc(doc) = the cortex INGEST gate: checks schema=resonance.show/0.1, channel/stepMs numeric, each keyframe tMs + frame.proto===1 + fixtures array, and tMs monotonic (replay order). Closes compile→export→import. +2 tests incl. full round-trip (compileShow→JSON→parse→validate ok) + rejects junk/wrong-schema/bad-proto/backwards-time. 93 tests, build+tsc clean.
- [cycle 57] COMMISSIONING UI (Elliot: 'calibration built in') — CommissioningPanel.tsx: '📍 commission' (bottom-left) opens a panel listing all 118 fixtures w/ progress bar (assigned/total), per-fixture 🔦 IDENTIFY (flashes that light white in the twin so an installer sees which it is) + 'bind' (assigns the typed/sim MAC → that slot via calibration.ts, persisted). Hidden in clean-view. Built on the tested calibration map. Build+tsc clean, 91 tests. ⚠ VISUAL VERIFICATION DEFERRED — Playwright MCP down this cycle; will screenshot-verify when it returns.
- [cycle 56] REAL-LIGHTS MAPPING + CALIBRATION (Elliot, super-important: 'full understanding of how this works with real lights · self-identify · self-locate · calibration built in · check ben's repo · chromatik'). Read Ben's firmware/ARCHITECTURE.md: fixtures SELF-ID by MAC-derived ID; CANNOT self-locate (RSSI=approx topology, not distance) → position is AUTHORED (fixtures.json, like Chromatik's model file) + COMMISSIONED. calibration.ts: MAC⇄fixtureId 1:1 map (localStorage), assign/resolve/progress/unassigned + identifyCommand (flash a fixture to commission it). +4 tests (91 total). doc 15 = full twin↔hardware trace (4W RGBW tube→skirt-gap petal gobo→ESP-NOW params-not-pixels→mirror truth-loop) + accurate-vs-approximated table + self-id/locate/calibration answer + open gaps. fixtures.json now 0.3/118 (78 down + 24 up + 16 chandelier) auto-loaded. NOTE: Playwright MCP disconnected this cycle (logic+doc only, build+91 tests verify).
- [cycle 55] CINEMATIC / CLEAN VIEW (Elliot: 'easily hide the DJ decks so we can see the tree + keep the visualizer clean', 'I still don't see the lights' — the bottom DJ console was covering the ground mandala). store.cinematic + App wraps all panels (Controls/DJ/AI/Touch) in {!cinematic}; an always-on '✨ clean view' / '🎛 controls' toggle. Also KILLED the favicon 404 (inline SVG 🌳 data-uri in index.html) → console now truly 0 errors. Verified in-browser: clean view shows full tree + lanterns + beams + floor petal-mandala, panels hidden, 0 errors, 87 tests.
- [cycle 54] PRESENCE/MOTION → RIPPLE (completes the sensor-interactivity loop). PresenceDriver.tsx: sensors.motion (0..1) sets the ripple spawn rate — more motion → faster pingPresence wavefronts (on real hw a PIR/mmWave fires this on movement; a passer-by sends a wave of light through the tree). Added a 'motion → ripples' slider to the sensor panel. Verified in-browser: motion=0.9 → ripple wavefronts sweep the canopy, 0 errors, 87 tests.
- [cycle 53] BARK MATERIAL POLISH — TreeContext now differentiates by node name: 'treev4 Plupu' (192 bark nodes) → dark near-opaque shell (#6b5230, opacity 0.96, the light-SHAPER) vs bamboo/structure → translucent (#9c7a44, opacity 0.7). Truer light-leak (glow escapes through the bamboo, shaped by the opaque bark) per Elliot's tube-realism note. Verified in-browser (0 errors, 87 tests).
- [cycle 52] 3 MORE PATTERNS (#26 bloom, #24 firefly, #23 ca-field) — bloom: radial bloom from trunk outward + audio-sat swell; firefly: sparse warm per-fixture blinks that SNAP together on the beat (Kuramoto-ish sync); ca: interfering sine lattices → shifting cellular blobs (GoL/reaction-diffusion feel). Now 16 patterns + 4 element modes. patterns.test auto-covers them (87 tests). Verified in-browser (ca renders, 0 errors).
- [cycle 51] 📱 iPad-OS TOUCH CONSOLE (Elliot: 'real touch screen controls / iPad OS interface'). TouchConsole.tsx: '📱 touch' button → fullscreen tablet overlay — big pattern-pad grid (17 patterns, auto-fit responsive), AI/Strobe/Sync toggles, Hero/Top-down camera, large MASTER/brightness/hue/speed/crossfade sliders. Big touch targets, safe-area insets, touchAction:manipulation. Wired to useTwin. Verified in-browser @1024 (tablet) + @375 (phone reflows to 3-col), 0 errors, 84 tests.
- [cycle 50] 🤖 AI-VJ AUTO-PILOT (PRD #32, Elliot: 'I want to SEE the AI controls'). aivj.ts decideLook(audio)→{pattern,hue,speed,reason}: DROP→godray burst; high energy→hot (spectrum/tricolor/chase/godray); mid→ripple/spiral/sequence/rising; calm→breathe/warmcool/ember/rain; treble biases hue. AiPilot.tsx = VISIBLE panel (top-right): ON toggle + live bass/mid/treble/level/drop meters + BPM + the AI's current decision+reason; when ON drives the show each phrase + instantly on a drop. +5 tests (84 total). Verified in-browser: panel renders, toggled ON drives the look, 0 real errors (favicon 404 only).
- [cycle 49] 🌸 LIGHT SHADES / per-fixture PETAL COOKIES (Elliot: 'light shades still not there' + 'mandala not working' — KEY). Added a 3rd InstancedMesh in TreeLights: one gobo.png-textured quad per fixture lying on the floor below it (sized ≈half the drop height), additive-blended, tinted per-frame by that fixture's reported colour (map×instanceColor). = real overlapping COLOURED petal shapes = the mandala. Performant (78 quads, not 78 spotlights). Verified in-browser TOP-DOWN+spectrum: full radial mandala of coloured petal flowers (red→purple around the ring), 0 errors, 79 tests. THIS is the projection milestone Elliot called key.
- [cycle 48] TOP-DOWN PROJECTION CAMERA + tighter gobo (conductor 0f274dea asks #1+#2) — store.cameraPreset hero|top + setCameraPreset; CameraRig positions straight-above looking down for 'top' (see the radial petal/mandala pattern); Controls 'camera' toggle (hero 3/4 | ⬇ top-down). Gobo cone penumbra tightened (×0.5, cap 0.4) so petals resolve crisply. Verified in-browser — TOP-DOWN + spectrum = the money shot: 78 lanterns in full rainbow wrapping the canopy radially, gobo projections visible, 0 errors. 79 tests.
- [cycle 47] 🎉 5/5 ASSETS INTEGRATED (blender f89a35c: tree-context.glb + Plu Plu bark 22MB + fixtures.json regen w/ TRUE per-fixture aim from .ejf). Bark auto-loads via TreeContext (semi-opaque 0.85 so glow leaks through), true aim auto-drives beams via schema-0.2 support. FULL real-geometry + real-photometric parity now LIVE: real petal gobo + IES cone + true aim + lantern bodies + bark shell + live colour ground-tint. Verified in-browser (bark visible, 78 lights, 0 errors, 79 tests). The Blender→twin pipeline is closed end-to-end.
- [cycle 46] LANTERN BODIES instanced (blender's downlight_lantern.glb: 17 meshes — body+ring+15 skirt strips, non-draco, real-world metres ~0.07×0.25m). LanternBodies.tsx: useGLTF → merge sub-meshes (position+normal) via mergeGeometries → InstancedMesh at 78 positions aimed by f.aim (schema 0.2), dim bamboo MeshStandardMaterial. Wrapped in ErrorBoundary. scale=1 = geometrically ACCURATE (intentionally small+dim — the LED source is HIDDEN in the tube per Elliot; the light stays beam+gobo+glow). Verified glb structure + 0 console errors + build/79 tests. NOTE: bodies are subtle at tree-zoom by design (correct realism).
- [cycle 45] IES PHOTOMETRY WIRED (blender-architect's downlight.ies) — ies.ts parseIES() reads the LM-63 profile (peak 450cd@0°, 50%@46.8°, ~0@57°) → beamDeg≈93.6, fieldDeg≈114. GoboFloor fetches /downlight.ies on mount + sets the SpotLight angle=fieldHalf + penumbra=(field-beam)/field → the floor cone now matches the REAL fixture photometrics (was a guessed 0.62rad). +3 unit tests (79 total). Verified in-browser (wider accurate cone, 0 errors). All 3 delivered assets now consumed (glb pending body-instancing; gobo+ies live).
- [cycle 44] REAL GOBO LANDED + WIRED (blender-architect pushed e7ab0b2: downlight_lantern.glb + gobo.png + downlight.ies via headless bake) — swapped floor SpotLight.map gobo-mandala.png → real gobo.png (skirt-petal projection). Combined with cycle-43 ground-tint = REAL COLOURED PETAL SHAPES on the floor, tinted by the live tree colour. Verified in-browser (spectrum → petal projection, 0 errors). NEXT: instance downlight_lantern.glb as the fixture body; fixtures.json 0.2 + bark tree-context.glb still pending (blender needs the organized scene).
- [cycle 43] LIVE GROUND TINT (conductor/Elliot milestone: 'real coloured shapes on the ground, not circles') — groundtint.ts shared mutable (zero re-render): TreeLights writes the tree's live aggregate colour (normalized hue + avg luminance) each frame; GoboFloor spotlight reads it in useFrame → floor projection is TINTED + brightened by what the tree is doing (was static warm). Works with current mandala gobo now, auto-upgrades to the real petal gobo.png when blender drops it. Verified in-browser (set magenta → floor glows magenta, 0 errors). 76 tests.
- [cycle 42] LLM OPERATOR (PRD #31) — llm.ts interpret(NL)→command-grammar lines: target words→zone/every/all, pattern names+synonyms (rainbow→spectrum, pulse→breathe, fire→ember…), CSS colours, fast/slow→speed, bright/dim→bri, vivid/pastel→sat, off/blackout→target off. Deterministic+offline (stand-in for the LLM policy; real LLM emits same surface). '🧠 say it' NL box in Controls → runScript. +8 tests (76 total). doc 13 tool-spec added. Verified in-browser: 'slow rainbow over the whole tree' → 'pattern spectrum · speed 0.5' applied, 0 errors.
- [cycle 41] SCHEMA 0.2 FORWARD-COMPAT (blender-architect co-build thread 6c772887: export bumps fixtures.json 0.1→0.2 w/ per-fixture aim + role) — Fixture.aim?[x,y,z] (Blender Z-up) → SimFixture.aim (three-space via blenderToThree, directions transform identically) → TreeLights uses REAL aim for beam orientation when present, else the down+outward heuristic. Validator soft-checks aim. Backward-compatible (gated on f.aim) → no regression now, auto-activates when their 0.2 fixtures.json lands. Also unblocked them on the Blender bridge (web-only my side; headless bake OK for assets). Build clean, 68 tests, 0 console errors.
- [cycle 40] SHOW COMPILER (PRD #29/F2) — showcompiler.ts: compileShow(cues,fixtures,base,channel,stepMs) → resonance.show/0.1 ShowDoc = deterministic per-fixture keyframe timeline of Protocol-v1 frames (params-not-pixels, channel-pinned, epoched) the CORTEX can replay browser-free. '⬇ compile show → JSON' button in Controls downloads it. +5 unit tests (68 total). Verified in-browser: clicking downloads resonance-show.json (schema ok, 78 fixtures, proto 1, 0 errors).
- [cycle 39] 5 NEW PATTERNS from research doc 14 (Elliot: 'get other patterns running', 'what other features') — spiral (rainbow barber-pole up the tree), godray (4 tight shafts sweeping azimuth), rising (band climbs trunk→canopy), planewipe (sheet of light sweeps through volume at rotating angle), warmcool (warm trunk/cool canopy w/ breathing split = depth). Added to PatternId+PATTERN_IDS+litFor; auto-appear as Controls buttons + DJ pads. NEW patterns.test.ts: every pattern+element id produces finite RGB in [0,1] across time, silent+loud audio (63 tests total). Verified in-browser (godray shafts). NOTE: new Blender geometry (bark/downlight bodies) NOT yet pushed — blender-architect still blocked on Blender reconnect; twin loads existing tree-context.glb.
- [cycle 38] BEAM-CAST GEOMETRY (Elliot: 'get the geometry right', 'more accurate', 'light shades create the real beam cast geometry', 'improve physics engine') — each beam cone now ORIENTED along its real cast direction: canopy downlights aim DOWN + fan radially OUTWARD from the trunk (they're tube-buried pointing down/out at the crowd), via quaternion setFromUnitVectors(DOWN, aim) per fixture. Replaces all-straight-down cones. Verified in-browser (spectrum beams splay outward = realistic radial cast). 45 unit green.
- [cycle 37] ENVIRONMENT SENSORS (Elliot: 'think about sensors — motion/people/temperature/wind', 'what other sensors'). sensors.ts: Sensors{crowd,motion,tempC,windKph,ambient} + pure applyEnv(control,sensors) — temp→warm/cool hue bias, wind→animation speed (capped 2.2x), crowd→energy/brightness, daylight→wash-down; windSway helper. Store sensors slice + setSensors. Controls panel 'environment sensors (sim)' with 4 sliders. Wired into TreeLights render via applyEnv. +5 unit tests (45 total). Verified in-browser (panel renders, build clean). On real hw these come from PIR/mmWave + temp probe + anemometer.
- [cycle 36] TRICOLOR ORBIT (Elliot: 'the three-colour projection design from the video — get it running') — upgraded the tricolor pattern to 3 triad hues (120° apart) in CRISP azimuthal sectors that ORBIT the trunk, each sector phase-offset-pulsing + (audio live) driven by its OWN band (sector0→bass, 1→mid, 2→treble) so the three colours dance against each other. sat floored 0.92 to keep them vivid/distinct. Verified in-browser (3 distinct gold/purple/green sectors around the tree).
- [cycle 35] SMOOTH TRANSITIONS (Elliot: 'smoother/better') — per-fixture 110ms low-pass colour slew in TreeLights so EVERY transition (pattern/cue/crossfade/colour) eases instead of hard-cutting. + RESEARCH doc 14: LED-art landscape (Tenere/Entwined/Chromatik lineage = our ancestor but NOT OSS; WLED EUPL-1.2 + WLEDtubes MIT = copy-safe) + 10 concrete new pattern algorithms (Canopy Dapple, Godray Shafts, Rising Sap, Tricolor Orbit, Warm/Cool Depth, Plane Wipe, Spectrum Spiral, Bloom, Particle Embers v2, Texture Scroll) + engine recs (shared phase clock, layered compositing, live-JS expr, temporal dither). Verified in-browser + 40 unit green.
- [cycle 34] VIRTUAL DJ CONTROLLER (Elliot ask: 'real virtual dj controller, spinning slider, buttons, the whole thing') — DjController.tsx: bottom console w/ 2 spinning platters (DECK A/B, spin rate = live BPM + beat boost), 3-band EQ knobs (LOW/MID/HIGH) + MASTER, crossfader A<->B, transport (SYNC/STROBE/AUTO-VJ/TRACK/MIC), 12-pad performance grid (all patterns + element modes). Wired to useTwin + audio engine. Pads aria-labelled to avoid e2e role collision. Verified in-browser (Playwright, 0 console errors); caught+noted PWA service-worker stale-cache gotcha (must unregister SW to see new build in preview). 40 unit green.
- [cycle 33] LIVE art-direction pass (Elliot, in-browser) — tightened beam RAYS (15° crisp shafts, 0.38×size throw, capped width) so downlights read as defined rainbow shafts not a flood; REDUCED brightness (GAIN 2.1→1.65, bloom 1.15→0.85/thresh 0.42, gobo 4.2→1.7); cut LIGHT POLLUTION between fixtures (ambient 0.35→0.16, fills down) → darker stage, each fixture distinct. Verified-by in-browser Playwright screenshots (spectrum/tricolor) + 40 unit green.
- [cycle 32] hardening — show-flow e2e (command script → save 2 cues → recall → play/stop timeline, 0 errors) + made the GL-heavy e2e suite reliable (workers:1, serial; retries:1) — verified-by npm run e2e 3 passed (2.5m) — APP-SIDE BUILD COMPLETE; remaining = hardware/cortex/env
- [cycle 31] IES-ish beam photometrics — photometry.ts beamIntensity/relativeBeam (lumens/cone-solid-angle: narrower=brighter) unit-tested; TreeLights scales each beam by its lumens_max+beam_deg; ready for the mixed HEX/RGBW fleet — verified-by build✓ npm test 40 passed + screenshots/cycle31-ies.png — next perf / polish / coverage
- [cycle 30] C3 guest-DJ scoped mode — guard.ts guestClamp (caps brightness≤0.8/master≤0.7, forces strobe off) unit-tested; 🔒 guest toggle; applied to effective control in the tick — safe handed-over controller — verified-by build✓ npm test 37 passed — next IES-ish falloff / perf / polish
- [cycle 29] control-matrix e2e + robustness — Playwright spec drives EVERY pattern/element/visualizer/seq-mode + command-console + DJ + auto-VJ + ping, asserts 0 console errors; FOUND+FIXED a remount churn (TreeLights no longer re-keys the InstancedMesh on viz change → unit-sphere scaled per-instance + wireframe/visible props; matters for long auto-VJ runs) — verified-by npm run e2e 2 passed (1.8m) — next guest-DJ / IES / perf
- [cycle 28] presence→ripple — interaction.ts rippleIntensity (expanding wavefront, fades ~2s) unit-tested; store.ripples + pingPresence; TreeLights brightens fixtures as the wave passes; ✨ ping button — the mesh-choreography interactivity — verified-by build✓ npm test 34 passed + screenshots/cycle28-ripple2.png (brightened ring) — next completeness audit / IES / guest-DJ
- [cycle 27] C2 WebMIDI — midi.ts ccToControl mapper (faders→brightness/hue/sat/speed/master/xfade) unit-tested + guarded WebMIDI engine (CC→params, note→cue recall) + 🎹 MIDI connect button/status; graceful when WebMIDI absent — verified-by build✓ npm test 30 passed + screenshots/cycle27-midi.png — next completeness audit + presence-ripple
- [cycle 26] F2 cue timeline — play toggle cycles saved cues in order, holding each stepSecs (loops); nextCueIndex unit-tested; TimelineDriver + transport in Controls — completes jam→lock→schedule — verified-by build✓ npm test pass + screenshots/cycle26-timeline.png (timeline cycling A→B) — next C2 WebMIDI / completeness audit
- [cycle 25] G3 PWA + README — vite-plugin-pwa (autoUpdate, manifest, SW precaches app shell + runtime-caches glb/png/json/wav → offline after first load); app/README.md (run/features/grammar) — verified-by build✓ (sw.js+manifest generated) npm test pass + screenshots/cycle25-pwa.png — next F2 timeline / G4 perf / A6 IES
- [cycle 24] F1/D5 cue system — save current look as a named cue + recall + delete, localStorage-persisted; cues.ts pure (makeCue/load/save) unit-tested; cue panel in Controls — verified-by build✓ tests pass + screenshots/cycle24-cues.png (saved spectrum → solid → recalled → restored) — next F2 timeline / G3 PWA
- [cycle 23] D4 element modes — wind (sway ripple+dim, teal) · ember (warm flicker) · rain (silver-blue cascade by heightT) · beacon (white lighthouse sweep, whiteout-safety) added as patterns + element-modes UI row — verified-by build✓ + screenshots/cycle23-beacon.png (white sweep) — next F2 cue/timeline / G3 PWA
- [cycle 22] G2 fixtures.json validation — pure validateFixturesDoc (checks meta+bbox + per-fixture id/position[3]/zone/beam_deg → {ok,errors[]}); wired into App load (errors → banner); unit-tested valid/invalid (23 tests pass); ready to gate a swapped real Grasshopper export — verified-by build✓ + screenshots/cycle22-validate.png (real doc valid, no banner) — next D4 element modes
- [cycle 21] E/I8 ESP-NOW control plane — protocol.ts Protocol-v1 param ENCODER (per-fixture {pattern,bri,hue,rgb?} CONTROL PARAMS not pixels; channel-pinned ShowFrame) unit-tested (4 tests); control-plane panel (channel 1-13 + 📡 drive-real stub + live packet preview); honors ADR 0004/0010 — verified-by build✓ npm test 19 passed + screenshots/cycle21-protocol.png — next G2 fixtures.json validation / D4 element modes
- [cycle 20] F1 LLM-console — multi-line command runner (textarea → store.runScript → each line via runCommand, the LLM's tool surface) + parseScript (drops blanks/# comments) unit-tested + command.test.ts (grammar) + docs/research/13 LLM grammar tool-spec — verified-by build✓ npm test 15 passed + screenshots/cycle20-llmscript.png (3-command script: solid + high-zone blue + every-4 red) — next more sequences / E cortex-bridge / G2 validation
- [cycle 19] D auto-VJ — shuffle-bag look switching (pattern+visualizer+hue) on phrase boundary (phraseSeconds from BPM × autoBars, fallback timer); autovj.ts pure (ShuffleBag/phraseSeconds/LOOKS) unit-tested; 🤖 auto-VJ toggle + bars in Controls — verified-by build✓ npm test 11 passed + screenshots/cycle19-autovj.png (auto-switched to spectrum) — next F LLM-console / more sequences
- [cycle 18] C DJ controller — crossfader A↔B look blend (2× litFor lerp) + 3-band EQ→tree-zone gain + master intensity + strobe gate; dj.ts pure helpers (eqGain/strobeGate/lerp) unit-tested; scrollable panel — verified-by build✓ npm test 8 passed + screenshots/cycle18-dj.png — next D auto-VJ / F LLM-console
- [cycle 17] P0 FIX (conductor caught) — app was BLANK on fresh clone: gobo-mandala.png was untracked → texture 404 → Suspense hang. Committed the asset + added per-asset ErrorBoundary around GoboFloor/TreeContext so a missing asset degrades gracefully (never blanks). — verified-by build✓ + screenshots/cycle17-assetfix.png — next C DJ controller
- [cycle 16] A7 multiple visualizers — render-style switch: lanterns (spheres+beams) / orbs (big blooming) / wire (wireframe data look, beams off); viz selector in Controls — verified-by screenshots/cycle16-{orbs,wire,lanterns}.png (3 distinct looks) — next C DJ crossfader
- [cycle 15] B live wiring — BPM→sequencer tempo (sync-to-beat toggle + ¼/⅛ div; stepMs=beatStepMs(bpm,div)) + onset→flash + DROP detection→burst; beatStepMs unit-tested (124→484, 140→429); 140bpm-drop test track added — verified-by build✓ npm test 4 passed + screenshots/cycle15-beatsync.png — next: real-browser audio confirm + C DJ crossfader / A7 visualizers
- [cycle 14] A5 gobo projection — ground plane (receiveShadow) + downward SpotLight map=gobo-mandala.png (shadows on, target below tree), mandala projected on the ground + lantern/structure shadows — verified-by screenshots/cycle14-gobo.png (radial mandala on ground) — next: BPM→sequencer tempo + drop→burst (with unit test), then A7 visualizers / C DJ
- [cycle 13] B BPM PROVEN — extracted beat math to pure BeatTracker (beat.ts) + Vitest: detects 124 BPM from a 124-bpm impulse train AND 90 from a 90-bpm train (deterministic, hardware-independent). Confirms the headless ~83 was the audio path, not the algorithm. audio.ts refactored to use it. — verified-by `npm test` 3 passed — next A5 gobo + real-browser audio confirm
- [cycle 12] B audio spine — audio.ts rewrite: spectral-flux onset (bass band) + interval BPM + asymmetric attack/release envelope followers (bass/mid/treble) + AGC + track player + beat→flash; "🎶 test track" button + live BPM readout — verified-by screenshots/cycle12-audio.png (reactive, 0 errors). ⚠ BPM read ~83 on the 124bpm track IN HEADLESS (headless audio timing unreliable) → needs real-browser verification + BPM-accuracy tuning (next). onset-reactivity works. — next: real-browser BPM verify + A5 gobo
- [cycle 11] spectrum + tricolor-dance patterns + ACES tonemapping — full-spectrum rainbow around the tree + 3-color dancing + filmic tonemap after bloom — verified-by screenshots/cycle11-spectrum.png (gorgeous full-rainbow tree, colored beams) — next A5 gobo (conductor supplied gobo-mandala.png) + B audio (Meyda/BPM)
- [cycle 10] A4 volumetric beams — additive downward cones per fixture, beam-angle sized (beamDeg), colored by reported state; tuned bloom/gain so it's pro not blown-out — verified-by screenshots/cycle10-beams.png (glowing lanterns + tasteful beam wash, reads beautifully as the tree) — next: full-spectrum/tricolor patterns + B audio beat/BPM
- [cycle 9] D1 bloom + VISUAL FIDELITY — bloom (HDR gain), visible warm bamboo material + key/rim lights + hero camera — verified-by screenshots/cycle9-hero.png (NOW LOOKS LIKE THE RESONANCE TREE: bamboo lattice + glowing lanterns) — next I2 real audio beat/BPM sync + I1 beams/gobo
- [cycle 8] G1+F3 truth loop — mock-heartbeat transport (held reports + jitter + dead fixtures) + Monitor (red no-signal markers + reporting/dead/stale readout); TreeLights renders reported buffers — verified-by screenshots/cycle8-monitor.png ("reporting 72 · dead 6 · stale 0", 6 red markers) — next D1 bloom
- [cycle 7] H6 tree-context backdrop — bg agent's decimated bamboo glb (2364 meshes, 10.4MB) wired as faint backdrop; tree now reads as a tree — verified-by screenshots/cycle7-tree-context.png (canopy silhouette behind 78 lights) — next G1 mock-heartbeat + F3 Monitor
- [cycle 6] H3 any-command console — command.ts parser (clear/on/off/globals + targeted overrides by all/zone/range/every/fixture) + per-fixture override layer + Controls input/chips/log — verified-by screenshots/cycle6-cmd-every4-red.png (live "every 4 color red" → 20 fixtures red, 0 errors) + build+e2e green — next: G1 mock-heartbeat + F3 Monitor (top audit pick), then D1 bloom + H6 tree geometry (bg agent running) / H6 tree context geometry
