beneckart/resonance-lighting/docs/tests/SOLAR_FIELD_CYCLE_P105_P126_2026-07.md

# P105/P126 outdoor solar field cycle and POR-loop findings -- July 2026

**Status:** Active bench record. Final P105 safety firmware was OTA-deployed July 13;
the production-RGBW ceiling profile and active-integrator fix were OTA-deployed July 14,
and the RGBW was installed before dusk. The original P126 peer was then disassembled
and retired after a header-rework hardware failure; replacement `9F2690` completed the
first VDC-capacitor solenoid trial. The paired replacements completed a clean seven-day
logger run on July 24. The trial's VDC + 10,000 uF result was subsequently promoted
to the finalized ADR 0030 solarnoid concept with 22,000 uF and a stronger-solenoid
bake-off; those later experiments are tracked separately. The P105 external INAs are
next scheduled for removal for a production-harness A/B.

## Purpose

This run combines two related questions:

1. What daily energy range can the production-cabled Voltaic P126 2 W panel deliver
   into a production 32700 LFP/PowerFeather fixture?
2. Why did the adjacent P105/HEX peer enter early nighttime power-on-reset (POR)
   loops, and what must firmware do so any POR source cannot recreate a full-load
   boot loop?

The two peers are useful A/B references but are not identical instruments. P105 has
external panel/battery INAs and a TSL2591. P126 deliberately uses production cabling,
no INAs, no Dupont leads, and no lux sensor.

## Devices and deployed images

| Peer | Panel/load | Instrumentation | Image/status |
|---|---|---|---|
| `9E5B0C` (historical) | P126 2 W, fixed 5.8 V; three full-bright single-channel R/G/B HEX pixels spiraling at 120 deg offsets | PowerFeather BQ/MAX17260 only; production cables | `net-bench-2026-07-10.1`; disassembled July 13 and board retired after header-rework failure |
| `9F2690` (replacement) | Same P126/HEX profile plus manual D7/VDC solenoid strike | Onboard telemetry; production cables; 10,000 uF cap trial on panel-input adapter | `net-bench-2026-07-13.3`; safety-verified July 13; no-cap weak / cap-assisted strike qualitatively strong July 14 |
| `9F26F8` | P105 5 W, fixed 4.6 V; one rail-fed 4 W RGBW point source, RGB full/W off | PowerFeather telemetry and TSL2591; external-INA status at swap was not recorded | `net-bench-2026-07-14.1`; OTA verified and RGBW installed before dusk July 14 |

P126 logger:
`ops/bench/data/ca/2026-07-10-ca-field-cycle-9E5B0C-p126-production-cabling.jsonl`.

Completed paired seven-day logger:
`ops/bench/data/ca/2026-07-17-ca-field-cycle-9F26F8-9F2690-weather-range-r2.jsonl`.

P105/P126 share the master/logger, so the same file also captures the P105 peer after
the July 10 P126 deployment. Earlier P105 history is in the July 3-8 field-cycle files
under `ops/bench/data/ca/`.

### P105 production-RGBW ceiling run -- armed July 14

The July 13-14 P105 HEX stress night delivered 4.505 Ah / 14.7 Wh over about 9.76 h,
then reached the 3.6 V CV/taper region by about 15:15 the next day. To remove the main
load mismatch, `net-bench-2026-07-14.1` changes only the LED profile to one 4 W RGBW
point source on the switchable 3V3 rail and A0/GPIO10: measured RGBW wire order,
`R=G=B=255`, `W=0`, brightness 255. Fixed P105 4.6 V VINDPM, charge/wait/protect
sleeps, lux thresholds, ramp, DIM/LOW/CRITICAL thresholds, durable session guard, and
recovery policy are unchanged.

The same image fixes the retained active-time integrator by carrying the sub-second
millisecond remainder instead of discarding it on every `dt / 1000` step. This changes
telemetry accounting only, not state transitions or load policy. Artifact:
`firmware/net_bench/build/field-cycle-peer-20260714-p105-rgbfull-r2/net_bench.ino.bin`,
SHA-256 `B7C75B53F278CE3A87E3301A376578569C994A51030E1F48EC3B42D233367FA6`.
Targeted shared-WiFi OTA completed at about 17:29 PDT and the peer rejoined ESP-NOW as
`.1`, software reset, still in daylight wait with no DIM or PROTECT latch. The first
75 s discovery attempt safely expired without uploading because it missed the peer's
300 s sleep / 8 s listen window; the successful retry used 360 s, now the helper
default. Ben installed the physical RGBW before dusk.

The peer entered DRAW at 20:29:37 PDT after the five-minute low-lux qualification.
The first DRAW heartbeat carried about 102 lux; by 20:54 the light sensor read about
7 lux and the rail-fed RGBW was stable at 3.295 V / -414 mA = 1.364 W battery-side,
with no DIM/PROTECT latch or fault reset. This agrees almost exactly with the earlier
417.6 mA full-RGB bench measurement. The corrected retained integrator rose 178 mAh
over the first 1,535 DRAW seconds, equivalent to 417.5 mA average. The absolute
counter included a 238 mAh pre-DRAW cycle baseline from charge/wait sleep-current
estimation: `field_elapsed_s` is phase-local, but discharge Ah/Wh are cycle-total, so
analysis must subtract the counter at the DRAW boundary.

### P126 VDC solenoid trial -- staged July 13, first capacitor result July 14

The next P126 experiment adds an Adafruit #5648 MOSFET driver on D7/GPIO37 with its
load supply tapped from VDC/GND. The first bright-sun trial deliberately omits the VDC
storage capacitor to answer whether the panel/BQ input path can deliver a useful strike
without it. Begin at one 40 ms pulse; record physical actuation, reset reason, supply
collapse, and post-strike telemetry before changing pulse width or adding capacitance.

`net-bench-2026-07-13.3` implements targeted manual-only strikes, timer plus loop
gate-off protection, a 5-300 ms hard range, 80 ms rest guard, and gate LOW across boot,
OTA, maintenance, and sleep. The driver schematic includes a 10K signal pulldown and
flyback diode. Its input therefore remains off while older firmware leaves D7
high-impedance. The P126 image retains the fixed 5.8 V and three-pixel spiral profile.
The original `9E5B0C` never received it and was retired after the failed header rework.
Replacement `9F2690` was USB-flashed July 13; direct telemetry verified `.3`,
`solenoid_enabled=true`, GPIO37, gate LOW, and zero strike/block/failsafe counters.
Solar and the driver were still disconnected at verification, so the no-capacitor
bright-sun strike remained the next hardware step at that point.

July 14 qualitative result: the panel-only/no-storage-capacitor strike was weak. Adding
a 10,000 uF, 16 V electrolytic directly across the panel adapter's V+/GND made the kick
dramatically stronger; Ben's assessment was that it was both effective and a design he
liked. This was not a quantified strike-energy result, but it moved VDC + local
storage from an alternative to the leading production candidate at the time. ADR 0030
later finalized the solarnoid around a 22,000 uF store and stronger-solenoid bake-off.

The tested cable/adapter stack was:

```text
Voltaic panel 3.5 x 1.1 mm male DC
  -> Voltaic female DC-to-male-USB-C adapter
  -> female USB-C-to-four-pin JST-XH breakout
  -> V+ and GND alone rehoused into two-pin XH
  -> PowerFeather VDC/GND
```

The capacitor leads happen to align directly with the V+ and GND through-holes on the
USB-C/XH breakout, so the addition took roughly one minute of soldering and no bare-wire
PowerFeather work. The prototype 10,000 uF/16 V parts cost roughly $1 each from Amazon;
volume price is expected to be lower but has not been sourced.

Remaining qualification: capture coil/pulse/VDC/recharge telemetry, repeated-strike and
hot-plug behavior, BQ/reset/fault response, dusk discharge/residual energy, capacitor
ESR/tolerance/temperature/lifetime, strain relief, and cold-Voc voltage margin. P126's
published nominal Voc is about 8.59 V; measure worst-case cold Voc and production
tolerance to document the derating margin of the successful 16 V part.

## Executive read

- The P126 load is representative of the intended production HEX show. Do not raise
  it merely to force a full-to-empty cycle every night.
- The P126's instantaneous input-loss dusk rule created a 14 h 46 min LED window.
  That is a bench-policy artifact, not the intended playa show. Civil dusk to civil dawn during the Aug 30-
  Sep 7 event is about 9 h 53 min to 10 h 15 min, so use 9-10 h for HEX energy sizing.
- At the measured 157.7 mA average battery draw, a 9 h show costs about 1.42 Ah and a
  10 h show about 1.58 Ah. The good July 11 solar interval put about 1.74 Ah into the
  battery, provisionally leaving +0.32 Ah at 9 h or +0.16 Ah at 10 h.
- The observed P126 daily range so far is about 1.12-1.55 Ah at the 5.8 V BQ input,
  or about 1.11-1.74 Ah of positive battery charge. These are only two weather days,
  and the battery number is acceptance- and sampling-limited.
- P126 has avoided POR primarily because its roughly 158 mA show is about one-third
  of P105's 460-480 mA draw and its production harness is lower resistance. It has
  stayed around 3.24-3.33 V instead of exercising the marginal low-voltage region.
  This does not prove its older reset policy safe.
- P105's dense loop was a firmware-amplified loaded-collapse problem: a POR erased
  dim/protect state and confirmation timers, rebound voltage looked healthy on reboot,
  and firmware reapplied the full LED load until the next POR. A power-path I2C glitch
  can create the same reset signature, so the loop breaker must be independent of the
  initiating cause.

### Seven-day P126 follow-up -- do not size from the artificial show window

The clean 604,800-second paired logger run from 2026-07-17 10:18 PDT through
2026-07-24 10:18 PDT extended the weather range. Integrating fresh telemetry into seven
consecutive 24-hour windows gives the replacement P126 fixture approximately:

| Quantity | Seven-day total |
|---|---:|
| BQ/fixture input | 52.3 Wh |
| Positive battery charge | 35.0 Wh |
| Battery discharge/load | 48.6 Wh |
| As-run battery balance | -13.6 Wh |

Some individual windows have 18.5-22.0 hours of usable telemetry, so the affected
daily values are lower-confidence. The week-level interpretation is nevertheless
clear: the no-lux bench policy still kept the LEDs on for roughly 13-15 hours on most
complete nights, close to the earlier directly measured 14.773-hour session. That is
not the production show duration.

At the measured 157.7 mA average whole-fixture draw, a scheduled 9-hour show is about
1.42 Ah / 4.6 Wh and a 10-hour show is about 1.58 Ah / 5.1 Wh. Normalizing the same
seven days to that 9-10 hour production window yields roughly 32-36 Wh of load versus
about 35 Wh charged. Therefore:

- the literal bench result ("every 24-hour window energy-negative") is true for the
  overlong as-run show;
- it is not evidence that the P126 2 W production role is undersized;
- this weather week is approximately break-even after schedule normalization, with
  little poor-weather margin and some telemetry uncertainty;
- future charts and sizing summaries must show both the as-run bench load and the
  schedule-normalized production load.

Production direction as of 2026-07-26 is deterministic scheduled dusk/dawn operation
from a sparse fleet of external GPS/GNSS and battery-backed RTC time anchors (ADR 0031),
not continued refinement of panel-current-only dusk inference. Local panel/lux
telemetry remains useful for diagnostics and optional degraded-mode policy.

## P126 MPP and daily harvest

### Fixed MPP result

The July 10 onboard re-check found a broad best region around 5.8-6.0 V. The apparent
6.0 V charger-input gain was only about 3.8 percent and produced no corresponding
battery-current gain; 6.2 V rolled over. Two 5.8 V anchors agreed within 0.4 percent.
Keep the external-INA-qualified P126 setpoint at **5.8 V**.

### What "Ah/day" means on this peer

There is no panel-lead INA, so there is no direct panel-terminal Ah measurement.
Record all three quantities and do not substitute one for another:

- **BQ input Ah:** integral of positive onboard `supply_ma`. At fixed 5.8 V this is
  the best available day-to-day panel/charger-input comparison.
- **BQ input Wh:** integral of `supply_v * supply_ma`; preferred when comparing energy.
- **Positive battery Ah:** integral of positive corrected `battery_ma`. This is what
  reached the cell after conversion and the live system load, but it is also affected
  by battery charge acceptance and sparse sleep sampling.

`battery_ma` on the P126 image already includes the measured MAX17260 `/1.08`
correction. Never divide it again. BQ supply current does not receive that correction.

### Preliminary rolling ledger

One-second cached sample-and-hold integration, with host gaps over 5 seconds excluded:

| Local date | Coverage | BQ input | BQ input energy | Positive battery charge | Interpretation |
|---|---:|---:|---:|---:|---|
| Jul 10 | 0.72 h | 0.166 Ah | 0.95 Wh | 0.190 Ah | Partial deployment afternoon; not a daily result |
| Jul 11 | 16.56 h | 1.545 Ah | 9.02 Wh | 1.738 Ah | Best observed sunny day; host resumed before useful P126 input began |
| Jul 12 through about 18:00 | 17.93 h | 1.116 Ah | 6.51 Wh | 1.114 Ah | Sunny then overcast; provisional weaker-day point |

The input-Ah and battery-Ah columns may look inverted because the buck charger trades
the roughly 5.8 V input for higher current at roughly 3.3 V. Compare Wh across voltage
domains. Input-to-battery differences also include conversion loss and the awake system
load.

The purpose of any remaining P126 deployment is to grow this weather-conditioned range,
not to validate the current 14.8 h show duration. For each additional local day record:

1. BQ input Ah and Wh;
2. positive battery Ah and Wh;
3. sky condition and any shading/handling;
4. logger coverage and whether a number is complete or a lower bound;
5. minimum loaded VBAT and any reset/protect event.

Do not use MAX17260 SOC percent for this ledger. It has previously stuck at 1 percent
with roughly 35 percent of cell capacity remaining. Coulomb integration against the
measured roughly 5,500 mAh usable capacity is the relevant battery-state estimate.

## Production HEX show duration

The clean July 11-12 P126 session ran from 18:07:33 to 08:53:54 PDT:

- wall-clock LED window: 14.773 h;
- logger-integrated battery draw: 2.33 Ah;
- mean corrected draw: 157.7 mA;
- dawn loaded/resting region: about 3.27 V; no dim, protect, or POR.

The deployed July 10 peer has no light sensor and predates the July 12 dusk qualifier.
It declares dusk immediately when charger input stops meeting the useful-input test and
ends draw when useful input returns. It can chatter through new cycles as input crosses
that boundary and can start well before visual darkness or run well after dawn. The
30-minute no-sensor confirmation exists in `net-bench-2026-07-12.1`, but that image was
deployed only to P105 and is not running on P126.

Black Rock Desert tables for event week give about 19:59-19:46 civil-dusk end and
05:52-06:01 civil-dawn start. That is a roughly 9 h 53 min to 10 h 15 min dark-show
window. Provisional sizing:

| Show duration | Draw at 157.7 mA | Net after the Jul 11 1.74 Ah charge estimate |
|---:|---:|---:|
| 9 h | 1.42 Ah | +0.32 Ah |
| 10 h | 1.58 Ah | +0.16 Ah |
| 11 h | 1.73 Ah | about break-even |
| 14.77 h bench artifact | 2.33 Ah | -0.59 Ah |

This is encouraging, not yet a production margin. Playa heat, dust, panel angle,
fixture shading, smoke/clouds, battery taper, and incomplete telemetry can consume the
small 10 h surplus. The qualified cell provides multi-day buffering, but final sizing
needs more daily harvest points and the actual show profile.

Sources:

- https://www.timeanddate.com/sun/@5701651?month=8
- https://www.timeanddate.com/sun/@5701651?month=9
- https://burningman.org/black-rock-city/ticketing-information/

## P105 POR boot-loop reconstruction

### Observed symptom

On July 11, P105 began a dense series of `reset_reason=poweron` boots around loaded
VBAT 3.00-3.05 V after only about 0.68 Ah had been removed from a recently full cell.
This was far earlier than the qualified cell's hard knee. The board repeatedly booted,
reapplied the 18-pixel brightness-128 load, collapsed, and booted again. A final sample
at or below the immediate critical floor eventually allowed protect to latch.

### Firmware regression chain

1. The July 7/8 ADR23 image moved the loaded protection region down. Earlier firmware
   generally exited near 3.10 V; `net-bench-2026-07-08.1` dimmed only after 60 seconds
   at or below 3.00 V, protected after 60 seconds at or below 2.95 V, and used 2.90 V
   as the immediate critical floor.
2. The heavier P105 load could collapse the source before the dim decision was reached
   or confirmed. Added harness resistance can shift that boundary upward, although the
   unchanged harness does not explain why the firmware behavior changed.
3. Dim/protect latches and phase state lived in RTC memory. Timer deep sleep preserves
   them; a true POR does not.
4. The 10/60 second confirmation timers lived only in RAM/RTC state. Every POR reset
   them to zero.
5. On reboot, load release raised the measured battery voltage above the low threshold.
   With no remembered active session, firmware interpreted the rebound as permission
   to enter drawdown and reapplied the full load.
6. The reset could recur faster than either confirmation timer, making the intended
   low-voltage policy unreachable indefinitely.

There was a second, independent trigger problem: daylight required both supply voltage
and useful current. A full/tapered battery could stop accepting current, which firmware
misread as darkness. It briefly turned the LEDs on in the afternoon, then saw input
current return and declared sunrise. This created false cycles and could expose the
power path earlier than visual dusk.

### Initiating cause versus loop amplifier

The July 11 evidence best fits extra loaded droop plus the lower firmware thresholds;
the INA harness can plausibly move the knee by tens of millivolts. That is not the only
way to get a POR. A corrupted I2C transaction to the BQ25628E power-path registers can
open the battery switch at healthy voltage, as established by ADR 0028. Either event
looks like `reset_reason=poweron` because VSYS disappears.

Firmware must therefore treat an unexpected reset during an armed LED session as the
primary fact. It must not depend on distinguishing cell sag, connector resistance,
I2C upset, brownout, watchdog, or panic before making the next boot safe.

## `net-bench-2026-07-12.1` recovery policy

The July 12 P105 image was built with 18 pixels at brightness 128, 6,000 mAh LFP,
1,500 mA charge limit, fixed 4.6 V VINDPM, and these field thresholds:

- dim at or below 3.10 V for 10 seconds;
- LED off/protect at or below 2.95 V for 60 seconds;
- immediate critical protect at or below 2.90 V;
- TSL2591 dusk at or below 200 lux for five minutes;
- separate dawn threshold at or above 500 lux;
- bare-peer fallback: 30 minutes without useful input.

The exact artifact is:
`firmware/net_bench/build/field-cycle-peer-20260712-p105-dusk-dim-retry-r3/net_bench.ino.bin`.
Its full compiler flags are preserved beside it in `build.options.json`.

The reset guard is a cause-independent state machine:

1. Before LED rail-on, persist `idle`, `full`, `dim`, or `protect` in NVS. NVS write
   failure parks safely.
2. At the first instructions of boot, force pixel data and EN_3V3 low. `Board.init()`
   can reconfigure the RTC-held rail, so park it low again immediately after init.
3. An unexpected reset from persisted `full` atomically consumes the sole retry by
   storing `dim` before any rail can turn on. It may then retry once at dim brightness.
4. Any reset from `dim` or `protect`, or a failed NVS read, hard-parks with the LED rail
   off until verified positive battery charge. A second collapse cannot recreate the
   full-power loop.
5. A deliberate load start waits for power/network initialization, clears the pixel
   rail, ramps brightness in four steps, and samples VBAT during the ramp. A low sample
   parks; a dim-region sample reduces the target.
6. Only verified solar/USB charge recovery clears the persisted session stage.

Telemetry added for remote diagnosis:

- `field_session_stage` and `field_session_marker`;
- `field_interrupted_boot`, `field_interrupted_retry`, and
  `field_interrupted_park`;
- `field_dusk_s`;
- existing `field_phase=5`, `field_reason=8`, and `field_protect_latched=true` identify
  a hard-park in the ESP-NOW heartbeat without another protocol-tail change.

OTA completed without a button press. Direct `/telemetry` confirmed the new revision,
idle session stage, valid PowerFeather init, and normal charge state; `/resume` returned
the peer from maintenance to ESP-NOW. Natural low-voltage POR retry/park behavior still
needs an autonomous field observation or a controlled bench injection before it is
called fully validated.

## Reusable POR and telemetry gotchas

1. **A POR erases the safety decision that was about to happen.** Any timeout, debounce,
   coulomb budget, or dim latch stored only in RAM/RTC can be defeated forever by a
   faster reset loop. Persist the armed load tier before energizing it.
2. **Rebound voltage is not recovery.** Removing a load raises LFP voltage. Do not use
   that rebound alone to authorize the same load after reset; require a persisted retry
   budget or verified positive charge.
3. **Default-off must begin before SDK initialization.** PowerFeather cold init enables
   the switchable rail, GPIO4 is RTC-held, and raw `digitalWrite` is ineffective after
   SDK init. Drive/hold it low first, use the SDK correctly, and park it again after init.
4. **Consume retry state before rail-on.** Persisting `dim` after starting the retry
   leaves a power-fail window that recreates the loop.
5. **Ramp startup loads.** A rail enable plus stale pixel data plus WiFi startup can
   stack transients before steady-state low-voltage logic runs.
6. **Dusk needs qualification and hysteresis.** Charger current alone is not daylight;
   full-battery taper, shade, and clouds create brief low-current intervals.
7. **`poweron` has multiple physical causes.** Real loaded collapse and a BQ battery-
   switch opening both remove VSYS. Keep ADR 0028's 100 kHz/shared-bus rules even after
   adding the NVS loop breaker.
8. **Harness resistance changes loaded thresholds.** Apply load compensation or qualify
   each production power path; do not copy a voltage threshold from a different current
   and harness without margin.
9. **Onboard active-time integration currently under-reports.**
   `fieldCycleIntegrateActive()` truncates every `dt / 1000` and resets the millisecond
   origin, losing the remainder. The 14.773 h session reported 13.02 h / 2.08 Ah instead
   of the logger's 14.773 h / 2.33 Ah, about 12 percent low. Carry milliseconds across
   calls before trusting retained active mAh/Wh.
10. **Deep-sleep charging is sparsely sampled.** A five-minute held current estimate is
    useful but not ground truth during fast cloud edges. Always label coverage and
    uncertainty.
11. **Cached protect current is not continuous current.** The host repeats the last
    heartbeat while the peer sleeps. State-aware integrations must not charge that
    stale value across the protect interval.
12. **BQ input is not panel-side ground truth.** It is still the best available P126
    day-to-day proxy, but external panel-lead instrumentation remains the qualification
    reference.

## Production power-policy hardening plan (2026-07-13)

### Working interpretation

Assume the P105's unexpectedly early collapse was dominated by the resistance and/or
intermittency of its external INA harness. This changes how the P105 voltage points are
interpreted; it does not justify removing the safety mechanisms the event exercised.
A production fixture can produce the same reset signature through a poor crimp, aging
or cold-cell resistance, a connector fault, an abrupt LED frame, or a BQ power-path /
BATFET disconnect after an I2C upset.

Treat the bad harness as a fault-injection test. Preserve cause-independent recovery,
then re-derive its numeric thresholds on the production electrical path.

| Firmware behavior | Production disposition | Reason |
|---|---|---|
| Force the LED rail off at the first boot instructions and after board init | Keep | A stale LED frame or SDK rail side effect must not energize the load during recovery. |
| Persist intended `full` / `dim` / `protect` tier before rail-on | Keep | A POR must not erase the safety decision that the load was active. |
| Allow one pre-consumed DIM retry, then hard-park | Keep | Recovers from a one-off transient without recreating an unlimited boot loop. |
| Preserve PROTECT across POR, watchdog, and OTA software reset | Keep | Reset type is not proof that the battery or power path recovered. |
| Stage LED startup and sample loaded VBAT during the ramp | Keep mechanism; tune duration by load class | It bounds inrush and exposes delayed sag before steady-state policy runs. |
| Latch night and require positive dawn evidence | Keep semantics; replace bench sensor constants | A missing lux or current sample is unknown, not sunrise. |
| Correct MAX17260 current by `/1.08`; ignore RepSOC for gates | Keep | This is replicated gauge behavior; RepSOC is not trustworthy on the LFP plateau. |
| P105 special 3.10 V dim threshold | Recalibrate | It was selected around an 18-pixel stress load on the instrumented harness. |
| 3.00 / 2.95 / 2.90 V standard tiers | Starting point only | ADR 0023 requires known-load evaluation, load compensation, and cold/variance margin. |
| Clear PROTECT from one `battery_ma >= +20 mA` sample | Strengthen before production | One borderline sunrise sample can be bias or a transient, not restored load capacity. |
| Field-cycle charge/wait/full telemetry cadence | Bench-only | It measures cycling; it is not the production show or low-battery state machine. |

The healthy-harness cost of the retained protections is small: one staged start at
show onset and a few durable state writes at transitions. The retry delay and park path
run only after a fault.

### Phase 1 -- production-harness A/B

1. Remove the P105 panel/battery INAs and Dupont/instrumented interconnects. Use the
   intended cable gauges, crimps, and connector path.
2. Leave `net-bench-2026-07-13.2`, the cell, panel, LED load, and thresholds unchanged
   for the first complete dusk/show/recovery cycle. Do not tune out the symptom before
   measuring the electrical change.
3. Record, from onboard telemetry and the reset/session markers:
   - pre-load or lowest-available low-load VBAT;
   - VBAT and battery current through each startup-ramp step;
   - minimum steady full- and DIM-load VBAT;
   - selected tier, reset reason, retry count, and final persisted stage;
   - charger state, battery current, and VBAT used to release PROTECT; and
   - any missing lux/I2C sample around a state transition.
4. Compare load-step sag, stable current, and resets against the July 13 instrumented
   values: roughly 493-506 mA / 2.93 V at full and 299-308 mA / 3.07-3.09 V at DIM.

Interpretation:

- A materially smaller sag and stable show supports the harness hypothesis. Retain the
  reset guard and move the P105 3.10 V value back into the calibration queue.
- A reset that persists on production wiring keeps the BQ/BATFET-disconnect hypothesis
  open. Capture charger/gauge reachability and reset reason before changing thresholds.
- Regardless of the initiating cause, the safety pass criterion is no repeated full-
  load loop: at most one DIM retry, followed by a rail-off durable park.

### Phase 2 -- strengthen recovery from PROTECT

Replace the current single-sample release with a compound recovery gate. Do not use
MAX17260 RepSOC. Production release requires all of:

1. valid external input and a BQ charging/no-relevant-fault indication;
2. corrected positive battery current sustained across a defined interval or multiple
   wake observations;
3. VBAT above a separately measured restart floor with hysteresis; and
4. preferably, a small positive-coulomb recovery budget accumulated since PROTECT.

Derive the exact current, time/sample count, VBAT, and coulomb constants from the
production-harness recovery trace. The July 13 morning release at about +24 mA, only
4 mA above the present gate, is specifically not sufficient evidence by itself. Weak
sun may delay recovery, but it must not repeatedly re-arm a load the source cannot yet
support.

### Phase 3 -- qualify thresholds by production electrical class

1. Exercise each distinct battery-to-LED power path at its worst credible show frame,
   not only the 18-pixel P105 stress pattern or the three-pixel P126 pattern.
2. Start from ADR 0023's standard loaded tiers: dim 3.00 V, LED-off 2.95 V, sparse
   sleep 2.90 V. Keep the P105 3.10 V dim point as a temporary bench override only.
3. Measure effective path resistance and either evaluate at a known load or implement
   `bv_comp = bv + R_path * I_load`. Do not copy raw loaded thresholds between fixture
   classes with different currents or cabling.
4. Repeat at the expected cold boundary and with production cell/connector variance.
   The existing room-temperature n=2 result is not a cold qualification.
5. Make corrected coulomb remaining the primary energy estimate, anchored to measured
   usable capacity. Use the 15 / 7 / 5 percent dim/off/sleep targets from ADR 0023;
   retain voltage as the immediate safety backstop. Gauge RepSOC remains advisory.
6. Fix the retained integrator's lost-millisecond remainder and quantify onboard
   coulomb error against an external reference before using it for production gates.

Only low energy enters PROTECT/sparse-wake behavior. Routine charge-phase timer sleeps
may reduce MCU telemetry energy because the BQ continues charging autonomously, but
they must not declare the cell full, end harvest, or authorize a show from weak input.

### Phase 4 -- deterministic transition tests

The production state machine is not accepted from an outdoor happy-path run alone.
Inject or simulate this matrix:

| Starting condition / event | Required result |
|---|---|
| POR while persisted FULL | Consume the only retry before rail-on; start DIM after the recovery delay. |
| POR while persisted DIM | Rail remains off; enter durable PROTECT. |
| POR or software reset while persisted PROTECT | Remain protected; no sensor or LED startup before verified recovery. |
| NVS read/write failure | Fail rail-off; remain remotely recoverable on timed wakes. |
| I2C/BQ/gauge read failure | Do not interpret missing data as healthy voltage, daylight, or charge recovery. |
| One short positive-current or supply transient | Stay in PROTECT. |
| Sustained qualified charging and recovered VBAT | Clear the stage once and begin a new charge cycle; do not immediately start the show. |
| Missing lux during an active night | Continue the latched night/show state. |
| Explicit dawn evidence | End the show once, without charge-current chatter. |
| Low threshold crossing under known load | Dim/off only after the specified confirmation; critical floor remains immediate. |

### Production exit criteria

The policy is ready to port from `net_bench` when all of the following are true:

- the post-INA P105 A/B is captured and the initiating-cause conclusion is recorded;
- every production power/load class has a room-temperature loaded-sag profile and a
  cold/variance margin;
- the compound PROTECT-release gate passes transient and sustained-charge tests;
- coulomb integration error and persistence behavior are measured and acceptable for
  the selected energy margins;
- the complete reset matrix above produces no unlimited load/reset loop; and
- at least one clean multi-day field run covers charge, dusk, show, dim/off/protect,
  sunrise recovery, intermittent sensing, and OTA maintenance.

The reusable state machine and PowerFeather rail sequencing belong in production
firmware/board abstractions. `net_bench` profile flags, TSL2591 thresholds, P105/P126
loads, and charge-cycle reporting remain test-harness configuration.

## Current operating decision

The original outdoor harvest series ended when Ben disassembled `9E5B0C` on July 13.
Keep its `.1` data as one historical fixture series; replacement `9F2690` starts a new
hardware/run boundary even though the cell, panel, and load profile are reused.

The immediate replacement-board experiment is the manual 40 ms D7/VDC strike in bright
sun without a storage capacitor. Keep fixed 5.8 V VINDPM. After that experiment, any new
field-cycle run should implement the provisional 9-10 h show cap and fix millisecond
carry in the retained integrator. Do not compare the old overlong nighttime soak with a
new capped run as though they were the same daily-energy profile.

## Related records

- `firmware/net_bench/README.md` -- field-cycle firmware behavior and build flags.
- `firmware/POWERFEATHER_NOTES.md` -- reusable PowerFeather rail, POR, I2C, gauge,
  charge-acceptance, and solar-input gotchas.
- `docs/decisions/0023-lfp-power-policy-thresholds.md` -- measured LFP dim/off/sleep
  policy and load compensation.
- `docs/decisions/0028-power-management-bus-integrity.md` -- BQ power-path I2C failure
  class and 100 kHz rule.
- `docs/decisions/0026-solar-panel-selection-and-role-mix.md` -- P105/P126 role choice.
- `docs/tests/BATTERY_32700_SHOOTOUT_PLAN_2026-07.md` -- qualified capacity and gauge
  limitations.
