beneckart/resonance-lighting/docs/tests/figures/boost_ab/fig5_stability.png

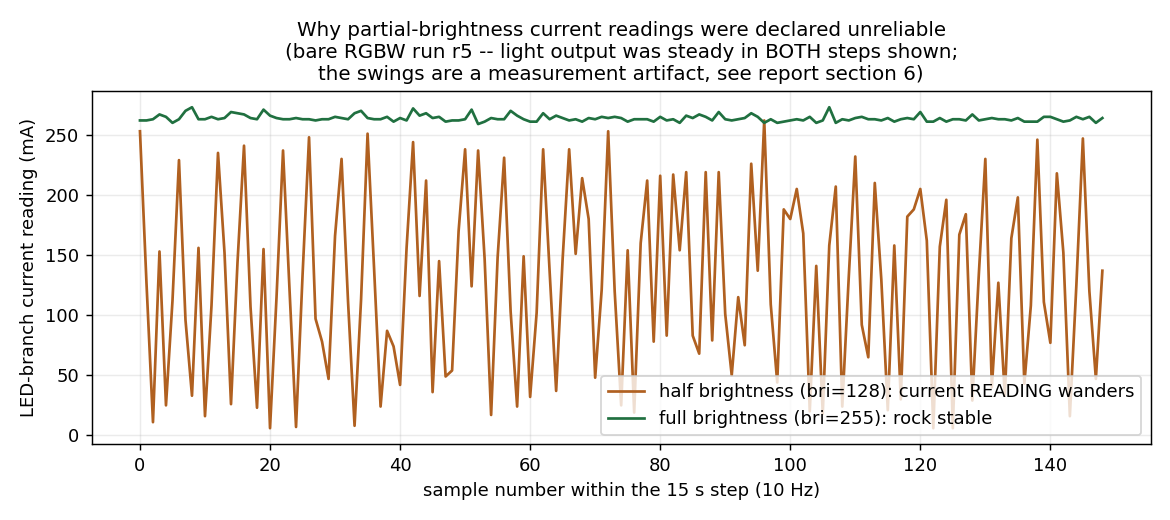
docs/tests/figures/boost_ab/fig5_stability.png
