beneckart/resonance-lighting/firmware/puca_bridge/puca_bridge.ino

// Resonance PUCA performance-audio bridge (ADR 0035) -- PROOF OF CONCEPT.
//
// *** STATUS: PARTIAL BENCH PROOF, NOT FIELD-VALIDATED. ***
// The original codec/MEMS path booted on PUCA hardware on 2026-08-20. The
// current stereo, touch, and fleet-scale deltas remain compile/native-test only.
// Every pin and register value below is sourced from the vendor repo
// (github.com/ohmic-net/puca_dsp) and marked with provenance. Treat the bring-up
// checklist in README.md as mandatory before trusting the bridge in a show.
//
// Target: PUCA DSP **Original Edition** (ESP32-PICO-D4 + WM8978 codec, 8 MB
// PSRAM) on the Ohmic 6 HP Eurorack expansion. This is a classic dual-core
// ESP32 -- NOT an S3; it does not run the CoreS3 bridge binary.
//
// Role (ADR 0035 / hardware/puca-audio-bridge/README.md):
//   audio in (onboard MEMS mics or 3.5 mm line-in from the RODE NTG)
//     -> WM8978 ADC -> I2S RX @ 16 kHz mono
//     -> shared envelope tracker (firmware/cores3_bridge/audio_reactive.h)
//     -> NB_DIRECT_FRAME broadcast at ~10 Hz on fixed ESP-NOW channel 11
//        to fixtures heard via NB_HEARTBEAT.
// Constraints honored:
//   - reuses the canonical wire contract (fixture/src/core/packet.h); no new
//     packet type (ADR 0035 6 forbids one until explicitly specced);
//   - preserves the fixture 3 s stale-frame fallback + 10 s micro-lease: any
//     silence/reboot/cable-pull just stops frames and the fleet goes back to
//     autonomous behavior;
//   - no WiFi AP (the factory image's "PUCA DSP" softAP must not exist here);
//     ordinary comms stays unassociated on channel 11. Exact-target service
//     requests may deliberately leave ESP-NOW and join shared WiFi for OTA;
//   - no raw audio on the air, ever.
//
// ---------------------------------------------------------------------------
// PIN PROVENANCE (all sources fetched 2026-08-19 from
// https://github.com/ohmic-net/puca_dsp @ main)
//
//   [IDF]  puca_dsp-esp-idf/main/main.cpp             (I2S gpio_cfg block)
//   [CVT]  puca-eurorack/hardware_test_arduino/Puca_Eurorack_CV_test/
//          Puca_Eurorack_CV_test.ino                  (knob/CV ADC channels)
//   [TRG]  puca-eurorack/hardware_test_arduino/Puca_Eurorack_trigger_test/
//          Puca_Eurorack_trigger_test.ino             (TOUCH/TRIG/LED pins)
//   [WMH]  .../Puca_Eurorack_CV_test/WM8978.h          (I2C pins + 0x1A addr)
//   [WMC]  .../Puca_Eurorack_CV_test/WM8978.cpp        (register semantics)
//   [FAU]  .../Puca_Eurorack_CV_test/sine_add.h/.cpp   (PICO_DSP=true branch:
//          bck=23 ws=25 dout=26 din=27; MCLK via CLK_OUT1 on GPIO0)
//   [DSH]  documentation/puca_dsp_datasheet_v1.1.pdf   (GPIO header table)
//   [RDM]  README.md (line-in 1 Mohm / 3.3 Vpp max; BT_LVL jumper -> GPIO14)
//
// UNCONFIRMED (could not be pinned from sources; bench-verify before trusting):
//   - which stereo slot (L/R) the mono I2S RX captures, and which physical
//     mic / line channel that is;
//   - whether the CV2/CV3 jacks share the ADC nets with the pots (eurorack
//     schematic PDF not parsed) -- a patched CV cable may fight the knobs;
//   - MICBEN requirement for the Knowles MEMS pair (upstream enables it);
//   - no amp/enable GPIO exists in any upstream source; the 1 W speaker driver
//     hangs off WM8978 LOUT2/ROUT2 which this firmware leaves powered down.
// ---------------------------------------------------------------------------

#include <ESP_I2S.h>
#include <Preferences.h>
#include <Update.h>
#include <WebServer.h>
#include <WiFi.h>
#include <Wire.h>
#include <esp_mac.h>
#include <esp_now.h>
#include <esp_ota_ops.h>
#include <esp_system.h>
#include <esp_task_wdt.h>
#include <esp_wifi.h>
#include <math.h>
#include <string.h>

// Wire contract: included via -I <firmware root> (see build.sh) so the fleet
// packet definitions come from the ONE canonical file -- never forked.
#include "fixture/src/core/packet.h"
// Shared envelope tracker + per-slot color, exactly the cores3 bridge's file
// (relative include, not a copy -- one tracker, one tuning).
#include "../cores3_bridge/audio_reactive.h"
#include "puca_core.h"

#define PUCA_BRIDGE_VERSION "0.5.5-dev"

// Shared maintenance WiFi credentials. This file is gitignored and populated
// by build.sh from an explicit --wifi-source or an existing sibling sketch.
#if __has_include("wifi_secrets.h")
#include "wifi_secrets.h"
#define PUCA_HAS_WIFI_SECRETS 1
#else
#define PUCA_HAS_WIFI_SECRETS 0
#endif

#ifndef NB_CHANNEL
#define NB_CHANNEL 11
#endif

#ifndef NB_MAX_TRACKED
#define NB_MAX_TRACKED 192
#endif

#ifndef NB_WDT_S
#define NB_WDT_S 8
#endif

// ---- pins (see provenance table above) --------------------------------------
static const int PIN_I2C_SDA = 19;   // [WMH] I2C_MASTER_SDA_IO
static const int PIN_I2C_SCL = 18;   // [WMH] I2C_MASTER_SCL_IO
static const int PIN_I2S_MCLK = 0;   // [IDF] .mclk = GPIO_NUM_0 ([FAU] CLK_OUT1)
static const int PIN_I2S_BCLK = 23;  // [IDF] .bclk = GPIO_NUM_23
static const int PIN_I2S_WS = 25;    // [IDF] .ws   = GPIO_NUM_25 (LRCLK)
static const int PIN_I2S_DOUT = 26;  // [IDF] .dout = GPIO_NUM_26 (to DAC; idle here)
static const int PIN_I2S_DIN = 27;   // [IDF] .din  = GPIO_NUM_27 (ADC -> ESP32)
static const int PIN_KNOB1 = 33;     // [CVT] CV2 top pot, ADC1_CH5 -> sensitivity
static const int PIN_KNOB2 = 34;     // [CVT] CV3 bottom pot, ADC1_CH6 -> mode param
static const int PIN_TOUCH = 15;     // [TRG] carrier capacitive paw, digital read
static const int PIN_LED_BOARD = 5;  // [TRG] LED1, PUCA_DSP onboard
static const int PIN_LED_TOP = 2;    // [TRG] LED2, carrier (LOW after boot)
static const int PIN_LED_BTM = 4;    // [TRG] LED3, carrier (LOW after boot)
static const uint32_t BOOT_ARM_WINDOW_MS = 5000;
// Not used but known: BUTTON=36 onboard, TRIG1=13, TRIG2=14 (HIGH after boot)
// [TRG]; BT_LVL jumper routes VBAT to GPIO14 [RDM] -- conflicts with TRIG2.

// ---- shared types (defined before the first function definition so the
// Arduino-injected prototypes that mention them stay valid) --------------------
struct PeerLite {
  bool used;
  uint8_t id[3];
  uint32_t lastHeardMs;
  bool hasFw;
  char fwRev[24];
};

struct RxItem {
  uint8_t len;
  uint8_t data[250];
};
static_assert(sizeof(NbHeartbeat) <= sizeof(RxItem::data),
              "heartbeat outgrew the PUCA bridge receive buffer");

// ---- WM8978 minimal register driver -----------------------------------------
// 7-bit I2C address 0x1A [WMH]. Registers are 7-bit addr + 9-bit value packed
// into two bytes: byte0 = (reg<<1)|val[8], byte1 = val[7:0] [WMC writeReg].
// The chip is write-only over I2C; there is no readback.
static const uint8_t WM8978_ADDR = 0x1A;

static uint32_t wm8978WriteErrors = 0;

static bool wm8978WriteReg(uint8_t reg, uint16_t val) {
  Wire.beginTransmission(WM8978_ADDR);
  Wire.write((uint8_t)((reg << 1) | ((val >> 8) & 0x01)));
  Wire.write((uint8_t)(val & 0xFF));
  bool ok = Wire.endTransmission() == 0;
  if (!ok) ++wm8978WriteErrors;
  return ok;
}

// Input path selection. false = onboard Knowles MEMS pair (differential into
// the input PGAs, routing per [WMC] inputCfg(1,0,0)); true = 3.5 mm stereo
// line-in (L2/R2 straight into the boost mixer at 0 dB, PGAs muted, per [WMC]
// lineinGain(5)). ALC/AGC stays at its power-on default (OFF, R32) on purpose:
// gain staging lives at the RODE dial + KNOB1, not in a codec loop
// (docs/research/AUDIO_INGEST_NTG_PUCA_2026-08-04.md item 2).
static bool wm8978SetInput(bool lineIn) {
  bool ok = true;
  if (lineIn) {
    ok &= wm8978WriteReg(44, 0x000);        // R44: nothing into the PGAs
    ok &= wm8978WriteReg(45, 0x040);        // R45: left PGA muted
    ok &= wm8978WriteReg(46, 0x140);        // R46: right PGA muted (+update)
    ok &= wm8978WriteReg(47, 0x050);        // R47: L2->boost 0 dB, PGABOOST off
    ok &= wm8978WriteReg(48, 0x050);        // R48: R2->boost 0 dB, PGABOOST off
  } else {
    ok &= wm8978WriteReg(44, 0x033);        // R44: LIP/LIN+RIP/RIN -> PGAs [WMC]
    ok &= wm8978WriteReg(45, 30);           // R45: left PGA +10.5 dB ([CVT] micGain(30))
    ok &= wm8978WriteReg(46, 0x100 | 30);   // R46: right PGA +10.5 dB, update
    ok &= wm8978WriteReg(47, 0x100);        // R47: +20 dB PGABOOSTL [WMC init]
    ok &= wm8978WriteReg(48, 0x100);        // R48: +20 dB PGABOOSTR [WMC init]
  }
  return ok;
}

// Minimal RX-only init: power/bias, ADC path, I2S slave, 16 kHz. Derived from
// the upstream init()/addaCfg()/sampleRate()/i2sCfg() sequence [WMC][CVT] with
// the DAC/headphone/speaker output enables stripped (this bridge never plays
// audio). Register fields cross-checked against documentation/WM8978_v4.5
// datasheet.pdf in the same repo.
static bool wm8978Init() {
  bool ok = true;
  ok &= wm8978WriteReg(0, 0x000);  // R0: software reset [WMC init]
  delay(10);
  ok &= wm8978WriteReg(1, 0x01B);  // R1: VMIDSEL=11, BIASEN, MICBEN (upstream
                                   //     0x9B minus OUT4MIXEN -- no outputs)
  ok &= wm8978WriteReg(2, 0x03F);  // R2: BOOSTENL/R, INPPGAENL/R, ADCENL/R
                                   //     (upstream 0x1B0|addaCfg minus LOUT1/ROUT1)
  ok &= wm8978WriteReg(3, 0x000);  // R3: DAC + output mixers all OFF (RX only)
  ok &= wm8978WriteReg(4, 0x010);  // R4: AIF = I2S format, 16-bit ([CVT] i2sCfg(2,0))
  ok &= wm8978WriteReg(6, 0x000);  // R6: codec = clock SLAVE, MCLK undivided;
                                   //     ESP32 masters BCLK/LRCLK/MCLK ([WMC]
                                   //     writeReg(6,0) + [IDF] I2S_ROLE_MASTER)
  ok &= wm8978WriteReg(7, 0x006);  // R7: SMPLR=011 -> 16 kHz filters ([WMC]
                                   //     sampleRate(3))
  ok &= wm8978WriteReg(14, 0x108); // R14: HPFEN (DC block) + ADCOSR128 (upstream
                                   //     sets OSR only; HPF is the chip default
                                   //     we keep instead of clearing)
  return ok;
}

// ---- global state ------------------------------------------------------------
static const uint8_t BCAST[6] = {0xFF, 0xFF, 0xFF, 0xFF, 0xFF, 0xFF};

uint8_t myMac[6] = {};
uint8_t myId[3] = {};
volatile uint32_t sendOk = 0;
volatile uint32_t sendFail = 0;
uint32_t txSeq = 0;
bool radioReady = false;
bool codecReady = false;
bool audioInputReady = false;
// Fail-safe boot: the publisher remains silent unless the paw was held through
// the deliberate boot gesture (or USB service explicitly enables it later).
bool audioActive = false;
bool inputLineIn = true;   // standalone profile: external line input by default
uint32_t audioFrames = 0;
uint32_t audioReadFailures = 0;
uint32_t audioClippedBlocks = 0;
uint32_t audioClippedSamples = 0;
uint16_t audioPeak = 0;

I2SClass i2sIn;
AudioEnvelope audioEnvelope;
AudioCalibrationClock audioCalibration;
PucaPeakFollower heartbeatFollower;

BridgeMode mode = MODE_CLASSIC;

enum PucaNetMode : uint8_t {
  PUCA_MODE_COMMS = 0,
  PUCA_MODE_MAINT = 1,
};
enum PucaMaintStatus : uint8_t {
  PUCA_MAINT_IDLE = 0,
  PUCA_MAINT_ACTIVE = 1,
  PUCA_MAINT_START_FAILED = 3,
  PUCA_MAINT_TIMEOUT = 4,
  PUCA_MAINT_RESUMED = 5,
};

static const uint32_t PUCA_MAINT_TIMEOUT_MS = 10UL * 60UL * 1000UL;
static const uint32_t PUCA_OTA_VERIFY_AT_MS = 20000;
WebServer otaServer(80);
PucaNetMode netMode = PUCA_MODE_COMMS;
uint8_t pucaMaintStatus = PUCA_MAINT_IDLE;
bool otaServerActive = false;
bool otaRoutesConfigured = false;
bool otaResumePending = false;
bool otaUploadActive = false;
bool otaUploadComplete = false;
uint32_t maintEnteredMs = 0;
uint32_t heartbeatSeq = 0;
uint32_t heartbeatSendOk = 0;
uint32_t heartbeatSendFail = 0;
bool otaVerifyChecked = false;
bool otaPendingCache = true;

float knob1Filt = 0.0f;   // smoothed 0..1
float knob2Filt = 0.0f;   // smoothed 0..1
bool knobsPrimed = false;
float knobGain = 1.0f;    // 0.25x..4x sensitivity multiplier from KNOB1
float lastShownLevel = 0.0f;
PucaTouchGesture touchGesture;
PucaCapTouchDetector pawCapDetector;
uint16_t pawCapRaw = 0;
PucaSetupWindow setupWindow;
PucaLedPattern statusLed;
bool bootArmRequested = false;

PeerLite peers[NB_MAX_TRACKED] = {};

QueueHandle_t rxQueue = nullptr;
volatile uint32_t rxQueueDrops = 0;

bool enterMaintenance();
void enterComms();

// uint8_t (not BridgeMode) so the Arduino-generated prototype -- which is
// injected above the enum definition -- stays a valid declaration.
const char *modeName(uint8_t m) {
  switch (m) {
  case MODE_CLASSIC: return "DJ";
  case MODE_HEARTBEAT: return "HEARTBEAT";
  case MODE_EMBER: return "EMBER";
  case MODE_HUE: return "HUE";
  case MODE_OFF: return "OFF";
  default: return "UNKNOWN";
  }
}

// ---- ESP-NOW (ported from cores3_bridge; same discipline) --------------------
void fillHeader(NbHeader *h, uint8_t type) {
  h->ver = NB_PROTO_VER;
  h->type = type;
  memcpy(h->src_id, myId, sizeof(myId));
  h->seq = txSeq++;
  h->uptime_ms = millis();
}

void onEspNowRecv(const esp_now_recv_info_t *info, const uint8_t *data, int len) {
  (void)info;
  if (!rxQueue || len < (int)sizeof(NbHeader) || len > (int)sizeof(RxItem::data))
    return;
  const NbHeader *h = (const NbHeader *)data;
  if (h->ver != NB_PROTO_VER) return;
  bool wanted = h->type == NB_HEARTBEAT ||
                h->type == NB_TARGET_ENTER_MAINT;
  if (!wanted) return;

  RxItem item = {};
  item.len = (uint8_t)len;
  memcpy(item.data, data, len);
  if (xQueueSend(rxQueue, &item, 0) != pdTRUE) ++rxQueueDrops;
}

void onEspNowSend(const esp_now_send_info_t *, esp_now_send_status_t status) {
  if (status == ESP_NOW_SEND_SUCCESS) ++sendOk;
  else ++sendFail;
}

bool setupEspNow() {
  WiFi.mode(WIFI_STA);
  WiFi.setSleep(false);
  // Leave the STA interface powered but unassociated. Passing wifioff=true here
  // stops the radio and makes esp_wifi_set_channel fail on Arduino-ESP32 3.x.
  // This also guarantees the factory "PUCA DSP" softAP behavior does not exist
  // in this firmware (ADR 0035).
  WiFi.disconnect(false, false);
  if (esp_wifi_set_channel(NB_CHANNEL, WIFI_SECOND_CHAN_NONE) != ESP_OK) {
    Serial.println("esp_wifi_set_channel FAILED");
    return false;
  }
  if (esp_now_init() != ESP_OK) {
    Serial.println("esp_now_init FAILED");
    return false;
  }
  esp_now_register_recv_cb(onEspNowRecv);
  esp_now_register_send_cb(onEspNowSend);

  esp_now_peer_info_t peer = {};
  memcpy(peer.peer_addr, BCAST, sizeof(BCAST));
  peer.channel = NB_CHANNEL;
  peer.ifidx = WIFI_IF_STA;
  peer.encrypt = false;
  esp_err_t result = esp_now_add_peer(&peer);
  if (result != ESP_OK && result != ESP_ERR_ESPNOW_EXIST) {
    Serial.printf("esp_now_add_peer FAILED: %d\n", (int)result);
    return false;
  }
  Serial.printf("esp-now up, ch=%d, broadcast peer registered\n", NB_CHANNEL);
  return true;
}

void stopEspNow() {
  if (radioReady) esp_now_deinit();
  radioReady = false;
}

// ---- heartbeat listener (minimal port of the cores3 peer tracker) ------------
PeerLite *findPeer(const uint8_t id[3], bool create) {
  for (size_t i = 0; i < NB_MAX_TRACKED; ++i) {
    if (peers[i].used && memcmp(peers[i].id, id, 3) == 0) return &peers[i];
  }
  if (!create) return nullptr;
  for (size_t i = 0; i < NB_MAX_TRACKED; ++i) {
    if (!peers[i].used) {
      memset(&peers[i], 0, sizeof(peers[i]));
      peers[i].used = true;
      memcpy(peers[i].id, id, 3);
      return &peers[i];
    }
  }
  return nullptr;
}

void processHeartbeat(const RxItem &item) {
  const NbHeartbeat *hb = (const NbHeartbeat *)item.data;
  PeerLite *peer = findPeer(hb->h.src_id, true);
  if (!peer) return;
  peer->lastHeardMs = millis();
  if (NB_HAS_HB_FIELD(item.len, fw_rev)) {
    peer->hasFw = true;
    memcpy(peer->fwRev, hb->fw_rev, sizeof(peer->fwRev));
    peer->fwRev[sizeof(peer->fwRev) - 1] = '\0';
  }
}

void processRx() {
  if (!rxQueue) return;
  RxItem item;
  while (xQueueReceive(rxQueue, &item, 0) == pdTRUE) {
    const NbHeader *h = (const NbHeader *)item.data;
    if (memcmp(h->src_id, myId, sizeof(myId)) == 0) continue;
    if (h->type == NB_HEARTBEAT &&
        item.len >= (int)offsetof(NbHeartbeat, supply_mv)) {
      processHeartbeat(item);
      continue;
    }
    if (h->type == NB_TARGET_ENTER_MAINT &&
        item.len >= (int)sizeof(NbTargetCmd)) {
      const NbTargetCmd *cmd = (const NbTargetCmd *)item.data;
      if (pucaMaintenanceTargetMatches(cmd->target_id, myId) &&
          netMode == PUCA_MODE_COMMS) {
        Serial.printf("exact-target maintenance request from %02X%02X%02X\n",
                      h->src_id[0], h->src_id[1], h->src_id[2]);
        enterMaintenance();
      }
    }
  }
}

int livePeerCount() {
  int count = 0;
  uint32_t now = millis();
  for (size_t i = 0; i < NB_MAX_TRACKED; ++i) {
    if (peers[i].used && now - peers[i].lastHeardMs <= 5000) ++count;
  }
  return count;
}

// Identical filter to cores3 collectLiveAudioIds: fixtures heard in the last
// 5 s, minus peers whose full heartbeat identifies non-fixture firmware, sorted
// by id so slot colors are stable regardless of heartbeat arrival order.
size_t collectLiveFixtureIds(uint8_t ids[NB_MAX_TRACKED][3]) {
  size_t count = 0;
  uint32_t now = millis();
  for (size_t i = 0; i < NB_MAX_TRACKED && count < NB_MAX_TRACKED; ++i) {
    if (!peers[i].used || now - peers[i].lastHeardMs > 5000) continue;
    if (!pucaAudioPeerEligible(peers[i].hasFw, peers[i].fwRev)) continue;
    memcpy(ids[count++], peers[i].id, 3);
  }
  for (size_t i = 1; i < count; ++i) {
    uint8_t key[3];
    memcpy(key, ids[i], 3);
    int j = (int)i - 1;
    while (j >= 0 && memcmp(ids[j], key, 3) > 0) {
      memcpy(ids[j + 1], ids[j], 3);
      --j;
    }
    memcpy(ids[j + 1], key, 3);
  }
  return count;
}

int liveFixtureCount() {
  uint8_t ids[NB_MAX_TRACKED][3];
  return (int)collectLiveFixtureIds(ids);
}

// ---- PUCA identity heartbeat + shared-WiFi maintenance OTA ------------------
// PUCA emits a tail-7 heartbeat so Bridge OS can census it, display the exact
// puca-bridge revision, and send NB_TARGET_ENTER_MAINT to A4EB10. It is not a
// fixture: the non-fixture firmware prefix keeps audio publishers out of the
// light-target census.
void sendPucaHeartbeat() {
  if (!radioReady || netMode != PUCA_MODE_COMMS) return;
  NbHeartbeat hb = {};
  hb.h.ver = NB_PROTO_VER;
  hb.h.type = NB_HEARTBEAT;
  memcpy(hb.h.src_id, myId, sizeof(myId));
  hb.h.seq = heartbeatSeq++;
  hb.h.uptime_ms = millis();
  hb.soc_pct = 255;             // no battery telemetry on the installed PUCA
  hb.reset_reason = (uint8_t)esp_reset_reason();
  hb.ca_state = audioActive ? 1 : 0;
  hb.mode = (uint8_t)mode;
  hb.dl_pdr_x1000 = 0xFFFF;
  hb.dl_rssi = -127;
  hb.lux_x10 = UINT32_MAX;
  hb.ptemp_cx10 = INT16_MIN;
  hb.prh_pct = 255;
  hb.btemp_cx10 = INT16_MIN;
  hb.ina_pv_mv = INT16_MIN;
  hb.ina_pa_ma = INT16_MIN;
  hb.ina_bv_mv = INT16_MIN;
  hb.ina_ba_ma = INT16_MIN;
  snprintf(hb.fw_rev, sizeof(hb.fw_rev), "puca-bridge-%s",
           PUCA_BRIDGE_VERSION);
  hb.maint_status = pucaMaintStatus;
  size_t wireLen = offsetof(NbHeartbeat, maint_status) +
                   sizeof(hb.maint_status);
  if (esp_now_send(BCAST, (const uint8_t *)&hb, wireLen) == ESP_OK)
    ++heartbeatSendOk;
  else
    ++heartbeatSendFail;
}

void heartbeatTick(uint32_t now) {
  static uint32_t nextHeartbeatMs = 0;
  if ((int32_t)(now - nextHeartbeatMs) < 0) return;
  nextHeartbeatMs = now + 1000;
  sendPucaHeartbeat();
}

const char *otaStateName(esp_ota_img_states_t state) {
  switch (state) {
  case ESP_OTA_IMG_NEW: return "new";
  case ESP_OTA_IMG_PENDING_VERIFY: return "pending_verify";
  case ESP_OTA_IMG_VALID: return "valid";
  case ESP_OTA_IMG_INVALID: return "invalid";
  case ESP_OTA_IMG_ABORTED: return "aborted";
  default: return "undefined";
  }
}

String pucaTelemetryJson() {
  const esp_partition_t *running = esp_ota_get_running_partition();
  esp_ota_img_states_t state = ESP_OTA_IMG_UNDEFINED;
  if (running) esp_ota_get_state_partition(running, &state);
  char shortId[7];
  snprintf(shortId, sizeof(shortId), "%02X%02X%02X",
           myId[0], myId[1], myId[2]);
  String json = "{\"board\":\"puca_dsp_original\",\"fw\":\"puca-bridge-";
  json += PUCA_BRIDGE_VERSION;
  json += "\",\"firmware_rev\":\"puca-bridge-";
  json += PUCA_BRIDGE_VERSION;
  json += "\",\"fixture_id\":\"";
  json += shortId; // compatibility key used by the existing discovery tools
  json += "\",\"node_id\":\"";
  json += shortId;
  json += "\",\"role\":\"puca_audio_bridge\",\"mode\":";
  json += String((unsigned)netMode);
  json += ",\"audio_mode\":\"";
  json += modeName(mode);
  json += "\",\"publisher_armed\":";
  json += audioActive ? "true" : "false";
  json += ",\"boot_armed\":";
  json += bootArmRequested ? "true" : "false";
  json += ",\"uptime_ms\":";
  json += String((unsigned long)millis());
  json += ",\"reset_reason\":";
  json += String((unsigned)esp_reset_reason());
  json += ",\"maint_status\":";
  json += String((unsigned)pucaMaintStatus);
  json += ",\"maintenance_ready\":";
  json += (netMode == PUCA_MODE_MAINT && otaServerActive &&
           WiFi.status() == WL_CONNECTED) ? "true" : "false";
  json += ",\"wifi_ip\":\"";
  json += WiFi.localIP().toString();
  json += "\",\"wifi_rssi\":";
  json += String(WiFi.status() == WL_CONNECTED ? WiFi.RSSI() : 0);
  json += ",\"codec\":";
  json += codecReady ? "true" : "false";
  json += ",\"i2s\":";
  json += audioInputReady ? "true" : "false";
  json += ",\"ota_state\":\"";
  json += otaStateName(state);
  json += "\",\"ota_pending_verify\":";
  json += state == ESP_OTA_IMG_PENDING_VERIFY ? "true" : "false";
  json += ",\"heap_free\":";
  json += String((unsigned long)ESP.getFreeHeap());
  json += "}\n";
  return json;
}

bool maintenanceReady() {
  return netMode == PUCA_MODE_MAINT &&
         pucaMaintStatus == PUCA_MAINT_ACTIVE && otaServerActive &&
         WiFi.status() == WL_CONNECTED;
}

void configureOtaRoutes() {
  if (otaRoutesConfigured) return;
  otaServer.on("/", HTTP_GET, []() {
    otaServer.send(200, "text/plain",
                   "Resonance PUCA maintenance OTA; exact target only.\n");
  });
  otaServer.on("/telemetry", HTTP_GET, []() {
    otaServer.send(200, "application/json", pucaTelemetryJson());
  });
  otaServer.on("/resume", HTTP_GET, []() {
    otaServer.send(200, "text/plain", "resuming dark comms\n");
    otaResumePending = true;
  });
  otaServer.on(
      "/update", HTTP_POST,
      []() {
        esp_task_wdt_reset();
        bool ok = otaUploadComplete && !Update.hasError();
        otaServer.send(ok ? 200 : 500, "text/plain",
                       ok ? "Update complete. Rebooting.\n"
                          : "Update failed.\n");
        if (ok) {
          delay(500);
          ESP.restart();
        }
      },
      []() {
        esp_task_wdt_reset();
        HTTPUpload &upload = otaServer.upload();
        if (upload.status == UPLOAD_FILE_START) {
          otaUploadActive = true;
          otaUploadComplete = false;
          Serial.printf("OTA start: %s\n", upload.filename.c_str());
          if (!Update.begin(UPDATE_SIZE_UNKNOWN)) Update.printError(Serial);
        } else if (upload.status == UPLOAD_FILE_WRITE) {
          if (Update.write(upload.buf, upload.currentSize) != upload.currentSize)
            Update.printError(Serial);
        } else if (upload.status == UPLOAD_FILE_END) {
          otaUploadComplete = Update.end(true);
          otaUploadActive = false;
          if (otaUploadComplete)
            Serial.printf("OTA done: %u bytes\n", upload.totalSize);
          else
            Update.printError(Serial);
        } else if (upload.status == UPLOAD_FILE_ABORTED) {
          Update.abort();
          otaUploadActive = false;
          otaUploadComplete = false;
          Serial.println("OTA aborted");
        }
      });
  otaRoutesConfigured = true;
}

bool startWifiOta() {
#if PUCA_HAS_WIFI_SECRETS
  WiFi.mode(WIFI_STA);
  WiFi.setSleep(false);
  WiFi.begin(RES_WIFI_SSID, RES_WIFI_PASSWORD);
  uint32_t startedMs = millis();
  while (WiFi.status() != WL_CONNECTED && millis() - startedMs < 20000) {
    esp_task_wdt_reset();
    delay(250);
    Serial.print('.');
  }
  Serial.println();
  if (WiFi.status() != WL_CONNECTED) {
    Serial.println("WiFi join failed");
    return false;
  }
  configureOtaRoutes();
  otaServer.begin();
  otaServerActive = true;
  Serial.print("maintenance WiFi up, ip=");
  Serial.print(WiFi.localIP());
  Serial.printf(" ch=%d id=%02X%02X%02X role=puca_audio_bridge\n",
                WiFi.channel(), myId[0], myId[1], myId[2]);
  return true;
#else
  Serial.println("no wifi_secrets.h -> cannot OTA");
  return false;
#endif
}

void stopOtaAndWifi() {
  if (otaServerActive) otaServer.stop();
  WiFi.softAPdisconnect(true); // defensive: this firmware never starts an AP
  WiFi.disconnect(true);
  WiFi.mode(WIFI_OFF);
  otaServerActive = false;
  otaUploadActive = false;
  otaUploadComplete = false;
}

bool enterMaintenance() {
  if (netMode == PUCA_MODE_MAINT) return true;
#if !PUCA_HAS_WIFI_SECRETS
  pucaMaintStatus = PUCA_MAINT_START_FAILED;
  Serial.println("maintenance refused: build has no shared-WiFi credentials");
  return false;
#endif
  // Do not transmit a black frame: simply release ownership and let the
  // receiver's stale-frame lease return every fixture to autonomous behavior.
  audioActive = false;
  digitalWrite(PIN_LED_TOP, LOW);
  Serial.println("publisher=SAFE-IDLE -> MAINTENANCE (shared-WiFi OTA)");
  stopEspNow();
  if (rxQueue) xQueueReset(rxQueue);
  netMode = PUCA_MODE_MAINT;
  maintEnteredMs = millis();
  if (!startWifiOta()) {
    pucaMaintStatus = PUCA_MAINT_START_FAILED;
    Serial.println("maintenance startup failed -> dark comms");
    enterComms();
    return false;
  }
  pucaMaintStatus = PUCA_MAINT_ACTIVE;
  return true;
}

void enterComms() {
  if (otaServerActive || WiFi.status() == WL_CONNECTED) stopOtaAndWifi();
  netMode = PUCA_MODE_COMMS;
  if (rxQueue) xQueueReset(rxQueue);
  radioReady = setupEspNow();
  digitalWrite(PIN_LED_BOARD, radioReady ? HIGH : LOW);
  digitalWrite(PIN_LED_TOP, LOW); // maintenance/resume never rearms publishing
  Serial.printf("-> COMMS dark, esp-now=%s\n", radioReady ? "ready" : "FAILED");
}

void maintenanceTick() {
  if (netMode != PUCA_MODE_MAINT) return;
  otaServer.handleClient();
  if (otaResumePending) {
    otaResumePending = false;
    pucaMaintStatus = PUCA_MAINT_RESUMED;
    Serial.println("/resume -> dark comms");
    enterComms();
    return;
  }
  if (!otaUploadActive && millis() - maintEnteredMs > PUCA_MAINT_TIMEOUT_MS) {
    pucaMaintStatus = PUCA_MAINT_TIMEOUT;
    Serial.println("maintenance timeout -> dark comms");
    enterComms();
  }
}

extern "C" bool verifyRollbackLater() { return true; }
extern "C" bool verifyOta() { return true; }

bool otaVerifyPending() {
  if (otaVerifyChecked || !otaPendingCache) return false;
  const esp_partition_t *running = esp_ota_get_running_partition();
  esp_ota_img_states_t state = ESP_OTA_IMG_UNDEFINED;
  if (!running || esp_ota_get_state_partition(running, &state) != ESP_OK) {
    otaPendingCache = false;
    return false;
  }
  otaPendingCache = state == ESP_OTA_IMG_PENDING_VERIFY;
  return otaPendingCache;
}

bool otaSelfTest() {
#ifdef PUCA_OTA_FAIL_SELFTEST
  Serial.println("ota-verify: PUCA_OTA_FAIL_SELFTEST forcing failure");
  return false;
#endif
  bool networkOk = netMode == PUCA_MODE_MAINT
                       ? maintenanceReady()
                       : radioReady && heartbeatSendOk > 0;
  if (!codecReady || !audioInputReady || !networkOk) return false;
  Preferences prefs;
  if (!prefs.begin("respuca", false)) return false;
  uint32_t probe = millis() | 1U;
  bool nvsOk = prefs.putUInt("otaprobe", probe) == sizeof(uint32_t) &&
               prefs.getUInt("otaprobe", 0) == probe;
  prefs.end();
  return nvsOk;
}

void otaVerifyTick() {
  if (otaVerifyChecked || millis() < PUCA_OTA_VERIFY_AT_MS) return;
  if (!otaVerifyPending()) {
    otaVerifyChecked = true;
    return;
  }
  otaVerifyChecked = true;
  otaPendingCache = false;
  if (otaSelfTest()) {
    esp_ota_mark_app_valid_cancel_rollback();
    Serial.println("ota-verify: VALID (codec + I2S + network + NVS)");
  } else {
    Serial.println("ota-verify: SELF-TEST FAILED -> rollback");
    Serial.flush();
    delay(100);
    esp_ota_mark_app_invalid_rollback_and_reboot();
  }
}

// ---- bridge-side color math (ported from cores3_bridge.ino) ------------------
// The wire contract (packet.h) stays untouched; this is sender-side math only.
void hsvToRgb(float hue, float sat, float val, uint8_t *r, uint8_t *g, uint8_t *b) {
  hue -= floorf(hue);
  float hf = hue * 6.0f;
  int sector = ((int)hf) % 6;
  float f = hf - (float)sector;
  float p = val * (1.0f - sat);
  float q = val * (1.0f - sat * f);
  float t = val * (1.0f - sat * (1.0f - f));
  float rf, gf, bf;
  switch (sector) {
  case 0: rf = val; gf = t; bf = p; break;
  case 1: rf = q; gf = val; bf = p; break;
  case 2: rf = p; gf = val; bf = t; break;
  case 3: rf = p; gf = q; bf = val; break;
  case 4: rf = t; gf = p; bf = val; break;
  default: rf = val; gf = p; bf = q; break;
  }
  *r = (uint8_t)(rf * 255.0f + 0.5f);
  *g = (uint8_t)(gf * 255.0f + 0.5f);
  *b = (uint8_t)(bf * 255.0f + 0.5f);
}

AudioColor colorForMode(uint8_t slot, float shown) {
  if (shown < 0.0f) shown = 0.0f;
  if (shown > 1.0f) shown = 1.0f;
  switch (mode) {
  case MODE_CLASSIC:
    // KNOB2 is the brightness ceiling; scale the level before the per-slot
    // color so the R/G/B ratios stay put.
    return audioColorForSlot(slot, shown * knob2Filt);
  case MODE_HEARTBEAT: {
    PucaRgbw heart = pucaHeartbeatColor(shown, knob2Filt);
    return {heart.r, heart.g, heart.b, heart.w};
  }
  case MODE_EMBER: {
    // Same warm-white ratios as cores3 AUDIO_MODE_EMBER; KNOB2 = ceiling.
    float v = shown * knob2Filt;
    return {(uint8_t)(v * 255.0f + 0.5f),
            (uint8_t)(v * 0.55f * 255.0f + 0.5f),
            (uint8_t)(v * 0.10f * 255.0f + 0.5f),
            (uint8_t)(v * 0.60f * 255.0f + 0.5f)};
  }
  case MODE_HUE: {
    // KNOB2 sets the hue; the envelope owns the value. No ceiling here --
    // the knob is spoken for.
    uint8_t r, g, b;
    hsvToRgb(knob2Filt, 1.0f, shown, &r, &g, &b);
    return {r, g, b, 0};
  }
  default:
    return {0, 0, 0, 0}; // MODE_OFF only sends the one blackout frame
  }
}

void sendDirectFrame(float shown) {
  if (!radioReady) return;
  uint8_t ids[NB_MAX_TRACKED][3];
  size_t total = collectLiveFixtureIds(ids);
  if (!total) return;

  // One direct frame holds 18 fixtures. Send the complete sorted census in
  // chunks, preserving global slot colors across chunk boundaries.
  for (size_t offset = 0; offset < total; offset += NB_DIRECT_MAX_ENTRIES) {
    NbDirectFrame frame = {};
    fillHeader(&frame.h, NB_DIRECT_FRAME);
    frame.flags = 0x03; // 10 s micro-lease + hard-cut; envelope owns smoothing
    size_t chunk = pucaChunkSize(total, offset, NB_DIRECT_MAX_ENTRIES);
    frame.count = (uint8_t)chunk;
    for (size_t i = 0; i < chunk; ++i) {
      size_t slot = offset + i;
      memcpy(frame.entries[i].id, ids[slot], 3);
      AudioColor color = colorForMode((uint8_t)slot, shown);
      frame.entries[i].r = color.r;
      frame.entries[i].g = color.g;
      frame.entries[i].b = color.b;
      frame.entries[i].w = color.w;
    }
    size_t wireLen = offsetof(NbDirectFrame, entries) +
                     chunk * sizeof(NbDirectEntry);
    if (esp_now_send(BCAST, (const uint8_t *)&frame, wireLen) == ESP_OK)
      ++audioFrames;
    else
      ++sendFail;
  }
}

// ---- controls -----------------------------------------------------------------
uint8_t nextLiveMode(uint8_t current) {
  return (uint8_t)pucaNextLiveMode((BridgeMode)current);
}

uint8_t modeStatusCode(uint8_t current) {
  return pucaModeStatusCode((BridgeMode)current);
}

void showStatus(uint32_t now) {
  statusLed.startStatus(now, inputLineIn, modeStatusCode(mode));
}

void setMode(uint8_t next) {
  mode = (BridgeMode)next;
  if (mode == MODE_HEARTBEAT) heartbeatFollower.reset();
  if (mode == MODE_OFF) sendDirectFrame(0.0f); // black now; staleness + lease
                                               // expiry return autonomy
  digitalWrite(PIN_LED_TOP, (mode != MODE_OFF && audioActive) ? HIGH : LOW);
  Serial.printf("mode=%s\n", modeName(mode));
}

void nextMode() {
  // The live cycle deliberately excludes OFF. Runtime silence/stop remains a
  // deliberate serial command or a power-down, never "one more paw tap".
  setMode(nextLiveMode(mode));
}

void setAudioActive(bool active) {
  if (active == audioActive) return;
  if (active && netMode != PUCA_MODE_COMMS) {
    Serial.println("audio ON refused: maintenance owns the radio");
    return;
  }
  if (active && (!codecReady || !audioInputReady)) {
    Serial.println("audio ON refused: codec/I2S not ready");
    return;
  }
  if (!active) sendDirectFrame(0.0f);
  audioActive = active;
  if (active) {
    audioEnvelope = AudioEnvelope{}; // re-run room-audio noise calibration
    audioCalibration.reset();
    heartbeatFollower.reset();
  }
  digitalWrite(PIN_LED_TOP, (mode != MODE_OFF && audioActive) ? HIGH : LOW);
  Serial.printf("audio -> %s\n", active ? "ON" : "OFF");
}

void setInputLineIn(bool lineIn) {
  inputLineIn = lineIn;
  bool ok = wm8978SetInput(lineIn);
  if (!ok) {
    codecReady = false;
    setAudioActive(false);
  }
  audioEnvelope = AudioEnvelope{}; // different noise floor -> recalibrate
  audioCalibration.reset();
  heartbeatFollower.reset();
  Serial.printf("input -> %s (%s)\n", lineIn ? "line" : "mic",
                ok ? "codec ack" : "I2C WRITE FAILED");
}

void selectHeartbeatMode() {
  if (!inputLineIn) setInputLineIn(true);
  if (!codecReady) {
    Serial.println("HEARTBEAT refused: line input unavailable");
    return;
  }
  setMode(MODE_HEARTBEAT);
  Serial.println("mode=HEARTBEAT input=line");
}

// KNOB1: sensitivity multiplier, log-mapped 0.25x (CCW) .. 4x (CW), 1x center.
// KNOB2: DJ/HEARTBEAT/EMBER brightness ceiling 0..1; HUE hue 0..1 turn.
// Both ADC1 channels, so readings survive WiFi being up. 10 Hz + light EMA.
void knobsTick() {
  float k1 = (float)analogRead(PIN_KNOB1) / 4095.0f;
  float k2 = pucaCarrierPotFromAdc(
      (float)analogRead(PIN_KNOB2) / 4095.0f);
  if (!knobsPrimed) {
    knob1Filt = k1;
    knob2Filt = k2;
    knobsPrimed = true;
  } else {
    knob1Filt += (k1 - knob1Filt) * 0.3f;
    knob2Filt += (k2 - knob2Filt) * 0.3f;
  }
  knobGain = pucaSensitivityGainFromAdc(knob1Filt);
}

bool pawTouched() {
  pawCapRaw = (uint16_t)touchRead(PIN_TOUCH);
  return pawCapDetector.update(pawCapRaw);
}

// Paw: the exact received unit exposes the electrode directly to ESP32 touch
// channel T3/GPIO15. A continuous capacitance-qualified boot hold is the
// physical arming interlock: without it PUCA joins the mesh only to report
// identity/accept maintenance and never emits a lighting frame. The same hold
// opens a 20 s setup window; short touches cycle DJ/HEARTBEAT/EMBER/HUE and a
// long hold locks immediately. OFF is never in the paw cycle.
void touchTick(uint32_t now) {
  bool raw = pawTouched();
  if (setupWindow.update(now)) {
    Serial.println("controls=LOCKED (setup timeout)");
    showStatus(now);
  }

  PucaTouchEvent event = touchGesture.update(now, raw);
  if (event == PUCA_TOUCH_NONE) return;

  if (!setupWindow.unlocked) {
    Serial.println("paw=status only (controls LOCKED)");
    showStatus(now);
    return;
  }

  if (event == PUCA_TOUCH_LONG) {
    setupWindow.lock();
    Serial.println("controls=LOCKED (confirmed)");
    showStatus(now);
    return;
  }

  nextMode();
  setupWindow.activity(now);
  Serial.println("controls=SETUP (short touch cycles; long hold locks)");
  showStatus(now);
}

void statusLedTick(uint32_t now) {
  bool on = statusLed.level(now, setupWindow.unlocked);
  digitalWrite(PIN_LED_BTM, on ? HIGH : LOW);
}

bool detectBootSetupHold() {
  PucaBootHoldDetector detector;
  uint32_t startedMs = millis();
  digitalWrite(PIN_LED_BTM, HIGH); // steady red cue while boot arming is available
  while (millis() - startedMs < BOOT_ARM_WINDOW_MS) {
    if (detector.update(millis(), pawTouched())) {
      digitalWrite(PIN_LED_BTM, LOW);
      return true;
    }
    delay(10);
  }
  digitalWrite(PIN_LED_BTM, LOW);
  return false;
}

// ---- audio: 100 ms blocking reads pace the ~10 Hz send loop -------------------
void audioTick() {
  if (!audioInputReady) return;

  // 3200 interleaved L/R samples = exactly 100 ms of 16 kHz stereo. The block
  // is analyzed for clipping, then averaged to mono for the shared envelope.
  // A single plugged jack reads about half level because the other channel is
  // silent; KNOB1's 0.25x-4x range absorbs that expected loss.
  static int16_t samples[3200];
  size_t got = i2sIn.readBytes((char *)samples, sizeof(samples));
  if (got < sizeof(samples)) {
    ++audioReadFailures;
    if (got < 2 * sizeof(int16_t)) {
      delay(5);
      return;
    }
  }

  knobsTick();
  if (!audioActive) return;

  size_t sampleCount = got / sizeof(int16_t);
  PucaPcmStats pcm = pucaPcmStats(samples, sampleCount);
  audioPeak = pcm.peak;
  audioClippedSamples += pcm.clipped;
  if (pcm.clipped) ++audioClippedBlocks;
  size_t stereoPairs = pucaStereoToMono(samples, sampleCount);

  uint32_t capturedMs = millis();
  audioCalibration.noteCapture(capturedMs);
  bool calibrating = audioCalibration.calibratingCurrentCapture();
  float level = audioEnvelope.update(
      samples, stereoPairs, calibrating, audioCalibration.observationCount16());
  float shown = mode == MODE_HEARTBEAT
                    ? heartbeatFollower.update(audioPeak, knobGain)
                    : level * knobGain;
  if (shown > 1.0f) shown = 1.0f;
  lastShownLevel = shown;

  bool inputReady = mode == MODE_HEARTBEAT || audioCalibration.calibrated();
  if (mode == MODE_OFF || !inputReady) return;

  // The blocking read is the metronome; this floor only stops a burst if the
  // DMA had a backlog and reads briefly return instantly.
  static uint32_t lastSendMs = 0;
  uint32_t now = millis();
  if (now - lastSendMs < 80) return;
  lastSendMs = now;
  sendDirectFrame(shown);
}

// ---- serial CLI + status -------------------------------------------------------
void printStatusJson() {
  bool touched = pawTouched();
  Serial.printf("{\"mode\":\"%s\",\"level\":%.3f,\"wave\":%.3f,\"rms\":%.0f,\"peak\":%u,"
                "\"clipblocks\":%lu,\"gain\":%.2f,\"hue\":%d,"
                "\"peers\":%d,\"fixtures\":%d,\"sendok\":%lu,\"active\":%d,\"input\":\"%s\","
                "\"ceil\":%.2f,\"sendfail\":%lu,\"codec\":%d,\"calibrated\":%d,"
                "\"cal_ms\":%lu,\"cal_obs\":%lu,\"paw_cap\":%u,\"paw\":%d,"
                "\"controls\":\"%s\",\"net\":\"%s\",\"maint_status\":%u,"
                "\"boot_armed\":%d}\n",
                modeName(mode), lastShownLevel, heartbeatFollower.level,
                audioEnvelope.rms, audioPeak,
                (unsigned long)audioClippedBlocks, knobGain,
                (int)(knob2Filt * 360.0f), livePeerCount(), liveFixtureCount(),
                (unsigned long)sendOk, audioActive ? 1 : 0,
                 inputLineIn ? "line" : "mic", knob2Filt,
                 (unsigned long)sendFail, codecReady ? 1 : 0,
                 audioCalibration.calibrated() ? 1 : 0,
                 (unsigned long)audioCalibration.elapsedMs(),
                 (unsigned long)audioCalibration.observations,
                 (unsigned)pawCapRaw, touched ? 1 : 0,
                 setupWindow.unlocked ? "SETUP" : "LOCKED",
                netMode == PUCA_MODE_MAINT ? "MAINT" : "COMMS",
                (unsigned)pucaMaintStatus, bootArmRequested ? 1 : 0);
}

// USB-only bench probe for the paw electrode itself. ESP32 touch-channel values
// fall when capacitance increases. Normal paw gestures are suspended for this
// bounded inactive-only measurement, while radio receive and heartbeats remain
// serviced so the diagnostic does not create queue drops or a mesh outage.
void runPawCapProbe() {
  if (audioActive || netMode != PUCA_MODE_COMMS) {
    Serial.println("pawprobe refused: requires inactive COMMS state");
    return;
  }

  static const uint32_t DURATION_MS = 4000;
  static const uint32_t REPORT_MS = 100;
  Serial.println("pawprobe start duration_ms=4000 esp32_touch=lower-is-more-capacitance");

  (void)touchRead(PIN_TOUCH); // discard first measurement
  uint32_t start = millis();
  uint32_t nextReport = start;
  uint32_t minimum = UINT32_MAX;
  uint32_t maximum = 0;
  uint64_t total = 0;
  uint32_t samples = 0;
  while (millis() - start < DURATION_MS) {
    uint32_t value = (uint32_t)touchRead(PIN_TOUCH);
    pawCapRaw = (uint16_t)value;
    if (value < minimum) minimum = value;
    if (value > maximum) maximum = value;
    total += value;
    ++samples;
    uint32_t now = millis();
    if ((int32_t)(now - nextReport) >= 0) {
      Serial.printf("pawprobe ms=%lu cap=%lu\n",
                    (unsigned long)(now - start), (unsigned long)value);
      nextReport += REPORT_MS;
    }
    processRx();
    heartbeatTick(now);
    esp_task_wdt_reset();
    delay(10);
  }

  touchGesture = PucaTouchGesture();
  pawCapDetector = PucaCapTouchDetector();
  uint32_t average = samples ? (uint32_t)(total / samples) : 0;
  Serial.printf("pawprobe done samples=%lu min=%lu avg=%lu max=%lu restored=cap-touch\n",
                (unsigned long)samples, (unsigned long)minimum,
                (unsigned long)average, (unsigned long)maximum);
}

void handleSerial() {
  while (Serial.available() > 0) {
    int c = Serial.read();
    switch (c) {
    case 't': printStatusJson(); break;
    case 'M': nextMode(); showStatus(millis()); break;
    case 'A': setAudioActive(!audioActive); break;
    case 'I': setInputLineIn(!inputLineIn); showStatus(millis()); break;
    case 'H': selectHeartbeatMode(); showStatus(millis()); break;
    case 'P': runPawCapProbe(); break;
    case '\r': case '\n': case ' ': break;
    default:
      Serial.println("keys: t=status-json M=next-live-mode A=audio-toggle I=mic/line H=heartbeat-line P=paw-cap-probe");
      break;
    }
  }
}

void statusTick(uint32_t now) {
  static uint32_t nextStatusMs = 0;
  if ((int32_t)(now - nextStatusMs) < 0) return;
  nextStatusMs = now + 1000;
  bool touched = pawTouched();
  Serial.printf("puca mode=%s active=%d bootarmed=%d net=%s maint=%u input=%s calibrated=%d calms=%lu calobs=%lu pawcap=%u paw=%d level=%.3f wave=%.3f "
                "gain=%.2f ceil=%.2f hue=%d peers=%d fixtures=%d sendok=%lu sendfail=%lu "
                "rms=%.0f peak=%u clipblk=%lu clips=%lu frames=%lu readfail=%lu "
                "rxdrop=%lu i2cerr=%lu codec=%d controls=%s up=%lu "
                "fw=puca-bridge-" PUCA_BRIDGE_VERSION "\n",
                modeName(mode), audioActive ? 1 : 0,
                bootArmRequested ? 1 : 0,
                netMode == PUCA_MODE_MAINT ? "MAINT" : "COMMS",
                (unsigned)pucaMaintStatus,
                inputLineIn ? "line" : "mic",
                 audioCalibration.calibrated() ? 1 : 0,
                 (unsigned long)audioCalibration.elapsedMs(),
                 (unsigned long)audioCalibration.observations,
                 (unsigned)pawCapRaw, touched ? 1 : 0, lastShownLevel,
                heartbeatFollower.level, knobGain,
                knob2Filt, (int)(knob2Filt * 360.0f), livePeerCount(),
                liveFixtureCount(),
                (unsigned long)sendOk, (unsigned long)sendFail,
                audioEnvelope.rms, audioPeak,
                (unsigned long)audioClippedBlocks,
                (unsigned long)audioClippedSamples,
                (unsigned long)audioFrames, (unsigned long)audioReadFailures,
                (unsigned long)rxQueueDrops, (unsigned long)wm8978WriteErrors,
                codecReady ? 1 : 0,
                setupWindow.unlocked ? "SETUP" : "LOCKED",
                (unsigned long)millis());
}

// ---- setup / loop ----------------------------------------------------------------
void setupWatchdog() {
  esp_task_wdt_config_t config = {};
  config.timeout_ms = NB_WDT_S * 1000;
  config.idle_core_mask = 0;
  config.trigger_panic = true;
  esp_err_t result = esp_task_wdt_reconfigure(&config);
  if (result == ESP_ERR_INVALID_STATE) esp_task_wdt_init(&config);
  esp_task_wdt_add(nullptr);
}

bool setupI2S() {
  // ESP32 is I2S master; ESP_I2S std mode defaults MCLK to 256 x fs, matching
  // the upstream I2S_MCLK_MULTIPLE_256 [IDF]. Capture both slots; audioTick
  // averages L+R so either faceplate input or the PCB stereo jack works.
  i2sIn.setPins(PIN_I2S_BCLK, PIN_I2S_WS, PIN_I2S_DOUT, PIN_I2S_DIN, PIN_I2S_MCLK);
  return i2sIn.begin(I2S_MODE_STD, 16000, I2S_DATA_BIT_WIDTH_16BIT,
                     I2S_SLOT_MODE_STEREO);
}

void setup() {
  Serial.begin(115200);
  uint32_t t0 = millis();
  while (!Serial && millis() - t0 < 3000) delay(10);
  Serial.println();
  Serial.println("=== Resonance puca-bridge " PUCA_BRIDGE_VERSION " ===");
  Serial.println("*** DEVELOPMENT: codec/MEMS proven; current deltas need hardware validation ***");
  Serial.printf("role=audio-bridge channel=%d target=PUCA DSP Original Edition\n",
                NB_CHANNEL);

  pinMode(PIN_LED_BOARD, OUTPUT);
  pinMode(PIN_LED_TOP, OUTPUT);
  pinMode(PIN_LED_BTM, OUTPUT);
  // GPIO15 is configured by the first touchRead(); do not claim it as a plain
  // digital GPIO first, or the electrode cannot use the RTC touch peripheral.
  digitalWrite(PIN_LED_BOARD, LOW);
  digitalWrite(PIN_LED_TOP, LOW);
  digitalWrite(PIN_LED_BTM, LOW);

  Serial.println("hold paw 1.2 s during the 5 s steady-red cue to ARM DJ; no hold = SAFE-IDLE");
  bootArmRequested = detectBootSetupHold();

  analogReadResolution(12);
  analogSetPinAttenuation(PIN_KNOB1, ADC_11db);
  analogSetPinAttenuation(PIN_KNOB2, ADC_11db);

  esp_read_mac(myMac, ESP_MAC_WIFI_STA);
  memcpy(myId, myMac + 3, sizeof(myId));
  Serial.printf("node id=%02X%02X%02X mac=%02X:%02X:%02X:%02X:%02X:%02X\n",
                myId[0], myId[1], myId[2], myMac[0], myMac[1], myMac[2],
                myMac[3], myMac[4], myMac[5]);

  Wire.begin(PIN_I2C_SDA, PIN_I2C_SCL, 100000); // [WMH] pins + 100 kHz
  codecReady = wm8978Init() && wm8978SetInput(inputLineIn);
  Serial.printf("codec: WM8978 @0x%02X %s (input=%s)\n", WM8978_ADDR,
                codecReady ? "init ok" : "INIT FAILED", inputLineIn ? "line" : "mic");

  audioInputReady = setupI2S();
  Serial.printf("i2s: 16 kHz stereo RX %s (mclk=%d bclk=%d ws=%d din=%d)\n",
                audioInputReady ? "ready" : "INIT FAILED",
                PIN_I2S_MCLK, PIN_I2S_BCLK, PIN_I2S_WS, PIN_I2S_DIN);
  audioActive = pucaPublisherShouldArmAtBoot(bootArmRequested, codecReady,
                                             audioInputReady);

  rxQueue = xQueueCreate(32, sizeof(RxItem));
  if (!rxQueue) Serial.println("rx queue allocation FAILED");
  else radioReady = setupEspNow();
  setupWatchdog();

  digitalWrite(PIN_LED_BOARD, radioReady ? HIGH : LOW);
  digitalWrite(PIN_LED_TOP, (mode != MODE_OFF && audioActive) ? HIGH : LOW);
  if (bootArmRequested && audioActive) {
    setupWindow.enter(millis());
    Serial.println("publisher=ARMED mode=DJ; controls=SETUP for 20 s");
    Serial.println("short touch cycles DJ/HEARTBEAT/EMBER/HUE; long hold locks");
  } else {
    Serial.println("publisher=SAFE-IDLE (no lighting frames); controls=LOCKED");
  }
  showStatus(millis());
  statusLedTick(millis());
  Serial.printf("mode=%s gain-knob=GPIO%d mode-knob=GPIO%d paw=GPIO%d\n",
                modeName(mode), PIN_KNOB1, PIN_KNOB2, PIN_TOUCH);
  Serial.println("status LED: LINE=1 long, MIC=2 long; DJ=1 short, HEARTBEAT=2, EMBER=3, HUE=4");
  Serial.println("keys: t=status-json M=next-live-mode A=audio-toggle I=mic/line H=heartbeat-line P=paw-cap-probe");
}

void loop() {
  esp_task_wdt_reset();
  uint32_t now = millis();
  handleSerial();
  if (netMode == PUCA_MODE_MAINT) {
    maintenanceTick();
    statusLedTick(now);
    statusTick(now);
    otaVerifyTick();
    delay(2);
    return;
  }
  processRx();
  if (netMode == PUCA_MODE_MAINT) return; // command switched radio ownership
  heartbeatTick(now);
  touchTick(now);
  statusLedTick(now);
  audioTick(); // blocks ~100 ms while audio is up; that is the loop cadence
  now = millis();
  statusLedTick(now);
  statusTick(now);
  otaVerifyTick();
  if (!audioInputReady) delay(10); // no I2S pacing -> do not spin the core
}
