beneckart/resonance-lighting/firmware/fixture/src/esp32/motion_trace.cpp

#include "motion_trace.h"

#include <Arduino.h>
#include <WebServer.h>
#include <esp_heap_caps.h>

#include "../core/motion_trace.h"
#include "../core/version.h"
#include "behavior_glue.h"
#include "identity.h"
#include "led_driver.h"
#include "sensors/sensors.h"
#include "telemetry.h"

static MotionTraceBuffer gTrace;
static uint32_t gLastMsaRead = 0;
static uint32_t gLastTraceSampleMs = 0;
static bool gPendingPresenceRising = false;
static bool gPresenceSentinelWhite = false;

#define RES_MOTION_TRACE_SAMPLE_INTERVAL_MS 300UL
#define RES_MOTION_TRACE_SAMPLE_HZ 3

bool motionTraceBuild() {
#if defined(RES_MSA_TRACE_TARGET)
  return true;
#else
  return false;
#endif
}

uint32_t motionTraceTargetId() {
#if defined(RES_MSA_TRACE_TARGET)
  return (uint32_t)RES_MSA_TRACE_TARGET;
#else
  return 0;
#endif
}

bool motionTraceTargetMatches() {
#if defined(RES_MSA_TRACE_TARGET)
  uint32_t actual = ((uint32_t)gMyId[0] << 16) |
                    ((uint32_t)gMyId[1] << 8) | gMyId[2];
  return actual == (uint32_t)RES_MSA_TRACE_TARGET;
#else
  return false;
#endif
}

uint32_t motionTraceCapacity() { return gTrace.capacity; }
uint32_t motionTraceCount() { return gTrace.count; }
uint32_t motionTraceOverwrites() { return gTrace.overwrites; }

void motionTraceNotePresenceSentinel(bool whiteActive) {
#if defined(RES_MSA_TRACE_TARGET) && defined(RES_CANOPY_PRESENCE_SENTINEL)
  gPresenceSentinelWhite = motionTraceTargetMatches() && whiteActive;
#else
  (void)whiteActive;
#endif
}

void motionTraceInit() {
#if defined(RES_MSA_TRACE_TARGET)
  if (!motionTraceTargetMatches()) {
    Serial.printf("motion-trace: target mismatch build=%06lX actual=%s; disabled\n",
                  (unsigned long)motionTraceTargetId(), gShortId.c_str());
    return;
  }

  // At the bounded diagnostic cadence, the 8192-sample PSRAM buffer is ample
  // and the internal-RAM fallback still retains just over five minutes. The
  // one-loop presence edge is held until the next recorded sample.
  uint32_t capacity = 8192;
  MotionTraceSample *storage = (MotionTraceSample *)heap_caps_malloc(
      sizeof(MotionTraceSample) * capacity, MALLOC_CAP_SPIRAM | MALLOC_CAP_8BIT);
  if (!storage) {
    capacity = 1024;
    storage = (MotionTraceSample *)heap_caps_malloc(
        sizeof(MotionTraceSample) * capacity, MALLOC_CAP_8BIT);
  }
  motionTraceBufferInit(gTrace, storage, storage ? capacity : 0);
  Serial.printf("motion-trace: armed target=%s capacity=%lu samples bytes=%lu\n",
                gShortId.c_str(), (unsigned long)gTrace.capacity,
                (unsigned long)(gTrace.capacity * sizeof(MotionTraceSample)));
#endif
}

static int16_t signedMilli(float value) {
  float scaled = value * 1000.0f;
  if (scaled > 32767.0f) return 32767;
  if (scaled < -32768.0f) return -32768;
  return (int16_t)(scaled >= 0 ? scaled + 0.5f : scaled - 0.5f);
}

static uint16_t unsignedMilli(float value) {
  if (!(value > 0.0f)) return 0;
  float scaled = value * 1000.0f;
  if (scaled >= 65535.0f) return 65535;
  return (uint16_t)(scaled + 0.5f);
}

static uint16_t centiDegrees(float value) {
  if (!(value > 0.0f)) return 0;
  float scaled = value * 100.0f;
  if (scaled >= 65535.0f) return 65535;
  return (uint16_t)(scaled + 0.5f);
}

void motionTraceTick() {
#if defined(RES_MSA_TRACE_TARGET)
  if (!motionTraceTargetMatches() || !gTrace.capacity) return;
  // The TMF edge and the bounded MSA trace sample need not land in the same
  // loop.
  // Hold the one-loop edge until it has been committed beside a motion sample.
  gPendingPresenceRising =
      gPendingPresenceRising || behaviorTofPresenceRising();
  const SensorSnapshot &sensor = sensors();
  if (!sensor.msaOk || !sensor.msaReads || sensor.msaReads == gLastMsaRead)
    return;
  if (gLastTraceSampleMs &&
      sensor.msaSampleMs - gLastTraceSampleMs <
          RES_MOTION_TRACE_SAMPLE_INTERVAL_MS)
    return;
  gLastMsaRead = sensor.msaReads;
  gLastTraceSampleMs = sensor.msaSampleMs;

  MotionTraceSample sample = {};
  sample.uptimeMs = sensor.msaSampleMs;
  sample.accelMg[0] = signedMilli(sensor.accelXG);
  sample.accelMg[1] = signedMilli(sensor.accelYG);
  sample.accelMg[2] = signedMilli(sensor.accelZG);
  sample.gravityMg[0] = signedMilli(sensor.gravityXG);
  sample.gravityMg[1] = signedMilli(sensor.gravityYG);
  sample.gravityMg[2] = signedMilli(sensor.gravityZG);
  sample.tiltCdeg = centiDegrees(sensor.tiltDeg);
  sample.swayMg = unsignedMilli(sensor.swayEnvG);
  sample.tmfReads = sensor.tmfReads;
  sample.tofDepthMm = sensor.tofDepthMm;
  sample.tofConfidence = sensor.tofConfidence;
  memcpy(sample.tofZoneMm, sensor.tofZoneMm, sizeof(sample.tofZoneMm));
  memcpy(sample.tofZoneConfidence, sensor.tofZoneConfidence,
         sizeof(sample.tofZoneConfidence));
  sample.presenceActive = behaviorTofPresenceActive() ? 1 : 0;
  sample.presenceRising = gPendingPresenceRising ? 1 : 0;
  sample.presenceSentinelWhite = gPresenceSentinelWhite ? 1 : 0;
  gPendingPresenceRising = false;
  sample.lifeState = gTelemetryLifeState;
  sample.program = gTelemetryProgram;
  sample.powerTier = gTelemetryPowerTier;
  LedOutputSnapshot led = ledOutputSnapshot();
  sample.ledRailOn = led.railOn;
  sample.ledR = led.r;
  sample.ledG = led.g;
  sample.ledB = led.b;
  sample.ledW = led.w;
  sample.ledLitPixels = led.litPixels;
  motionTraceBufferAppend(gTrace, sample);
#endif
}

static uint32_t parseUint32(const String &text, uint32_t fallback) {
  if (!text.length()) return fallback;
  char *end = nullptr;
  unsigned long value = strtoul(text.c_str(), &end, 10);
  return end && *end == '\0' ? (uint32_t)value : fallback;
}

static void appendArray(String &body, const uint16_t *values, uint8_t count) {
  body += '[';
  for (uint8_t i = 0; i < count; ++i) {
    if (i) body += ',';
    body += String(values[i]);
  }
  body += ']';
}

void motionTraceHandleHttp(WebServer &server) {
#if !defined(RES_MSA_TRACE_TARGET)
  server.send(404, "application/json", "{\"ok\":false,\"error\":\"not a trace build\"}\n");
#else
  if (!motionTraceTargetMatches()) {
    server.send(409, "application/json", "{\"ok\":false,\"error\":\"trace target mismatch\"}\n");
    return;
  }
  if (!gTrace.capacity) {
    server.send(503, "application/json", "{\"ok\":false,\"error\":\"trace buffer unavailable\"}\n");
    return;
  }

  uint32_t after = server.hasArg("after")
                       ? parseUint32(server.arg("after"), 0)
                       : 0;
  uint32_t requested = server.hasArg("max")
                           ? parseUint32(server.arg("max"), 16)
                           : 16;
  if (requested > 32) requested = 32;
  MotionTraceSample batch[32];
  uint32_t count = requested
                       ? motionTraceBufferCollectAfter(gTrace, after, batch,
                                                       requested)
                       : 0;

  String body;
  body.reserve(512 + count * 360);
  body += "{\"kind\":\"meta\",\"schema\":1,\"fixture_id\":\"";
  body += gShortId;
  body += "\",\"fw\":\"" RES_FIXTURE_VERSION "\",\"target\":\"";
  char target[7];
  snprintf(target, sizeof(target), "%06lX",
           (unsigned long)motionTraceTargetId());
  body += target;
  body += "\",\"sample_hz\":" + String(RES_MOTION_TRACE_SAMPLE_HZ);
  body += ",\"sample_interval_ms\":" +
          String((unsigned long)RES_MOTION_TRACE_SAMPLE_INTERVAL_MS);
  body += ",\"presence_sentinel_build\":";
#if defined(RES_CANOPY_PRESENCE_SENTINEL)
  body += "true";
#else
  body += "false";
#endif
  body += ",\"presence_distant_range_build\":";
#if defined(RES_CANOPY_PRESENCE_DISTANT_RANGE)
  body += "true";
#else
  body += "false";
#endif
  body += ",\"sample_bytes\":";
  body += String((unsigned)sizeof(MotionTraceSample));
  body += ",\"capacity\":" + String((unsigned long)gTrace.capacity);
  body += ",\"count\":" + String((unsigned long)gTrace.count);
  body += ",\"oldest_seq\":" +
          String((unsigned long)motionTraceBufferOldestSeq(gTrace));
  body += ",\"newest_seq\":" +
          String((unsigned long)motionTraceBufferNewestSeq(gTrace));
  body += ",\"overwrites\":" + String((unsigned long)gTrace.overwrites);
  body += "}\n";

  for (uint32_t i = 0; i < count; ++i) {
    const MotionTraceSample &sample = batch[i];
    body += "{\"kind\":\"sample\",\"seq\":" +
            String((unsigned long)sample.seq);
    body += ",\"uptime_ms\":" + String((unsigned long)sample.uptimeMs);
    body += ",\"accel_mg\":[" + String(sample.accelMg[0]) + ',' +
            String(sample.accelMg[1]) + ',' + String(sample.accelMg[2]) + ']';
    body += ",\"gravity_mg\":[" + String(sample.gravityMg[0]) + ',' +
            String(sample.gravityMg[1]) + ',' + String(sample.gravityMg[2]) + ']';
    body += ",\"tilt_cdeg\":" + String(sample.tiltCdeg);
    body += ",\"sway_mg\":" + String(sample.swayMg);
    body += ",\"tmf_reads\":" + String((unsigned long)sample.tmfReads);
    body += ",\"tof_depth_mm\":" + String(sample.tofDepthMm);
    body += ",\"tof_confidence\":" + String(sample.tofConfidence);
    body += ",\"tof_zone_mm\":";
    appendArray(body, sample.tofZoneMm, MOTION_TRACE_ZONE_COUNT);
    body += ",\"tof_zone_confidence\":";
    appendArray(body, sample.tofZoneConfidence, MOTION_TRACE_ZONE_COUNT);
    body += ",\"presence_active\":" + String(sample.presenceActive);
    body += ",\"presence_rising\":" + String(sample.presenceRising);
    body += ",\"presence_sentinel_white\":" +
            String(sample.presenceSentinelWhite);
    body += ",\"life_state\":" + String(sample.lifeState);
    body += ",\"program\":" + String(sample.program);
    body += ",\"power_tier\":" + String(sample.powerTier);
    body += ",\"led\":[" + String(sample.ledRailOn) + ',' +
            String(sample.ledR) + ',' + String(sample.ledG) + ',' +
            String(sample.ledB) + ',' + String(sample.ledW) + ',' +
            String(sample.ledLitPixels) + "]}\n";
  }
  server.send(200, "application/x-ndjson", body);
#endif
}
