beneckart/resonance-lighting/firmware/net_bench/net_bench.ino

// Resonance net-bench -- ESP-NOW networking feasibility bench for PowerFeather V2
// (ESP32-S3). Throwaway-friendly sketch to de-risk basing ~100 fixtures on this
// board: validates ESP-NOW broadcast comms (master-multicast + peer mesh), per-link
// packet-delivery-ratio / RSSI, a maintenance-mode WiFi OTA cycle, power telemetry,
// a watchdog, and battery stability. See docs/tests/NETWORKING_FEASIBILITY_5NODE_*.
//
// Forked from firmware/power_bench (reuses telemetry, OTA /update, autosleep guard).
//
// ROLES (build flag): master broadcasts SHOW_FRAME commands + WiFi-STA-joins the
// bench AP and bridges per-peer stats to the host over UDP:54321; peers run pure
// ESP-NOW on battery and broadcast HEARTBEAT (id, seq, battery, dl-PDR/RSSI).
//
// HARD ADR CONSTRAINTS: OTA is STANDARD WiFi only (ADR 0010) -- ESP-NOW carries only
// small control/state/metadata, never firmware bytes. USB/pogo stays recovery path.
//
// Build/flash (see build.sh):
//   ./build.sh --role master --channel 6 --port /dev/ttyACM0
//   ./build.sh --role peer   --channel 6 --port /dev/ttyACM1
// The bench AP MUST be on the same fixed channel as --channel (see README).

#include <Arduino.h>
#include <WiFi.h>
#include <WebServer.h>
#include <Update.h>
#include <WiFiUdp.h>
#include <esp_now.h>
#include <esp_wifi.h>
#include "esp_mac.h"
#include "esp_system.h"
#include "esp_ota_ops.h"
#include "esp_sleep.h"
#include "esp_timer.h"
#include "esp_task_wdt.h"
#include "esp_adc/adc_continuous.h"
#include "esp_adc/adc_cali.h"
#include "esp_adc/adc_cali_scheme.h"
#include "esp32-hal-periman.h"
#include "esp_heap_caps.h"
#include "driver/rtc_io.h"
#include <Preferences.h>
#include <Wire.h>
// Env sensors (MPP sweep): auto-probed on the STEMMA bus (Wire1) at boot --
// one image serves sensored and bare boards alike. See envInit()/envTick().
#include <Adafruit_TSL2591.h>
#include <Adafruit_SHT31.h>
#include <Adafruit_NeoPixel.h>
#ifndef NB_SENSOR_TRIAD
#define NB_SENSOR_TRIAD 0
#endif
#ifndef NB_MAGIC_WAND
#define NB_MAGIC_WAND 0
#endif
#if NB_SENSOR_TRIAD
#include <Adafruit_MSA301.h>
#include <Adafruit_BMP5xx.h>
#include <SparkFun_TMF882X_Library.h>
#endif
#include "magic_wand_mode.h"

#define NET_BENCH_VERSION "net-bench-2026-08-19.2" // NeoHex Magic Wand fleet role
#define RES_BOARD_NAME "powerfeather_v2"
#define NB_LED_PIN 46 // PowerFeather onboard user LED (battery-level indicator)

// ---- WiFi secrets (gitignored; copied from ../power_bench by build.sh) ------
#if __has_include("wifi_secrets.h")
#include "wifi_secrets.h"
#define RES_HAS_WIFI_SECRETS 1
#else
#define RES_HAS_WIFI_SECRETS 0
#endif

// ---- PowerFeather SDK (telemetry) ------------------------------------------
#include <PowerFeather.h>
#include "../powerfeather_solar_guard.h"
using namespace PowerFeather;
#if !defined(POWERFEATHER_BOARD_V2) && !defined(CONFIG_ESP32S3_POWERFEATHER_V2)
#error "Build with -DPOWERFEATHER_BOARD_V2=1 so the SDK uses the V2 MAX17260 fuel gauge. See firmware/net_bench/build.sh."
#endif
#ifndef RES_PF_BATTERY_CAPACITY_MAH
#define RES_PF_BATTERY_CAPACITY_MAH 2000
#endif
#ifndef RES_PF_BATTERY_TYPE
#define RES_PF_BATTERY_TYPE Mainboard::BatteryType::Generic_3V7
#endif
#ifndef RES_PF_ENABLE_CHARGING
#define RES_PF_ENABLE_CHARGING 1
#endif
#ifndef RES_PF_MAX_CHARGE_MA
#define RES_PF_MAX_CHARGE_MA 2000.0f
#endif
#ifndef RES_PF_MAINTAIN_V
#define RES_PF_MAINTAIN_V 4.6f
#endif
#ifndef NB_GAUGE_CURRENT_DIVISOR
#define NB_GAUGE_CURRENT_DIVISOR 1.08f // MAX17260 reads +8% high; ADR 0023, replicated across 8 sessions
#endif

// ---- net-bench config (override with -D at build time) ---------------------
#if !defined(NB_ROLE_MASTER) && !defined(NB_ROLE_PEER)
#define NB_ROLE_PEER 1
#endif
#ifndef NB_CHANNEL
#define NB_CHANNEL 6 // locked WiFi/ESP-NOW channel; MUST equal the bench AP channel
#endif
#ifndef NB_FRAME_HZ
#define NB_FRAME_HZ 10 // master SHOW_FRAME rate (0 = master is a pure bridge/mesh node)
#endif
#ifndef NB_HB_HZ
#define NB_HB_HZ 2 // peer HEARTBEAT rate
#endif
#ifndef NB_JITTER_PCT
#define NB_JITTER_PCT 30 // +/- jitter (% of period) on periodic sends (anti-collision)
#endif
#ifndef NB_WDT_S
#define NB_WDT_S 8 // task watchdog timeout (s)
#endif
#ifndef NB_MAINT_TIMEOUT_S
#define NB_MAINT_TIMEOUT_S 600 // peer auto-resume from maintenance if no OTA (s)
#endif
#ifndef NB_BRIDGE_HZ
#define NB_BRIDGE_HZ 1 // master -> host UDP stats rate
#endif
#ifndef NB_MAX_TRACKED
#define NB_MAX_TRACKED 16 // per-source tracking table size (5-board bench + headroom)
#endif
#ifndef NB_WIFI_LOWPOWER
#define NB_WIFI_LOWPOWER 0
#endif
// ---- WiFi scan-report (field 2.4 GHz coverage mapping over ESP-NOW) ---------
// A field PEER built with -DNB_SCAN_REPORT periodically WiFi-scans (never
// associates) and broadcasts each visible AP as an NB_SCANAP packet. A board
// built with -DNB_SERIAL_BRIDGE (a master) relays everything it hears to USB
// serial (so a desk-tethered bridge logs the fleet WITHOUT a laptop in the
// field) -- the answer to the WiFi range diagnostic / item (b) of the solar-
// telemetry plan. Scan-only: no association, so the radio stays pinned to
// NB_CHANNEL for ESP-NOW (no Eero-channel coupling). See README.
#ifndef NB_SCAN_S
#define NB_SCAN_S 20 // field-peer scan-report interval (s)
#endif
#ifndef NB_SCAN_MAX
#define NB_SCAN_MAX 12 // max APs reported per scan batch (bounds the ESP-NOW burst)
#endif
// ---- sleep-cycle (field-representative duty-cycled load measurement) --------
// -DNB_SLEEP_CYCLE makes a peer wake -> send a telemetry heartbeat -> listen
// briefly for ENTER_MAINT (preserve no-touch OTA) -> deep-sleep NB_SLEEP_S. On
// battery-only this measures the duty-cycled average draw (the overnight/idle
// budget) -- vs the always-on ~168 mA that flattens a 2 Ah cell in ~12 h. Run it
// multi-hour/overnight: avg current = SOC/coulomb drop over time (gauge is too
// coarse for a precise per-wake sleep current -> use an external meter for that).
#ifndef NB_SLEEP_S
#define NB_SLEEP_S 30 // deep-sleep interval between wakes (s)
#endif
#ifndef NB_WAKE_LISTEN_MS
#define NB_WAKE_LISTEN_MS 400 // per-wake window to catch ENTER_MAINT before re-sleeping (ms)
#endif

// Remote low-battery park command. A bare serial 'S' sleeps peers for this long.
#ifndef NB_REMOTE_SLEEP_S
#define NB_REMOTE_SLEEP_S 21600 // 6 hours; enough to wait for sun without losing recoverability
#endif
#ifndef NB_TARGET_SLEEP_DEFAULT_S
#define NB_TARGET_SLEEP_DEFAULT_S 3600 // selected-peer "solar nap" default
#endif
// Optional P126 VDC-tap solenoid. The Adafruit MOSFET driver's flyback diode and
// gate pulldown are mandatory because VDC is always live; unlike a 3V3-fed coil,
// the firmware cannot kill coil power with EN_3V3. Enable only on the wired peer.
#ifndef NB_SOLENOID_PIN
#define NB_SOLENOID_PIN D7 // PowerFeather D7 is GPIO37 (not GPIO7)
#endif
#ifndef NB_SOLENOID_DEFAULT_MS
#define NB_SOLENOID_DEFAULT_MS 40
#endif
#ifndef NB_SOLENOID_MIN_MS
#define NB_SOLENOID_MIN_MS 5
#endif
#ifndef NB_SOLENOID_MAX_MS
#define NB_SOLENOID_MAX_MS 300
#endif
#ifndef NB_SOLENOID_REST_MS
#define NB_SOLENOID_REST_MS 80
#endif
#ifndef NB_SOLENOID_BUTTON_PIN
#define NB_SOLENOID_BUTTON_PIN BTN // PowerFeather USER/BOOT button, GPIO0, active LOW
#endif
#ifndef NB_SOLENOID_BUTTON_DEBOUNCE_MS
#define NB_SOLENOID_BUTTON_DEBOUNCE_MS 30
#endif
#if defined(NB_CAPBANK_PROBE) && !defined(NB_SOLENOID_D7)
#error "NB_CAPBANK_PROBE requires NB_SOLENOID_D7"
#endif
// v1.0 capbank telemetry. Nominal cable is A4=VSNS, A5=D7S; the bench cable
// may be reversed because both signals are ADC1-safe and the PCB was designed
// to tolerate that. Override both pins at build time when reversed.
#ifndef NB_CAPBANK_VSNS_PIN
#define NB_CAPBANK_VSNS_PIN A4
#endif
#ifndef NB_CAPBANK_D7S_PIN
#define NB_CAPBANK_D7S_PIN A5
#endif
#ifndef NB_CAPBANK_VSNS_TOP_OHM
#define NB_CAPBANK_VSNS_TOP_OHM 100000.0f
#endif
#ifndef NB_CAPBANK_VSNS_BOTTOM_OHM
#define NB_CAPBANK_VSNS_BOTTOM_OHM 33000.0f
#endif
#ifndef NB_CAPBANK_PROBE_RECOVERY_MS
#define NB_CAPBANK_PROBE_RECOVERY_MS 250
#endif
#if defined(NB_CAPBANK_WAVEFORM) && !defined(NB_CAPBANK_PROBE)
#error "NB_CAPBANK_WAVEFORM requires NB_CAPBANK_PROBE"
#endif
// Bench-only waveform recorder. The ESP32-S3 ADC ceiling is 83,333 total
// conversions/s; two interleaved ADC1 channels at 80 kconv/s give about
// 40 ksps/channel. HTTP only arms/downloads the capture. WiFi is fully off
// during the strike so radio current cannot contaminate the waveform.
#ifndef NB_CAPBANK_WAVEFORM_CONV_HZ
#define NB_CAPBANK_WAVEFORM_CONV_HZ 80000
#endif
#ifndef NB_CAPBANK_WAVEFORM_PRE_MS
#define NB_CAPBANK_WAVEFORM_PRE_MS 10
#endif
#ifndef NB_CAPBANK_WAVEFORM_POST_MS
#define NB_CAPBANK_WAVEFORM_POST_MS 250
#endif
#ifndef NB_CAPBANK_WAVEFORM_MAX_PULSE_MS
#define NB_CAPBANK_WAVEFORM_MAX_PULSE_MS 50
#endif
#ifndef NB_CAPBANK_WAVEFORM_MAX_SAMPLES
#define NB_CAPBANK_WAVEFORM_MAX_SAMPLES 14000
#endif
#ifndef NB_SOLENOID_RGB_BUTTON_POLL_MS
#define NB_SOLENOID_RGB_BUTTON_POLL_MS 50
#endif
#ifndef NB_SOLENOID_RGB_BUTTON_DEBOUNCE_MS
#define NB_SOLENOID_RGB_BUTTON_DEBOUNCE_MS 50
#endif
#ifndef NB_SOLENOID_RGB_BUTTON_MAX_ERRORS
#define NB_SOLENOID_RGB_BUTTON_MAX_ERRORS 3
#endif
#ifndef NB_SOLENOID_RGB_BUTTON_PROBE_MS
#define NB_SOLENOID_RGB_BUTTON_PROBE_MS 250
#endif
#ifndef NB_SOLENOID_RGB_BUTTON_PROBE_ATTEMPTS
#define NB_SOLENOID_RGB_BUTTON_PROBE_ATTEMPTS 8
#endif
#ifndef NB_SOLENOID_NAV_POLL_MS
#define NB_SOLENOID_NAV_POLL_MS 50
#endif
#ifndef NB_SOLENOID_NAV_DEBOUNCE_MS
#define NB_SOLENOID_NAV_DEBOUNCE_MS 50
#endif
#ifndef NB_SOLENOID_NAV_PROBE_MS
#define NB_SOLENOID_NAV_PROBE_MS 250
#endif
#ifndef NB_SOLENOID_NAV_PROBE_ATTEMPTS
#define NB_SOLENOID_NAV_PROBE_ATTEMPTS 8
#endif
#ifndef NB_SOLENOID_NAV_MAX_ERRORS
#define NB_SOLENOID_NAV_MAX_ERRORS 3
#endif
#ifndef NB_DRAWDOWN_PIXEL_PIN
#define NB_DRAWDOWN_PIXEL_PIN 10 // GPIO10 / A0: direct-GPIO HEX bench harness
#endif
#ifndef NB_DRAWDOWN_PIXEL_COUNT
#define NB_DRAWDOWN_PIXEL_COUNT 37
#endif
#ifndef NB_DRAWDOWN_LIT_COUNT
#define NB_DRAWDOWN_LIT_COUNT NB_DRAWDOWN_PIXEL_COUNT
#endif
#ifndef NB_DRAWDOWN_BRIGHTNESS
#define NB_DRAWDOWN_BRIGHTNESS 128 // measured about 0.75 A battery-side on the current HEX rig
#endif
#ifndef NB_DRAWDOWN_R
#define NB_DRAWDOWN_R 255
#endif
#ifndef NB_DRAWDOWN_G
#define NB_DRAWDOWN_G 255
#endif
#ifndef NB_DRAWDOWN_B
#define NB_DRAWDOWN_B 255
#endif
#ifndef NB_DRAWDOWN_DEFAULT_MAH
#define NB_DRAWDOWN_DEFAULT_MAH 3500 // full 7.2 Ah -> roughly half-full/hungry
#endif
#ifndef NB_DRAWDOWN_SOFT_FLOOR_MV
#define NB_DRAWDOWN_SOFT_FLOOR_MV 3180 // loaded LFP, after the initial sag window
#endif
#ifndef NB_DRAWDOWN_HARD_FLOOR_MV
#define NB_DRAWDOWN_HARD_FLOOR_MV 3050 // stay well above precharge/trickle territory
#endif
#ifndef NB_DRAWDOWN_MIN_RUN_S
#define NB_DRAWDOWN_MIN_RUN_S 1800 // ignore early load sag for the soft floor
#endif
#ifndef NB_DRAWDOWN_SLEEP_S
#define NB_DRAWDOWN_SLEEP_S 43200 // 12 h: preserve the hungry cell for tomorrow morning
#endif
// ---- field-cycle (production-ish solar day / radio-night lifecycle) --------
// -DNB_FIELD_CYCLE makes a peer run an autonomous state machine:
// charge/sleep on external supply, wait-full, draw down in dark with the normal
// ESP-NOW radio load, then protect-sleep at a low LFP voltage. Timer wakes keep
// it recoverable; a sustained U can still catch an awake window for OTA.
#ifndef NB_FIELD_CHARGE_SLEEP_S
#define NB_FIELD_CHARGE_SLEEP_S 300 // charge-mode telemetry cadence while sleeping
#endif
#ifndef NB_FIELD_WAIT_SLEEP_S
#define NB_FIELD_WAIT_SLEEP_S 300 // full-but-daylight check cadence
#endif
#ifndef NB_FIELD_PROTECT_SLEEP_S
#define NB_FIELD_PROTECT_SLEEP_S 900 // low-battery protect recheck cadence
#endif
#ifndef NB_FIELD_WAKE_LISTEN_MS
#define NB_FIELD_WAKE_LISTEN_MS 8000 // timer-wake OTA/telemetry window before re-sleep
#endif
#ifndef NB_FIELD_COLD_LISTEN_MS
#define NB_FIELD_COLD_LISTEN_MS 30000 // cold boot catch window before first sleep
#endif
#ifndef NB_FIELD_FULL_MV
#define NB_FIELD_FULL_MV 3600 // PowerFeather LFP CV target / effectively full candidate
#endif
#ifndef NB_FIELD_FULL_TAPER_MA
#define NB_FIELD_FULL_TAPER_MA 120 // net battery charge current at/under this near top = full-ish
#endif
#ifndef NB_FIELD_DIM_MV
#define NB_FIELD_DIM_MV 3150 // ADR 0046 charge-knee ladder: dim load at 3.15 V loaded
#endif
#ifndef NB_FIELD_DIM_CLEAR_MV
#define NB_FIELD_DIM_CLEAR_MV (NB_FIELD_DIM_MV + 150) // hysteresis; bench dim latch normally clears on charge cycle
#endif
#ifndef NB_FIELD_DIM_CONFIRM_S
#define NB_FIELD_DIM_CONFIRM_S 10 // dim before a marginal source can reset for the full 60 s low debounce
#endif
#ifndef NB_FIELD_LOW_MV
#define NB_FIELD_LOW_MV 3100 // ADR 0046 charge-knee ladder: LED-off/protect threshold under load
#endif
#ifndef NB_FIELD_CRITICAL_MV
#define NB_FIELD_CRITICAL_MV 3050 // ADR 0046 charge-knee ladder: sparse sleep / hard backstop under load
#endif
#ifndef NB_FIELD_LOW_CONFIRM_S
#define NB_FIELD_LOW_CONFIRM_S 60 // ADR 0023: avoid one-sample load-sag false transitions
#endif
#ifndef NB_FIELD_PROTECT_RETRY_MV
#define NB_FIELD_PROTECT_RETRY_MV (NB_FIELD_LOW_MV + 150) // only used when dark retry is explicitly enabled
#endif
#ifndef NB_FIELD_PROTECT_RETRY_DARK
#define NB_FIELD_PROTECT_RETRY_DARK 0 // default: latch protect until clear solar/USB charge recovery
#endif
#ifndef NB_FIELD_DRAWDOWN_MIN_S
#define NB_FIELD_DRAWDOWN_MIN_S NB_DRAWDOWN_MIN_RUN_S
#endif
#ifndef NB_FIELD_LED_LOAD
#define NB_FIELD_LED_LOAD 0 // opt-in: use the configured addressable-LED load during field-cycle draw
#endif
#ifndef NB_FIELD_LED_RGBW
#define NB_FIELD_LED_RGBW 0 // production 4 W single pixel: RGBW wire order, RGB full and W off
#endif
#ifndef NB_FIELD_LED_SPIRAL_RGB
#define NB_FIELD_LED_SPIRAL_RGB 0 // LED Studio spiral + 120-degree symmetric pure-R/G/B triplet
#endif
#ifndef NB_FIELD_LED_FRAME_MS
#define NB_FIELD_LED_FRAME_MS 290 // LED Studio default speed=30; ~21 s center-edge-center cycle
#endif
#ifndef NB_FIELD_LED_DIM_BRIGHTNESS
#define NB_FIELD_LED_DIM_BRIGHTNESS ((NB_DRAWDOWN_BRIGHTNESS > 1) ? (NB_DRAWDOWN_BRIGHTNESS / 2) : 1)
#endif
#ifndef NB_FIELD_LED_START_DELAY_MS
#define NB_FIELD_LED_START_DELAY_MS 1000 // let power + ESP-NOW settle before applying the field load
#endif
#ifndef NB_FIELD_LED_RETRY_DELAY_MS
#define NB_FIELD_LED_RETRY_DELAY_MS 10000 // let a tripped cell/protection path recover before the one dim retry
#endif
#ifndef NB_FIELD_LED_RAMP_MS
#define NB_FIELD_LED_RAMP_MS 3200 // four 800 ms steps expose delayed harness/cell sag before full load
#endif
#ifndef NB_FIELD_LED_RAMP_STEPS
#define NB_FIELD_LED_RAMP_STEPS 4
#endif
#if NB_FIELD_LED_SPIRAL_RGB && NB_DRAWDOWN_PIXEL_COUNT != 37
#error "NB_FIELD_LED_SPIRAL_RGB requires the 37-pixel M5Stack HEX geometry"
#endif
#if NB_FIELD_LED_SPIRAL_RGB && NB_FIELD_LED_RGBW
#error "NB_FIELD_LED_SPIRAL_RGB and NB_FIELD_LED_RGBW are mutually exclusive"
#endif
#if NB_FIELD_LED_RGBW && NB_DRAWDOWN_PIXEL_COUNT != 1
#error "NB_FIELD_LED_RGBW requires NB_DRAWDOWN_PIXEL_COUNT=1"
#endif
#ifndef NB_FIELD_SUN_SUPPLY_MV
#define NB_FIELD_SUN_SUPPLY_MV 4000 // supply/panel voltage that counts as present
#endif
#ifndef NB_FIELD_SUN_CHARGE_MA
#define NB_FIELD_SUN_CHARGE_MA 20 // input current into board that counts as useful sun/supply
#endif
#ifndef NB_FIELD_RECOVER_CHARGE_MA
#define NB_FIELD_RECOVER_CHARGE_MA 20 // battery charge current needed to release protect latch
#endif
#ifndef NB_FIELD_DUSK_LUX_X10
#define NB_FIELD_DUSK_LUX_X10 2000 // 200 lux: July field trace reaches this near visual sunset
#endif
#ifndef NB_FIELD_DAWN_LUX_X10
#define NB_FIELD_DAWN_LUX_X10 5000 // 500 lux: separate dawn hysteresis avoids LED/light chatter
#endif
#ifndef NB_FIELD_DUSK_CONFIRM_S
#define NB_FIELD_DUSK_CONFIRM_S 300 // sensored peer: require 5 min below the lux threshold
#endif
#ifndef NB_FIELD_DUSK_NO_SENSOR_CONFIRM_S
#define NB_FIELD_DUSK_NO_SENSOR_CONFIRM_S 1800 // bare peer fallback: 30 min without useful input
#endif
#ifndef NB_FIELD_DRAWDOWN_HZ
#define NB_FIELD_DRAWDOWN_HZ 1 // production-ish always-awake radio draw cadence
#endif
#ifndef NB_FIELD_MPPT
#define NB_FIELD_MPPT 0 // opt-in: daylight-only 4.6/4.8/5.0 V VINDPM perturb
#endif
#ifndef NB_FIELD_MPPT_HOLD_BEST
#define NB_FIELD_MPPT_HOLD_BEST 0 // default bench mode clamps back to 4.6 V before sleep
#endif
#ifndef NB_FIELD_MPPT_DEFAULT_V10
#define NB_FIELD_MPPT_DEFAULT_V10 46 // 4.6 V: USB/power-bank rescue-safe default
#endif
#ifndef NB_FIELD_MPPT_MID_V10
#define NB_FIELD_MPPT_MID_V10 48
#endif
#ifndef NB_FIELD_MPPT_HIGH_V10
#define NB_FIELD_MPPT_HIGH_V10 50
#endif
#ifndef NB_FIELD_MPPT_MIN_BATT_MV
#define NB_FIELD_MPPT_MIN_BATT_MV NB_FIELD_DIM_CLEAR_MV
#endif
#ifndef NB_FIELD_MPPT_TAPER_MV
#define NB_FIELD_MPPT_TAPER_MV NB_FIELD_FULL_MV
#endif
#ifndef NB_FIELD_MPPT_TAPER_MA
#define NB_FIELD_MPPT_TAPER_MA 220 // skip if near top and not accepting much current
#endif
#ifndef NB_FIELD_MPPT_MIN_SUPPLY_MA
#define NB_FIELD_MPPT_MIN_SUPPLY_MA 200 // avoid noisy weak-sun comparisons
#endif
#ifndef NB_FIELD_MPPT_MIN_PANEL_W_X100
#define NB_FIELD_MPPT_MIN_PANEL_W_X100 100 // 1.00 W minimum baseline panel power
#endif
#ifndef NB_FIELD_MPPT_SETTLE_MS
#define NB_FIELD_MPPT_SETTLE_MS 900
#endif
#ifndef NB_MAINTAIN_MIN_V10
#define NB_MAINTAIN_MIN_V10 46 // PowerFeather SDK intentionally clamps at 4.6 V
#endif
#ifndef NB_MAINTAIN_MAX_V10
#define NB_MAINTAIN_MAX_V10 168 // PowerFeather SDK supports 16.8 V maximum
#endif
#ifndef NB_MAINT_MIN_LFP_MV
#define NB_MAINT_MIN_LFP_MV 3200 // below this, defer OTA until the LFP has charged
#endif
#ifndef NB_MAINT_MIN_3V7_MV
#define NB_MAINT_MIN_3V7_MV 3600 // low Li-ion cells have browned out on WiFi entry
#endif
#ifndef NB_MAINT_SUPPLY_OVERRIDE_MA
#define NB_MAINT_SUPPLY_OVERRIDE_MA 250 // strong external/solar input can override low Vbat
#endif
#ifndef NB_MAINT_POWER_ENFORCE
#define NB_MAINT_POWER_ENFORCE 0 // default: report low-power maintenance risk; do not block OTA tests
#endif
#ifndef NB_MAINT_REFUSE_REPORT_MS
#define NB_MAINT_REFUSE_REPORT_MS 5000 // throttle warning prints/HBs during sustained U
#endif
#ifndef NB_CAPACITY_MIN_MAH
#define NB_CAPACITY_MIN_MAH 100
#endif
#ifndef NB_CAPACITY_MAX_MAH
#define NB_CAPACITY_MAX_MAH 30000
#endif
#ifndef NB_CHARGE_MIN_MA
#define NB_CHARGE_MIN_MA 40
#endif
#ifndef NB_CHARGE_MAX_MA
#define NB_CHARGE_MAX_MA 2000
#endif
#ifndef NB_CHARGE_POLICY_VERSION
#define NB_CHARGE_POLICY_VERSION 1
#endif
// NB_START_MAINT, NB_WDT_HANGTEST, NB_AUTOSLEEP, NB_SCAN_REPORT, NB_SERIAL_BRIDGE,
// NB_MAINT_AP, NB_SLEEP_CYCLE, NB_FIELD_CYCLE are presence-only flags.
#ifndef NB_MAINT_AP_PASS
#define NB_MAINT_AP_PASS "resonance"
#endif
#ifndef NB_MAINT_AP_PREFIX
#define NB_MAINT_AP_PREFIX "ResonanceMaint"
#endif
#ifndef NB_BUDGET_MAH
#define NB_BUDGET_MAH 1000
#endif
#ifndef NB_WAKE_S
#define NB_WAKE_S 900
#endif
#define NB_LOOP_LIMIT 25   // NVS reboot-loop breaker threshold
#define NB_HEALTHY_MS 120000 // a boot is "healthy" after surviving this long

#if defined(NB_ROLE_MASTER)
static const bool IS_MASTER = true;
#else
static const bool IS_MASTER = false;
#endif

#if defined(NB_SERIAL_BRIDGE)
static const bool SERIAL_BRIDGE = true; // master relays bridge lines to USB serial
#else
static const bool SERIAL_BRIDGE = false;
#endif

// ---- Globals ---------------------------------------------------------------
WebServer server(80);
WiFiUDP bridgeUdp;
bool pfReady = false;
String shortId;
uint8_t myMac[6] = {0};
uint8_t myId[3] = {0};
static const uint8_t BCAST[6] = {0xFF, 0xFF, 0xFF, 0xFF, 0xFF, 0xFF};
String otaMode = "off";

enum NetMode { MODE_COMMS = 0, MODE_MAINT = 1 };
enum MaintStatus : uint8_t {
  MAINT_STATUS_IDLE = 0,
  MAINT_STATUS_ACTIVE = 1,
  MAINT_STATUS_POWER_WARN = 2,
  MAINT_STATUS_START_FAILED = 3,
  MAINT_STATUS_TIMEOUT = 4,
  MAINT_STATUS_RESUMED = 5,
};
enum FieldPhase : uint8_t {
  FC_OFF = 0,
  FC_BOOT = 1,
  FC_CHARGE = 2,
  FC_WAIT_DARK = 3,
  FC_DRAWDOWN = 4,
  FC_PROTECT = 5,
};
enum FieldReason : uint8_t {
  FC_REASON_NONE = 0,
  FC_REASON_BOOT = 1,
  FC_REASON_SUPPLY = 2,
  FC_REASON_FULL = 3,
  FC_REASON_DARK = 4,
  FC_REASON_LOW = 5,
  FC_REASON_CRITICAL = 6,
  FC_REASON_SUNRISE = 7,
  FC_REASON_INTERRUPTED = 8,
};
enum FieldSessionStage : uint8_t {
  FIELD_SESSION_IDLE = 0,
  FIELD_SESSION_FULL = 1,
  FIELD_SESSION_DIM = 2,
  FIELD_SESSION_PROTECT = 3,
};
enum FieldMpptStatus : uint8_t {
  MPPT_STATUS_DISABLED = 0,
  MPPT_STATUS_SKIPPED = 1,
  MPPT_STATUS_RAN = 2,
  MPPT_STATUS_CLAMPED = 3,
  MPPT_STATUS_HELD_BEST = 4,
};
enum FieldMpptReason : uint8_t {
  MPPT_REASON_NONE = 0,
  MPPT_REASON_DISABLED = 1,
  MPPT_REASON_PHASE = 2,
  MPPT_REASON_WAKE_WINDOW = 3,
  MPPT_REASON_LOW_BATT = 4,
  MPPT_REASON_WEAK_SUN = 5,
  MPPT_REASON_TAPER = 6,
  MPPT_REASON_BQ_FAULT = 7,
  MPPT_REASON_MEASURED = 8,
  MPPT_REASON_CLAMP = 9,
  MPPT_REASON_MAINT = 10,
};
volatile NetMode gMode = MODE_COMMS;
volatile bool gResumePending = false; // /resume sets this; loop() does the real enterComms()
bool otaActive = false;
uint32_t maintEnteredMs = 0;
uint8_t gMaintStatus = MAINT_STATUS_IDLE;
uint32_t gLastMaintRefuseMs = 0;

#define NB_FIELD_RTC_MAGIC 0xC7
RTC_DATA_ATTR uint8_t rtcFieldMagic = 0;
RTC_DATA_ATTR uint8_t rtcFieldPhase = FC_OFF;
RTC_DATA_ATTR uint8_t rtcFieldReason = FC_REASON_NONE;
RTC_DATA_ATTR uint16_t rtcFieldCycle = 0;
RTC_DATA_ATTR uint32_t rtcFieldPhaseElapsedS = 0;
RTC_DATA_ATTR uint32_t rtcFieldChargeMas = 0;
RTC_DATA_ATTR uint32_t rtcFieldDischargeMas = 0;
RTC_DATA_ATTR uint16_t rtcFieldMinMv = 0;
RTC_DATA_ATTR uint16_t rtcFieldMaxMv = 0;
RTC_DATA_ATTR uint32_t rtcFieldChargeMws = 0;
RTC_DATA_ATTR uint32_t rtcFieldDischargeMws = 0;
RTC_DATA_ATTR uint16_t rtcFieldPeakPanelWx100 = 0;
RTC_DATA_ATTR uint16_t rtcFieldPeakChargeWx100 = 0;
RTC_DATA_ATTR uint16_t rtcFieldPeakDrawWx100 = 0;
RTC_DATA_ATTR uint16_t rtcFieldLowS = 0;
RTC_DATA_ATTR uint16_t rtcFieldDimS = 0;
RTC_DATA_ATTR uint16_t rtcFieldChargeS = 0;
RTC_DATA_ATTR uint16_t rtcFieldWaitS = 0;
RTC_DATA_ATTR uint16_t rtcFieldDrawS = 0;
RTC_DATA_ATTR uint16_t rtcFieldProtectS = 0;
RTC_DATA_ATTR uint16_t rtcFieldDuskS = 0;
RTC_DATA_ATTR uint8_t rtcFieldLoadDimmed = 0;
RTC_DATA_ATTR uint8_t rtcFieldProtectLatched = 0;
RTC_DATA_ATTR uint8_t rtcFieldMpptStatus = MPPT_STATUS_DISABLED;
RTC_DATA_ATTR uint8_t rtcFieldMpptReason = MPPT_REASON_DISABLED;
RTC_DATA_ATTR uint8_t rtcFieldMpptRuns = 0;
RTC_DATA_ATTR uint8_t rtcFieldMpptActiveV10 = NB_FIELD_MPPT_DEFAULT_V10;
RTC_DATA_ATTR uint8_t rtcFieldMpptBestV10 = NB_FIELD_MPPT_DEFAULT_V10;
RTC_DATA_ATTR uint8_t rtcFieldMpptLastV10 = 0;
RTC_DATA_ATTR uint16_t rtcFieldMpptP46Wx100 = 0;
RTC_DATA_ATTR uint16_t rtcFieldMpptP48Wx100 = 0;
RTC_DATA_ATTR uint16_t rtcFieldMpptP50Wx100 = 0;
// Capability, not sample validity: once this peer has produced a real TSL2591
// sample, keep using the qualified 5-minute dusk policy across deep-sleep wakes.
// A transient sensor read failure must not expand an already-qualified night to
// the 30-minute no-sensor fallback.
RTC_DATA_ATTR uint8_t rtcFieldLuxSensorSeen = 0;
uint32_t fieldLastIntegrateMs = 0;
uint32_t fieldLowSinceMs = 0;
uint32_t fieldDimSinceMs = 0;
uint32_t fieldDuskLastMs = 0;
bool gFieldSessionMarker = false;
bool gFieldInterruptedBoot = false;
bool gFieldInterruptedRetry = false;
bool gFieldInterruptedPark = false;
bool gFieldSessionStateLoaded = false;
uint8_t gFieldSessionStage = FIELD_SESSION_IDLE;
uint32_t gFieldLedEarliestOnMs = 0;

uint32_t txSeq = 0;        // our outgoing sequence number (monotonic)
uint32_t sendOk = 0, sendFail = 0; // ESP-NOW send-callback tallies
uint8_t gRateHz = IS_MASTER ? NB_FRAME_HZ : NB_HB_HZ; // runtime-settable (master '+'/'-')

// cached battery + supply (panel) telemetry (refreshed ~1 Hz; the ESP-NOW callback
// must not touch the SDK). Supply = the solar/USB input side, the missing half for
// battery/panel sizing -- supply_v x supply_ma = panel harvest; battery_ma = net.
float cbV = 0, cbMa = 0, cbMaRaw = 0;
int cbSoc = -1;
float csV = 0, csMa = 0; // supply (panel) voltage / current
bool csGood = false;     // charger considers the supply valid (checkSupplyGood)
uint16_t gBatteryCapacityMah = (uint16_t)RES_PF_BATTERY_CAPACITY_MAH;
uint16_t gChargeMa = (uint16_t)(RES_PF_MAX_CHARGE_MA + 0.5f);
float gMaintainV = (float)RES_PF_MAINTAIN_V;
bool gBenchConfigLoaded = false;
bool gChargingEnabled = false;
uint16_t gBqVindpmMv = 0xFFFF, gBqIchgMa = 0xFFFF, gBqVregMv = 0xFFFF;
uint8_t gBqReg16 = 0xFF, gBqReg18 = 0xFF, gBqStat0 = 0xFF, gBqStat1 = 0xFF;
uint8_t gBqFault0 = 0xFF, gBqFlag0 = 0xFF, gBqFlag1 = 0xFF, gBqFaultFlag0 = 0xFF;
uint8_t gBqPart = 0xFF;

// ---- env sensors (MPP sweep: light + panel temp, no host tether) ------------
Adafruit_TSL2591 gTsl(2591);          // lux/irradiance proxy (STEMMA, 0x29)
Adafruit_SHT31 gSht(&Wire1);          // panel-back temp + RH (STEMMA, 0x44)
bool gEnvTsl = false, gEnvSht = false, gEnvBtemp = false;
uint32_t gEnvLuxX10 = 0xFFFFFFFF;     // 0xFFFFFFFE = saturated (full sun > range)
uint16_t gEnvCh0 = 0, gEnvCh1 = 0;
int16_t gEnvPtempX10 = INT16_MIN;
uint8_t gEnvRh = 255;
int16_t gEnvBtempX10 = INT16_MIN;

#if NB_SENSOR_TRIAD
// Production downlight sensor-chain diagnostic. This is opt-in until its timing
// and energy cost are folded into production firmware. All devices share Wire1
// with the PowerFeather charger/gauge, so ADR 0028's 100 kHz ceiling applies.
Adafruit_MSA311 gMsa311;
Adafruit_BMP5xx gBmp581;
SparkFun_TMF882X gTmf8820;
struct tmf882x_msg_meas_results gTmfResults = {};
bool gMsa311Present = false, gBmp581Present = false, gTmf8820Present = false;
bool gMsa311ReadOk = false, gBmp581ReadOk = false, gTmf8820ReadOk = false;
float gMsaAxG = NAN, gMsaAyG = NAN, gMsaAzG = NAN;
float gBmpTempC = NAN, gBmpPressureHpa = NAN;
uint16_t gTmfClosestMm = 0;
uint16_t gTmfClosestConfidence = 0;
uint32_t gTmfReadCount = 0, gTmfReadErrors = 0;
#endif

// ---- onboard SEN0291/INA219 meters (panel + battery leads, on Wire1) --------
// Address convention (uses the two UNAMBIGUOUS DIP settings -- no need to know
// which switch is A0): both OFF = 0x40 = panel/VDC lead; both ON = 0x45 =
// battery lead. Override with -DNB_INA_PANEL_ADDR / -DNB_INA_BATT_ADDR.
// NOTE: 0x44 is reserved by the SHT31; 0x41 needs a single-switch guess.
#ifndef NB_INA_PANEL_ADDR
#define NB_INA_PANEL_ADDR 0x40
#endif
#ifndef NB_INA_BATT_ADDR
#define NB_INA_BATT_ADDR 0x45
#endif
#define NB_INA_RSHUNT_OHMS 0.01f
#define NB_INA_CONFIG 0x27FF // BRNG 32V, PG /1 (+-4A @ 10mR), 128-avg, continuous
bool gInaPanel = false, gInaBatt = false;
int16_t gInaPvMv = INT16_MIN, gInaPaMa = INT16_MIN, gInaBvMv = INT16_MIN, gInaBaMa = INT16_MIN;
// (the ina* helper FUNCTIONS live below the struct definitions -- defining any
// function this early moves the Arduino auto-prototype insertion point above
// the structs and breaks every later type reference)

Adafruit_NeoPixel drawdownPixels(
    NB_DRAWDOWN_PIXEL_COUNT, NB_DRAWDOWN_PIXEL_PIN,
#if NB_FIELD_LED_RGBW
    NEO_RGBW + NEO_KHZ800);
#else
    NEO_GRB + NEO_KHZ800);
#endif
bool gDrawdownPixelsBegun = false;
bool gDrawdownActive = false;
bool gFieldLedLoadOn = false;
bool gFieldLedLoadDimmedApplied = false;
bool gFieldSpiralGeometryReady = false;
uint8_t gFieldSpiralOrder[NB_DRAWDOWN_PIXEL_COUNT];
float gFieldPixelX[NB_DRAWDOWN_PIXEL_COUNT], gFieldPixelY[NB_DRAWDOWN_PIXEL_COUNT];
uint16_t gFieldSpiralPosition = 0;
uint32_t gFieldSpiralLastFrameMs = 0;
uint16_t gDrawdownBudgetMah = NB_DRAWDOWN_DEFAULT_MAH;
float gDrawdownMah = 0.0f;
uint32_t gDrawdownStartMs = 0;
uint32_t gDrawdownLastMs = 0;
uint32_t gDrawdownLastLogMs = 0;

uint32_t identifyUntil = 0; // millis deadline: blink the locate pattern instead of battery

// field scan-report state (set on a -DNB_SCAN_REPORT peer). gScanRunning is read
// unconditionally by the send loop (suppress ESP-NOW TX while the radio is hopping).
bool gScanRunning = false;
uint8_t gScanId = 0;
uint32_t gNextScanMs = 0;

// D7/VDC solenoid state is deliberately outside the LED rail state machine. VDC
// remains live in every phase, so the gate gets an esp_timer one-shot, an
// independent loop deadline, and explicit LOW calls before init/OTA/sleep.
#if defined(NB_SOLENOID_D7)
volatile bool gSolenoidGateOn = false;
volatile uint32_t gSolenoidLastEndMs = 0;
uint32_t gSolenoidFailsafeMs = 0;
uint32_t gSolenoidStrikes = 0;
uint32_t gSolenoidBlocked = 0;
uint32_t gSolenoidFailsafes = 0;
uint16_t gSolenoidLastPulseMs = 0;
esp_timer_handle_t gSolenoidPulseTimer = nullptr;
bool gSolenoidButtonRawReleased = true;
bool gSolenoidButtonStableReleased = true;
bool gSolenoidButtonWakePending = false;
uint32_t gSolenoidButtonChangedMs = 0;
bool gSolenoidRgbButtonPresent = false;
uint8_t gSolenoidRgbButtonAddr = 0;
bool gSolenoidRgbButtonRawPressed = false;
bool gSolenoidRgbButtonStablePressed = false;
uint8_t gSolenoidRgbButtonConsecutiveErrors = 0;
uint32_t gSolenoidRgbButtonChangedMs = 0;
uint32_t gSolenoidRgbButtonNextPollMs = 0;
uint32_t gSolenoidRgbButtonPresses = 0;
uint32_t gSolenoidRgbButtonErrors = 0;
uint8_t gSolenoidRgbButtonProbeAttempts = 0;
uint8_t gSolenoidRgbButtonAckMask = 0;
uint8_t gSolenoidRgbButtonPidAddr = 0;
uint16_t gSolenoidRgbButtonPid = 0;
bool gSolenoidNavPresent = false;
uint8_t gSolenoidNavAddr = 0;
bool gSolenoidNavRawReleased = true;
bool gSolenoidNavStableReleased = true;
uint8_t gSolenoidNavProbeAttempts = 0;
uint8_t gSolenoidNavAckMask = 0;
uint8_t gSolenoidNavLastInput = 0xFF;
uint8_t gSolenoidNavLastConfig = 0xFF;
uint8_t gSolenoidNavLastPolarity = 0xFF;
uint8_t gSolenoidNavConsecutiveErrors = 0;
uint32_t gSolenoidNavChangedMs = 0;
uint32_t gSolenoidNavNextPollMs = 0;
uint32_t gSolenoidNavPresses = 0;
uint32_t gSolenoidNavErrors = 0;
#endif

#if defined(NB_CAPBANK_WAVEFORM)
enum CapbankWaveState : uint8_t {
  CAPW_IDLE = 0,
  CAPW_ARMED = 1,
  CAPW_CAPTURING = 2,
  CAPW_READY = 3,
  CAPW_ERROR = 4,
};
volatile uint8_t gCapWaveState = CAPW_IDLE;
uint16_t gCapWavePulseMs = 0;
uint32_t gCapWaveArmAtMs = 0;
uint32_t gCapWaveId = 0;
uint16_t *gCapWaveVsnsMv = nullptr;
uint16_t *gCapWaveD7sMv = nullptr;
uint32_t gCapWaveVsnsCount = 0;
uint32_t gCapWaveD7sCount = 0;
uint32_t gCapWaveVsnsTriggerIndex = 0;
uint32_t gCapWaveD7sTriggerIndex = 0;
uint32_t gCapWaveCaptureUs = 0;
uint32_t gCapWaveTriggerUs = 0;
uint32_t gCapWaveRequestedConvHz = NB_CAPBANK_WAVEFORM_CONV_HZ;
bool gCapWaveOverflow = false;
String gCapWaveError;
#endif

// downlink (master SHOW_FRAME) tracking on peers
uint32_t masterLastSeq = 0;
uint32_t masterRx = 0, masterGaps = 0;
int8_t masterRssi = 0;
bool masterSeen = false;

// ---- ESP-NOW packet formats (packed, versioned, little-endian) -------------
#define NB_PROTO_VER 1
enum NbType : uint8_t {
  NB_HEARTBEAT = 1,   // peer -> all: state + telemetry summary
  NB_SHOWFRAME = 2,   // master -> all: show command
  NB_ENTER_MAINT = 3, // master -> all: ADR-0010 metadata, "enter maintenance"
  NB_RESUME = 4,      // master -> all: leave maintenance
  NB_SET_RATE = 5,    // master -> all: set heartbeat/frame rate (Hz) for sweeps
  NB_IDENTIFY = 6,    // master -> target (or all): blink the locate pattern to find a board
  NB_SCANAP = 7,      // field peer -> bridge: one scanned 2.4 GHz AP (coverage mapping)
  NB_SET_MAINTAIN = 8,// master -> all: set charger VINDPM/maintain V (panel MPP sweep / MPPT)
  NB_SET_CAPACITY = 9,// master -> all: persist battery capacity (mAh), reboot to apply
  NB_SET_CHARGE_MA = 10,// master -> all: persist/apply charger current cap (mA)
  NB_SLEEP_FOR = 11,  // master -> all: cut rails and timed deep-sleep (seconds)
  NB_DRAWDOWN = 12,   // master -> target: HEX drawdown load, then guarded timed sleep
  NB_TARGET_SLEEP_FOR = 13, // master -> target: cut rails and timed deep-sleep
  NB_TARGET_CAPACITY = 14,  // master -> target: persist capacity (mAh), reboot to apply
  NB_TARGET_CHARGE_MA = 15, // master -> target: persist/apply charger current cap (mA)
  NB_TARGET_ENTER_MAINT = 16, // master -> target: enter shared-WiFi maintenance/OTA
  NB_TARGET_SOLENOID = 17, // master -> target: one bounded D7 gate pulse (milliseconds)
};

struct __attribute__((packed)) NbHeader {
  uint8_t ver;
  uint8_t type;
  uint8_t src_id[3];
  uint32_t seq;
  uint32_t uptime_ms;
};
struct __attribute__((packed)) NbShowFrame {
  NbHeader h;
  uint16_t phase;
  uint8_t hue;
  uint8_t flags;
};
struct __attribute__((packed)) NbHeartbeat {
  NbHeader h;
  int16_t batt_mv;
  int16_t batt_ma;
  uint8_t soc_pct;
  uint8_t reset_reason; // (uint8_t)esp_reset_reason()
  uint8_t ca_state;
  uint8_t mode;
  uint16_t dl_pdr_x1000; // master-multicast PDR as seen by this peer
  int8_t dl_rssi;        // RSSI of master frames at this peer
  // --- APPEND-ONLY below (supply/panel side) ---------------------------------
  // New fields go at the END. Old parsers length-check (it.len >= sizeof) and
  // ignore the tail, so NB_PROTO_VER stays 1 (no flag-day; a pre-supply master
  // still reads the battery fields of a supply-capable peer). NEVER reorder/insert.
  int16_t supply_mv; // panel/USB input voltage (mV)
  int16_t supply_ma; // panel/USB input current INTO the board (mA)
  uint8_t supply_good; // charger considers the supply valid (0/1)
  // --- APPEND-ONLY tail 2 (env sensors on the peer's STEMMA bus, for the MPP
  // sweep: no-tether outdoor light + panel-temp logging). Same rules as above.
  uint32_t lux_x10;   // TSL2591 lux*10; 0xFFFFFFFF = no sensor, 0xFFFFFFFE = SATURATED
  uint16_t light_ch0; // TSL2591 raw full-spectrum count (GAIN_LOW / 100 ms, fixed)
  uint16_t light_ch1; // TSL2591 raw IR count
  int16_t ptemp_cx10; // SHT31 temp x10 C (tape it to the panel BACK); INT16_MIN = absent
  uint8_t prh_pct;    // SHT31 RH %; 255 = absent
  int16_t btemp_cx10; // battery NTC via charger TS x10 C (needs -DNB_BATT_NTC); INT16_MIN = absent
  // --- APPEND-ONLY tail 3 (SEN0291/INA219 meters on the peer's OWN Wire1:
  // ground-truth panel + battery power for the MPP sweep, no Metro tether.
  // The peer is awake during sweeps, so self-metering works; sleep/reset tests
  // still need the separate Metro monitor). INT16_MIN = channel absent.
  int16_t ina_pv_mv; // panel-lead INA bus mV (0x40 default)
  int16_t ina_pa_ma; // panel-lead INA current mA (wired so INTO the board = +)
  int16_t ina_bv_mv; // battery-lead INA bus mV (0x41 default)
  int16_t ina_ba_ma; // battery-lead INA current mA
  // --- APPEND-ONLY tail 4 (runtime bench config). Lets the bridge/dashboard
  // verify which NVS-backed gauge/charge settings this peer booted with.
  uint16_t cfg_cap_mah;
  uint16_t cfg_charge_ma;
  // --- APPEND-ONLY tail 5 (targeted battery drawdown helper). This is bench-only
  // telemetry for preparing a hungry LFP and estimating delivered capacity.
  uint16_t drawdown_mah_x10;
  uint16_t drawdown_budget_mah;
  uint8_t drawdown_active;
  // --- APPEND-ONLY tail 6 (dashboard/debug identity). Fixed-size to keep the
  // heartbeat binary and parser simple; NUL-terminated when sent by this firmware.
  char fw_rev[24];
  // --- APPEND-ONLY tail 7 (maintenance health). Lets the bridge see power warnings
  // and maintenance-start failures instead of inferring them from silence.
  uint8_t maint_status;
  // --- APPEND-ONLY tail 8 (field-cycle lifecycle). Production-ish solar day /
  // radio-night state, persisted through timer deep sleep in RTC memory.
  uint8_t field_phase;
  uint8_t field_reason;
  uint16_t field_cycle;
  uint16_t field_elapsed_s;
  uint16_t field_charge_mah;
  uint16_t field_discharge_mah;
  uint16_t field_min_mv;
  uint16_t field_max_mv;
  // --- APPEND-ONLY tail 9 (BQ25628E charger truth). Raw status/control bytes
  // avoid over-decoding in the firmware while still exposing CHG_EN/HIZ,
  // BATFET, VBUS/charge state, and fault flags to the dashboard/log.
  uint16_t bq_vindpm_mv; // programmed/effective VINDPM via SDK, 0xFFFF = unknown
  uint16_t bq_ichg_ma;   // charge-current limit via SDK, 0xFFFF = unknown
  uint16_t bq_vreg_mv;   // charge-voltage/CV limit via SDK, 0xFFFF = unknown
  uint8_t bq_reg16;      // Charger_Control_0: CHG_EN, EN_HIZ, watchdog
  uint8_t bq_reg18;      // Charger_Control_2: BATFET_CTRL, WVBUS
  uint8_t bq_stat0;      // Charger_Status_0
  uint8_t bq_stat1;      // Charger_Status_1: VBUS_STAT, CHG_STAT
  uint8_t bq_fault0;     // FAULT_Status_0
  uint8_t bq_flag0;      // Charger_Flag_0
  uint8_t bq_flag1;      // Charger_Flag_1
  uint8_t bq_fault_flag0;// FAULT_Flag_0
  uint8_t bq_part;       // Part_Information
  // --- APPEND-ONLY tail 10 (field-cycle v2 summary). Keep the heartbeat <=128B:
  // Wh x10, W x100, soft-low debounce seconds, and time in phase minutes.
  uint16_t field_charge_wh_x10;
  uint16_t field_discharge_wh_x10;
  uint16_t field_peak_panel_w_x100;
  uint16_t field_peak_charge_w_x100;
  uint16_t field_peak_draw_w_x100;
  uint8_t field_low_s;
  uint8_t field_charge_min;
  uint8_t field_wait_min;
  uint8_t field_draw_min;
  uint8_t field_protect_min;
  // --- APPEND-ONLY tail 11 (field-cycle safe VINDPM perturb). This intentionally
  // extends the heartbeat past 128 B; deploy the matching serial bridge before
  // deploying an MPPT peer. Powers are W x100 at fixed P105 candidate setpoints.
  uint8_t mppt_status;
  uint8_t mppt_reason;
  uint8_t mppt_runs;
  uint8_t mppt_active_v10;
  uint8_t mppt_best_v10;
  uint8_t mppt_last_v10;
  uint16_t mppt_p46_w_x100;
  uint16_t mppt_p48_w_x100;
  uint16_t mppt_p50_w_x100;
  // --- APPEND-ONLY tail 12 (field-cycle low-voltage latches).
  uint8_t field_load_dimmed;
  uint8_t field_protect_latched;
};
struct __attribute__((packed)) NbCmd { // ENTER_MAINT / RESUME / SET_RATE
  NbHeader h;
  uint8_t arg; // SET_RATE: Hz
};
struct __attribute__((packed)) NbSetU16 {
  NbHeader h;
  uint16_t value;
};
struct __attribute__((packed)) NbTargetU16 {
  NbHeader h;
  uint8_t target_id[3]; // 00:00:00 = all; otherwise node short ID
  uint16_t value;
};
struct __attribute__((packed)) NbTargetCmd {
  NbHeader h;
  uint8_t target_id[3]; // 00:00:00 = all; otherwise node short ID
  uint8_t arg;
};
struct __attribute__((packed)) NbIdentify { // locate a board (target 00:00:00 = all)
  NbHeader h;
  uint8_t target_id[3];
  uint8_t secs;
};
struct __attribute__((packed)) NbScanAp { // one AP from a field scan batch (45 bytes)
  NbHeader h;
  uint8_t scan_id;  // increments per scan batch (groups a batch on the host)
  uint8_t idx;      // rank within the batch (0 = strongest), sorted by RSSI desc
  uint8_t count;    // total APs found this scan (idx<count; >NB_SCAN_MAX => truncated)
  uint8_t bssid[6]; // which radio (e.g. which Eero node)
  int8_t ap_rssi;   // RSSI of this AP as seen from the FIELD board (the coverage metric)
  uint8_t channel;
  uint8_t enc;      // wifi_auth_mode_t
  char ssid[20];    // truncated SSID (identifies home network vs neighbors)
};

// ---- per-source receive tracking (PDR) -------------------------------------
struct NbPeerStat {
  bool used;
  uint8_t id[3];
  uint8_t last_type;
  uint32_t last_seq;
  uint32_t recv;
  uint32_t gaps;
  int8_t rssi;
  uint32_t last_heard_ms;
  uint32_t up; // peer's reported uptime_ms (for host reboot detection)
  // last heartbeat snapshot (for the bridge)
  int16_t batt_mv, batt_ma;
  uint8_t soc, rr, ca, pmode;
  uint16_t dl_pdr_x1000;
  int8_t dl_rssi;
  int16_t supply_mv, supply_ma; // panel side (0 if peer pre-dates supply telemetry)
  uint8_t supply_good;
  bool has_env; // peer sent the env-sensor tail
  uint32_t lux_x10;
  uint16_t light_ch0, light_ch1;
  int16_t ptemp_cx10;
  uint8_t prh_pct;
  int16_t btemp_cx10;
  bool has_ina; // peer sent the onboard-INA tail
  int16_t ina_pv_mv, ina_pa_ma, ina_bv_mv, ina_ba_ma;
  bool has_cfg; // peer sent the runtime-config tail
  uint16_t cfg_cap_mah, cfg_charge_ma;
  bool has_drawdown; // peer sent the targeted drawdown tail
  uint16_t drawdown_mah_x10, drawdown_budget_mah;
  uint8_t drawdown_active;
  bool has_fw;
  char fw_rev[24];
  bool has_maint_status;
  uint8_t maint_status;
  bool has_field_cycle;
  uint8_t field_phase, field_reason;
  uint16_t field_cycle, field_elapsed_s, field_charge_mah, field_discharge_mah;
  uint16_t field_min_mv, field_max_mv;
  bool has_bq;
  uint16_t bq_vindpm_mv, bq_ichg_ma, bq_vreg_mv;
  uint8_t bq_reg16, bq_reg18, bq_stat0, bq_stat1, bq_fault0, bq_flag0, bq_flag1;
  uint8_t bq_fault_flag0, bq_part;
  bool has_field_summary;
  uint16_t field_charge_wh_x10, field_discharge_wh_x10;
  uint16_t field_peak_panel_w_x100, field_peak_charge_w_x100, field_peak_draw_w_x100;
  uint8_t field_low_s, field_charge_min, field_wait_min, field_draw_min, field_protect_min;
  bool has_mppt;
  uint8_t mppt_status, mppt_reason, mppt_runs, mppt_active_v10, mppt_best_v10, mppt_last_v10;
  uint16_t mppt_p46_w_x100, mppt_p48_w_x100, mppt_p50_w_x100;
  bool has_field_latches;
  uint8_t field_load_dimmed, field_protect_latched;
};
NbPeerStat peers[NB_MAX_TRACKED];

// ---- optional D7/VDC solenoid ---------------------------------------------
// Only a targeted command or a deliberate PowerFeather USER-button press can
// energize the gate. Every exit path returns it LOW. The button is also an
// active-LOW deep-sleep wake source so the local control remains useful during
// five-minute field-cycle sleeps. Physical release before re-sleep is the only
// re-arm condition; no retained debounce state can get stuck across boots.
void solenoidPreInit() {
#if defined(NB_SOLENOID_D7)
  pinMode(NB_SOLENOID_PIN, OUTPUT);
  digitalWrite(NB_SOLENOID_PIN, LOW);
#endif
}

#if defined(NB_SOLENOID_D7)
void solenoidPulseEnd(void *) { // esp_timer task context, not an ISR
  digitalWrite(NB_SOLENOID_PIN, LOW);
  gSolenoidGateOn = false;
  gSolenoidLastEndMs = millis();
}

void solenoidInit() {
  solenoidPreInit();
  gSolenoidLastEndMs = millis() - NB_SOLENOID_REST_MS;
  // EXT0 owns the RTC pad through deep sleep. Return it to normal GPIO before
  // sampling the active-LOW USER button and enabling its internal pull-up.
  rtc_gpio_deinit((gpio_num_t)NB_SOLENOID_BUTTON_PIN);
  pinMode(NB_SOLENOID_BUTTON_PIN, INPUT_PULLUP);
  delay(1);
  bool released = digitalRead(NB_SOLENOID_BUTTON_PIN) == HIGH;
  gSolenoidButtonWakePending =
      esp_sleep_get_wakeup_cause() == ESP_SLEEP_WAKEUP_EXT0;
  // EXT0 itself proves a deliberate LOW. Start latched as pressed even if the
  // user released before setup sampled GPIO0, so contact bounce cannot create a
  // second active-mode falling edge during the same press.
  gSolenoidButtonRawReleased = gSolenoidButtonWakePending ? false : released;
  gSolenoidButtonStableReleased = gSolenoidButtonWakePending ? false : released;
  gSolenoidButtonChangedMs = millis();

  const esp_timer_create_args_t timerArgs = {
      .callback = &solenoidPulseEnd,
      .arg = nullptr,
      .dispatch_method = ESP_TIMER_TASK,
      .name = "nb_solenoid",
      .skip_unhandled_events = true,
  };
  esp_err_t err = esp_timer_create(&timerArgs, &gSolenoidPulseTimer);
  if (err != ESP_OK) {
    gSolenoidPulseTimer = nullptr;
    Serial.printf("solenoid timer init failed: %s\n", esp_err_to_name(err));
  } else {
    Serial.printf("solenoid armed: PowerFeather D7/GPIO%d, VDC tap, pulse %u..%u ms\n",
                  NB_SOLENOID_PIN, NB_SOLENOID_MIN_MS, NB_SOLENOID_MAX_MS);
    Serial.printf("solenoid local trigger: USER/GPIO%d, %ums debounce, deep-sleep wake\n",
                  NB_SOLENOID_BUTTON_PIN, NB_SOLENOID_BUTTON_DEBOUNCE_MS);
  }
}

void solenoidStop(const char *why) {
  if (gSolenoidPulseTimer) esp_timer_stop(gSolenoidPulseTimer);
  digitalWrite(NB_SOLENOID_PIN, LOW);
  if (gSolenoidGateOn) {
    gSolenoidGateOn = false;
    gSolenoidLastEndMs = millis();
    Serial.printf("solenoid forced LOW (%s)\n", why);
  }
}

bool solenoidStrike(uint16_t pulseMs, const char *why) {
  pulseMs = constrain(pulseMs, (uint16_t)NB_SOLENOID_MIN_MS,
                      (uint16_t)NB_SOLENOID_MAX_MS);
  uint32_t now = millis();
  if (!gSolenoidPulseTimer || gSolenoidGateOn ||
      now - gSolenoidLastEndMs < NB_SOLENOID_REST_MS) {
    gSolenoidBlocked++;
    return false;
  }

  gSolenoidFailsafeMs = now + pulseMs + 50;
  gSolenoidGateOn = true;
  digitalWrite(NB_SOLENOID_PIN, HIGH);
  esp_err_t err = esp_timer_start_once(gSolenoidPulseTimer,
                                       (uint64_t)pulseMs * 1000ULL);
  if (err != ESP_OK) {
    digitalWrite(NB_SOLENOID_PIN, LOW);
    gSolenoidGateOn = false;
    gSolenoidLastEndMs = millis();
    gSolenoidFailsafes++;
    Serial.printf("solenoid timer start failed: %s\n", esp_err_to_name(err));
    return false;
  }

  gSolenoidStrikes++;
  gSolenoidLastPulseMs = pulseMs;
  Serial.printf("solenoid strike #%lu: %ums (%s)\n",
                (unsigned long)gSolenoidStrikes, (unsigned)pulseMs, why);
  return true;
}

#if defined(NB_CAPBANK_PROBE)
float capbankVoltsFromSenseMv(uint32_t senseMv) {
  return (senseMv / 1000.0f) *
         ((NB_CAPBANK_VSNS_TOP_OHM + NB_CAPBANK_VSNS_BOTTOM_OHM) /
          NB_CAPBANK_VSNS_BOTTOM_OHM);
}

uint32_t capbankAverageMv(uint8_t pin, uint8_t count) {
  uint32_t total = 0;
  for (uint8_t i = 0; i < count; ++i) {
    total += analogReadMilliVolts(pin);
    delayMicroseconds(150);
  }
  return count ? total / count : 0;
}

void capbankProbeInit() {
  pinMode(NB_CAPBANK_VSNS_PIN, INPUT);
  pinMode(NB_CAPBANK_D7S_PIN, INPUT);
  analogSetPinAttenuation(NB_CAPBANK_VSNS_PIN, ADC_11db);
  analogSetPinAttenuation(NB_CAPBANK_D7S_PIN, ADC_11db);
  Serial.printf("capbank probe: VSNS=GPIO%d D7S=GPIO%d divider=%.4fx\n",
                NB_CAPBANK_VSNS_PIN, NB_CAPBANK_D7S_PIN,
                (NB_CAPBANK_VSNS_TOP_OHM + NB_CAPBANK_VSNS_BOTTOM_OHM) /
                    NB_CAPBANK_VSNS_BOTTOM_OHM);
}

void capbankReportIdle() {
  uint32_t senseMv = capbankAverageMv(NB_CAPBANK_VSNS_PIN, 32);
  uint32_t gateMv = capbankAverageMv(NB_CAPBANK_D7S_PIN, 16);
  Serial.printf("{\"capbank_idle\":1,\"vsns_pin\":%d,\"d7s_pin\":%d,"
                "\"sense_mv\":%lu,\"bank_v\":%.3f,\"gate_mv\":%lu,"
                "\"gate_on\":%s}\n",
                NB_CAPBANK_VSNS_PIN, NB_CAPBANK_D7S_PIN,
                (unsigned long)senseMv, capbankVoltsFromSenseMv(senseMv),
                (unsigned long)gateMv, gSolenoidGateOn ? "true" : "false");
}

bool capbankProbeStrike(uint16_t pulseMs) {
  uint32_t preSenseMv = capbankAverageMv(NB_CAPBANK_VSNS_PIN, 32);
  uint32_t gateIdleMv = capbankAverageMv(NB_CAPBANK_D7S_PIN, 16);
  if (!solenoidStrike(pulseMs, "capbank probe")) {
    Serial.printf("{\"capbank_probe\":1,\"ok\":false,\"pulse_ms\":%u,"
                  "\"reason\":\"strike_blocked\",\"bank_v\":%.3f,"
                  "\"gate_mv\":%lu}\n",
                  (unsigned)pulseMs, capbankVoltsFromSenseMv(preSenseMv),
                  (unsigned long)gateIdleMv);
    return false;
  }

  uint32_t minSenseMv = preSenseMv;
  uint32_t gatePeakMv = gateIdleMv;
  uint32_t post20Mv = 0, post100Mv = 0, post250Mv = 0;
  bool got20 = false, got100 = false, got250 = false;
  uint32_t samples = 0;
  const uint32_t startUs = micros();
  const uint32_t endUs =
      (uint32_t)(pulseMs + NB_CAPBANK_PROBE_RECOVERY_MS) * 1000UL;
  while ((uint32_t)(micros() - startUs) < endUs) {
    uint32_t senseMv = analogReadMilliVolts(NB_CAPBANK_VSNS_PIN);
    uint32_t gateMv = analogReadMilliVolts(NB_CAPBANK_D7S_PIN);
    if (senseMv < minSenseMv) minSenseMv = senseMv;
    if (gateMv > gatePeakMv) gatePeakMv = gateMv;
    uint32_t elapsedMs = (uint32_t)(micros() - startUs) / 1000UL;
    if (!got20 && elapsedMs >= (uint32_t)pulseMs + 20U) {
      post20Mv = senseMv;
      got20 = true;
    }
    if (!got100 && elapsedMs >= (uint32_t)pulseMs + 100U) {
      post100Mv = senseMv;
      got100 = true;
    }
    if (!got250 &&
        elapsedMs >= (uint32_t)pulseMs + NB_CAPBANK_PROBE_RECOVERY_MS - 1U) {
      post250Mv = senseMv;
      got250 = true;
    }
    ++samples;
    delayMicroseconds(100);
  }
  if (!got20) post20Mv = analogReadMilliVolts(NB_CAPBANK_VSNS_PIN);
  if (!got100) post100Mv = post20Mv;
  if (!got250) post250Mv = analogReadMilliVolts(NB_CAPBANK_VSNS_PIN);

  float preV = capbankVoltsFromSenseMv(preSenseMv);
  float minV = capbankVoltsFromSenseMv(minSenseMv);
  Serial.printf("{\"capbank_probe\":1,\"ok\":true,\"pulse_ms\":%u,"
                "\"vsns_pin\":%d,\"d7s_pin\":%d,\"pre_v\":%.3f,"
                "\"min_v\":%.3f,\"drop_v\":%.3f,\"post20_v\":%.3f,"
                "\"post100_v\":%.3f,\"post250_v\":%.3f,"
                "\"gate_idle_mv\":%lu,\"gate_peak_mv\":%lu,"
                "\"samples\":%lu,\"failsafes\":%lu}\n",
                (unsigned)pulseMs, NB_CAPBANK_VSNS_PIN, NB_CAPBANK_D7S_PIN,
                preV, minV, preV - minV, capbankVoltsFromSenseMv(post20Mv),
                capbankVoltsFromSenseMv(post100Mv), capbankVoltsFromSenseMv(post250Mv),
                (unsigned long)gateIdleMv, (unsigned long)gatePeakMv,
                (unsigned long)samples, (unsigned long)gSolenoidFailsafes);
  return true;
}
#else
void capbankProbeInit() {}
void capbankReportIdle() { Serial.println("capbank probe not compiled"); }
bool capbankProbeStrike(uint16_t) {
  Serial.println("capbank probe not compiled");
  return false;
}
#endif

#if defined(NB_CAPBANK_WAVEFORM)
const char *capbankWaveStateName() {
  switch (gCapWaveState) {
    case CAPW_ARMED: return "armed";
    case CAPW_CAPTURING: return "capturing";
    case CAPW_READY: return "ready";
    case CAPW_ERROR: return "error";
    default: return "idle";
  }
}

bool capbankWaveEnsureBuffers() {
  if (gCapWaveVsnsMv && gCapWaveD7sMv) return true;
  free(gCapWaveVsnsMv);
  free(gCapWaveD7sMv);
  const size_t bytes = (size_t)NB_CAPBANK_WAVEFORM_MAX_SAMPLES * sizeof(uint16_t);
  gCapWaveVsnsMv = (uint16_t *)heap_caps_malloc(bytes, MALLOC_CAP_8BIT);
  gCapWaveD7sMv = (uint16_t *)heap_caps_malloc(bytes, MALLOC_CAP_8BIT);
  if (!gCapWaveVsnsMv || !gCapWaveD7sMv) {
    free(gCapWaveVsnsMv);
    free(gCapWaveD7sMv);
    gCapWaveVsnsMv = nullptr;
    gCapWaveD7sMv = nullptr;
    gCapWaveError = "sample buffer allocation failed";
    return false;
  }
  return true;
}

bool capbankWaveCapture(uint16_t pulseMs) {
  gCapWaveState = CAPW_CAPTURING;
  gCapWaveError = "";
  gCapWaveVsnsCount = 0;
  gCapWaveD7sCount = 0;
  gCapWaveVsnsTriggerIndex = 0;
  gCapWaveD7sTriggerIndex = 0;
  gCapWaveCaptureUs = 0;
  gCapWaveTriggerUs = 0;
  gCapWaveOverflow = false;
  if (!capbankWaveEnsureBuffers()) {
    gCapWaveState = CAPW_ERROR;
    return false;
  }

  adc_continuous_handle_t adc = nullptr;
  adc_cali_handle_t cal = nullptr;
  bool adcStarted = false;
  bool pinsDetached = false;
  bool ok = false;
  do {
    // capbankProbeInit() attached Arduino's ADC1 one-shot driver. Detaching both
    // pins releases that handle so the DMA/continuous driver can own ADC1.
    if (!perimanClearPinBus(NB_CAPBANK_VSNS_PIN) ||
        !perimanClearPinBus(NB_CAPBANK_D7S_PIN)) {
      gCapWaveError = "could not release ADC one-shot pins";
      break;
    }
    pinsDetached = true;

    adc_unit_t vsnsUnit = ADC_UNIT_1, d7sUnit = ADC_UNIT_1;
    adc_channel_t vsnsChannel = ADC_CHANNEL_0, d7sChannel = ADC_CHANNEL_0;
    esp_err_t err = adc_continuous_io_to_channel(
        NB_CAPBANK_VSNS_PIN, &vsnsUnit, &vsnsChannel);
    if (err != ESP_OK || vsnsUnit != ADC_UNIT_1) {
      gCapWaveError = "VSNS is not on ADC1";
      break;
    }
    err = adc_continuous_io_to_channel(
        NB_CAPBANK_D7S_PIN, &d7sUnit, &d7sChannel);
    if (err != ESP_OK || d7sUnit != ADC_UNIT_1) {
      gCapWaveError = "D7S is not on ADC1";
      break;
    }

    adc_continuous_handle_cfg_t handleCfg = {};
    handleCfg.max_store_buf_size = 32768;
    handleCfg.conv_frame_size = 256;
    handleCfg.flags.flush_pool = true;
    err = adc_continuous_new_handle(&handleCfg, &adc);
    if (err != ESP_OK) {
      gCapWaveError = String("ADC handle: ") + esp_err_to_name(err);
      break;
    }

    adc_digi_pattern_config_t pattern[2] = {};
    pattern[0].atten = ADC_ATTEN_DB_12;
    pattern[0].channel = vsnsChannel;
    pattern[0].unit = ADC_UNIT_1;
    pattern[0].bit_width = ADC_BITWIDTH_12;
    pattern[1].atten = ADC_ATTEN_DB_12;
    pattern[1].channel = d7sChannel;
    pattern[1].unit = ADC_UNIT_1;
    pattern[1].bit_width = ADC_BITWIDTH_12;
    adc_continuous_config_t adcCfg = {};
    adcCfg.pattern_num = 2;
    adcCfg.adc_pattern = pattern;
    adcCfg.sample_freq_hz = NB_CAPBANK_WAVEFORM_CONV_HZ;
    adcCfg.conv_mode = ADC_CONV_SINGLE_UNIT_1;
    adcCfg.format = ADC_DIGI_OUTPUT_FORMAT_TYPE2;
    err = adc_continuous_config(adc, &adcCfg);
    if (err != ESP_OK) {
      gCapWaveError = String("ADC config: ") + esp_err_to_name(err);
      break;
    }

    adc_cali_curve_fitting_config_t calCfg = {};
    calCfg.unit_id = ADC_UNIT_1;
    calCfg.atten = ADC_ATTEN_DB_12;
    calCfg.bitwidth = ADC_BITWIDTH_12;
    err = adc_cali_create_scheme_curve_fitting(&calCfg, &cal);
    if (err != ESP_OK) {
      gCapWaveError = String("ADC calibration: ") + esp_err_to_name(err);
      break;
    }

    err = adc_continuous_start(adc);
    if (err != ESP_OK) {
      gCapWaveError = String("ADC start: ") + esp_err_to_name(err);
      break;
    }
    adcStarted = true;
    const uint64_t captureStartUs = esp_timer_get_time();
    uint64_t triggerAtUs = 0;
    bool triggered = false;
    uint8_t dma[512];

    while (true) {
      esp_task_wdt_reset();
      uint32_t bytesRead = 0;
      err = adc_continuous_read(adc, dma, sizeof(dma), &bytesRead, 20);
      if (err != ESP_OK && err != ESP_ERR_TIMEOUT) {
        gCapWaveError = String("ADC read: ") + esp_err_to_name(err);
        break;
      }
      for (uint32_t offset = 0;
           offset + SOC_ADC_DIGI_RESULT_BYTES <= bytesRead;
           offset += SOC_ADC_DIGI_RESULT_BYTES) {
        const adc_digi_output_data_t *sample =
            (const adc_digi_output_data_t *)&dma[offset];
        if (sample->type2.unit != 0) continue;
        const uint16_t raw = sample->type2.data;
        if (sample->type2.channel == (uint32_t)vsnsChannel) {
          if (gCapWaveVsnsCount < NB_CAPBANK_WAVEFORM_MAX_SAMPLES)
            gCapWaveVsnsMv[gCapWaveVsnsCount++] = raw;
          else gCapWaveOverflow = true;
        } else if (sample->type2.channel == (uint32_t)d7sChannel) {
          if (gCapWaveD7sCount < NB_CAPBANK_WAVEFORM_MAX_SAMPLES)
            gCapWaveD7sMv[gCapWaveD7sCount++] = raw;
          else gCapWaveOverflow = true;
        }
      }

      const uint64_t nowUs = esp_timer_get_time();
      if (!triggered && nowUs - captureStartUs >=
                            (uint64_t)NB_CAPBANK_WAVEFORM_PRE_MS * 1000ULL) {
        gCapWaveVsnsTriggerIndex = gCapWaveVsnsCount;
        gCapWaveD7sTriggerIndex = gCapWaveD7sCount;
        triggerAtUs = esp_timer_get_time();
        gCapWaveTriggerUs = (uint32_t)(triggerAtUs - captureStartUs);
        if (!solenoidStrike(pulseMs, "capbank DMA waveform")) {
          gCapWaveError = "strike blocked";
          break;
        }
        triggered = true;
        // nowUs was sampled immediately before triggerAtUs. Do not subtract the
        // newer trigger timestamp from that older unsigned value; collect the
        // next DMA frame before evaluating the post-trigger deadline.
        continue;
      }
      if (triggered && nowUs - triggerAtUs >=
                           (uint64_t)(pulseMs + NB_CAPBANK_WAVEFORM_POST_MS) * 1000ULL) {
        gCapWaveCaptureUs = (uint32_t)(nowUs - captureStartUs);
        ok = true;
        break;
      }
      if (nowUs - captureStartUs >
          (uint64_t)(NB_CAPBANK_WAVEFORM_PRE_MS + pulseMs +
                     NB_CAPBANK_WAVEFORM_POST_MS + 1000U) * 1000ULL) {
        gCapWaveError = "capture timeout";
        break;
      }
    }

    solenoidStop("waveform complete");
    if (!ok) break;

    // DMA stores raw codes. Convert after the timing-critical capture so the
    // eFuse-calibrated millivolt conversion cannot perturb sample cadence.
    for (uint32_t i = 0; i < gCapWaveVsnsCount; ++i) {
      int mv = 0;
      if (adc_cali_raw_to_voltage(cal, gCapWaveVsnsMv[i], &mv) != ESP_OK) {
        gCapWaveError = "VSNS calibration failed";
        ok = false;
        break;
      }
      gCapWaveVsnsMv[i] = (uint16_t)constrain(mv, 0, 65535);
    }
    if (!ok) break;
    for (uint32_t i = 0; i < gCapWaveD7sCount; ++i) {
      int mv = 0;
      if (adc_cali_raw_to_voltage(cal, gCapWaveD7sMv[i], &mv) != ESP_OK) {
        gCapWaveError = "D7S calibration failed";
        ok = false;
        break;
      }
      gCapWaveD7sMv[i] = (uint16_t)constrain(mv, 0, 65535);
    }
  } while (false);

  if (adcStarted) adc_continuous_stop(adc);
  if (adc) adc_continuous_deinit(adc);
  if (cal) adc_cali_delete_scheme_curve_fitting(cal);
  if (pinsDetached) capbankProbeInit();
  if (ok) {
    ++gCapWaveId;
    gCapWaveState = CAPW_READY;
    Serial.printf("capbank waveform #%lu ready: %ums, VSNS=%lu D7S=%lu, %.1f/%.1f sps\n",
                  (unsigned long)gCapWaveId, (unsigned)pulseMs,
                  (unsigned long)gCapWaveVsnsCount,
                  (unsigned long)gCapWaveD7sCount,
                  gCapWaveCaptureUs ?
                      (double)gCapWaveVsnsCount * 1000000.0 / gCapWaveCaptureUs : 0.0,
                  gCapWaveCaptureUs ?
                      (double)gCapWaveD7sCount * 1000000.0 / gCapWaveCaptureUs : 0.0);
  } else {
    solenoidStop("waveform error");
    gCapWaveState = CAPW_ERROR;
    Serial.printf("capbank waveform error: %s\n", gCapWaveError.c_str());
  }
  return ok;
}

String capbankWaveStatusJson() {
  float vsnsHz = gCapWaveCaptureUs ?
      (float)gCapWaveVsnsCount * 1000000.0f / gCapWaveCaptureUs : 0.0f;
  float d7sHz = gCapWaveCaptureUs ?
      (float)gCapWaveD7sCount * 1000000.0f / gCapWaveCaptureUs : 0.0f;
  String j;
  j.reserve(520);
  j = "{\"feature\":\"capbank_waveform\",\"fixture_id\":\"" + shortId + "\"";
  j += ",\"fw\":\"" NET_BENCH_VERSION "\"";
  j += ",\"state\":\"" + String(capbankWaveStateName()) + "\"";
  j += ",\"capture_id\":" + String((unsigned long)gCapWaveId);
  j += ",\"pulse_ms\":" + String(gCapWavePulseMs);
  j += ",\"requested_conversion_hz\":" + String(gCapWaveRequestedConvHz);
  j += ",\"vsns_hz\":" + String(vsnsHz, 2);
  j += ",\"d7s_hz\":" + String(d7sHz, 2);
  j += ",\"vsns_count\":" + String((unsigned long)gCapWaveVsnsCount);
  j += ",\"d7s_count\":" + String((unsigned long)gCapWaveD7sCount);
  j += ",\"capture_us\":" + String((unsigned long)gCapWaveCaptureUs);
  j += ",\"trigger_us\":" + String((unsigned long)gCapWaveTriggerUs);
  j += ",\"pre_ms\":" + String(NB_CAPBANK_WAVEFORM_PRE_MS);
  j += ",\"post_ms\":" + String(NB_CAPBANK_WAVEFORM_POST_MS);
  j += ",\"overflow\":" + String(gCapWaveOverflow ? "true" : "false");
  j += ",\"radio_quiet\":true";
  j += ",\"error\":\"" + gCapWaveError + "\"}";
  return j;
}

void capbankWaveSendCsv() {
  if (gCapWaveState != CAPW_READY || !gCapWaveVsnsCount || !gCapWaveD7sCount) {
    server.send(409, "application/json", capbankWaveStatusJson());
    return;
  }
  const uint32_t n = min(gCapWaveVsnsCount, gCapWaveD7sCount);
  const float vsnsHz = (float)gCapWaveVsnsCount * 1000000.0f / gCapWaveCaptureUs;
  const float divider =
      (NB_CAPBANK_VSNS_TOP_OHM + NB_CAPBANK_VSNS_BOTTOM_OHM) /
      NB_CAPBANK_VSNS_BOTTOM_OHM;
  server.sendHeader("Content-Disposition",
                    "attachment; filename=capbank-waveform-" +
                    String((unsigned long)gCapWaveId) + ".csv");
  server.setContentLength(CONTENT_LENGTH_UNKNOWN);
  server.send(200, "text/csv", "");
  String chunk;
  chunk.reserve(3072);
  chunk = "# fixture_id," + shortId + "\n";
  chunk += "# firmware," NET_BENCH_VERSION "\n";
  chunk += "# capture_id," + String((unsigned long)gCapWaveId) + "\n";
  chunk += "# pulse_ms," + String(gCapWavePulseMs) + "\n";
  chunk += "# requested_conversion_hz," + String(gCapWaveRequestedConvHz) + "\n";
  chunk += "# vsns_sample_hz," + String(vsnsHz, 3) + "\n";
  chunk += "# d7s_sample_hz," +
           String((float)gCapWaveD7sCount * 1000000.0f / gCapWaveCaptureUs, 3) + "\n";
  chunk += "# radio_quiet,true\n";
  chunk += "t_ms,bank_v,vsns_mv,d7s_mv,gate_command\n";
  server.sendContent(chunk);
  chunk = "";
  for (uint32_t i = 0; i < n; ++i) {
    const float tMs = ((int64_t)i - (int64_t)gCapWaveVsnsTriggerIndex) *
                      1000.0f / vsnsHz;
    const float bankV = (gCapWaveVsnsMv[i] / 1000.0f) * divider;
    chunk += String(tMs, 4) + "," + String(bankV, 4) + "," +
             String(gCapWaveVsnsMv[i]) + "," + String(gCapWaveD7sMv[i]) + "," +
             String((tMs >= 0.0f && tMs < gCapWavePulseMs) ? 1 : 0) + "\n";
    if ((i % 48U) == 47U) {
      esp_task_wdt_reset();
      server.sendContent(chunk);
      chunk = "";
    }
  }
  if (chunk.length()) server.sendContent(chunk);
  server.sendContent("");
}

void capbankWaveConfigureRoutes() {
  server.on("/capbank/waveform", HTTP_GET, []() {
    server.send(200, "application/json", capbankWaveStatusJson());
  });
  server.on("/capbank/waveform.csv", HTTP_GET, []() { capbankWaveSendCsv(); });
  server.on("/capbank/arm", HTTP_GET, []() {
    if (!server.hasArg("ms")) {
      server.send(400, "text/plain", "use /capbank/arm?ms=5..50\n");
      return;
    }
    const int pulseMs = server.arg("ms").toInt();
    if (pulseMs < NB_SOLENOID_MIN_MS ||
        pulseMs > NB_CAPBANK_WAVEFORM_MAX_PULSE_MS) {
      server.send(400, "text/plain", "pulse outside bench-qualified 5..50 ms\n");
      return;
    }
    if (gCapWaveState == CAPW_ARMED || gCapWaveState == CAPW_CAPTURING) {
      server.send(409, "application/json", capbankWaveStatusJson());
      return;
    }
    gCapWavePulseMs = (uint16_t)pulseMs;
    gCapWaveArmAtMs = millis() + 350;
    gCapWaveState = CAPW_ARMED;
    gCapWaveError = "";
    server.send(202, "application/json", capbankWaveStatusJson());
  });
}
#else
void capbankWaveConfigureRoutes() {}
#endif

void solenoidButtonHandleWake() {
  if (!gSolenoidButtonWakePending) return;
  gSolenoidButtonWakePending = false;
  solenoidStrike(NB_SOLENOID_DEFAULT_MS, "user button wake");
}

void solenoidButtonTick() {
  bool released = digitalRead(NB_SOLENOID_BUTTON_PIN) == HIGH;
  uint32_t now = millis();
  if (released != gSolenoidButtonRawReleased) {
    gSolenoidButtonRawReleased = released;
    gSolenoidButtonChangedMs = now;
  }
  if (released == gSolenoidButtonStableReleased ||
      now - gSolenoidButtonChangedMs < NB_SOLENOID_BUTTON_DEBOUNCE_MS) return;

  gSolenoidButtonStableReleased = released;
  if (!released) {
    if (gMode == MODE_COMMS)
      solenoidStrike(NB_SOLENOID_DEFAULT_MS, "user button");
    else
      Serial.println("solenoid USER button ignored during maintenance");
  }
}

// DFR0991 Gravity I2C RGB Button. Its eight DIP-selectable addresses are
// 0x23..0x2A (default 0x2A); PID 0x43DF prevents an unrelated device at one of
// those addresses from becoming a solenoid trigger. This is intentionally an
// awake-only trigger: the four-wire I2C lead does not expose a wake/interrupt
// signal, and the field-cycle code cuts VSQT before deep sleep.
bool solenoidRgbButtonRead(uint8_t addr, uint8_t reg, uint8_t *data, size_t len) {
  // ADR 0028: never raise a bus shared with the PowerFeather charger/gauge over
  // 100 kHz. Reassert it here in case another peripheral changed the clock.
  Wire1.setClock(100000);
  Wire1.beginTransmission(addr);
  Wire1.write(reg);
  if (Wire1.endTransmission() != 0) return false;
  if (Wire1.requestFrom((int)addr, (int)len) != len) return false;
  for (size_t i = 0; i < len; ++i) data[i] = Wire1.read();
  return true;
}

bool solenoidRgbButtonPing(uint8_t addr) {
  Wire1.setClock(100000);
  Wire1.beginTransmission(addr);
  return Wire1.endTransmission() == 0;
}

bool solenoidRgbButtonProbe() {
  constexpr uint8_t kAddrMin = 0x23;
  constexpr uint8_t kAddrMax = 0x2A;
  constexpr uint16_t kPid = 0x43DF;
  constexpr uint8_t kPidMsbReg = 0x09;
  constexpr uint8_t kButtonReg = 0x04;

  gSolenoidRgbButtonProbeAttempts++;
  gSolenoidRgbButtonPresent = false;
  gSolenoidRgbButtonAddr = 0;
  gSolenoidRgbButtonConsecutiveErrors = 0;
  gSolenoidRgbButtonAckMask = 0;
  gSolenoidRgbButtonPidAddr = 0;
  gSolenoidRgbButtonPid = 0;
  for (uint8_t addr = kAddrMin; addr <= kAddrMax; ++addr) {
    if (!solenoidRgbButtonPing(addr)) continue;
    gSolenoidRgbButtonAckMask |= (uint8_t)(1U << (addr - kAddrMin));

    uint8_t pidBytes[2];
    if (!solenoidRgbButtonRead(addr, kPidMsbReg, pidBytes, sizeof(pidBytes))) continue;
    uint16_t pid = ((uint16_t)pidBytes[0] << 8) | pidBytes[1];
    gSolenoidRgbButtonPidAddr = addr;
    gSolenoidRgbButtonPid = pid;
    if (pid != kPid) continue;

    uint8_t state = 0;
    if (!solenoidRgbButtonRead(addr, kButtonReg, &state, 1)) continue;
    gSolenoidRgbButtonPresent = true;
    gSolenoidRgbButtonAddr = addr;
    gSolenoidRgbButtonRawPressed = state != 0;
    gSolenoidRgbButtonStablePressed = state != 0;
    gSolenoidRgbButtonChangedMs = millis();
    gSolenoidRgbButtonNextPollMs = millis() + NB_SOLENOID_RGB_BUTTON_POLL_MS;
    Serial.printf("solenoid local trigger: DFR0991 at 0x%02X, %ums poll/debounce\n",
                  addr, NB_SOLENOID_RGB_BUTTON_POLL_MS);
    return true;
  }
  return false;
}

void solenoidRgbButtonInit() {
  gSolenoidRgbButtonProbeAttempts = 0;
  if (solenoidRgbButtonProbe()) return;
  gSolenoidRgbButtonNextPollMs = millis() + NB_SOLENOID_RGB_BUTTON_PROBE_MS;
}

void solenoidRgbButtonTick() {
  constexpr uint8_t kButtonReg = 0x04;
  uint32_t now = millis();
  if (!gSolenoidRgbButtonPresent) {
    if (gSolenoidRgbButtonProbeAttempts >= NB_SOLENOID_RGB_BUTTON_PROBE_ATTEMPTS ||
        (int32_t)(now - gSolenoidRgbButtonNextPollMs) < 0) return;
    if (!solenoidRgbButtonProbe()) {
      gSolenoidRgbButtonNextPollMs = now + NB_SOLENOID_RGB_BUTTON_PROBE_MS;
      if (gSolenoidRgbButtonProbeAttempts == NB_SOLENOID_RGB_BUTTON_PROBE_ATTEMPTS) {
        Serial.printf("solenoid DFR0991 absent after %u probes: ack_mask=0x%02X pid_addr=0x%02X pid=0x%04X\n",
                      gSolenoidRgbButtonProbeAttempts, gSolenoidRgbButtonAckMask,
                      gSolenoidRgbButtonPidAddr, gSolenoidRgbButtonPid);
      }
    }
    return;
  }

  if ((int32_t)(now - gSolenoidRgbButtonNextPollMs) < 0) return;
  gSolenoidRgbButtonNextPollMs = now + NB_SOLENOID_RGB_BUTTON_POLL_MS;

  uint8_t state = 0;
  if (!solenoidRgbButtonRead(gSolenoidRgbButtonAddr, kButtonReg, &state, 1)) {
    gSolenoidRgbButtonErrors++;
    if (++gSolenoidRgbButtonConsecutiveErrors >= NB_SOLENOID_RGB_BUTTON_MAX_ERRORS) {
      gSolenoidRgbButtonPresent = false;
      Serial.printf("solenoid DFR0991 at 0x%02X disabled after %u read errors\n",
                    gSolenoidRgbButtonAddr, NB_SOLENOID_RGB_BUTTON_MAX_ERRORS);
    }
    return;
  }
  gSolenoidRgbButtonConsecutiveErrors = 0;

  bool pressed = state != 0;
  if (pressed != gSolenoidRgbButtonRawPressed) {
    gSolenoidRgbButtonRawPressed = pressed;
    gSolenoidRgbButtonChangedMs = now;
  }
  if (pressed == gSolenoidRgbButtonStablePressed ||
      now - gSolenoidRgbButtonChangedMs < NB_SOLENOID_RGB_BUTTON_DEBOUNCE_MS) return;

  gSolenoidRgbButtonStablePressed = pressed;
  if (pressed) {
    gSolenoidRgbButtonPresses++;
    if (gMode == MODE_COMMS)
      solenoidStrike(NB_SOLENOID_DEFAULT_MS, "DFR0991 button");
    else
      Serial.println("solenoid DFR0991 button ignored during maintenance");
  }
}

// SparkFun Qwiic Navigation Switch PRT-27576. The board is a PCA9554 with
// UP/DOWN/RIGHT/LEFT/CENTER on active-LOW GPIO0..4. We only consume DOWN/GPIO1
// and leave the RGB outputs plus optional INT pin untouched. A PCA9554 has no
// product-ID register, so probe conservatively: address 0x20..0x27 must ACK and
// the five switch GPIOs must retain their power-on input/non-inverted config.
bool solenoidNavRead(uint8_t addr, uint8_t reg, uint8_t &value) {
  Wire1.setClock(100000); // ADR 0028 shared-bus ceiling
  Wire1.beginTransmission(addr);
  Wire1.write(reg);
  if (Wire1.endTransmission() != 0) return false;
  if (Wire1.requestFrom((int)addr, 1) != 1) return false;
  value = Wire1.read();
  return true;
}

bool solenoidNavPing(uint8_t addr) {
  Wire1.setClock(100000);
  Wire1.beginTransmission(addr);
  return Wire1.endTransmission() == 0;
}

bool solenoidNavProbe() {
  constexpr uint8_t kAddrMin = 0x20;
  constexpr uint8_t kAddrMax = 0x27;
  constexpr uint8_t kInputReg = 0x00;
  constexpr uint8_t kPolarityReg = 0x02;
  constexpr uint8_t kConfigReg = 0x03;

  gSolenoidNavProbeAttempts++;
  gSolenoidNavPresent = false;
  gSolenoidNavAddr = 0;
  gSolenoidNavAckMask = 0;
  for (uint8_t addr = kAddrMin; addr <= kAddrMax; ++addr) {
    if (!solenoidNavPing(addr)) continue;
    gSolenoidNavAckMask |= (uint8_t)(1U << (addr - kAddrMin));

    uint8_t input = 0, polarity = 0, config = 0;
    if (!solenoidNavRead(addr, kInputReg, input) ||
        !solenoidNavRead(addr, kPolarityReg, polarity) ||
        !solenoidNavRead(addr, kConfigReg, config)) continue;
    gSolenoidNavLastInput = input;
    gSolenoidNavLastPolarity = polarity;
    gSolenoidNavLastConfig = config;
    if ((config & 0x1F) != 0x1F || (polarity & 0x1F) != 0x00) continue;

    gSolenoidNavPresent = true;
    gSolenoidNavAddr = addr;
    gSolenoidNavRawReleased = (input & (1U << 1)) != 0;
    gSolenoidNavStableReleased = gSolenoidNavRawReleased;
    gSolenoidNavChangedMs = millis();
    gSolenoidNavNextPollMs = millis() + NB_SOLENOID_NAV_POLL_MS;
    gSolenoidNavConsecutiveErrors = 0;
    Serial.printf("solenoid local trigger: Qwiic Navigation Switch at 0x%02X, DOWN/GPIO1\n",
                  addr);
    return true;
  }
  return false;
}

void solenoidNavInit() {
  gSolenoidNavProbeAttempts = 0;
  if (solenoidNavProbe()) return;
  gSolenoidNavNextPollMs = millis() + NB_SOLENOID_NAV_PROBE_MS;
}

void solenoidNavTick() {
  constexpr uint8_t kInputReg = 0x00;
  uint32_t now = millis();
  if (!gSolenoidNavPresent) {
    if (gSolenoidNavProbeAttempts >= NB_SOLENOID_NAV_PROBE_ATTEMPTS ||
        (int32_t)(now - gSolenoidNavNextPollMs) < 0) return;
    if (!solenoidNavProbe()) {
      gSolenoidNavNextPollMs = now + NB_SOLENOID_NAV_PROBE_MS;
      if (gSolenoidNavProbeAttempts == NB_SOLENOID_NAV_PROBE_ATTEMPTS) {
        Serial.printf("solenoid Qwiic nav absent after %u probes: ack_mask=0x%02X config=0x%02X polarity=0x%02X\n",
                      gSolenoidNavProbeAttempts, gSolenoidNavAckMask,
                      gSolenoidNavLastConfig, gSolenoidNavLastPolarity);
      }
    }
    return;
  }

  if ((int32_t)(now - gSolenoidNavNextPollMs) < 0) return;
  gSolenoidNavNextPollMs = now + NB_SOLENOID_NAV_POLL_MS;

  uint8_t input = 0;
  if (!solenoidNavRead(gSolenoidNavAddr, kInputReg, input)) {
    gSolenoidNavErrors++;
    if (++gSolenoidNavConsecutiveErrors >= NB_SOLENOID_NAV_MAX_ERRORS) {
      gSolenoidNavPresent = false;
      Serial.printf("solenoid Qwiic nav at 0x%02X disabled after %u read errors\n",
                    gSolenoidNavAddr, NB_SOLENOID_NAV_MAX_ERRORS);
    }
    return;
  }
  gSolenoidNavConsecutiveErrors = 0;
  gSolenoidNavLastInput = input;

  bool released = (input & (1U << 1)) != 0;
  if (released != gSolenoidNavRawReleased) {
    gSolenoidNavRawReleased = released;
    gSolenoidNavChangedMs = now;
  }
  if (released == gSolenoidNavStableReleased ||
      now - gSolenoidNavChangedMs < NB_SOLENOID_NAV_DEBOUNCE_MS) return;

  gSolenoidNavStableReleased = released;
  if (!released) {
    gSolenoidNavPresses++;
    if (gMode == MODE_COMMS)
      solenoidStrike(NB_SOLENOID_DEFAULT_MS, "Qwiic nav DOWN");
    else
      Serial.println("solenoid Qwiic nav DOWN ignored during maintenance");
  }
}

void solenoidButtonPrepareSleep() {
  bool released = digitalRead(NB_SOLENOID_BUTTON_PIN) == HIGH;
  // Reset any wake configuration inherited within this boot, then re-enable it
  // only from a physically released level. A held LOW therefore gets the timer
  // wake only and cannot form an immediate EXT0 reboot/strike loop.
  esp_sleep_disable_wakeup_source(ESP_SLEEP_WAKEUP_EXT0);
  if (!released) {
    Serial.println("solenoid USER button held: button wake disabled for this sleep");
    return;
  }

  gpio_num_t pin = (gpio_num_t)NB_SOLENOID_BUTTON_PIN;
  esp_err_t err = rtc_gpio_init(pin);
  if (err == ESP_OK) err = rtc_gpio_set_direction(pin, RTC_GPIO_MODE_INPUT_ONLY);
  if (err == ESP_OK) err = rtc_gpio_pullup_en(pin);
  if (err == ESP_OK) err = rtc_gpio_pulldown_dis(pin);
  if (err == ESP_OK) err = esp_sleep_enable_ext0_wakeup(pin, 0);
  if (err != ESP_OK)
    Serial.printf("solenoid USER button wake setup failed: %s\n", esp_err_to_name(err));
}

void solenoidFailsafeTick() {
  if (gSolenoidGateOn &&
      (int32_t)(millis() - gSolenoidFailsafeMs) >= 0) {
    digitalWrite(NB_SOLENOID_PIN, LOW);
    gSolenoidGateOn = false;
    gSolenoidLastEndMs = millis();
    gSolenoidFailsafes++;
    Serial.println("solenoid FAILSAFE: gate forced LOW");
  }
}
#else
void solenoidInit() {}
void solenoidStop(const char *) {}
bool solenoidStrike(uint16_t, const char *) { return false; }
void capbankProbeInit() {}
void capbankReportIdle() { Serial.println("capbank probe requires --solenoid-d7"); }
bool capbankProbeStrike(uint16_t) {
  Serial.println("capbank probe requires --solenoid-d7");
  return false;
}
void capbankWaveConfigureRoutes() {}
void solenoidButtonHandleWake() {}
void solenoidButtonTick() {}
void solenoidRgbButtonInit() {}
void solenoidRgbButtonTick() {}
void solenoidNavInit() {}
void solenoidNavTick() {}
void solenoidButtonPrepareSleep() {}
void solenoidFailsafeTick() {}
#endif

// ESP-NOW rx -> loop queue (callback enqueues only; loop processes)
struct RxItem {
  uint8_t mac[6];
  int8_t rssi;
  uint8_t len;
  uint8_t data[160];
};
QueueHandle_t rxQueue;
static_assert(sizeof(NbHeartbeat) <= sizeof(RxItem::data),
              "heartbeat outgrew the rx buffer -- bump RxItem::data");
#define NB_HAS_HB_FIELD(len, field) \
  ((len) >= (int)(offsetof(NbHeartbeat, field) + sizeof(((NbHeartbeat *)0)->field)))

// ---- reused helpers (from power_bench) -------------------------------------
const char *resetReasonName(esp_reset_reason_t r) {
  switch (r) {
  case ESP_RST_POWERON: return "poweron";
  case ESP_RST_EXT: return "external";
  case ESP_RST_SW: return "software";
  case ESP_RST_PANIC: return "panic";
  case ESP_RST_INT_WDT: return "interrupt_watchdog";
  case ESP_RST_TASK_WDT: return "task_watchdog";
  case ESP_RST_WDT: return "other_watchdog";
  case ESP_RST_DEEPSLEEP: return "deepsleep";
  case ESP_RST_BROWNOUT: return "brownout";
  default: return "unknown";
  }
}
const char *batteryTypeName() {
  switch (RES_PF_BATTERY_TYPE) {
  case Mainboard::BatteryType::Generic_3V7: return "Generic_3V7";
  case Mainboard::BatteryType::Generic_LFP: return "Generic_LFP";
  default: return "other";
  }
}

uint16_t checkedStoredUInt(Preferences &pf, const char *key, uint16_t fallback,
                           uint16_t minVal, uint16_t maxVal) {
  uint32_t raw = pf.getUInt(key, fallback);
  if (raw < minVal || raw > maxVal) return fallback;
  return (uint16_t)raw;
}

void loadBenchConfig() {
  if (gBenchConfigLoaded) return;
  gBenchConfigLoaded = true;
  uint16_t defaultChargeMa = (uint16_t)(RES_PF_MAX_CHARGE_MA + 0.5f);
#if NB_MAGIC_WAND
  // This one-off fixture has a known 15 Ah LFP cell and a conservative 500 mA
  // charge limit. Do not inherit stale capacity/charge overrides from a board's
  // earlier bench role.
  gBatteryCapacityMah = (uint16_t)RES_PF_BATTERY_CAPACITY_MAH;
  gChargeMa = defaultChargeMa;
  Serial.printf("  magic wand config: cap=%u mAh charge=%u mA (build locked)\n",
                gBatteryCapacityMah, gChargeMa);
  return;
#endif
  Preferences pf;
  pf.begin("netbench", false);
  uint32_t chargePolicyVersion = pf.getUInt("chg_policy", 0);
  if (chargePolicyVersion < NB_CHARGE_POLICY_VERSION) {
    // Replace known historical defaults, but preserve a nonstandard value that
    // may be an intentional small-cell limit.
    uint32_t priorMa = pf.getUInt("chg_ma", 0);
    bool legacyDefault = priorMa == 0 || priorMa == 500 ||
                         priorMa == 1000 || priorMa == 1500;
    if (legacyDefault) pf.putUInt("chg_ma", defaultChargeMa);
    pf.putUInt("chg_policy", NB_CHARGE_POLICY_VERSION);
    Serial.printf("  charge policy v%u %s %lu mA%s\n",
                  (unsigned)NB_CHARGE_POLICY_VERSION,
                  legacyDefault ? "migrated" : "preserved",
                  (unsigned long)(legacyDefault ? defaultChargeMa : priorMa),
                  legacyDefault ? "" : " (explicit override)");
  }
  gBatteryCapacityMah = checkedStoredUInt(pf, "cap_mah", (uint16_t)RES_PF_BATTERY_CAPACITY_MAH,
                                          NB_CAPACITY_MIN_MAH, NB_CAPACITY_MAX_MAH);
  gChargeMa = checkedStoredUInt(pf, "chg_ma", defaultChargeMa, NB_CHARGE_MIN_MA, NB_CHARGE_MAX_MA);
  pf.end();
  Serial.printf("  bench config: cap=%u mAh charge=%u mA%s\n",
                gBatteryCapacityMah, gChargeMa,
                (gBatteryCapacityMah == (uint16_t)RES_PF_BATTERY_CAPACITY_MAH &&
                 gChargeMa == defaultChargeMa) ? " (build defaults)" : " (NVS override)");
}

bool fieldSessionUnexpectedReset(esp_reset_reason_t reason) {
  switch (reason) {
  case ESP_RST_POWERON:
  case ESP_RST_PANIC:
  case ESP_RST_INT_WDT:
  case ESP_RST_TASK_WDT:
  case ESP_RST_WDT:
  case ESP_RST_BROWNOUT:
    return true;
  default:
    return false;
  }
}

void fieldSessionRawRailOff() {
#if defined(NB_FIELD_CYCLE) && NB_FIELD_LED_LOAD
  pinMode(NB_DRAWDOWN_PIXEL_PIN, OUTPUT);
  digitalWrite(NB_DRAWDOWN_PIXEL_PIN, LOW);
  rtc_gpio_hold_dis(GPIO_NUM_4);
  rtc_gpio_init(GPIO_NUM_4);
  rtc_gpio_set_direction(GPIO_NUM_4, RTC_GPIO_MODE_INPUT_OUTPUT);
  rtc_gpio_set_level(GPIO_NUM_4, 0);
  rtc_gpio_hold_en(GPIO_NUM_4);
#endif
}

void fieldSessionGuardPreInit() {
#if defined(NB_FIELD_CYCLE) && NB_FIELD_LED_LOAD
  // Fail-safe from the first instructions: keep pixel data and the switchable header
  // rail low until the power stack, reset guard, and ESP-NOW are initialized. Board.init()
  // will briefly reconfigure EN_3V3, so setupPowerFeather() parks it again immediately.
  fieldSessionRawRailOff();

  Preferences pf;
  if (pf.begin("netbench", false)) {
    if (pf.isKey("fc_led_stage")) {
      gFieldSessionStage = min((uint8_t)FIELD_SESSION_PROTECT,
                               pf.getUChar("fc_led_stage", FIELD_SESSION_IDLE));
    } else if (pf.getBool("fc_led_active", false)) {
      // Migration from the compiled-but-not-normally-deployed boolean guard. Treat an
      // armed legacy marker as a full-load attempt so it receives one safe dim retry.
      gFieldSessionStage = FIELD_SESSION_FULL;
      pf.putUChar("fc_led_stage", gFieldSessionStage);
    }
    gFieldSessionStateLoaded = true;

    if (gFieldSessionStage == FIELD_SESSION_PROTECT) {
      // PROTECT is a durable charge-release latch, not merely a reset diagnosis.
      // RTC phase data can be lost across an OTA/software reset, so NVS must remain
      // authoritative on every boot type until verified charge clears the stage.
      gFieldInterruptedPark = true;
      gFieldInterruptedBoot = fieldSessionUnexpectedReset(esp_reset_reason());
    } else if (gFieldSessionStage != FIELD_SESSION_IDLE &&
               fieldSessionUnexpectedReset(esp_reset_reason())) {
      gFieldInterruptedBoot = true;
      if (gFieldSessionStage == FIELD_SESSION_FULL) {
        // Consume the only retry BEFORE any rail can turn on. A reset during the dim
        // attempt therefore boots with DIM already persisted and hard-parks below.
        if (pf.putUChar("fc_led_stage", FIELD_SESSION_DIM) == sizeof(uint8_t)) {
          gFieldSessionStage = FIELD_SESSION_DIM;
          gFieldInterruptedRetry = true;
        } else {
          gFieldSessionStage = FIELD_SESSION_PROTECT;
          gFieldInterruptedPark = true;
        }
      } else {
        gFieldInterruptedPark = true;
      }
    } else if (gFieldSessionStage == FIELD_SESSION_DIM) {
      // A deliberate software reset/OTA is not a retry failure. Preserve the
      // already-selected dim tier if RTC state was reinitialized by the new image.
      rtcFieldLoadDimmed = 1;
    }
    pf.end();
  }
  if (!gFieldSessionStateLoaded && fieldSessionUnexpectedReset(esp_reset_reason())) {
    // If NVS itself cannot be read, fail safe rather than applying a blind full load.
    gFieldInterruptedBoot = true;
    gFieldInterruptedPark = true;
    gFieldSessionStage = FIELD_SESSION_PROTECT;
  }
  gFieldSessionMarker = gFieldSessionStage != FIELD_SESSION_IDLE;
#endif
}

bool fieldSessionSetStage(uint8_t stage) {
#if defined(NB_FIELD_CYCLE) && NB_FIELD_LED_LOAD
  stage = min((uint8_t)FIELD_SESSION_PROTECT, stage);
  if (gFieldSessionStateLoaded && gFieldSessionStage == stage) return true;
  Preferences pf;
  if (!pf.begin("netbench", false)) return false;
  size_t written = pf.putUChar("fc_led_stage", stage);
  pf.end();
  if (written != sizeof(uint8_t)) return false;
  gFieldSessionStage = stage;
  gFieldSessionMarker = stage != FIELD_SESSION_IDLE;
  gFieldSessionStateLoaded = true;
#else
  (void)stage;
#endif
  return true;
}

void fieldSessionReportBootState() {
#if defined(NB_FIELD_CYCLE) && NB_FIELD_LED_LOAD
  Serial.printf("field-session guard: stage=%u marker=%d interrupted=%d retry=%d park=%d reset=%s nvs=%d\n",
                gFieldSessionStage, gFieldSessionMarker ? 1 : 0,
                gFieldInterruptedBoot ? 1 : 0, gFieldInterruptedRetry ? 1 : 0,
                gFieldInterruptedPark ? 1 : 0,
                resetReasonName(esp_reset_reason()), gFieldSessionStateLoaded ? 1 : 0);
#endif
}

bool persistCapacity(uint16_t mah) {
  if (mah < NB_CAPACITY_MIN_MAH || mah > NB_CAPACITY_MAX_MAH) {
    Serial.printf("capacity %u rejected (range %u..%u mAh)\n",
                  mah, (unsigned)NB_CAPACITY_MIN_MAH, (unsigned)NB_CAPACITY_MAX_MAH);
    return false;
  }
  Preferences pf;
  pf.begin("netbench", false);
  pf.putUInt("cap_mah", mah);
  pf.end();
  gBatteryCapacityMah = mah;
  Serial.printf("battery capacity stored -> %u mAh; rebooting to apply gauge model\n", mah);
  Serial.flush();
  delay(150);
  esp_restart();
  return true;
}

bool persistAndApplyChargeMa(uint16_t ma) {
  if (ma < NB_CHARGE_MIN_MA || ma > NB_CHARGE_MAX_MA) {
    Serial.printf("charge current %u rejected (range %u..%u mA)\n",
                  ma, (unsigned)NB_CHARGE_MIN_MA, (unsigned)NB_CHARGE_MAX_MA);
    return false;
  }
  Preferences pf;
  pf.begin("netbench", false);
  pf.putUInt("chg_ma", ma);
  pf.end();
  gChargeMa = ma;
  if (pfReady) Board.setBatteryChargingMaxCurrent((float)ma);
  Serial.printf("charge current cap stored/applied -> %u mA\n", ma);
  return true;
}

void setupPowerFeather() {
  Serial.println("PowerFeather SDK init:");
  loadBenchConfig();
  Result r = Result::Failure;
  for (int a = 1; a <= 4; a++) {
    r = Board.init(gBatteryCapacityMah, RES_PF_BATTERY_TYPE);
#if defined(NB_FIELD_CYCLE) && NB_FIELD_LED_LOAD
    fieldSessionRawRailOff();
#endif
    if (r == Result::Ok) break;
    Serial.printf("  Board.init attempt %d -> %d, retrying\n", a, (int)r);
    delay(250);
  }
  pfReady = (r == Result::Ok);
  Serial.printf("  Board.init(cap=%u, %s) -> %s\n", (unsigned)gBatteryCapacityMah,
                batteryTypeName(), pfReady ? "Ok" : "ERR");
  if (!pfReady) return;
#if defined(NB_FIELD_CYCLE) && NB_FIELD_LED_LOAD
  // The SDK intentionally enables this rail on cold init. Field-cycle owns the LED
  // rail, so park it before any charger policy writes or network startup can overlap
  // an old/unknown pixel frame. Only fieldCycleLedLoadOn() may re-enable it.
  if (Board.enable3V3(false) != Result::Ok)
    Serial.println("field-session guard: WARN failed to park 3V3 after Board.init");
#endif
  gMaintainV = (float)RES_PF_MAINTAIN_V;
  Board.setSupplyMaintainVoltage(gMaintainV);
  rtcFieldMpptActiveV10 = (uint8_t)(gMaintainV * 10.0f + 0.5f);
#if RES_PF_ENABLE_CHARGING
  Board.setBatteryChargingMaxCurrent((float)gChargeMa);
#endif
  // Charging a missing battery can brownout-loop the board on USB. Keep charging
  // off until the warmed gauge reports a plausible cell; chargingGuardTick()
  // enables it later. This makes one image safe for bare-board incoming inspection
  // and for the same board after a production battery is installed.
  Board.enableBatteryCharging(false);
  gChargingEnabled = false;
  pfSolarGuardInit("net_bench", gMaintainV, false);
}

// ---- onboard INA helpers (placed after the structs; see note at the globals) -
static bool inaReadReg(uint8_t addr, uint8_t reg, uint16_t &val) {
  Wire1.beginTransmission(addr);
  Wire1.write(reg);
  if (Wire1.endTransmission(false) != 0) return false;
  if (Wire1.requestFrom((int)addr, 2) != 2) return false;
  val = ((uint16_t)Wire1.read() << 8) | Wire1.read();
  return true;
}
static bool inaWriteReg(uint8_t addr, uint8_t reg, uint16_t val) {
  Wire1.beginTransmission(addr);
  Wire1.write(reg);
  Wire1.write(val >> 8);
  Wire1.write(val & 0xFF);
  return Wire1.endTransmission() == 0;
}
static bool inaProbe(uint8_t addr) {
  uint16_t v;
  if (!inaReadReg(addr, 0x00, v)) return false;
  return inaWriteReg(addr, 0x00, NB_INA_CONFIG);
}
static bool inaRead(uint8_t addr, int16_t &bus_mv, int16_t &ma) {
  uint16_t rs, rb;
  if (!(inaReadReg(addr, 0x01, rs) && inaReadReg(addr, 0x02, rb))) return false;
  float shunt_mv = (int16_t)rs * 0.01f;            // 10 uV LSB
  bus_mv = (int16_t)((rb >> 3) * 4);               // 4 mV LSB
  ma = (int16_t)(shunt_mv / NB_INA_RSHUNT_OHMS);   // mV / ohm = mA
  return true;
}

static uint16_t bqMvOrUnknown(bool ok, float volts) {
  if (!ok || volts < 0.0f) return 0xFFFF;
  return (uint16_t)min(65535UL, (unsigned long)(volts * 1000.0f + 0.5f));
}

static uint16_t bqMaOrUnknown(bool ok, float ma) {
  if (!ok || ma < 0.0f) return 0xFFFF;
  return (uint16_t)min(65535UL, (unsigned long)(ma + 0.5f));
}

void readChargerStatus() {
  gBqVindpmMv = gBqIchgMa = gBqVregMv = 0xFFFF;
  gBqReg16 = gBqReg18 = gBqStat0 = gBqStat1 = 0xFF;
  gBqFault0 = gBqFlag0 = gBqFlag1 = gBqFaultFlag0 = gBqPart = 0xFF;
  if (!pfReady) return;

  float v = 0.0f;
  gBqVindpmMv = bqMvOrUnknown(Board.getCharger().getVINDPM(v), v);
  gBqIchgMa = bqMaOrUnknown(Board.getCharger().getChargeCurrentLimit(v), v);
  gBqVregMv = bqMvOrUnknown(Board.getCharger().getChargeVoltageLimit(v), v);

  uint8_t b = 0;
  if (pfSolarGuardRead8(PF_SOLAR_GUARD_REG_CHG_CTRL0, b)) gBqReg16 = b;
  if (pfSolarGuardRead8(0x18, b)) gBqReg18 = b;
  if (pfSolarGuardRead8(0x1D, b)) gBqStat0 = b;
  if (pfSolarGuardRead8(0x1E, b)) gBqStat1 = b;
  if (pfSolarGuardRead8(0x1F, b)) gBqFault0 = b;
  if (pfSolarGuardRead8(0x20, b)) gBqFlag0 = b;
  if (pfSolarGuardRead8(0x21, b)) gBqFlag1 = b;
  if (pfSolarGuardRead8(0x22, b)) gBqFaultFlag0 = b;
  if (pfSolarGuardRead8(0x38, b)) gBqPart = b;
}

// Env sensors: probe the STEMMA bus once at boot. Board.init() already started
// Wire1 (47/48) and enabled VSQT, so a sensored board just works; a bare board
// probes-and-misses and sends absent-sentinels. Battery NTC is OPT-IN
// (-DNB_BATT_NTC): enabling the charger's TS input with no thermistor attached
// makes the BQ apply JEITA limits to a floating pin -> can suspend charging.
void envInit() {
  Wire1.begin(47, 48, 100000); // idempotent; keep the SDK's 100 kHz
  // Wiring check: list every ACK on the STEMMA bus (the power chips live here too)
  Serial.print("Wire1 scan:");
  for (uint8_t a = 0x08; a <= 0x77; a++) {
    Wire1.beginTransmission(a);
    if (Wire1.endTransmission() == 0) Serial.printf(" 0x%02X", a);
  }
  Serial.println();
  gEnvTsl = gTsl.begin(&Wire1);
  if (gEnvTsl) {
    gTsl.setGain(TSL2591_GAIN_LOW);                 // full-sun headroom
    gTsl.setTiming(TSL2591_INTEGRATIONTIME_100MS);  // max count 36863
  }
  gEnvSht = gSht.begin(0x44);
  gInaPanel = inaProbe(NB_INA_PANEL_ADDR);
  gInaBatt = inaProbe(NB_INA_BATT_ADDR);
#ifdef NB_BATT_NTC
  if (pfReady && Board.enableBatteryTempSense(true) == Result::Ok) {
    float t;
    gEnvBtemp = (Board.getBatteryTemperature(t) == Result::Ok);
  }
#endif
  Serial.printf("env sensors: TSL2591=%d SHT31=%d batt-NTC=%d INA-panel(0x%02X)=%d INA-batt(0x%02X)=%d\n",
                gEnvTsl, gEnvSht, gEnvBtemp, NB_INA_PANEL_ADDR, gInaPanel, NB_INA_BATT_ADDR, gInaBatt);
}

// Refresh the env cache at ~1 Hz. The TSL2591 read blocks ~120 ms (integration),
// so heartbeats at high rates reuse the cache instead of reading inline.
void envTick() {
  static uint32_t nextMs = 0;
  if ((!gEnvTsl && !gEnvSht && !gEnvBtemp && !gInaPanel && !gInaBatt) || millis() < nextMs) return;
  nextMs = millis() + 1000;
  if (gInaPanel && !inaRead(NB_INA_PANEL_ADDR, gInaPvMv, gInaPaMa)) {
    gInaPvMv = INT16_MIN; gInaPaMa = INT16_MIN;
  }
  if (gInaBatt && !inaRead(NB_INA_BATT_ADDR, gInaBvMv, gInaBaMa)) {
    gInaBvMv = INT16_MIN; gInaBaMa = INT16_MIN;
  }
  if (gEnvTsl) {
    uint32_t lum = gTsl.getFullLuminosity();
    gEnvCh0 = (uint16_t)(lum & 0xFFFF);
    gEnvCh1 = (uint16_t)(lum >> 16);
    float lux = gTsl.calculateLux(gEnvCh0, gEnvCh1);
    if (gEnvCh0 >= 36800 || gEnvCh1 >= 36800 || lux < 0.0f)
      gEnvLuxX10 = 0xFFFFFFFE; // saturated: add a diffuser (relative use survives it)
    else
      gEnvLuxX10 = (uint32_t)(lux * 10.0f);
  }
  if (gEnvSht) {
    float t = gSht.readTemperature(), h = gSht.readHumidity();
    gEnvPtempX10 = isnan(t) ? INT16_MIN : (int16_t)(t * 10.0f);
    gEnvRh = isnan(h) ? 255 : (uint8_t)(h + 0.5f);
  }
  if (gEnvBtemp) {
    float t;
    if (Board.getBatteryTemperature(t) == Result::Ok) gEnvBtempX10 = (int16_t)(t * 10.0f);
  }
}

#if NB_SENSOR_TRIAD
void sensorTriadInit() {
  Wire1.setClock(100000);
  gMsa311Present = gMsa311.begin(MSA311_I2CADDR_DEFAULT, &Wire1);
  if (gMsa311Present) {
    gMsa311.setRange(MSA301_RANGE_4_G);
    gMsa311.setDataRate(MSA301_DATARATE_125_HZ);
    gMsa311.setBandwidth(MSA301_BANDWIDTH_62_5_HZ);
    gMsa311.setPowerMode(MSA301_NORMALMODE);
  }

  Wire1.setClock(100000);
  gBmp581Present = gBmp581.begin(BMP5XX_ALTERNATIVE_ADDRESS, &Wire1);
  if (gBmp581Present) {
    gBmp581.setTemperatureOversampling(BMP5XX_OVERSAMPLING_2X);
    gBmp581.setPressureOversampling(BMP5XX_OVERSAMPLING_16X);
    gBmp581.setIIRFilterCoeff(BMP5XX_IIR_FILTER_COEFF_3);
    gBmp581.setOutputDataRate(BMP5XX_ODR_05_HZ);
    gBmp581.setPowerMode(BMP5XX_POWERMODE_NORMAL);
    gBmp581.enablePressure(true);
  }

  Wire1.setClock(100000);
  gTmf8820Present = gTmf8820.begin(Wire1);
  Wire1.setClock(100000);
  Serial.printf("sensor triad @100kHz: MSA311(0x62)=%d TMF8820(0x41)=%d BMP581(0x47)=%d\n",
                gMsa311Present, gTmf8820Present, gBmp581Present);
}

void sensorTriadTick() {
  static uint32_t nextMs = 0;
  if (millis() < nextMs) return;
  nextMs = millis() + 2000;
  Wire1.setClock(100000);

  gMsa311ReadOk = false;
  if (gMsa311Present) {
    gMsa311.read();
    gMsaAxG = gMsa311.x_g;
    gMsaAyG = gMsa311.y_g;
    gMsaAzG = gMsa311.z_g;
    gMsa311ReadOk = isfinite(gMsaAxG) && isfinite(gMsaAyG) && isfinite(gMsaAzG);
  }

  gBmp581ReadOk = false;
  if (gBmp581Present && gBmp581.performReading()) {
    gBmpTempC = gBmp581.temperature;
    gBmpPressureHpa = gBmp581.pressure;
    gBmp581ReadOk = isfinite(gBmpTempC) && isfinite(gBmpPressureHpa);
  }

  gTmf8820ReadOk = false;
  gTmfClosestMm = 0;
  gTmfClosestConfidence = 0;
  if (gTmf8820Present) {
    Wire1.setClock(100000);
    if (gTmf8820.startMeasuring(gTmfResults)) {
      gTmf8820ReadOk = true;
      gTmfReadCount++;
      uint32_t count = min((uint32_t)TMF882X_MAX_MEAS_RESULTS, gTmfResults.num_results);
      for (uint32_t i = 0; i < count; ++i) {
        const tmf882x_meas_result &r = gTmfResults.results[i];
        if (r.confidence == 0 || r.distance_mm == 0 || r.distance_mm > UINT16_MAX) continue;
        if (gTmfClosestMm == 0 || r.distance_mm < gTmfClosestMm) {
          gTmfClosestMm = (uint16_t)r.distance_mm;
          gTmfClosestConfidence = (uint16_t)min((uint32_t)UINT16_MAX, r.confidence);
        }
      }
    } else {
      gTmfReadErrors++;
    }
    Wire1.setClock(100000);
  }
}
#else
void sensorTriadInit() {}
void sensorTriadTick() {}
#endif

// Locate pattern "..-" (dot dot dash + gap), unmistakable vs the battery blinks.
struct LedStep { uint16_t ms; bool on; };
const LedStep IDENT_PAT[] = {
    {150, true}, {150, false}, {150, true}, {150, false}, {450, true}, {700, false}};
const uint8_t IDENT_N = 6;

// Onboard LED indicator. Identify (locate) overrides battery for its window:
//   identify: "..-" | >50% solid | 25-50% 1 Hz | 10-24% 2 Hz | <10% 4 Hz | no info off
// VOLTAGE CROSS-CHECK: the MAX17260 SOC can read wildly wrong after a DesignCap change
// or before a learn cycle (we saw a full 4.19 V cell report 1%). So floor the displayed
// level by what the (loaded, Li-ion) terminal voltage allows -- a healthy cell never
// shows "critical". Thresholds are Generic_3V7; LFP would need its own (flat curve).
void updateStatusLed() {
  uint32_t now = millis();
  if (now < identifyUntil) { // locate beacon
    static uint32_t t0 = 0;
    static uint8_t i = 0;
    if (now - t0 >= IDENT_PAT[i].ms) { i = (i + 1) % IDENT_N; t0 = now; }
    digitalWrite(NB_LED_PIN, IDENT_PAT[i].on ? HIGH : LOW);
    return;
  }
  static uint32_t last = 0;
  static bool on = false;
  int soc = cbSoc;
  float v = cbV;
  if (soc < 0 && v < 2.5f) { digitalWrite(NB_LED_PIN, LOW); return; } // no battery info -> off
  int vfloor = (v >= 3.95f) ? 99 : (v >= 3.70f) ? 40 : (v >= 3.50f) ? 20 : (v >= 3.35f) ? 12 : 0;
  int eff = (soc < 0) ? vfloor : (soc > vfloor ? soc : vfloor); // healthier of gauge vs voltage
  if (eff > 50) { digitalWrite(NB_LED_PIN, HIGH); return; }      // solid
  uint16_t interval = (eff >= 25) ? 500 : (eff >= 10) ? 250 : 125; // 1/2/4 Hz
  if (now - last >= interval) { last = now; on = !on; digitalWrite(NB_LED_PIN, on ? HIGH : LOW); }
}

void readBatteryCell() {
  if (!pfReady) return;
  float v;
  if (Board.getBatteryVoltage(v) == Result::Ok) cbV = v;
  if (Board.getBatteryCurrent(v) == Result::Ok) {
    cbMaRaw = v;
    cbMa = v / NB_GAUGE_CURRENT_DIVISOR;
  }
  uint8_t s;
  if (Board.getBatteryCharge(s) == Result::Ok) cbSoc = s;
}

void chargingGuardTick() {
#if RES_PF_ENABLE_CHARGING
  static bool done = false;
  if (done || !pfReady || millis() < 6000) return;
  if (cbV < 0.1f) {
    if (millis() > 60000) {
      done = true;
      Serial.println("no battery reading after 60 s -> charging stays OFF until reboot");
    }
    return;
  }
  done = true;
  if (cbV > 2.5f && cbV < 4.4f) {
    Board.setBatteryChargingMaxCurrent((float)gChargeMa);
    Board.enableBatteryCharging(true);
    gChargingEnabled = true;
    pfSolarGuardInit("net_bench", gMaintainV, true);
    Serial.printf("battery %.2fV present -> charging ON (%u mA, %s profile)\n",
                  cbV, (unsigned)gChargeMa, batteryTypeName());
  } else {
    Serial.printf("battery %.2fV implausible -> charging stays OFF\n", cbV);
  }
#endif
}

void readBattery() {
  if (!pfReady) return;
  readBatteryCell();
  chargingGuardTick();
  float v;
  if (Board.getSupplyVoltage(v) == Result::Ok) csV = v;
  if (Board.getSupplyCurrent(v) == Result::Ok) csMa = v;
  bool g;
  if (Board.checkSupplyGood(g) == Result::Ok) csGood = g;
  readChargerStatus();
  pfSolarGuardTick("net_bench", csV, csMa, csGood, gMaintainV, gChargingEnabled);
}

String telemetryJson() {
  String j = "{";
  j += "\"board\":\"" RES_BOARD_NAME "\"";
  j += ",\"fw\":\"" NET_BENCH_VERSION "\"";
  j += ",\"fixture_id\":\"" + shortId + "\"";
  j += ",\"role\":\"";
  j += IS_MASTER ? "master" : "peer";
  j += "\"";
  j += ",\"mode\":";
  j += (int)gMode;
  j += ",\"uptime_ms\":" + String((unsigned long)millis());
  j += ",\"drawdown_active\":";
  j += gDrawdownActive ? "true" : "false";
  j += ",\"drawdown_mah\":";
  j += String(gDrawdownMah, 1);
  j += ",\"drawdown_budget_mah\":";
  j += String(gDrawdownBudgetMah);
  j += ",\"heap_free\":" + String(ESP.getFreeHeap());
  j += ",\"flash_bytes\":" + String((unsigned long)ESP.getFlashChipSize());
  j += ",\"psram_bytes\":" + String((unsigned long)ESP.getPsramSize());
  j += ",\"reset_reason\":\"" + String(resetReasonName(esp_reset_reason())) + "\"";
  j += ",\"pf_ready\":";
  j += pfReady ? "true" : "false";
  j += ",\"battery_present\":";
  j += (cbV > 2.5f && cbV < 4.4f) ? "true" : "false";
  j += ",\"charging_enabled\":";
  j += gChargingEnabled ? "true" : "false";
  j += ",\"maint_status\":";
  j += String(gMaintStatus);
  j += ",\"field_phase\":";
  j += String(rtcFieldPhase);
  j += ",\"field_reason\":";
  j += String(rtcFieldReason);
  j += ",\"field_cycle\":";
  j += String(rtcFieldCycle);
  j += ",\"field_elapsed_s\":";
  j += String((unsigned long)rtcFieldPhaseElapsedS);
  j += ",\"field_charge_mah\":";
  j += String((unsigned long)(rtcFieldChargeMas / 3600UL));
  j += ",\"field_discharge_mah\":";
  j += String((unsigned long)(rtcFieldDischargeMas / 3600UL));
  j += ",\"field_min_mv\":";
  j += String(rtcFieldMinMv);
  j += ",\"field_max_mv\":";
  j += String(rtcFieldMaxMv);
  j += ",\"field_charge_wh\":";
  j += String((float)rtcFieldChargeMws / 3600000.0f, 2);
  j += ",\"field_discharge_wh\":";
  j += String((float)rtcFieldDischargeMws / 3600000.0f, 2);
  j += ",\"field_peak_panel_w\":";
  j += String((float)rtcFieldPeakPanelWx100 / 100.0f, 2);
  j += ",\"field_peak_charge_w\":";
  j += String((float)rtcFieldPeakChargeWx100 / 100.0f, 2);
  j += ",\"field_peak_draw_w\":";
  j += String((float)rtcFieldPeakDrawWx100 / 100.0f, 2);
  j += ",\"field_low_s\":";
  j += String(rtcFieldLowS);
  j += ",\"field_charge_s\":";
  j += String(rtcFieldChargeS);
  j += ",\"field_wait_s\":";
  j += String(rtcFieldWaitS);
  j += ",\"field_draw_s\":";
  j += String(rtcFieldDrawS);
  j += ",\"field_protect_s\":";
  j += String(rtcFieldProtectS);
  j += ",\"field_dim_s\":";
  j += String(rtcFieldDimS);
  j += ",\"field_load_dimmed\":";
  j += rtcFieldLoadDimmed ? "true" : "false";
  j += ",\"field_protect_latched\":";
  j += rtcFieldProtectLatched ? "true" : "false";
  j += ",\"field_session_marker\":";
  j += gFieldSessionMarker ? "true" : "false";
  j += ",\"field_session_stage\":";
  j += String(gFieldSessionStage);
  j += ",\"field_interrupted_boot\":";
  j += gFieldInterruptedBoot ? "true" : "false";
  j += ",\"field_interrupted_retry\":";
  j += gFieldInterruptedRetry ? "true" : "false";
  j += ",\"field_interrupted_park\":";
  j += gFieldInterruptedPark ? "true" : "false";
  j += ",\"field_dusk_s\":";
  j += String(rtcFieldDuskS);
  j += ",\"field_lux_sensor_seen\":";
  j += rtcFieldLuxSensorSeen ? "true" : "false";
  j += ",\"mppt_status\":";
  j += String(rtcFieldMpptStatus);
  j += ",\"mppt_reason\":";
  j += String(rtcFieldMpptReason);
  j += ",\"mppt_runs\":";
  j += String(rtcFieldMpptRuns);
  j += ",\"mppt_active_v10\":";
  j += String(rtcFieldMpptActiveV10);
  j += ",\"mppt_best_v10\":";
  j += String(rtcFieldMpptBestV10);
  j += ",\"mppt_last_v10\":";
  j += String(rtcFieldMpptLastV10);
  j += ",\"mppt_p46_w\":";
  j += String((float)rtcFieldMpptP46Wx100 / 100.0f, 2);
  j += ",\"mppt_p48_w\":";
  j += String((float)rtcFieldMpptP48Wx100 / 100.0f, 2);
  j += ",\"mppt_p50_w\":";
  j += String((float)rtcFieldMpptP50Wx100 / 100.0f, 2);
  j += ",\"battery_type\":\"" + String(batteryTypeName()) + "\"";
  j += ",\"battery_capacity_mah\":" + String(gBatteryCapacityMah);
  j += ",\"charge_limit_ma\":" + String(gChargeMa);
  j += ",\"maintain_v\":" + String(gMaintainV, 1);
  if (pfReady) {
    char b[24];
    float v;
    if (Board.getBatteryVoltage(v) == Result::Ok) { snprintf(b, sizeof(b), "%.3f", v); j += ",\"battery_v\":" + String(b); }
    if (Board.getBatteryCurrent(v) == Result::Ok) {
      snprintf(b, sizeof(b), "%.1f", v / NB_GAUGE_CURRENT_DIVISOR);
      j += ",\"battery_ma\":" + String(b);
      snprintf(b, sizeof(b), "%.1f", v);
      j += ",\"battery_ma_raw\":" + String(b);
      j += ",\"battery_current_divisor\":" + String(NB_GAUGE_CURRENT_DIVISOR, 2);
    }
    uint8_t s;
    if (Board.getBatteryCharge(s) == Result::Ok) j += ",\"soc_pct\":" + String(s);
    if (Board.getSupplyVoltage(v) == Result::Ok) { snprintf(b, sizeof(b), "%.3f", v); j += ",\"supply_v\":" + String(b); }
    if (Board.getSupplyCurrent(v) == Result::Ok) { snprintf(b, sizeof(b), "%.1f", v); j += ",\"supply_ma\":" + String(b); }
    bool g;
    if (Board.checkSupplyGood(g) == Result::Ok) { j += ",\"supply_good\":"; j += g ? "true" : "false"; }
  }
#if NB_SENSOR_TRIAD
  j += ",\"sensor_triad_enabled\":true";
  j += ",\"msa311_present\":";
  j += gMsa311Present ? "true" : "false";
  j += ",\"msa311_read_ok\":";
  j += gMsa311ReadOk ? "true" : "false";
  j += ",\"msa_ax_g\":";
  j += isfinite(gMsaAxG) ? String(gMsaAxG, 4) : "null";
  j += ",\"msa_ay_g\":";
  j += isfinite(gMsaAyG) ? String(gMsaAyG, 4) : "null";
  j += ",\"msa_az_g\":";
  j += isfinite(gMsaAzG) ? String(gMsaAzG, 4) : "null";
  j += ",\"bmp581_present\":";
  j += gBmp581Present ? "true" : "false";
  j += ",\"bmp581_read_ok\":";
  j += gBmp581ReadOk ? "true" : "false";
  j += ",\"bmp_temp_c\":";
  j += isfinite(gBmpTempC) ? String(gBmpTempC, 2) : "null";
  j += ",\"bmp_pressure_hpa\":";
  j += isfinite(gBmpPressureHpa) ? String(gBmpPressureHpa, 2) : "null";
  j += ",\"tmf8820_present\":";
  j += gTmf8820Present ? "true" : "false";
  j += ",\"tmf8820_read_ok\":";
  j += gTmf8820ReadOk ? "true" : "false";
  j += ",\"tmf_result_num\":" + String((unsigned long)gTmfResults.result_num);
  j += ",\"tmf_result_count\":" + String((unsigned long)gTmfResults.num_results);
  j += ",\"tmf_closest_mm\":" + String(gTmfClosestMm);
  j += ",\"tmf_closest_confidence\":" + String(gTmfClosestConfidence);
  j += ",\"tmf_ambient_light\":" + String((unsigned long)gTmfResults.ambient_light);
  j += ",\"tmf_temperature_c\":" + String((unsigned long)gTmfResults.temperature);
  j += ",\"tmf_reads\":" + String((unsigned long)gTmfReadCount);
  j += ",\"tmf_errors\":" + String((unsigned long)gTmfReadErrors);
  j += ",\"tmf_results\":[";
  uint32_t tmfJsonCount = min((uint32_t)12, min((uint32_t)TMF882X_MAX_MEAS_RESULTS,
                                               gTmfResults.num_results));
  for (uint32_t i = 0; i < tmfJsonCount; ++i) {
    if (i) j += ",";
    const tmf882x_meas_result &r = gTmfResults.results[i];
    j += "{\"channel\":" + String((unsigned long)r.channel);
    j += ",\"sub_capture\":" + String((unsigned long)r.sub_capture);
    j += ",\"distance_mm\":" + String((unsigned long)r.distance_mm);
    j += ",\"confidence\":" + String((unsigned long)r.confidence) + "}";
  }
  j += "]";
#else
  j += ",\"sensor_triad_enabled\":false";
#endif
#if defined(NB_SOLENOID_D7)
  j += ",\"solenoid_enabled\":true";
  j += ",\"solenoid_pin\":" + String(NB_SOLENOID_PIN);
  j += ",\"solenoid_gate_on\":";
  j += gSolenoidGateOn ? "true" : "false";
  j += ",\"solenoid_strikes\":" + String((unsigned long)gSolenoidStrikes);
  j += ",\"solenoid_blocked\":" + String((unsigned long)gSolenoidBlocked);
  j += ",\"solenoid_failsafes\":" + String((unsigned long)gSolenoidFailsafes);
  j += ",\"solenoid_last_ms\":" + String(gSolenoidLastPulseMs);
  j += ",\"solenoid_button_pin\":" + String(NB_SOLENOID_BUTTON_PIN);
  j += ",\"solenoid_button_armed\":";
  j += gSolenoidButtonStableReleased ? "true" : "false";
  j += ",\"solenoid_button_pressed\":";
  j += digitalRead(NB_SOLENOID_BUTTON_PIN) == LOW ? "true" : "false";
  j += ",\"solenoid_rgb_button_present\":";
  j += gSolenoidRgbButtonPresent ? "true" : "false";
  j += ",\"solenoid_rgb_button_addr\":" + String(gSolenoidRgbButtonAddr);
  j += ",\"solenoid_rgb_button_pressed\":";
  j += gSolenoidRgbButtonStablePressed ? "true" : "false";
  j += ",\"solenoid_rgb_button_presses\":" +
       String((unsigned long)gSolenoidRgbButtonPresses);
  j += ",\"solenoid_rgb_button_errors\":" +
       String((unsigned long)gSolenoidRgbButtonErrors);
  j += ",\"solenoid_rgb_button_probe_attempts\":" +
       String(gSolenoidRgbButtonProbeAttempts);
  j += ",\"solenoid_rgb_button_ack_mask\":" +
       String(gSolenoidRgbButtonAckMask);
  j += ",\"solenoid_rgb_button_pid_addr\":" +
       String(gSolenoidRgbButtonPidAddr);
  j += ",\"solenoid_rgb_button_pid\":" +
       String(gSolenoidRgbButtonPid);
  j += ",\"solenoid_nav_present\":";
  j += gSolenoidNavPresent ? "true" : "false";
  j += ",\"solenoid_nav_addr\":" + String(gSolenoidNavAddr);
  j += ",\"solenoid_nav_down_pressed\":";
  j += gSolenoidNavStableReleased ? "false" : "true";
  j += ",\"solenoid_nav_presses\":" + String((unsigned long)gSolenoidNavPresses);
  j += ",\"solenoid_nav_errors\":" + String((unsigned long)gSolenoidNavErrors);
  j += ",\"solenoid_nav_probe_attempts\":" + String(gSolenoidNavProbeAttempts);
  j += ",\"solenoid_nav_ack_mask\":" + String(gSolenoidNavAckMask);
  j += ",\"solenoid_nav_input\":" + String(gSolenoidNavLastInput);
  j += ",\"solenoid_nav_config\":" + String(gSolenoidNavLastConfig);
  j += ",\"solenoid_nav_polarity\":" + String(gSolenoidNavLastPolarity);
#else
  j += ",\"solenoid_enabled\":false";
#endif
#if NB_MAGIC_WAND
  MagicWandMode::appendTelemetry(j);
#else
  j += ",\"magic_wand\":false";
#endif
  j += "}";
  return j;
}

// ---- OTA web routes (ADR-0010 standard WiFi OTA) ---------------------------
bool otaRoutesConfigured = false;
void configureOtaRoutes() {
  if (otaRoutesConfigured) return;
  server.on("/", HTTP_GET, []() { server.send(200, "text/plain", "net-bench " NET_BENCH_VERSION "\n"); });
  server.on("/telemetry", HTTP_GET, []() { server.send(200, "application/json", telemetryJson()); });
  server.on("/resume", HTTP_GET, []() { server.send(200, "text/plain", "resuming\n"); gResumePending = true; });
  capbankWaveConfigureRoutes();
  server.on(
      "/update", HTTP_POST,
      []() {
        esp_task_wdt_reset();
        bool ok = !Update.hasError();
        server.send(ok ? 200 : 500, "text/plain", ok ? "Update complete. Rebooting.\n" : "Update failed.\n");
        delay(500);
        if (ok) ESP.restart();
      },
      []() {
        esp_task_wdt_reset();
        HTTPUpload &up = server.upload();
        if (up.status == UPLOAD_FILE_START) {
          solenoidStop("OTA");
          if (!Update.begin(UPDATE_SIZE_UNKNOWN)) Update.printError(Serial);
        } else if (up.status == UPLOAD_FILE_WRITE) {
          if (Update.write(up.buf, up.currentSize) != up.currentSize) Update.printError(Serial);
        } else if (up.status == UPLOAD_FILE_END) {
          if (Update.end(true)) Serial.printf("OTA done: %u bytes\n", up.totalSize);
          else Update.printError(Serial);
        }
      });
  otaRoutesConfigured = true;
}

bool startWifiOta() {
#if defined(NB_MAINT_AP)
  esp_task_wdt_reset();
  WiFi.mode(WIFI_AP);
  WiFi.setSleep(false);
  String ssid = String(NB_MAINT_AP_PREFIX) + "-" + shortId;
  bool ok = WiFi.softAP(ssid.c_str(), NB_MAINT_AP_PASS, NB_CHANNEL);
  esp_task_wdt_reset();
  if (!ok) {
    Serial.println("maintenance AP start failed");
    return false;
  }
  configureOtaRoutes();
  server.begin();
  otaActive = true;
  otaMode = "ap";
  Serial.print("maintenance AP '"); Serial.print(ssid);
  Serial.print("' pass='" NB_MAINT_AP_PASS "' ip="); Serial.print(WiFi.softAPIP());
  Serial.printf(" ch=%d\n", NB_CHANNEL);
  return true;
#else
#if RES_HAS_WIFI_SECRETS
  WiFi.mode(WIFI_STA);
#if NB_WIFI_LOWPOWER
  WiFi.setSleep(true);
  WiFi.setTxPower(WIFI_POWER_8_5dBm);
#else
  WiFi.setSleep(false);
#endif
  WiFi.begin(RES_WIFI_SSID, RES_WIFI_PASSWORD);
  uint32_t t0 = millis();
  while (WiFi.status() != WL_CONNECTED && millis() - t0 < 20000) {
    esp_task_wdt_reset();
    delay(250);
    Serial.print(".");
  }
  Serial.println();
  if (WiFi.status() != WL_CONNECTED) { Serial.println("WiFi join failed"); return false; }
  configureOtaRoutes();
  server.begin();
  otaActive = true;
  otaMode = "wifi";
  Serial.print("maintenance WiFi up, ip="); Serial.print(WiFi.localIP());
  Serial.printf(" ch=%d\n", WiFi.channel());
  return true;
#else
  Serial.println("no wifi_secrets.h -> cannot OTA");
  return false;
#endif
#endif
}

void stopOtaAndWifi() {
  if (otaActive) server.stop();
  WiFi.softAPdisconnect(true);
  WiFi.disconnect(true);
  WiFi.mode(WIFI_OFF);
  otaActive = false;
  otaMode = "off";
}

void capbankWaveTick() {
#if defined(NB_CAPBANK_WAVEFORM)
  if (gCapWaveState != CAPW_ARMED ||
      (int32_t)(millis() - gCapWaveArmAtMs) < 0) return;
  // The arming HTTP response has already left. Tear down every WiFi path before
  // sampling, capture into RAM, then rejoin and expose the completed CSV.
  stopOtaAndWifi();
  delay(30);
  capbankWaveCapture(gCapWavePulseMs);
  maintEnteredMs = millis();
  if (!startWifiOta()) {
    gCapWaveError += gCapWaveError.length() ? "; WiFi rejoin failed" : "WiFi rejoin failed";
    if (gCapWaveState != CAPW_READY) gCapWaveState = CAPW_ERROR;
    Serial.println("waveform retained in RAM; retrying shared WiFi in 2 s");
    delay(2000);
    startWifiOta();
  }
#endif
}

// ---- watchdog (net-new: closes the field-reliability TODO) -----------------
void setupWatchdog() {
  esp_task_wdt_config_t cfg = {};
  cfg.timeout_ms = (uint32_t)NB_WDT_S * 1000;
  cfg.idle_core_mask = 0;
  cfg.trigger_panic = true;
  esp_err_t e = esp_task_wdt_init(&cfg);
  if (e == ESP_ERR_INVALID_STATE) esp_task_wdt_reconfigure(&cfg); // core already inited it
  esp_task_wdt_add(NULL); // subscribe the loop task
  Serial.printf("watchdog: %ds, panic+reset on hang\n", NB_WDT_S);
}

// ---- per-source table ------------------------------------------------------
NbPeerStat *findPeer(const uint8_t id[3], bool create) {
  for (int i = 0; i < NB_MAX_TRACKED; i++)
    if (peers[i].used && memcmp(peers[i].id, id, 3) == 0) return &peers[i];
  if (!create) return nullptr;
  for (int i = 0; i < NB_MAX_TRACKED; i++)
    if (!peers[i].used) {
      memset(&peers[i], 0, sizeof(NbPeerStat));
      peers[i].used = true;
      memcpy(peers[i].id, id, 3);
      return &peers[i];
    }
  return nullptr;
}

void accountSeq(NbPeerStat *p, uint32_t seq) {
  if (p->recv == 0) { p->last_seq = seq; p->recv = 1; return; }
  if (seq > p->last_seq) {
    p->gaps += (seq - p->last_seq - 1);
    p->recv += 1;
    p->last_seq = seq;
  } else {
    // out-of-order or sender reboot (seq reset): treat as fresh start
    if (seq < p->last_seq && p->last_seq - seq > 100) { p->last_seq = seq; p->recv = 1; p->gaps = 0; }
    else p->recv += 1;
  }
}

// ---- ESP-NOW callbacks -----------------------------------------------------
void onEspNowRecv(const esp_now_recv_info_t *info, const uint8_t *data, int len) {
  if (len < (int)sizeof(NbHeader) || len > (int)sizeof(RxItem::data)) return;
  RxItem it;
  memcpy(it.mac, info->src_addr, 6);
  it.rssi = info->rx_ctrl ? info->rx_ctrl->rssi : 0;
  it.len = (uint8_t)len;
  memcpy(it.data, data, len);
  BaseType_t hpw = pdFALSE;
  xQueueSendFromISR(rxQueue, &it, &hpw); // recv cb is WiFi-task ctx; ISR-safe send is fine
}

void onEspNowSend(const esp_now_send_info_t *info, esp_now_send_status_t status) {
  if (status == ESP_NOW_SEND_SUCCESS) sendOk++; else sendFail++;
}

bool espNowInit() {
  esp_wifi_set_channel(NB_CHANNEL, WIFI_SECOND_CHAN_NONE);
  if (esp_now_init() != ESP_OK) { Serial.println("esp_now_init FAILED"); return false; }
  esp_now_register_recv_cb(onEspNowRecv);
  esp_now_register_send_cb(onEspNowSend);
  esp_now_peer_info_t peer = {};
  memcpy(peer.peer_addr, BCAST, 6);
  peer.channel = NB_CHANNEL;
  peer.ifidx = WIFI_IF_STA;
  peer.encrypt = false; // UNENCRYPTED broadcast = the 100-node-scalable pattern
  esp_now_add_peer(&peer);
  Serial.printf("esp-now up, ch=%d, broadcast peer registered\n", NB_CHANNEL);
  return true;
}
void espNowDeinit() {
  esp_now_unregister_recv_cb();
  esp_now_deinit();
}

// fill a header for an outgoing packet
void fillHeader(NbHeader *h, uint8_t type) {
  h->ver = NB_PROTO_VER;
  h->type = type;
  memcpy(h->src_id, myId, 3);
  h->seq = txSeq++;
  h->uptime_ms = millis();
}
void sendShowFrame() {
  NbShowFrame f;
  fillHeader(&f.h, NB_SHOWFRAME);
  f.phase = (uint16_t)((millis() / 50) & 0xFFFF);
  f.hue = (uint8_t)(f.phase & 0xFF);
  f.flags = 0;
  esp_now_send(BCAST, (uint8_t *)&f, sizeof(f));
}
void sendHeartbeat(uint8_t caState) {
  static uint32_t hbSeq = 0;
  NbHeartbeat hb;
  fillHeader(&hb.h, NB_HEARTBEAT);
  // Heartbeats carry their OWN contiguous seq: the master derives uplink PDR from
  // it, and the shared txSeq is also consumed by scan-AP sends -- without this, a
  // scan batch's N packets would read as N phantom heartbeat gaps. (Suppressed
  // heartbeats during a scan simply don't advance hbSeq, so they aren't gaps.)
  hb.h.seq = hbSeq++;
  hb.batt_mv = (int16_t)(cbV * 1000.0f);
  hb.batt_ma = (int16_t)cbMa;
  hb.soc_pct = (cbSoc < 0) ? 255 : (uint8_t)cbSoc;
  hb.reset_reason = (uint8_t)esp_reset_reason();
  hb.ca_state = caState;
  hb.mode = (uint8_t)gMode;
  uint32_t tot = masterRx + masterGaps;
  hb.dl_pdr_x1000 = tot ? (uint16_t)((uint64_t)masterRx * 1000 / tot) : 0;
  hb.dl_rssi = masterRssi;
  hb.supply_mv = (int16_t)(csV * 1000.0f);
  hb.supply_ma = (int16_t)csMa;
  hb.supply_good = csGood ? 1 : 0;
  hb.lux_x10 = gEnvTsl ? gEnvLuxX10 : 0xFFFFFFFF;
  hb.light_ch0 = gEnvCh0;
  hb.light_ch1 = gEnvCh1;
  hb.ptemp_cx10 = gEnvPtempX10;
  hb.prh_pct = gEnvRh;
  hb.btemp_cx10 = gEnvBtempX10;
  hb.ina_pv_mv = gInaPvMv;
  hb.ina_pa_ma = gInaPaMa;
  hb.ina_bv_mv = gInaBvMv;
  hb.ina_ba_ma = gInaBaMa;
  hb.cfg_cap_mah = gBatteryCapacityMah;
  hb.cfg_charge_ma = gChargeMa;
  hb.drawdown_mah_x10 = (uint16_t)min(65535UL, (unsigned long)(gDrawdownMah * 10.0f + 0.5f));
  hb.drawdown_budget_mah = gDrawdownBudgetMah;
  hb.drawdown_active = gDrawdownActive ? 1 : 0;
  memset(hb.fw_rev, 0, sizeof(hb.fw_rev));
  strncpy(hb.fw_rev, NET_BENCH_VERSION, sizeof(hb.fw_rev) - 1);
  hb.maint_status = gMaintStatus;
  hb.field_phase = rtcFieldPhase;
  hb.field_reason = rtcFieldReason;
  hb.field_cycle = rtcFieldCycle;
  hb.field_elapsed_s = (uint16_t)min(65535UL, rtcFieldPhaseElapsedS);
  hb.field_charge_mah = (uint16_t)min(65535UL, rtcFieldChargeMas / 3600UL);
  hb.field_discharge_mah = (uint16_t)min(65535UL, rtcFieldDischargeMas / 3600UL);
  hb.field_min_mv = rtcFieldMinMv;
  hb.field_max_mv = rtcFieldMaxMv;
  hb.bq_vindpm_mv = gBqVindpmMv;
  hb.bq_ichg_ma = gBqIchgMa;
  hb.bq_vreg_mv = gBqVregMv;
  hb.bq_reg16 = gBqReg16;
  hb.bq_reg18 = gBqReg18;
  hb.bq_stat0 = gBqStat0;
  hb.bq_stat1 = gBqStat1;
  hb.bq_fault0 = gBqFault0;
  hb.bq_flag0 = gBqFlag0;
  hb.bq_flag1 = gBqFlag1;
  hb.bq_fault_flag0 = gBqFaultFlag0;
  hb.bq_part = gBqPart;
  hb.field_charge_wh_x10 = (uint16_t)min(65535UL, rtcFieldChargeMws / 360000UL);
  hb.field_discharge_wh_x10 = (uint16_t)min(65535UL, rtcFieldDischargeMws / 360000UL);
  hb.field_peak_panel_w_x100 = rtcFieldPeakPanelWx100;
  hb.field_peak_charge_w_x100 = rtcFieldPeakChargeWx100;
  hb.field_peak_draw_w_x100 = rtcFieldPeakDrawWx100;
  hb.field_low_s = (uint8_t)min(255UL, (unsigned long)rtcFieldLowS);
  hb.field_charge_min = (uint8_t)min(255UL, (unsigned long)((rtcFieldChargeS + 30) / 60));
  hb.field_wait_min = (uint8_t)min(255UL, (unsigned long)((rtcFieldWaitS + 30) / 60));
  hb.field_draw_min = (uint8_t)min(255UL, (unsigned long)((rtcFieldDrawS + 30) / 60));
  hb.field_protect_min = (uint8_t)min(255UL, (unsigned long)((rtcFieldProtectS + 30) / 60));
  hb.mppt_status = rtcFieldMpptStatus;
  hb.mppt_reason = rtcFieldMpptReason;
  hb.mppt_runs = rtcFieldMpptRuns;
  hb.mppt_active_v10 = rtcFieldMpptActiveV10;
  hb.mppt_best_v10 = rtcFieldMpptBestV10;
  hb.mppt_last_v10 = rtcFieldMpptLastV10;
  hb.mppt_p46_w_x100 = rtcFieldMpptP46Wx100;
  hb.mppt_p48_w_x100 = rtcFieldMpptP48Wx100;
  hb.mppt_p50_w_x100 = rtcFieldMpptP50Wx100;
  hb.field_load_dimmed = rtcFieldLoadDimmed;
  hb.field_protect_latched = rtcFieldProtectLatched;
  esp_now_send(BCAST, (uint8_t *)&hb, sizeof(hb));
}
void sendCmd(uint8_t type, uint8_t arg) {
  NbCmd c;
  fillHeader(&c.h, type);
  c.arg = arg;
  for (int i = 0; i < 4; i++) { esp_now_send(BCAST, (uint8_t *)&c, sizeof(c)); delay(5); } // repeat (unacked)
}
void sendSetU16(uint8_t type, uint16_t value) {
  NbSetU16 c;
  fillHeader(&c.h, type);
  c.value = value;
  for (int i = 0; i < 4; i++) { esp_now_send(BCAST, (uint8_t *)&c, sizeof(c)); delay(5); }
}
void sendTargetU16(uint8_t type, const uint8_t target[3], uint16_t value) {
  NbTargetU16 c;
  fillHeader(&c.h, type);
  memcpy(c.target_id, target, 3);
  c.value = value;
  for (int i = 0; i < 6; i++) { esp_now_send(BCAST, (uint8_t *)&c, sizeof(c)); delay(8); }
}
void sendTargetCmd(uint8_t type, const uint8_t target[3], uint8_t arg) {
  NbTargetCmd c;
  fillHeader(&c.h, type);
  memcpy(c.target_id, target, 3);
  c.arg = arg;
  for (int i = 0; i < 6; i++) { esp_now_send(BCAST, (uint8_t *)&c, sizeof(c)); delay(8); }
}
bool targetMatchesMe(const uint8_t target[3]) {
  bool all = (target[0] == 0 && target[1] == 0 && target[2] == 0);
  return all || memcmp(target, myId, 3) == 0;
}
uint16_t maintenanceBatteryFloorMv() {
  return (RES_PF_BATTERY_TYPE == Mainboard::BatteryType::Generic_LFP)
             ? NB_MAINT_MIN_LFP_MV
             : NB_MAINT_MIN_3V7_MV;
}
bool maintenancePowerOk() {
  if (IS_MASTER || !pfReady) return true;

  readBattery();
  esp_task_wdt_reset();
  int battMv = (int)(cbV * 1000.0f + 0.5f);
  uint16_t floorMv = maintenanceBatteryFloorMv();
  bool batteryKnown = battMv > 500;
  bool batteryOk = !batteryKnown || battMv >= (int)floorMv;
  bool supplyOk = csGood && csMa >= (float)NB_MAINT_SUPPLY_OVERRIDE_MA;
  if (batteryOk || supplyOk) return true;

  gMaintStatus = MAINT_STATUS_POWER_WARN;
  uint32_t now = millis();
  if (!gLastMaintRefuseMs || now - gLastMaintRefuseMs >= NB_MAINT_REFUSE_REPORT_MS) {
    gLastMaintRefuseMs = now;
    Serial.printf("maintenance power warning: bv=%dmV floor=%umV sv=%.3fV sma=%.0fmA sgood=%d enforce=%d\n",
                  battMv, (unsigned)floorMv, csV, csMa, csGood ? 1 : 0,
                  NB_MAINT_POWER_ENFORCE);
    sendHeartbeat(0);
  }
#if NB_MAINT_POWER_ENFORCE
  return false;
#else
  return true;
#endif
}
void enterTimedDeepSleep(uint16_t seconds, const char *why) {
  if (seconds == 0) seconds = 1;
  solenoidStop("deep sleep");
#if NB_MAGIC_WAND
  // The external Pololu is not on either PowerFeather switchable rail.
  MagicWandMode::pauseForMaintenance();
#endif
  digitalWrite(NB_LED_PIN, LOW);
  if (pfReady) {
    Board.enable3V3(false);
    Board.enableVSQT(false);
  }
  Serial.printf("deep sleep (%s), timer wake %us\n", why, (unsigned)seconds);
  solenoidButtonPrepareSleep();
  Serial.flush();
  esp_sleep_enable_timer_wakeup((uint64_t)seconds * 1000000ULL);
  esp_deep_sleep_start();
}
void drawdownPixelsBegin() {
  if (gDrawdownPixelsBegun) return;
  drawdownPixels.begin();
  drawdownPixels.setBrightness(255);
  drawdownPixels.clear();
  drawdownPixels.show();
  gDrawdownPixelsBegun = true;
}
void drawdownPixelsOff() {
  drawdownPixelsBegin();
  drawdownPixels.setBrightness(255);
  drawdownPixels.clear();
  drawdownPixels.show();
  pinMode(NB_DRAWDOWN_PIXEL_PIN, OUTPUT);
  digitalWrite(NB_DRAWDOWN_PIXEL_PIN, LOW);
}
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
